myriadrf/LimeRFE/docs/reference/v1.31/gpios.rst

GPIOs
#####

10-pin GPIO interface between SDR and LimeRFE pinouti s given in table 6.

.. list-table:: Table 6. GPIO and I2C connector (J12)
   :header-rows: 1
   :stub-columns: 1

   * - Pin Numbers
     - Designation on Schematic
     - Comments
   * - 1
     - GPIO0
     - Connected to PIN 32 of MCU (INT0 pin)

       Can directly control digital TDD signal (PA/LNA – on/off)
   * - 2
     - GPIO1
     - Via J22 drives RELAY_3

       Connected to PIN 1 of MCU (INT1 pin)
   * - 3
     - GPIO2
     - Drives RELAY_0
   * - 4
     - GPIO3
     - Drives RELAY_1
   * - 5
     - GPIO4
     - Drives RELAY_2
   * - 6
     - GPIO5_CONN
     - Via J22 drives RELAY_3
   * - 7
     - SCL
     - I2C bus
   * - 8
     - SDA
     - I2C bus
   * - 9
     - GND
     - Ground
   * - 10
     - VDD_CON
     - Referent voltage for GPIOx and I2C signals

Level shifted (VDDA) GPIOs and ADC header pinout is given in table 7.

.. list-table:: Table 7. GPIO_LS and ADC connector (J13)
   :header-rows: 1
   :stub-columns: 1

   * - Pin Numbers
     - Designation on Schematic
     - Comments
   * - 1
     - GPIO2_LS
     - Connected to GPI2, level shifted to VDDA
   * - 2
     - GPIO4_LS
     - Connected to GPI4, level shifted to VDDA
   * - 3
     - ADC1
     - Via J6 connected to internal MCU ADC
   * - 4
     - GND
     - Ground
   * - 5
     - VDDA
     - Referent voltage for GPIOx_LS signals
   * - 6
     - ADC2
     - Via J7 connected to internal MCU ADC
   * - 7
     - GPIO5_LS
     - Connected to GPI5, level shifted to VDDA
   * - 8
     - GPIO3_LS
     - Connected to GPI3, level shifted to VDDA

External relays connector (J16) pinout is given in table 8.

.. list-table:: Table 8. External relays connector (J16)
   :header-rows: 1
   :stub-columns: 1

   * - Pin Numbers
     - Designation on Schematic
     - Comments
   * - 1
     - RELAY_3
     - Drives relay 3
   * - 2
     - VCOM
     - Referent voltage, from connector J15
   * - 3
     - RELAY_2
     - Drives relay 2
   * - 4
     - VCOM
     - Referent voltage, from connector J15
   * - 5
     - RELAY_1
     - Drives relay 1
   * - 6
     - VCOM
     - Referent voltage, from connector J15
   * - 7
     - RELAY_0
     - Drives relay 0
   * - 8
     - VCOM
     - Referent voltage, from connector J15
