myriadrf/LimeRFE/docs/reference/v1.31/leds.rst

LEDs
####

The LimeRFE board includes ten indicator LEDs. Their positions on the board are shown in Figures 8 and 9.

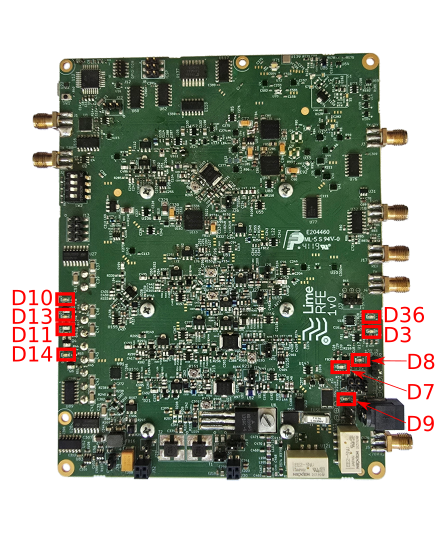
[picture p12: docs/images/LimeRFE_v1.0_components_LEDs_top.png]


  Figure 8. LimeRFE v1.0 indication top LEDs 

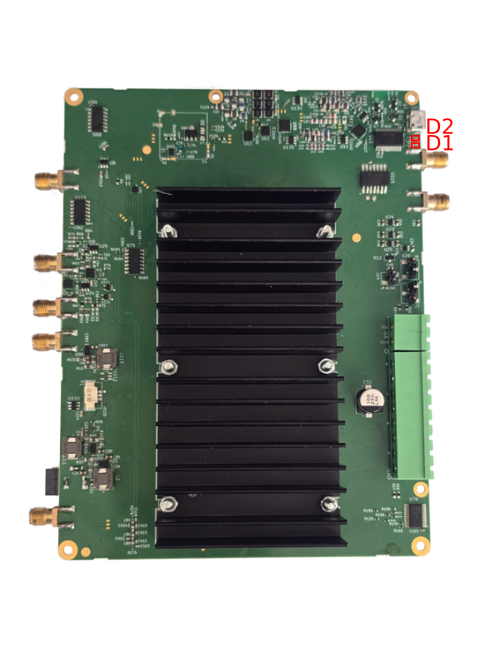
[picture p13: docs/images/LimeRFE_v1.0_components_LEDs_bot.png]


  Figure 9. LimeRFE v1.0 indication bottom LEDs 

LEDs funcions are described in table 5.

.. list-table:: Table 5. Default LEDs configuration
   :header-rows: 1
   :stub-columns: 1
   
   * - Board Reference
     - Description
   * - D1, D2
     - USB to serial communication indicator
   * - D3
     - +3V power indicator
   * - D7
     - +5V_MCU power indicator
   * - D9
     - +7.5V power indicator
   * - D10
     - GPIO2 indicator
   * - D11
     - GPIO4 indicator
   * - D13
     - GPIO3 indicator
   * - D14
     - GPIO5 indicator
   * - D36
     - +2.5V power indicator
