myriadrf/LimeRFE/docs/reference/v1.31/peripheralinterfaces.rst

ICSP Connector
##############

MCU SPI bus connectors pinout is given in table 9.

.. list-table:: Table 9. ICSP connector pinout (J8)
   :stub-columns: 1

   * - Pin Numbers
     - Designation on Schematic
     - Comments
   * - 1
     - MISO
     - ICSP bus
   * - 2
     - +5V_ICSP
     - Referent voltage for ICSP bus
   * - 3
     - SCK
     - ICSP bus
   * - 4
     - MOSI
     - ICSP bus
   * - 5
     - RESET
     - MCU reset
   * - 6
     - GND
     - Ground
