myriadrf/LimeRFE/docs/reference/v1.31/index.rst

v1.31
#####

.. toctree::
   :maxdepth: 3
   :hidden:
   
   overview
   cons
   rxblock
   txblock
   leds
   gpios
   peripheralinterfaces
   power

This is the Reference Manual for LimeRFE v1.31 hardware.



  Figure 1: LimeRFE v1.31 board top view

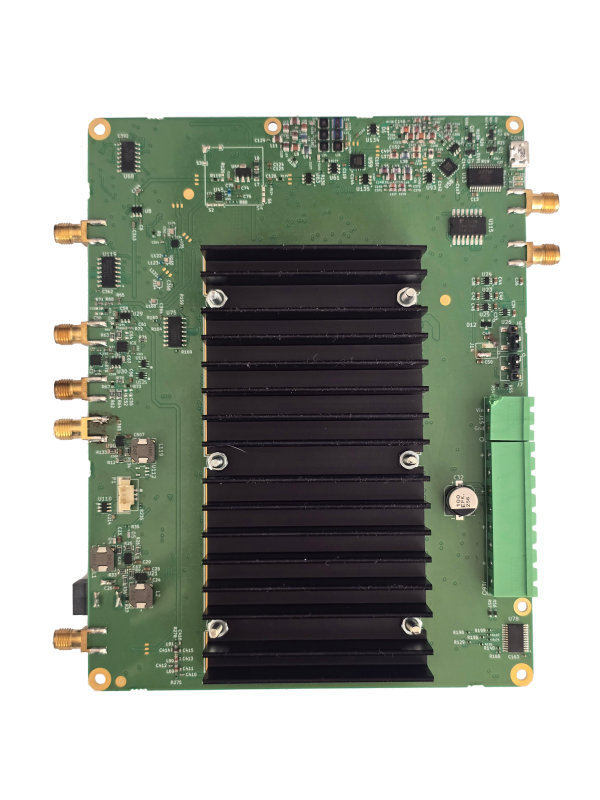
[picture p15: docs/images/LimeRFE_v1.31_3d_bot.png]


  Figure 2: LimeRFE v1.31 board bottom view
