myriadrf/LimeRFE/hardware/1v0/HeatSink_drawing/LimeRFE_1v0_HeatSink.pdf

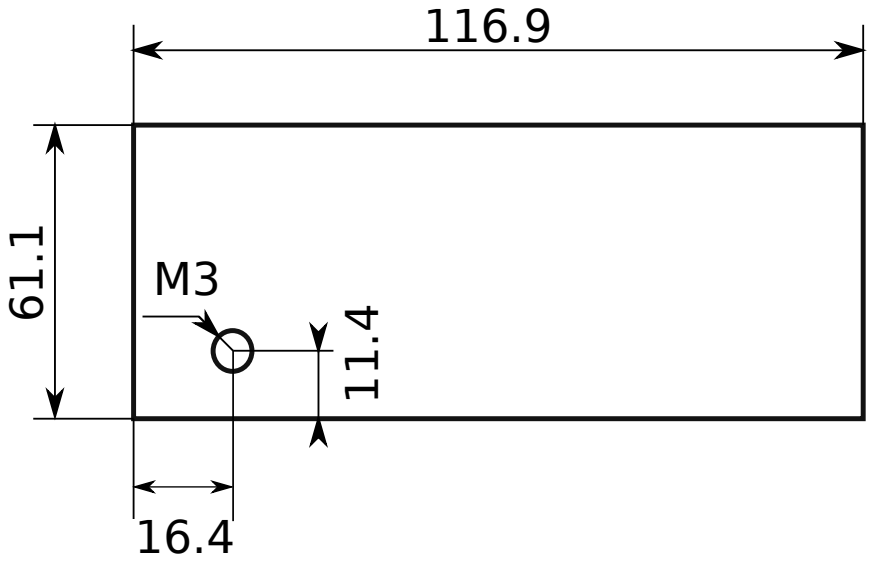
[picture p16: figure]

19.1

3.2

Heat sink
for LimeRFE 1v0
