myriadrf/LimeRFE/hardware/1v31/HeatSink_drawing/LimeRFE_1v31_HeatSink.pdf

19.1

3.2

Heat sink
for LimeRFE 1v31
