myriadrf/LimeRFE/docs/reference/v1.0/overview.rst

Overview
########

The scope of this chapter is in detailed explanation of the block diagram of the LimeRFE board. The above mentioned block diagram is shown in Figure 3. Please keep in mind that this block diagram depicts only RF part of the board. 

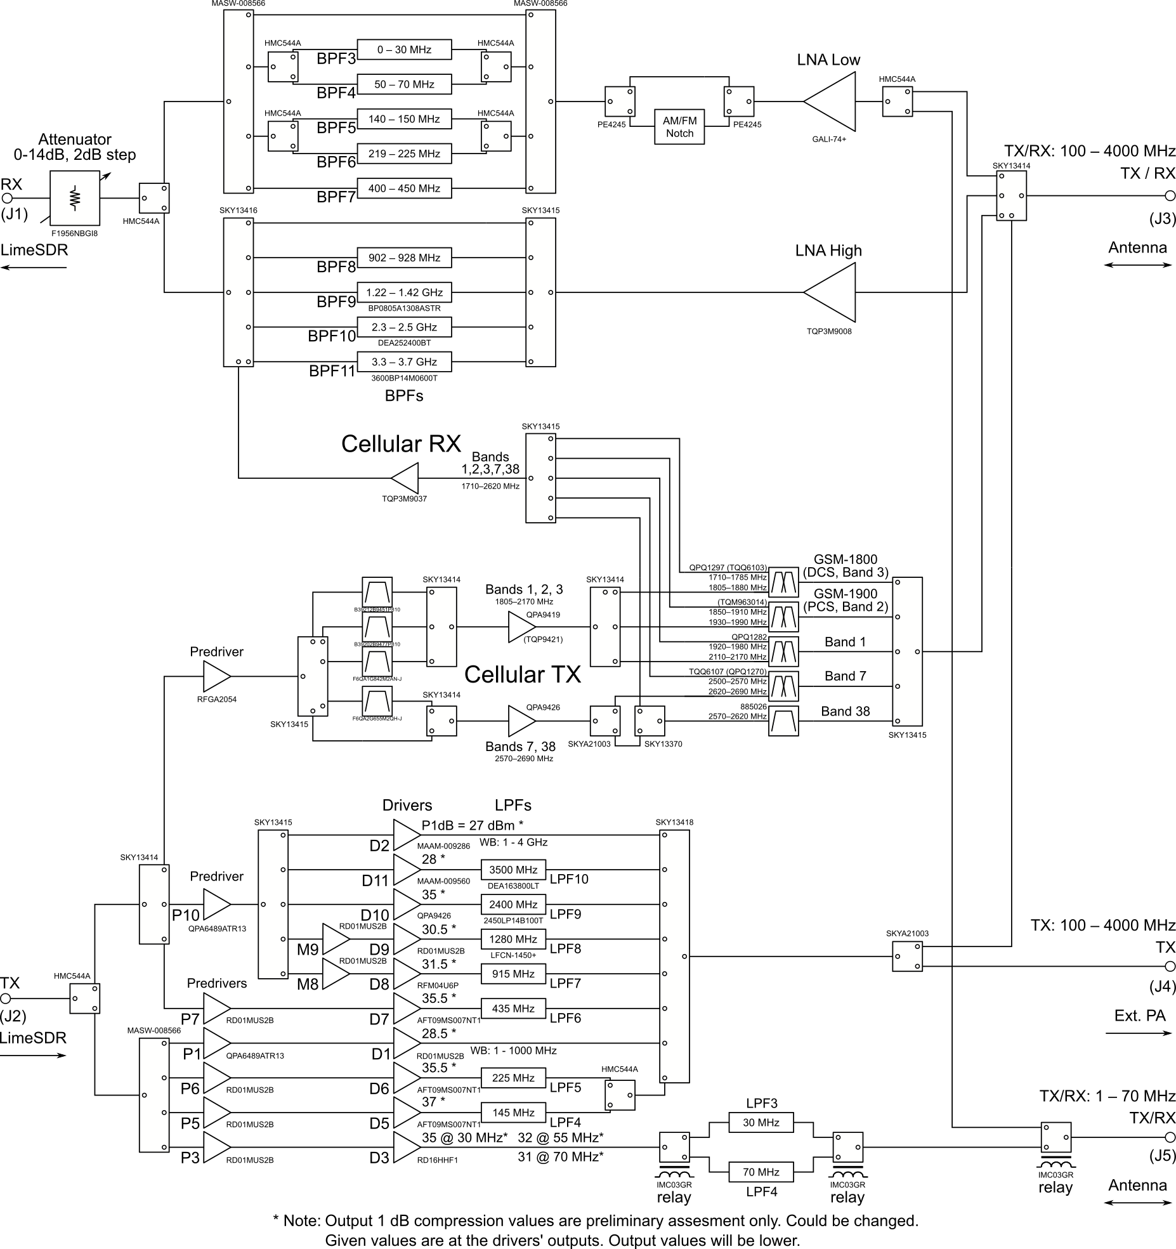
[picture p65: docs/images/LimeRFE_v1.0_diagrams_BD.png]


  Figure 3: LimeRFE v1.0 board block diagram

Basically, the board comprises receiver and transmitter blocks, where both of them have Wideband, HAM and Cellular sub-blocks. These sub-blocks are not strictly divided and separated, for example HAM and Wideband have been realised under the same hardware. Photo of the LimeRFE board, with marked most important RF blocks is shown in Figure 4 and in Figure 5. 

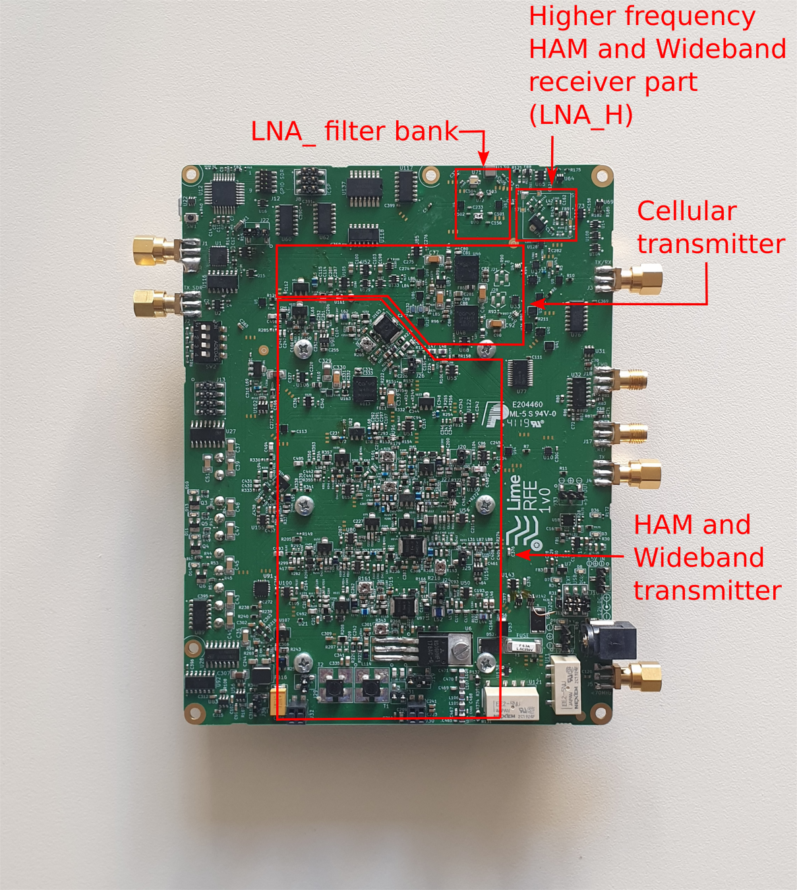
[picture p66: docs/images/LimeRFE_v1.0_Wideband_Cell_HAM_top.png]


  Figure 4: Receiver and transmitter sub-blocks – Top view

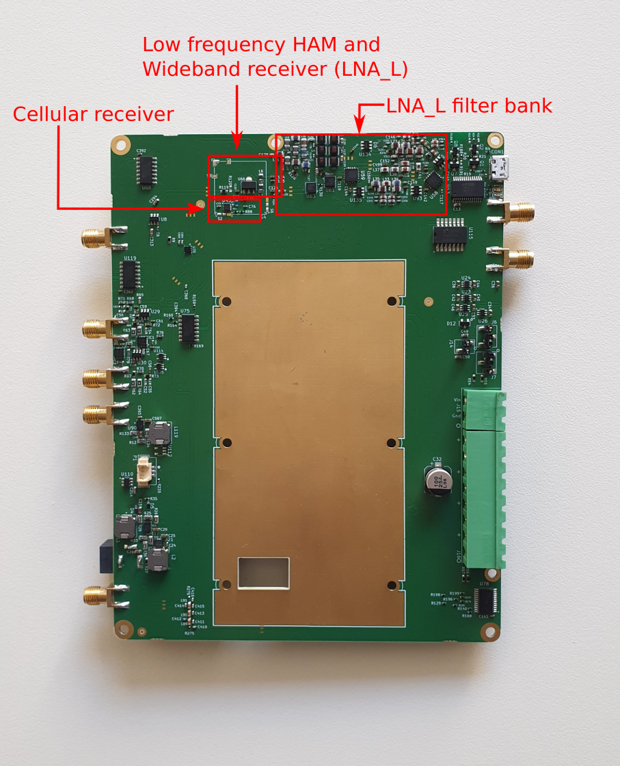
[picture p67: docs/images/LimeFRE_v1.0_Wideband_Cell_HAM_bot.png]


  Figure 5: Receiver and transmitter sub-blocks – Bottom view 
  (without Heat sink and RD16HHF1 transistor)

.. table:: Table 1. Board components

  +-----------------------+-------------------------+-------------------------------------------------------------------------------------------------------------+
  | **Board Reference**   | **Type**                | **Description**                                                                                             |
  +=======================+=========================+=============================================================================================================+
  | **DC Supply Block**                                                                                                                                           |
  +-----------------------+-------------------------+-------------------------------------------------------------------------------------------------------------+
  | J9                    | 3 pin header            | 12V DC input                                                                                                |
  +-----------------------+-------------------------+-------------------------------------------------------------------------------------------------------------+
  | J23                   | Power Barrel            | 12V DC input                                                                                                |
  |                       |                         |                                                                                                             |
  |                       | Connector Jack          |                                                                                                             |
  +-----------------------+-------------------------+-------------------------------------------------------------------------------------------------------------+
  | J10                   | 3 pin header            | 5V DC input                                                                                                 |
  +-----------------------+-------------------------+-------------------------------------------------------------------------------------------------------------+
  | J11                   | 3x2 pin header          | 5V input selector                                                                                           |
  +-----------------------+-------------------------+-------------------------------------------------------------------------------------------------------------+
  | J33                   | 3 pin header            | 5V DC output                                                                                                |
  +-----------------------+-------------------------+-------------------------------------------------------------------------------------------------------------+
  | U17                   | LDO 3V                  | Provides a stable 3V DC                                                                                     |
  +-----------------------+-------------------------+-------------------------------------------------------------------------------------------------------------+
  | U18                   | LDO 2.5V                | Provides a stable 2.5V DC                                                                                   |
  +-----------------------+-------------------------+-------------------------------------------------------------------------------------------------------------+
  | U19                   | DC-DC converter         | Converts 12V to internal 5V                                                                                 |
  +-----------------------+-------------------------+-------------------------------------------------------------------------------------------------------------+
  | U20                   | 5V input protection     | Monitors and protects 5V input                                                                              |
  +-----------------------+-------------------------+-------------------------------------------------------------------------------------------------------------+
  | U21                   | DC-DC converter         | Converts 12V to internal 7.5V                                                                               |
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
  +-----------------------+-------------------------+-------------------------------------------------------------------------------------------------------------+
  | U12                   | MCU                     | ATMEGA 328P microcontroller                                                                                 |
  +-----------------------+-------------------------+-------------------------------------------------------------------------------------------------------------+
  | U13                   | USB-to-serial chip      | Converts USB to MCU serial communication and vice versa                                                     |
  +-----------------------+-------------------------+-------------------------------------------------------------------------------------------------------------+
  | J8                    | ICSP connector          | SPI bus to MCU                                                                                              |
  +-----------------------+-------------------------+-------------------------------------------------------------------------------------------------------------+
  | D1, D2                | LED                     | USB to Serial communication indicator                                                                       |
  +-----------------------+-------------------------+-------------------------------------------------------------------------------------------------------------+
  | CON1                  | USB mini-B connector    | USB connector for the LimeRFE board                                                                         |
  +-----------------------+-------------------------+-------------------------------------------------------------------------------------------------------------+
  | U22                   | USB protection          | Protects USB lines from over-voltages                                                                       |
  +-----------------------+-------------------------+-------------------------------------------------------------------------------------------------------------+
  | U60, U62, U68, U75,   | Shift registers         | Saves the current state of the LimeRFE                                                                      |
  |                       |                         |                                                                                                             |
  | U76, U89, U92, U116,  |                         |                                                                                                             |
  |                       |                         |                                                                                                             |
  | U117, U118, U119      |                         |                                                                                                             |
  +-----------------------+-------------------------+-------------------------------------------------------------------------------------------------------------+
  | J12                   | GPIO and I2C connector  | PINS:                                                                                                       |
  |                       |                         |                                                                                                             |
  |                       |                         | GPIO0, GPIO1, GPIO2, GPIO3_CONN, GPIO4,                                                                     |
  |                       |                         |                                                                                                             |
  |                       |                         | GPIO5, SCL, SDA, GND, VDD_CON                                                                               |
  +-----------------------+-------------------------+-------------------------------------------------------------------------------------------------------------+
  | D12                   | TVS diode               | Protects the board from the DC voltage connected to J12                                                     |
  +-----------------------+-------------------------+-------------------------------------------------------------------------------------------------------------+
  | J13                   | Level Shifted GPIO      | PINS:                                                                                                       |
  |                       |                         |                                                                                                             |
  |                       | and ADC connector       | GPIO0_LS, GPIO2_LS, ADC1, GND,                                                                              |
  |                       |                         |                                                                                                             |
  |                       |                         | VDDA, ADC2, GPIO3_LS, GPIO1_LS                                                                              |
  +-----------------------+-------------------------+-------------------------------------------------------------------------------------------------------------+
  | U23, U24, U25, U26    | Level Shifters          | Converts voltage levels of GPIO signals;                                                                    |
  |                       |                         |                                                                                                             |
  |                       |                         | between VDD_CON (GPIO) and VDDA (GPIO_LS)                                                                   |
  +-----------------------+-------------------------+-------------------------------------------------------------------------------------------------------------+
  | SW2                   | Switch                  | Sets directions of U23-26, for GPIO signals (between GPIO and GPIO_LS)                                      |
  +-----------------------+-------------------------+-------------------------------------------------------------------------------------------------------------+
  | J14                   | 2 pin header            | In a case VDD_CON = VDDA connects these two voltages                                                        |
  +-----------------------+-------------------------+-------------------------------------------------------------------------------------------------------------+
  | J22                   | 3 pin header            | Selects GPIO3 source, either GPIO3_CONN or GPIO5                                                            |
  +-----------------------+-------------------------+-------------------------------------------------------------------------------------------------------------+
  | D10, D11, D13 D14     | LED                     | Indicators for GPIO0, GPIO2, GPIO1, GPIO3 respectively                                                      |
  +-----------------------+-------------------------+-------------------------------------------------------------------------------------------------------------+
  | Q3, Q4, Q5, Q6        | BJT NPN                 | Drivers for D10-13, for GPIO0, GPIO2, GPIO1, GPIO3 respectively                                             |
  +-----------------------+-------------------------+-------------------------------------------------------------------------------------------------------------+
  | U27, U28              | Relay drivers           | Drivers for RELAY_0, RELAY_1, RELAY_2, RELAY_3 signals                                                      |
  +-----------------------+-------------------------+-------------------------------------------------------------------------------------------------------------+
  | J16                   | 8 position header       | Connects LimeRFE to the external relays                                                                     |
  +-----------------------+-------------------------+-------------------------------------------------------------------------------------------------------------+
  | J15                   | 2 position header       | DC voltage for drivers for relays                                                                           |
  +-----------------------+-------------------------+-------------------------------------------------------------------------------------------------------------+
  | U115                  | Inverter                | It is used as 2.5V – 3.0V level shifter for digital signals obtained from U116 and U117,                    |
  |                       |                         |                                                                                                             |
  |                       |                         | from the LimeRFE shift register                                                                             |
  +-----------------------+-------------------------+-------------------------------------------------------------------------------------------------------------+
  | U77, U78              | Level shifter           | Level shifter for digital signals which control TX HAM and WB sub-blocks                                    |
  +-----------------------+-------------------------+-------------------------------------------------------------------------------------------------------------+
  | U127, U129            | Inverter                | Controls digital signals for TDD TX/RX RF switch (U128 )                                                    |
  +-----------------------+-------------------------+-------------------------------------------------------------------------------------------------------------+
  | U141, U142            | Inverter                | Controls digital signals for RF switch for TX HAM145 and HAM220 (U143)                                      |
  +-----------------------+-------------------------+-------------------------------------------------------------------------------------------------------------+
  | U69                   | Logical AND             | Generates control signals for LNA_EN for LNA in higher frequency bands                                      |
  |                       |                         |                                                                                                             |
  |                       |                         | (HAM1280, HAM3500, HAM2400, HAM920 and WB4000)                                                              |
  +-----------------------+-------------------------+-------------------------------------------------------------------------------------------------------------+
  | U137                  | Inverter                | Generates control signals for RF switches in RX lower frequency section. (U38, U134, U93 and U135)          |
  +-----------------------+-------------------------+-------------------------------------------------------------------------------------------------------------+
  | U64                   | Logical AND             | Generates control signals for LNA_EN for LNA for lower frequency bands                                      |
  |                       |                         |                                                                                                             |
  |                       |                         | (HAM30, HAM70, HAM435, HAM220, HAM145, WB1000)                                                              |
  +-----------------------+-------------------------+-------------------------------------------------------------------------------------------------------------+
  | U7                    | Relay driver            | Generates control signal for RF switch U11                                                                  |
  +-----------------------+-------------------------+-------------------------------------------------------------------------------------------------------------+
  | U114, U125            | Inverter                | Generates control signal for RF switches U29 and U30 in SWR section.                                        |
  +-----------------------+-------------------------+-------------------------------------------------------------------------------------------------------------+
  | U32                   | OP amp                  | Operational amplifier in SWR section                                                                        |
  +-----------------------+-------------------------+-------------------------------------------------------------------------------------------------------------+
  | **RF Block**                                                                                                                                                  |
  +-----------------------+-------------------------+-------------------------------------------------------------------------------------------------------------+
  | J1                    | SMA                     | RX connector                                                                                                |
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
  +-----------------------+-------------------------+-------------------------------------------------------------------------------------------------------------+
  | H1                    | Heat sink               | Aluminum black anodized heat sink                                                                           |
  +-----------------------+-------------------------+-------------------------------------------------------------------------------------------------------------+
  | P1                    | 3 pin FAN connector     | Connects an external fan                                                                                    |
  +-----------------------+-------------------------+-------------------------------------------------------------------------------------------------------------+

A more detailed description is provided in the following sections.
