myriadrf/LimeRFE/docs/reference/v1.0/index.rst

v1.0
####

.. toctree::
   :maxdepth: 3
   :hidden:
   
   overview
   cons
   rxblock
   txblock
   leds
   gpios
   peripheralinterfaces
   power

This is the Reference Manual for LimeRFE v1.0 hardware.



  Figure 1: LimeRFE v1.0 board top view

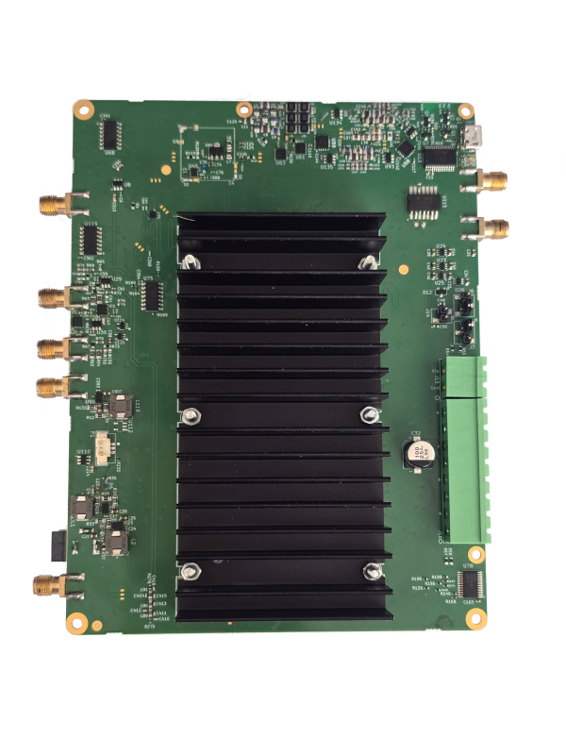
[picture p71: docs/images/LimeRFE_v1.0_3d_bot.png]


  Figure 2: LimeRFE v1.0 board bottom view
