myriadrf/LimeRFE/archived/0v3/hardware/PDF/LimeRFE_v03_Block_Diagram.pdf

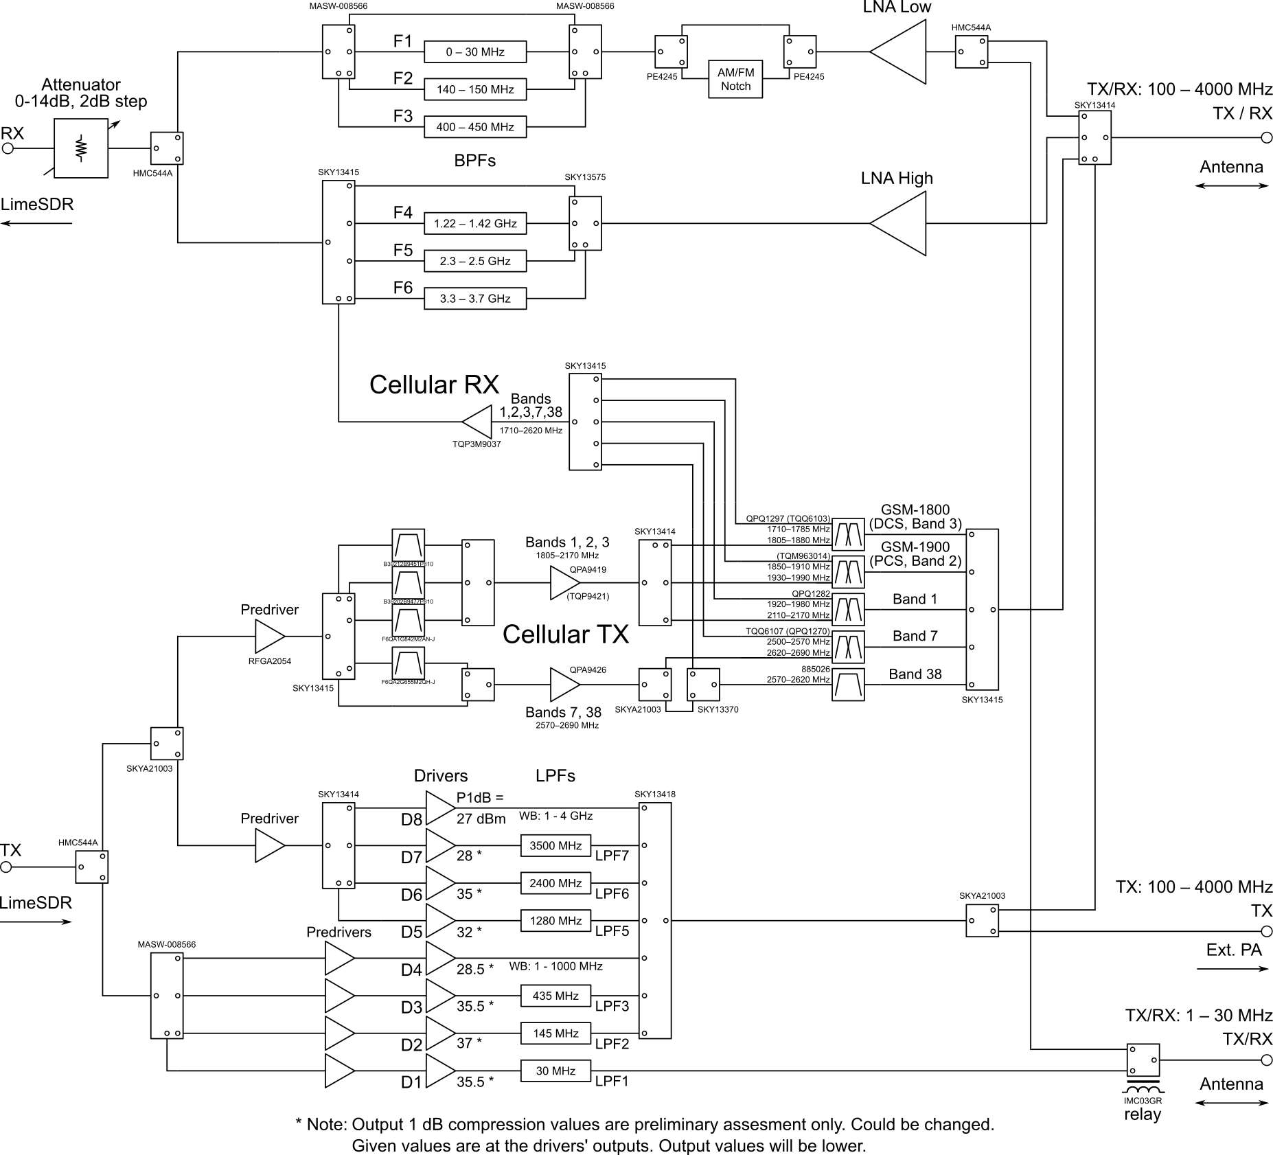
[picture p72: page 1]
