myriadrf/LimeRFE/archived/1v0/hardware/PDF/LimeRFE_1v0_Block_Diagram.pdf

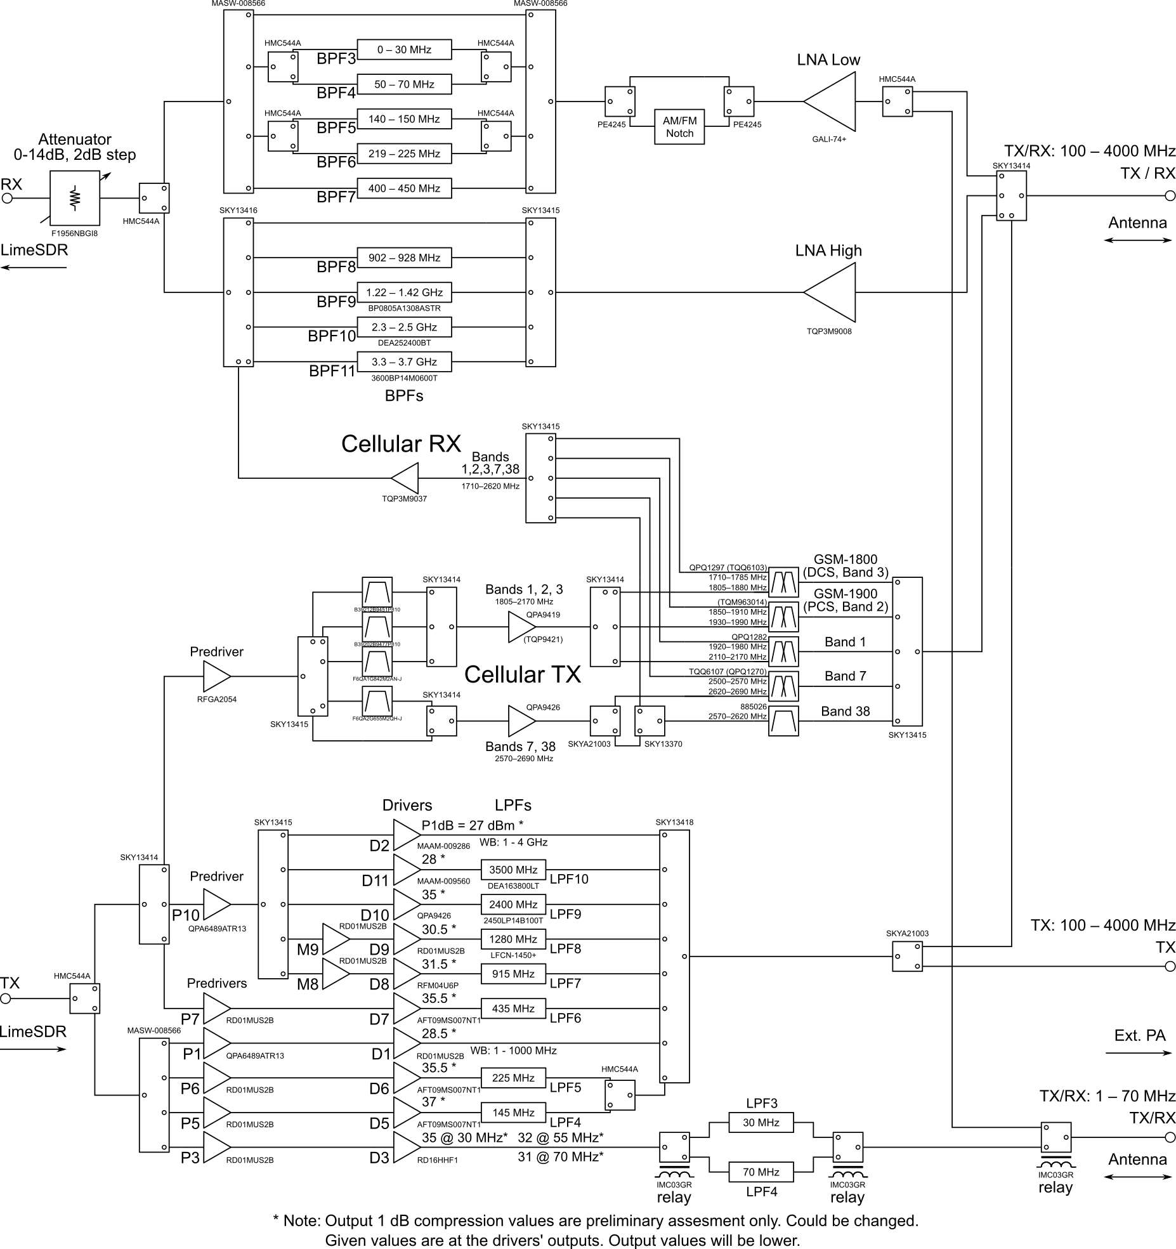
[picture p73: page 1]
