myriadrf/LimeRFE/docs/images/LimeRFE_v1.0_3D.jpg

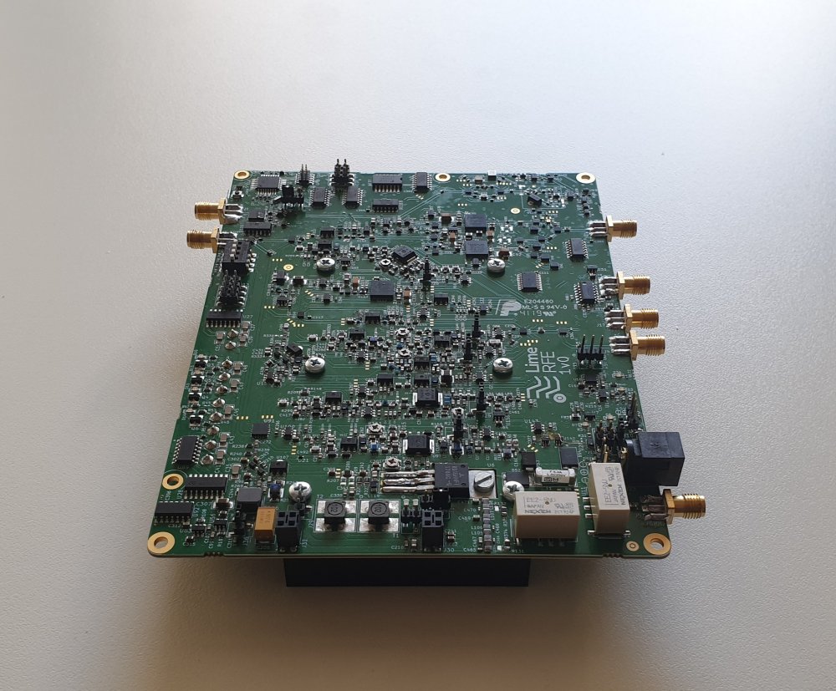
docs/images/LimeRFE_v1.0_3D.jpg
