myriadrf/LimeRFE/hardware/1v0/PDF/Layout/Lime_RFE-B.Mask.pdf

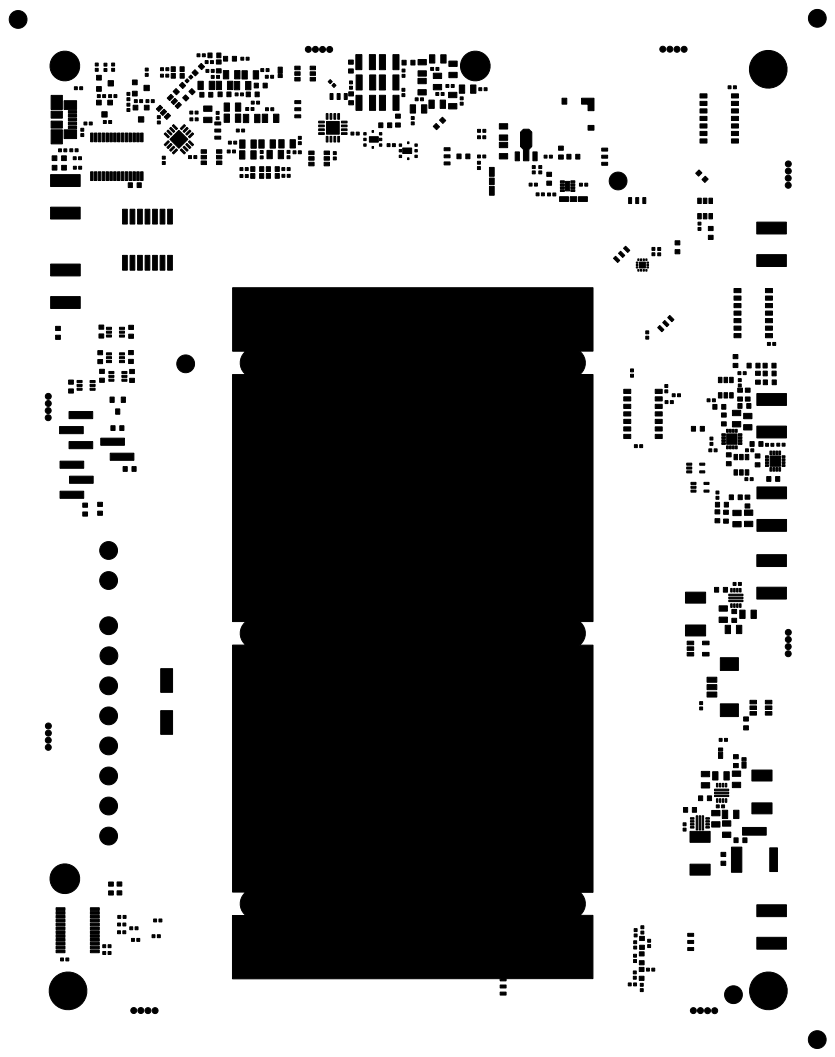
[picture p354: page 1]
