myriadrf/LimeRFE/hardware/1v0/PDF/Layout/Lime_RFE-B.Paste.pdf

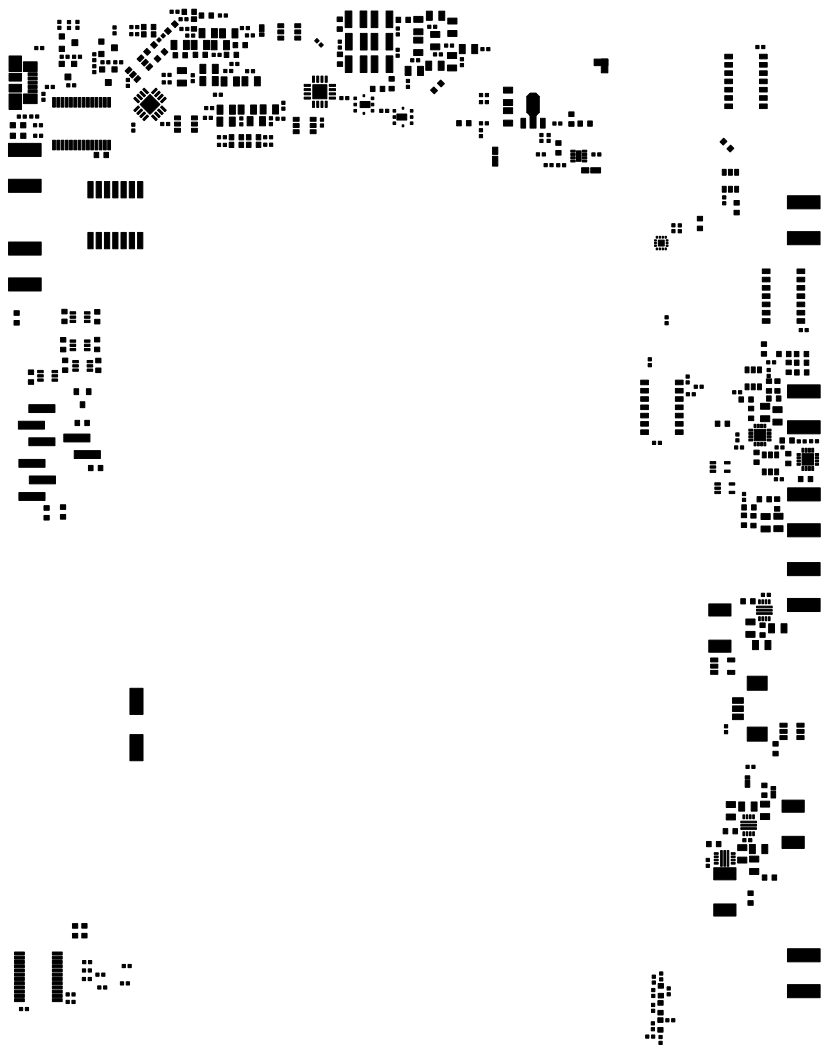
[picture p355: page 1]
