myriadrf/LimeRFE/hardware/1v0/PDF/Layout/Lime_RFE-B.pdf

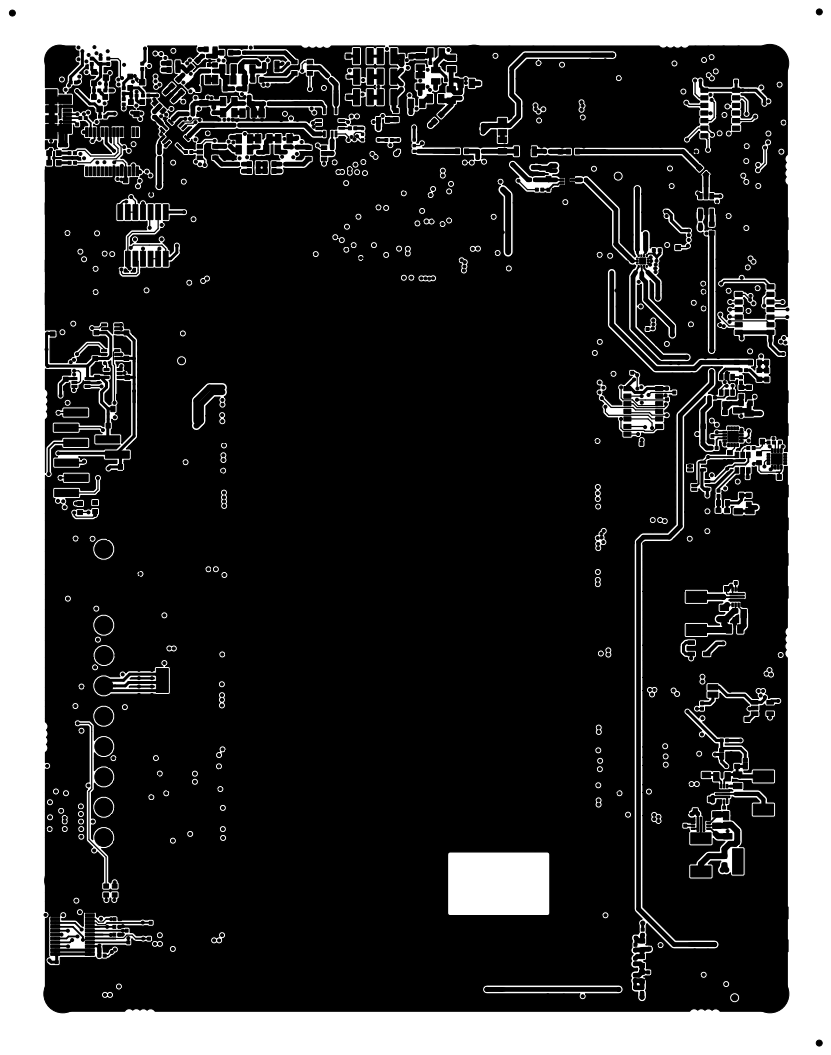
[picture p356: page 1]
