myriadrf/LimeRFE/hardware/1v0/PDF/Layout/Lime_RFE-B.SilkS.pdf

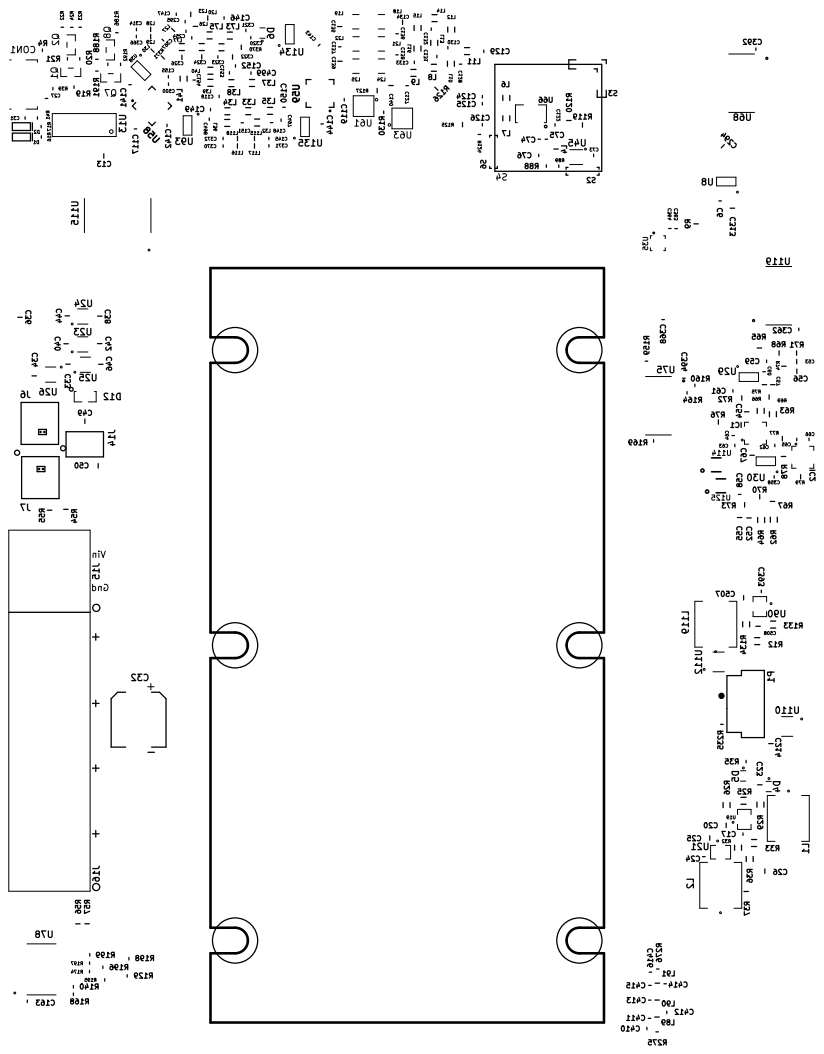
[picture p357: page 1]
