myriadrf/LimeRFE/hardware/1v0/PDF/Layout/Lime_RFE-Edge.Cuts.pdf

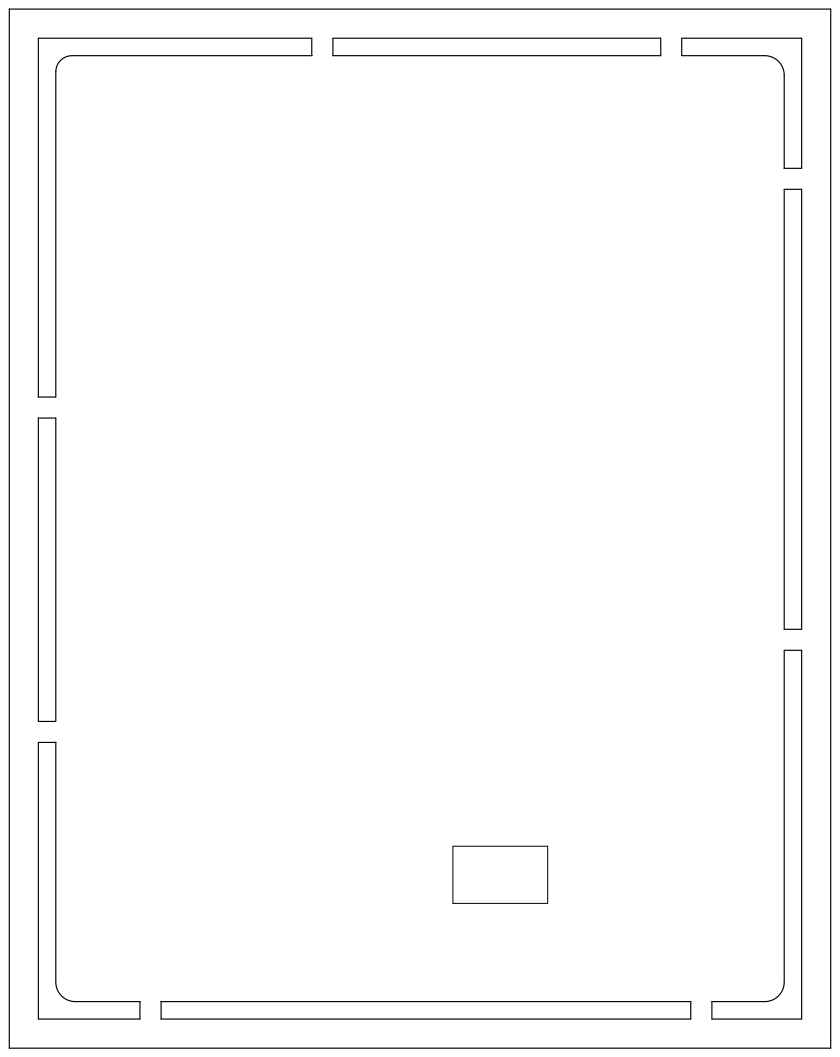
[picture p358: page 1]
