myriadrf/LimeRFE/hardware/1v0/PDF/Layout/Lime_RFE-F.Fab.pdf

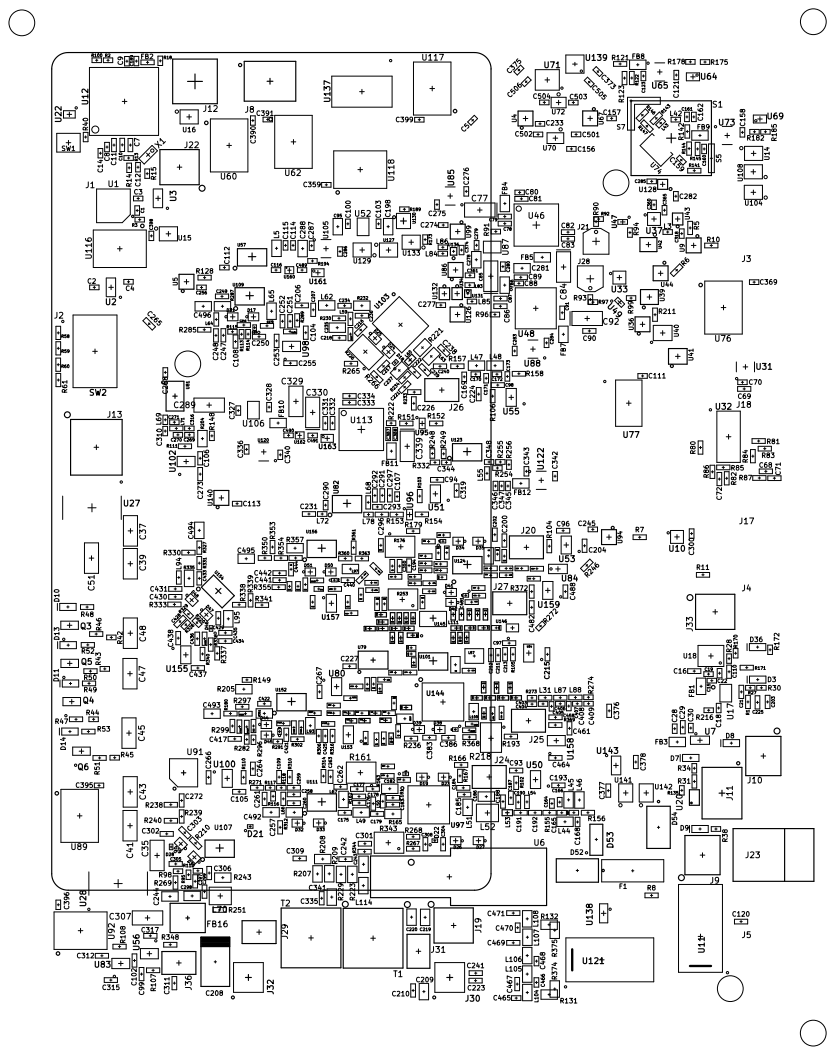
[picture p359: page 1]
