myriadrf/LimeRFE/hardware/1v0/PDF/Layout/Lime_RFE-F.Mask.pdf

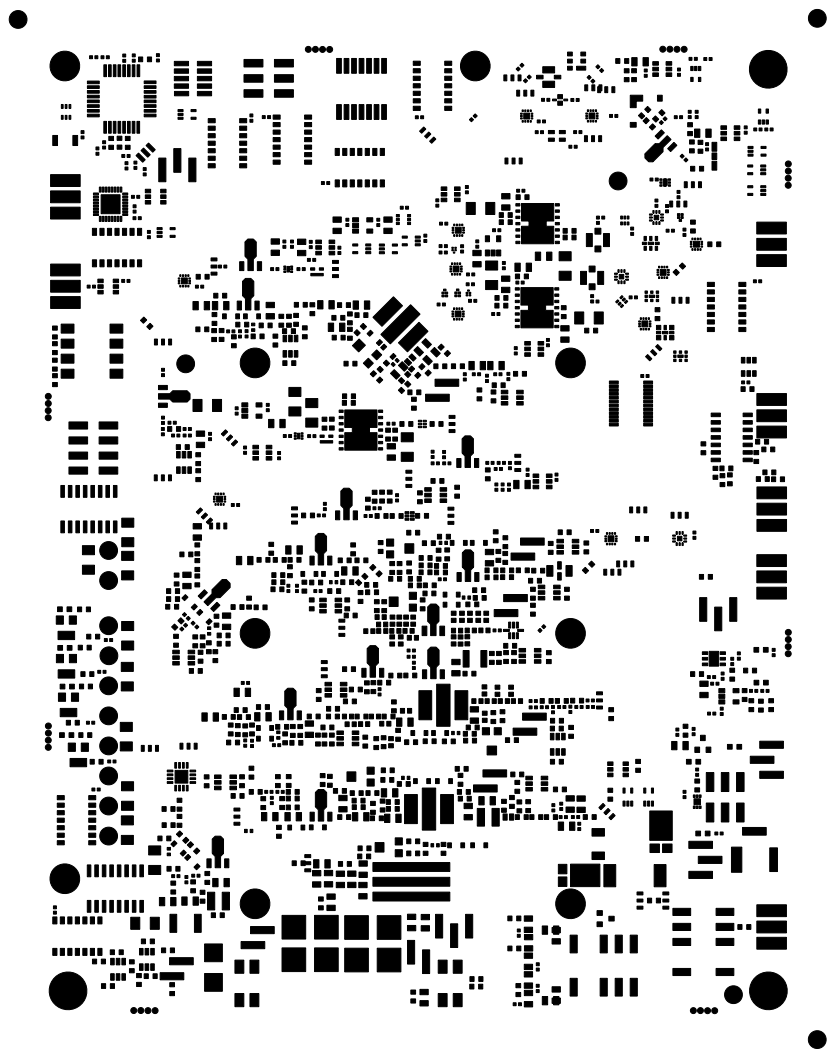
[picture p360: page 1]
