myriadrf/LimeRFE/hardware/1v0/PDF/Layout/Lime_RFE-F.Paste.pdf

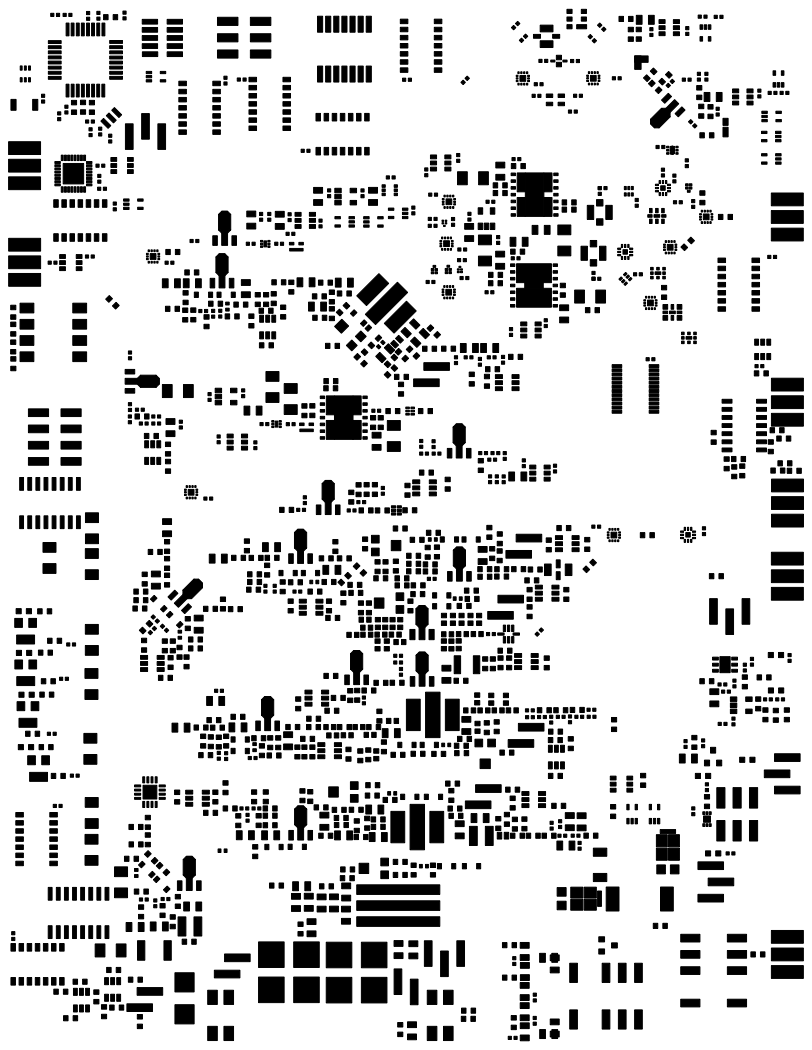
[picture p361: page 1]
