myriadrf/LimeRFE/hardware/1v0/PDF/Layout/Lime_RFE-F.SilkS.pdf

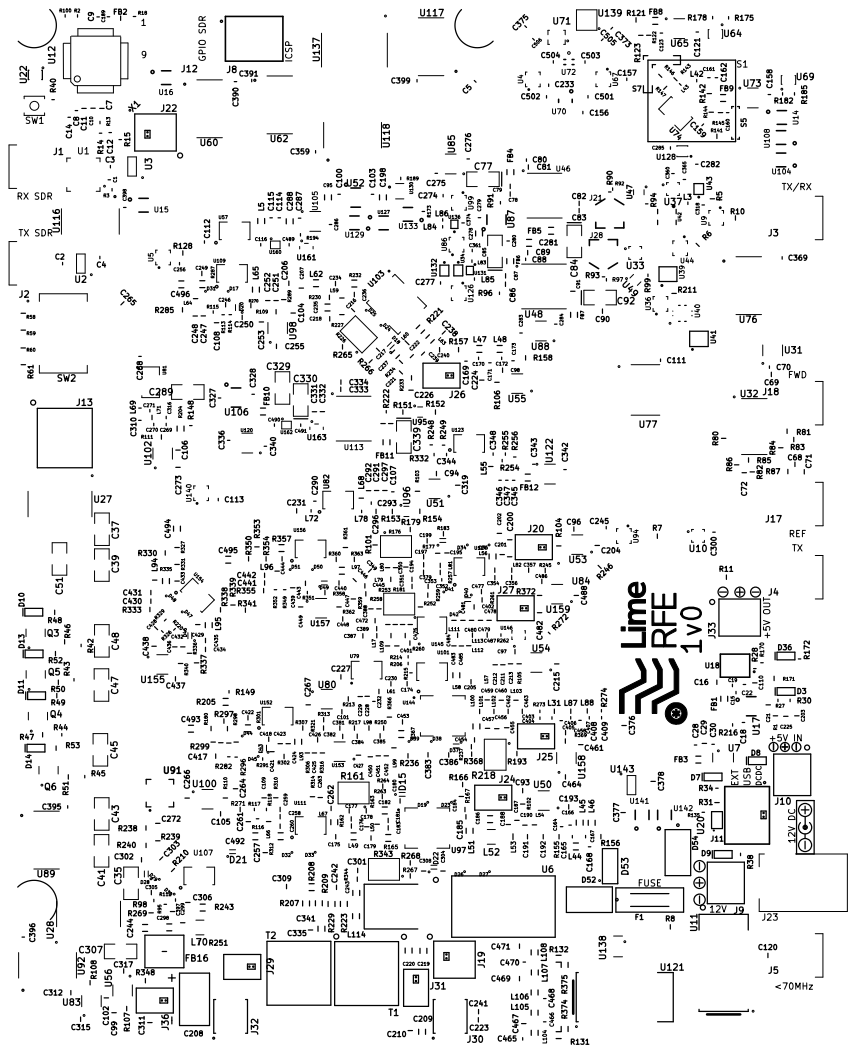
[picture p362: page 1]
