myriadrf/LimeRFE/hardware/1v0/PDF/Layout/Lime_RFE-GND.pdf

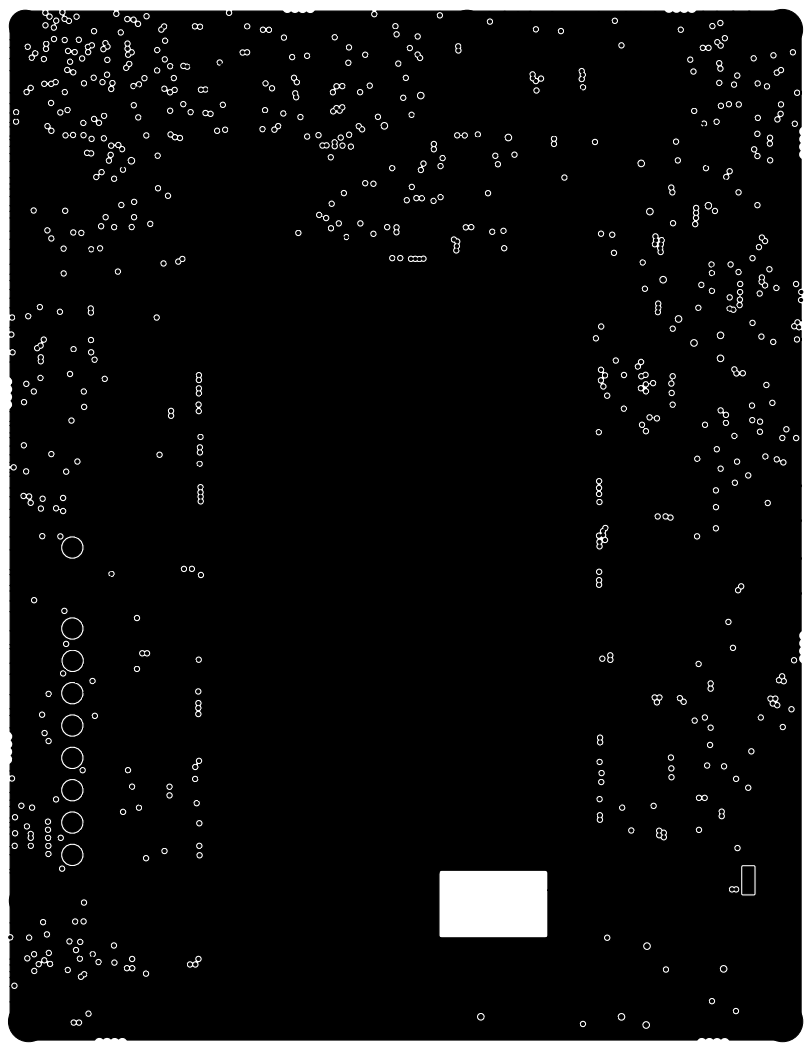
[picture p363: page 1]
