myriadrf/LimeRFE/hardware/1v0/PDF/Layout/Lime_RFE-PWR.pdf

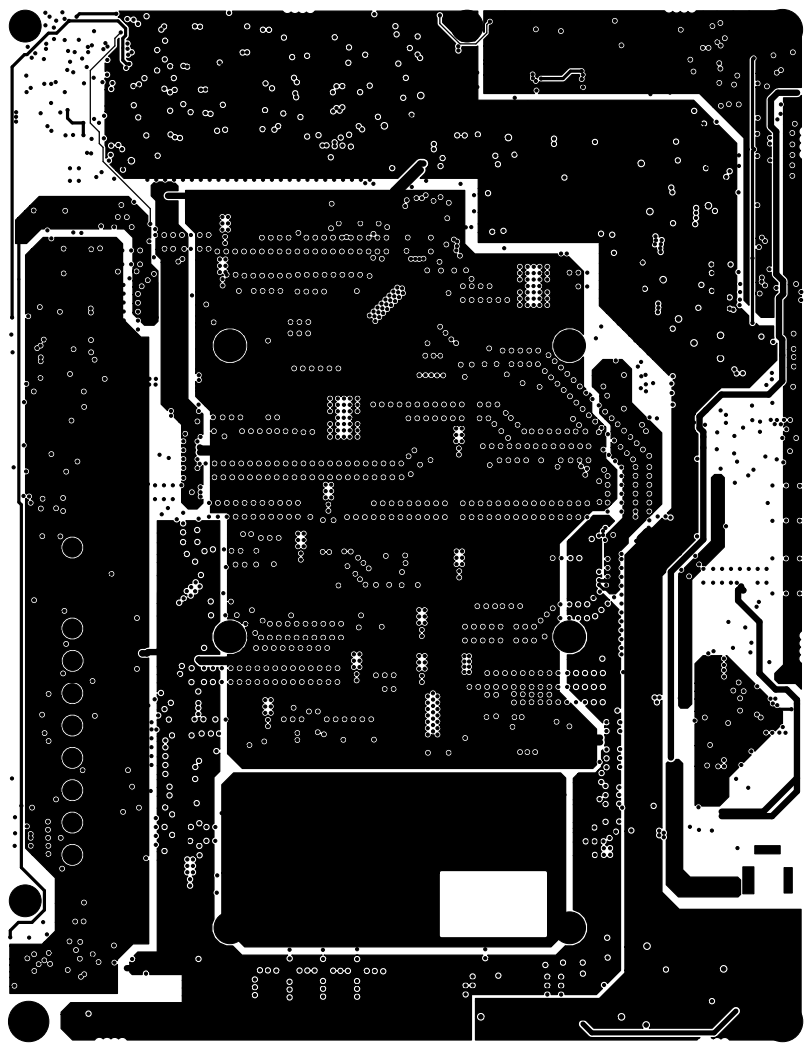
[picture p364: page 1]
