myriadrf/LimeRFE/hardware/1v0/PDF/Layout/Lime_RFE-SIG1.pdf

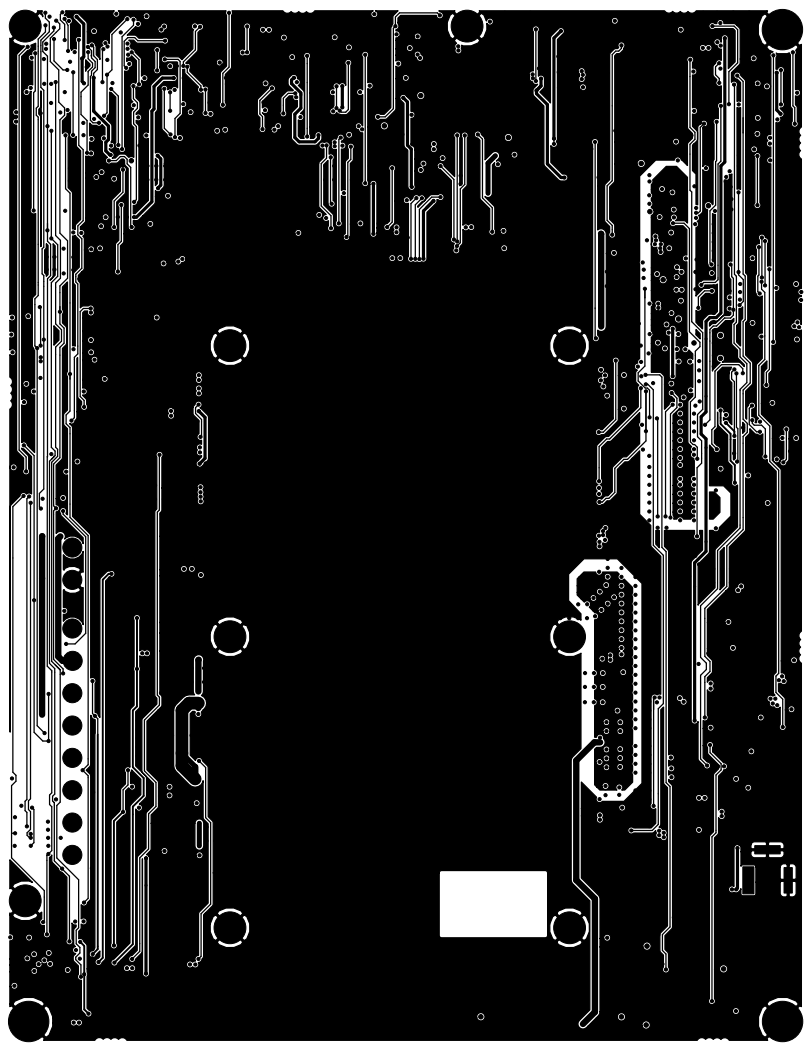
[picture p365: page 1]
