myriadrf/LimeRFE/hardware/1v0/PDF/Layout/Lime_RFE-SIG2.pdf

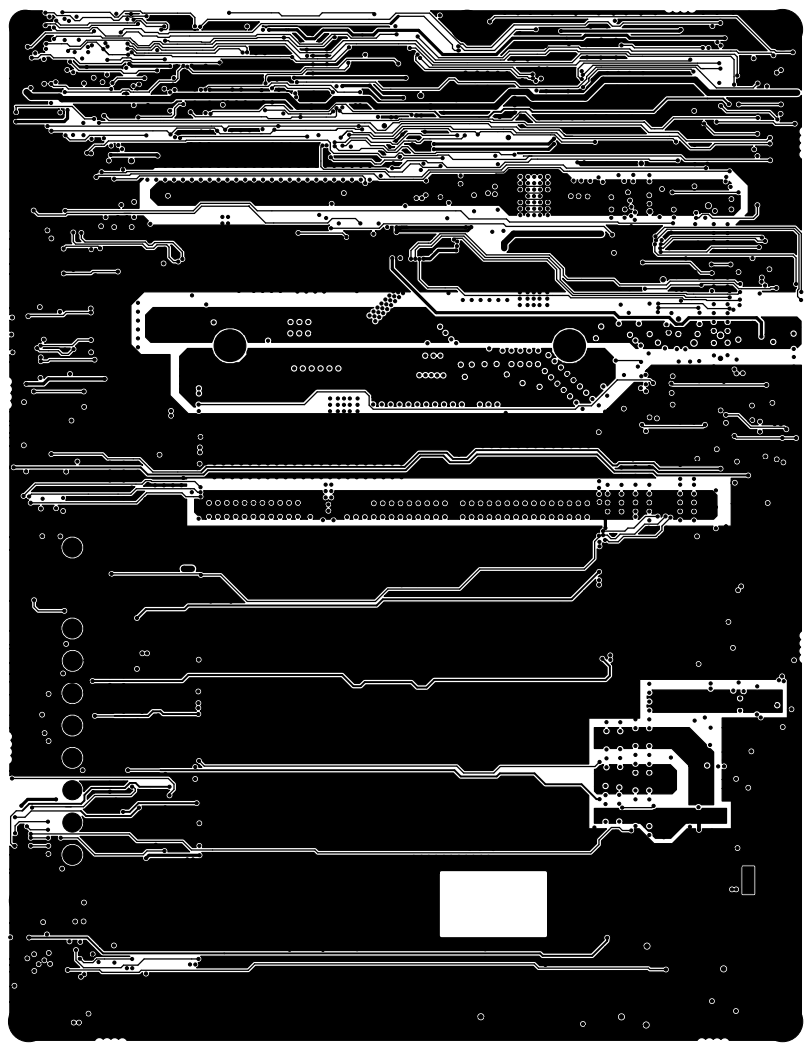
[picture p366: page 1]
