myriadrf/LimeRFE/hardware/1v0/PDF/Layout/Lime_RFE-T.pdf

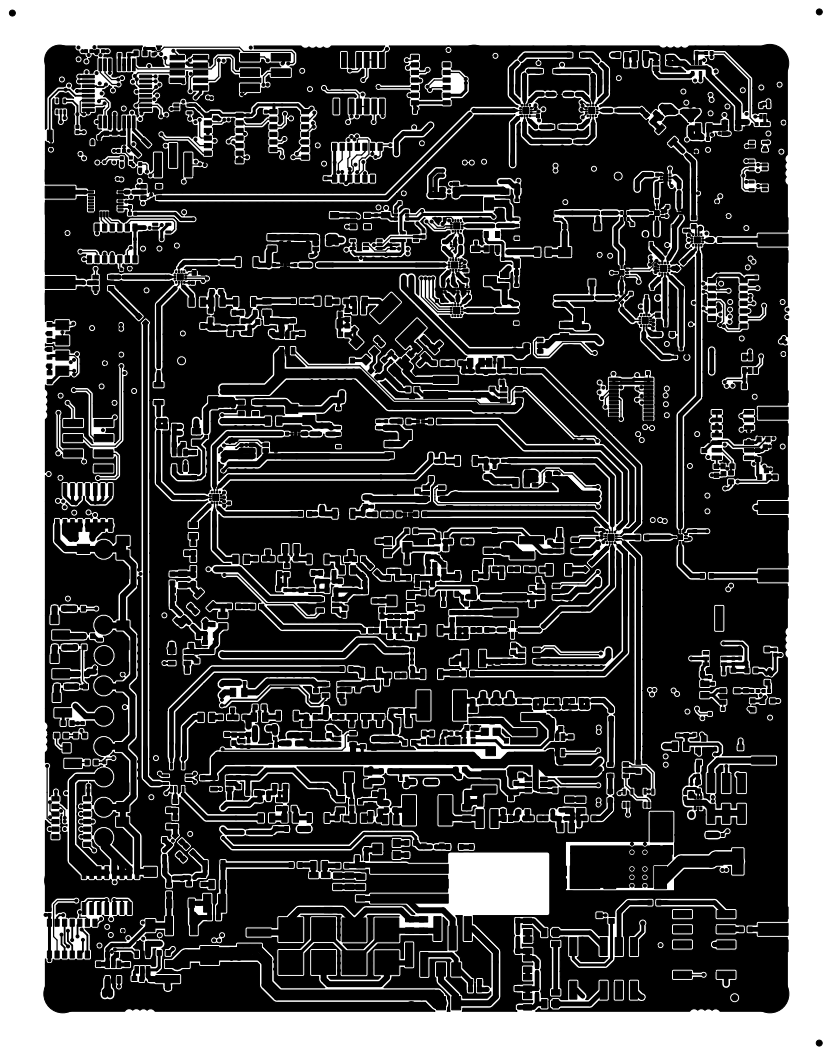
[picture p367: page 1]
