myriadrf/LimeRFE/archived/0v3/docs/LimeRFE_0v3_Schematic.pdf

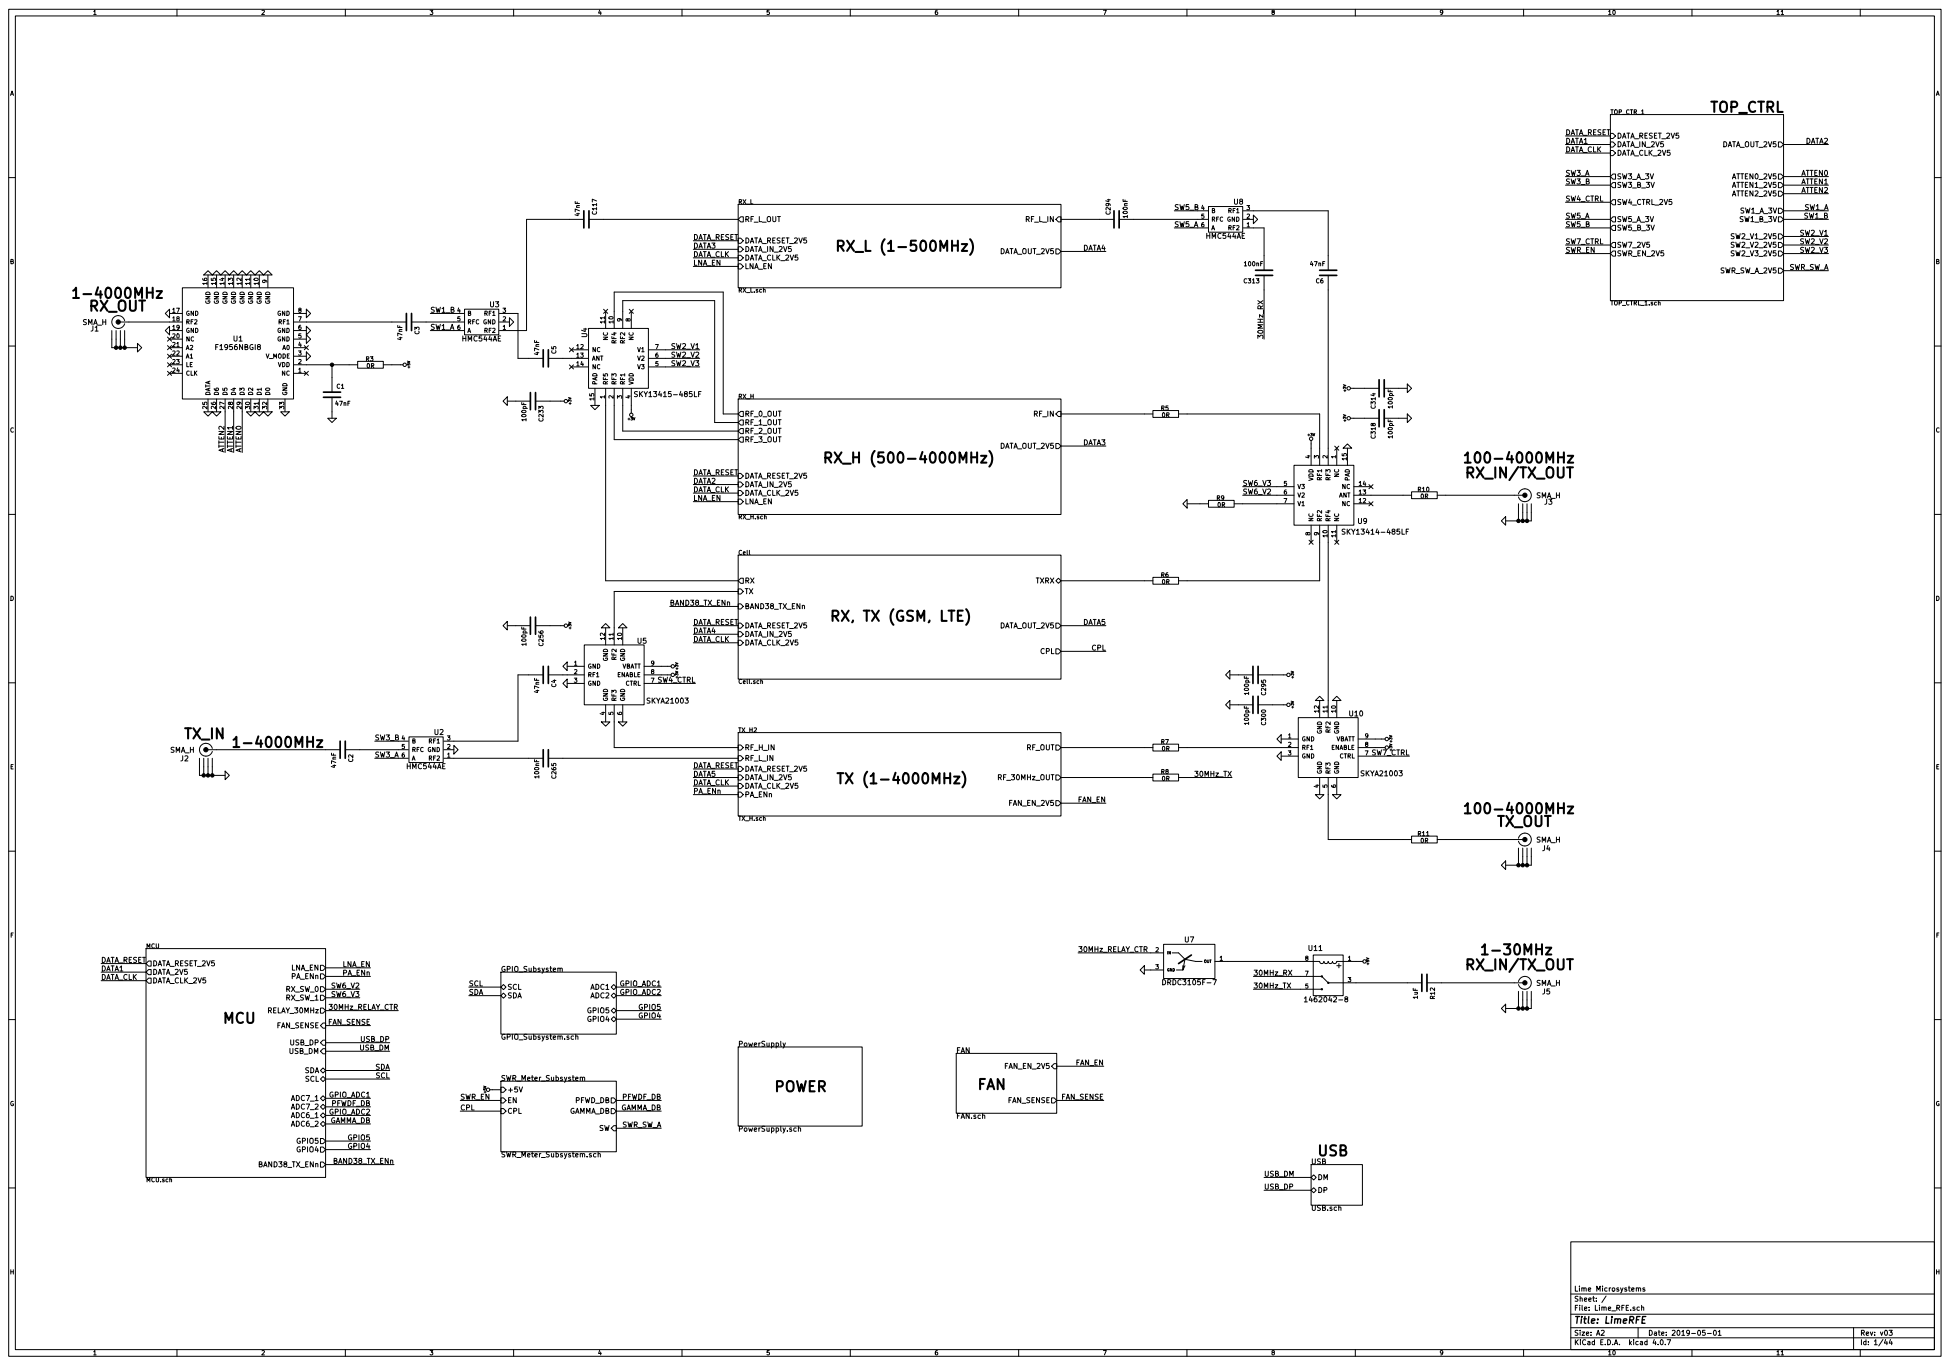
[picture p368: page 1]

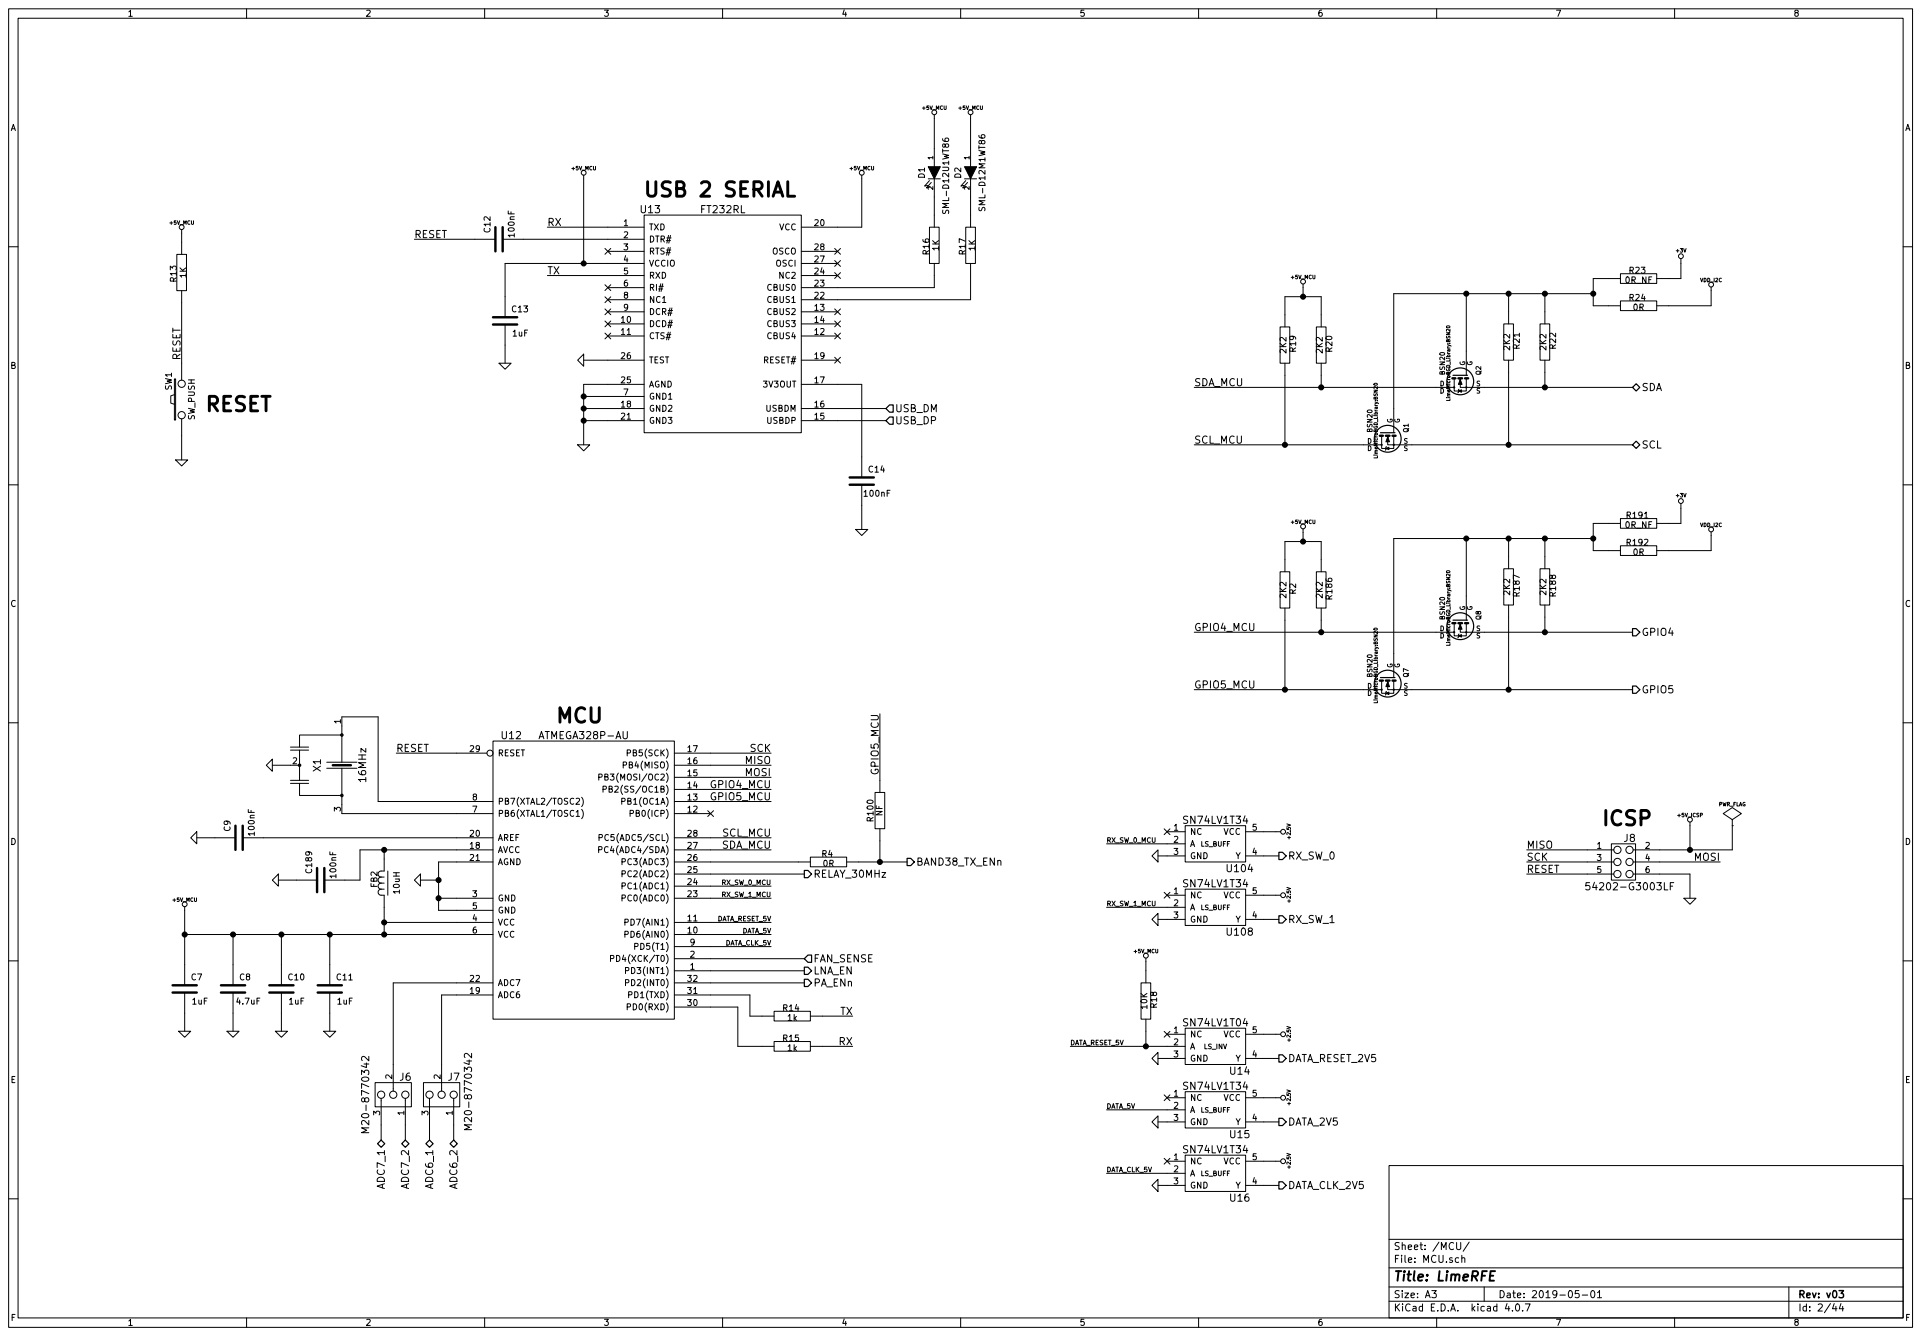
[picture p369: page 2]

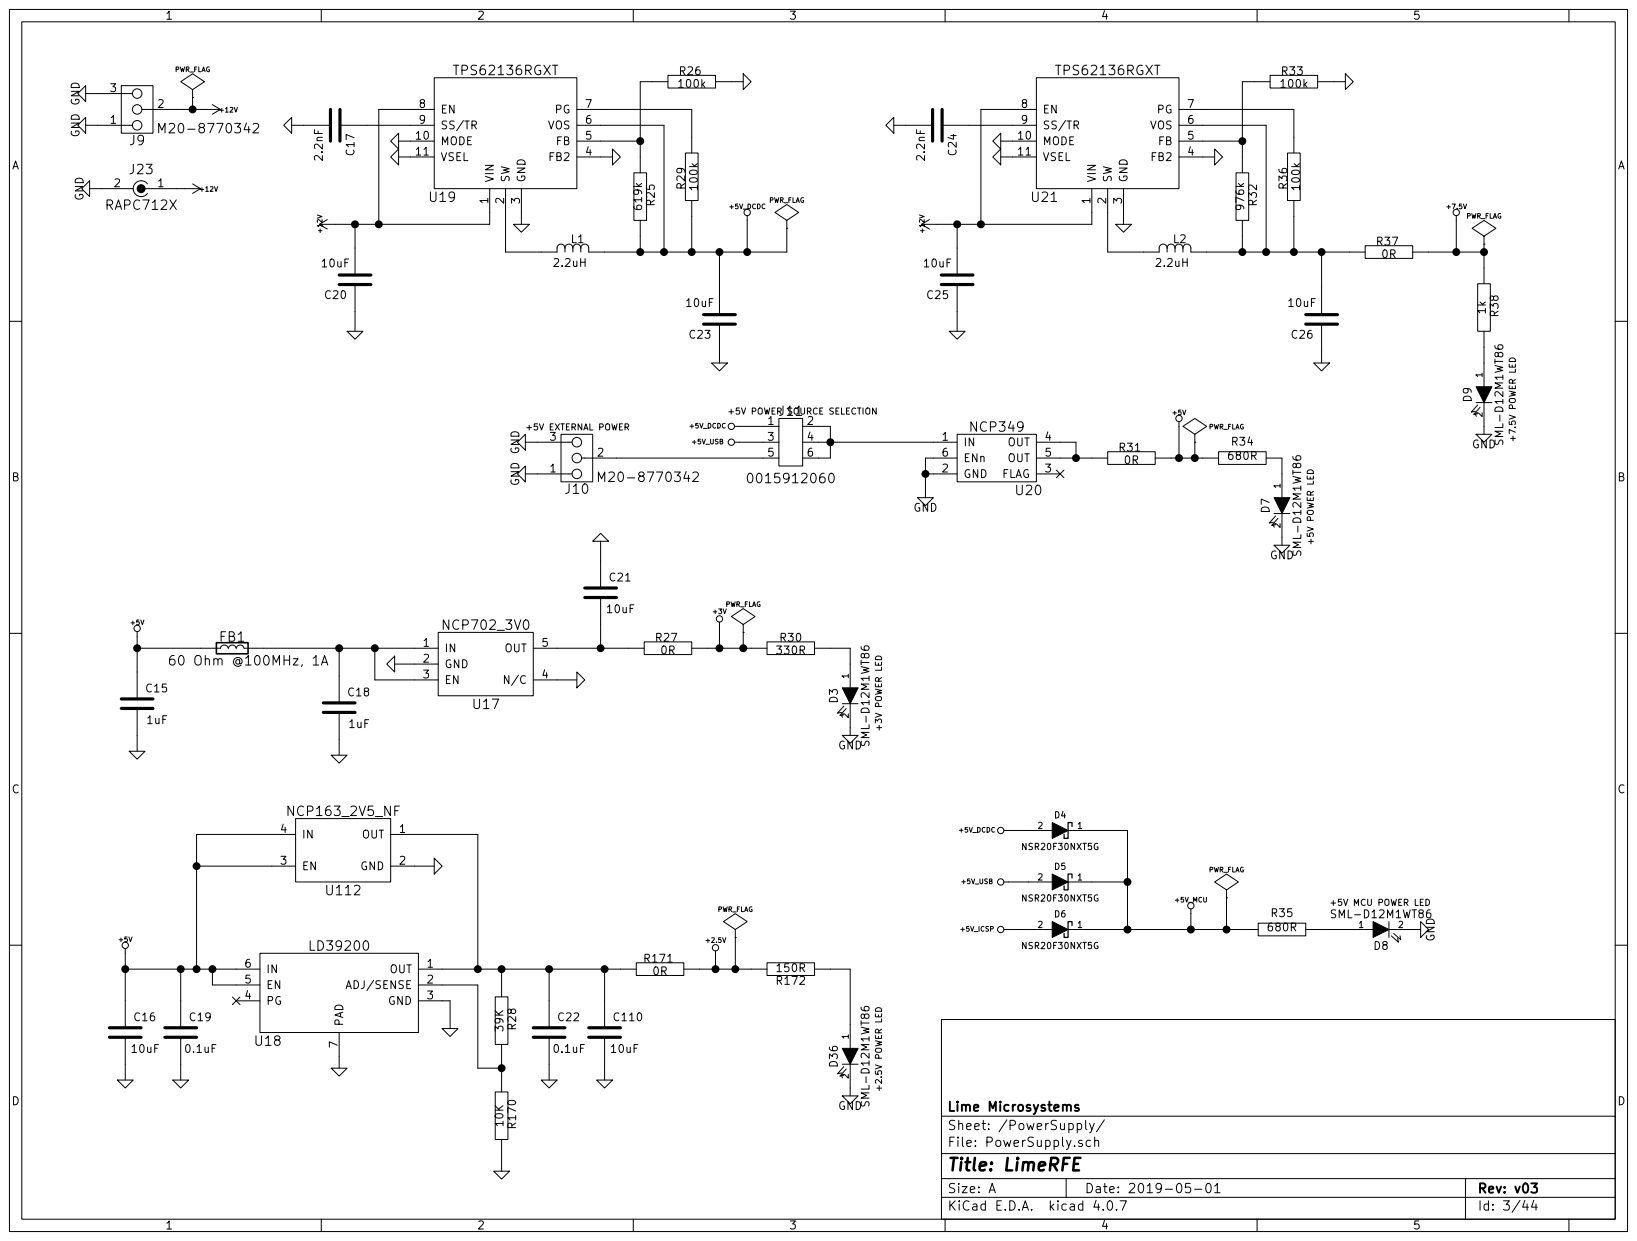
[picture p370: page 3]

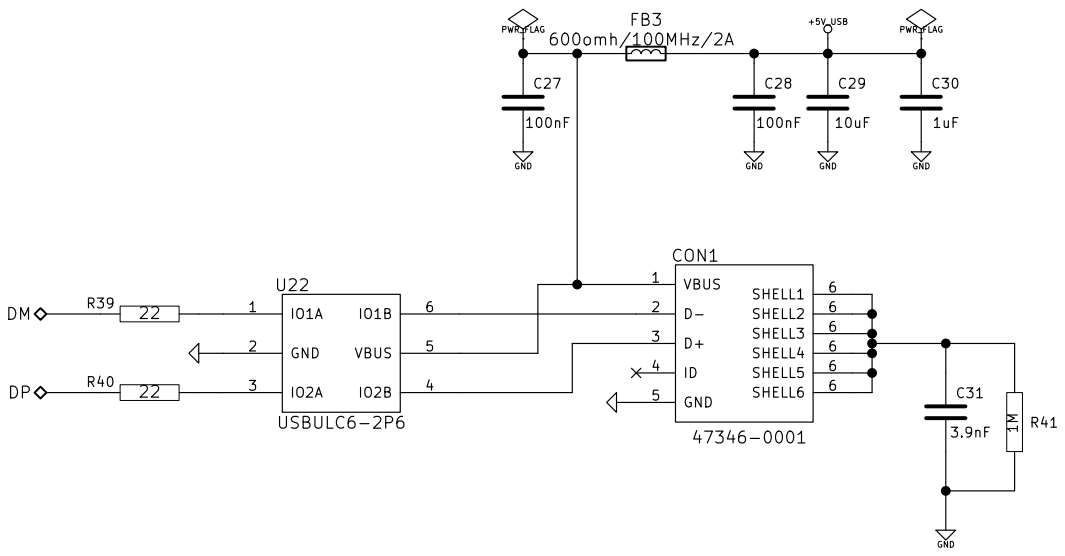
[picture p371: page 4]

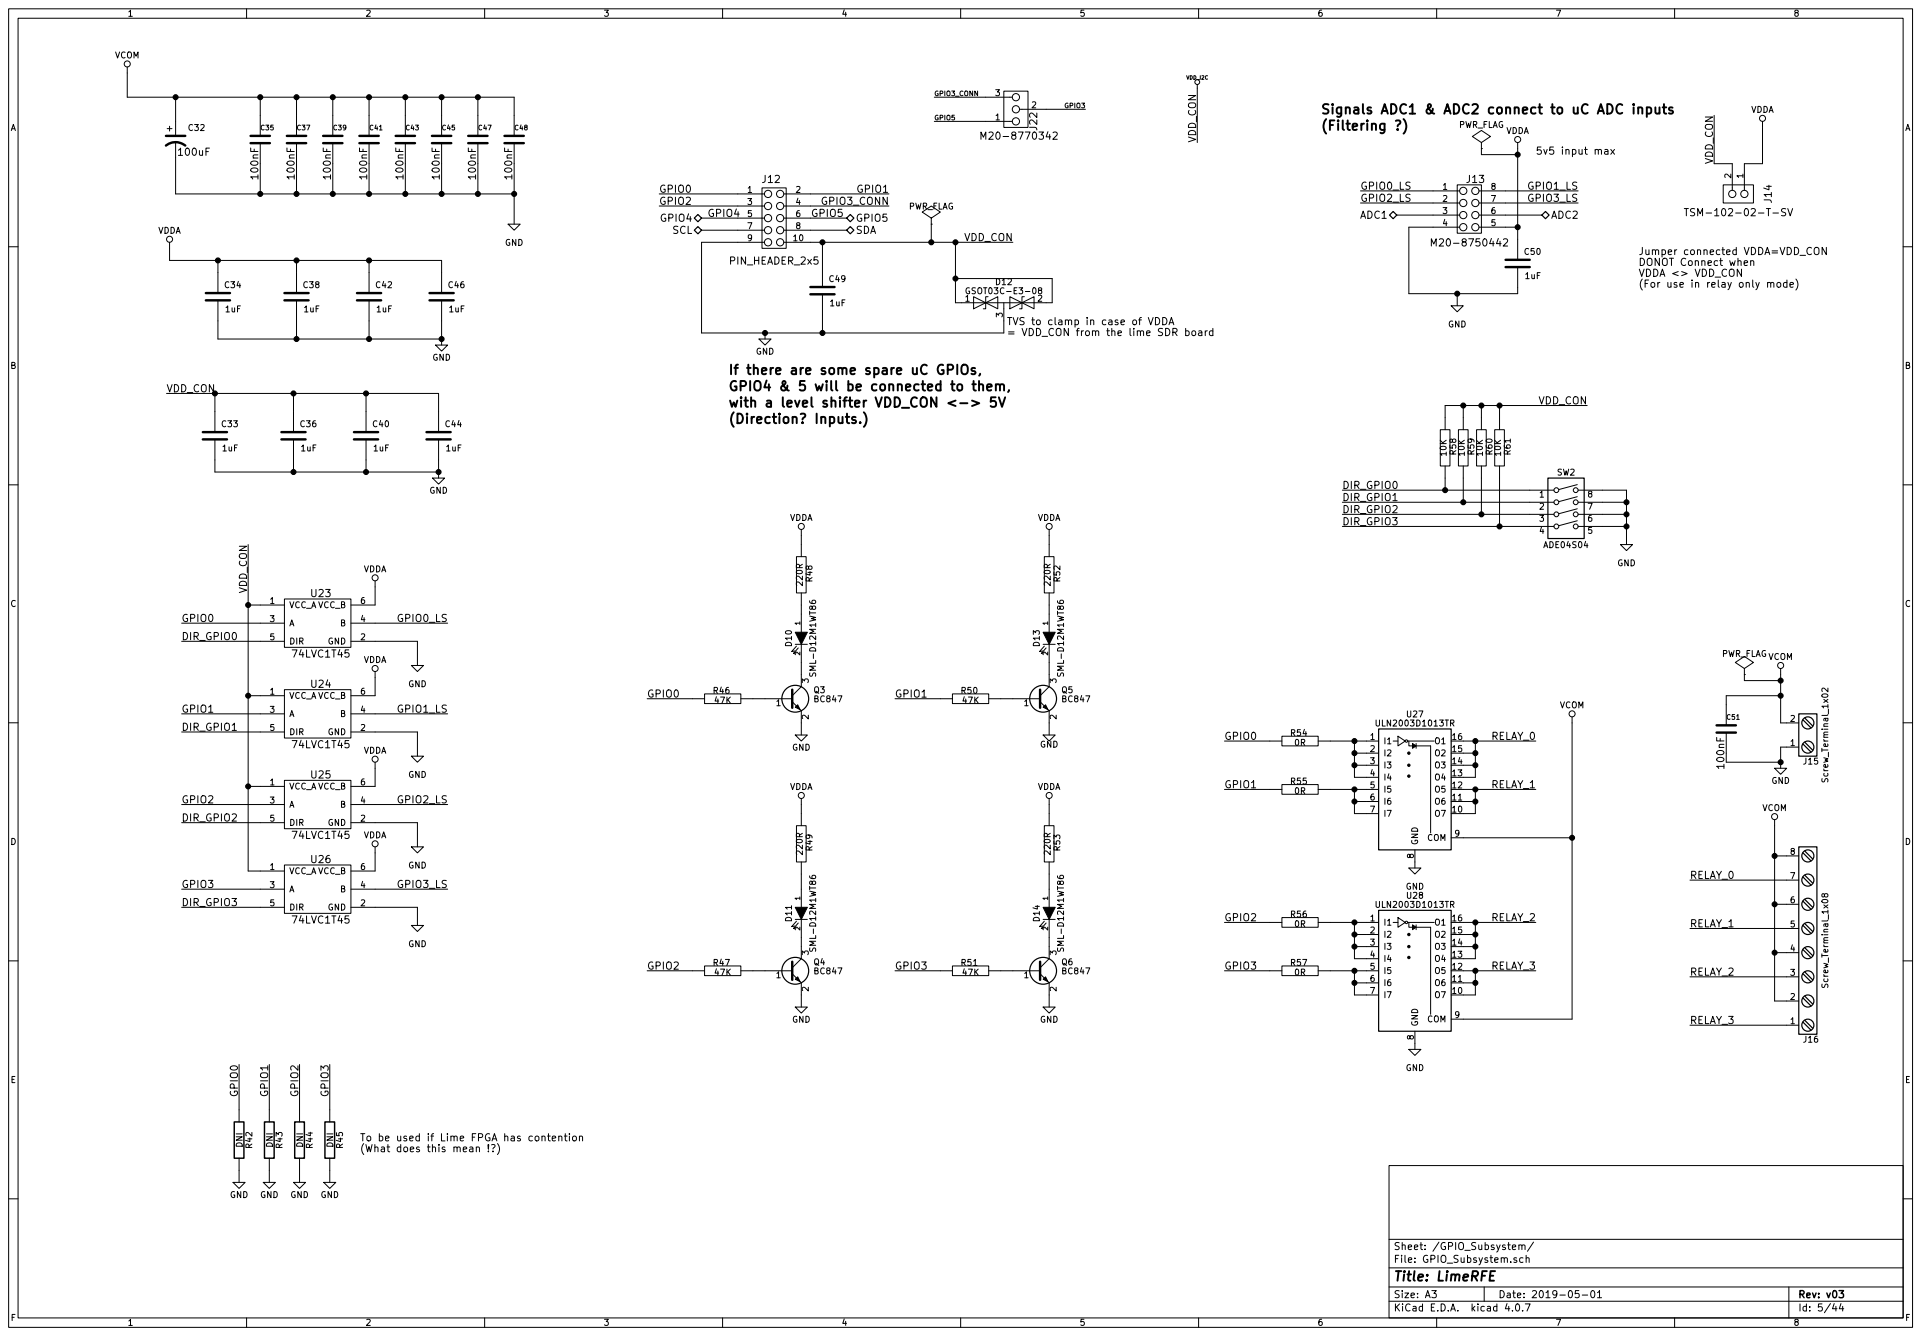
[picture p372: page 5]

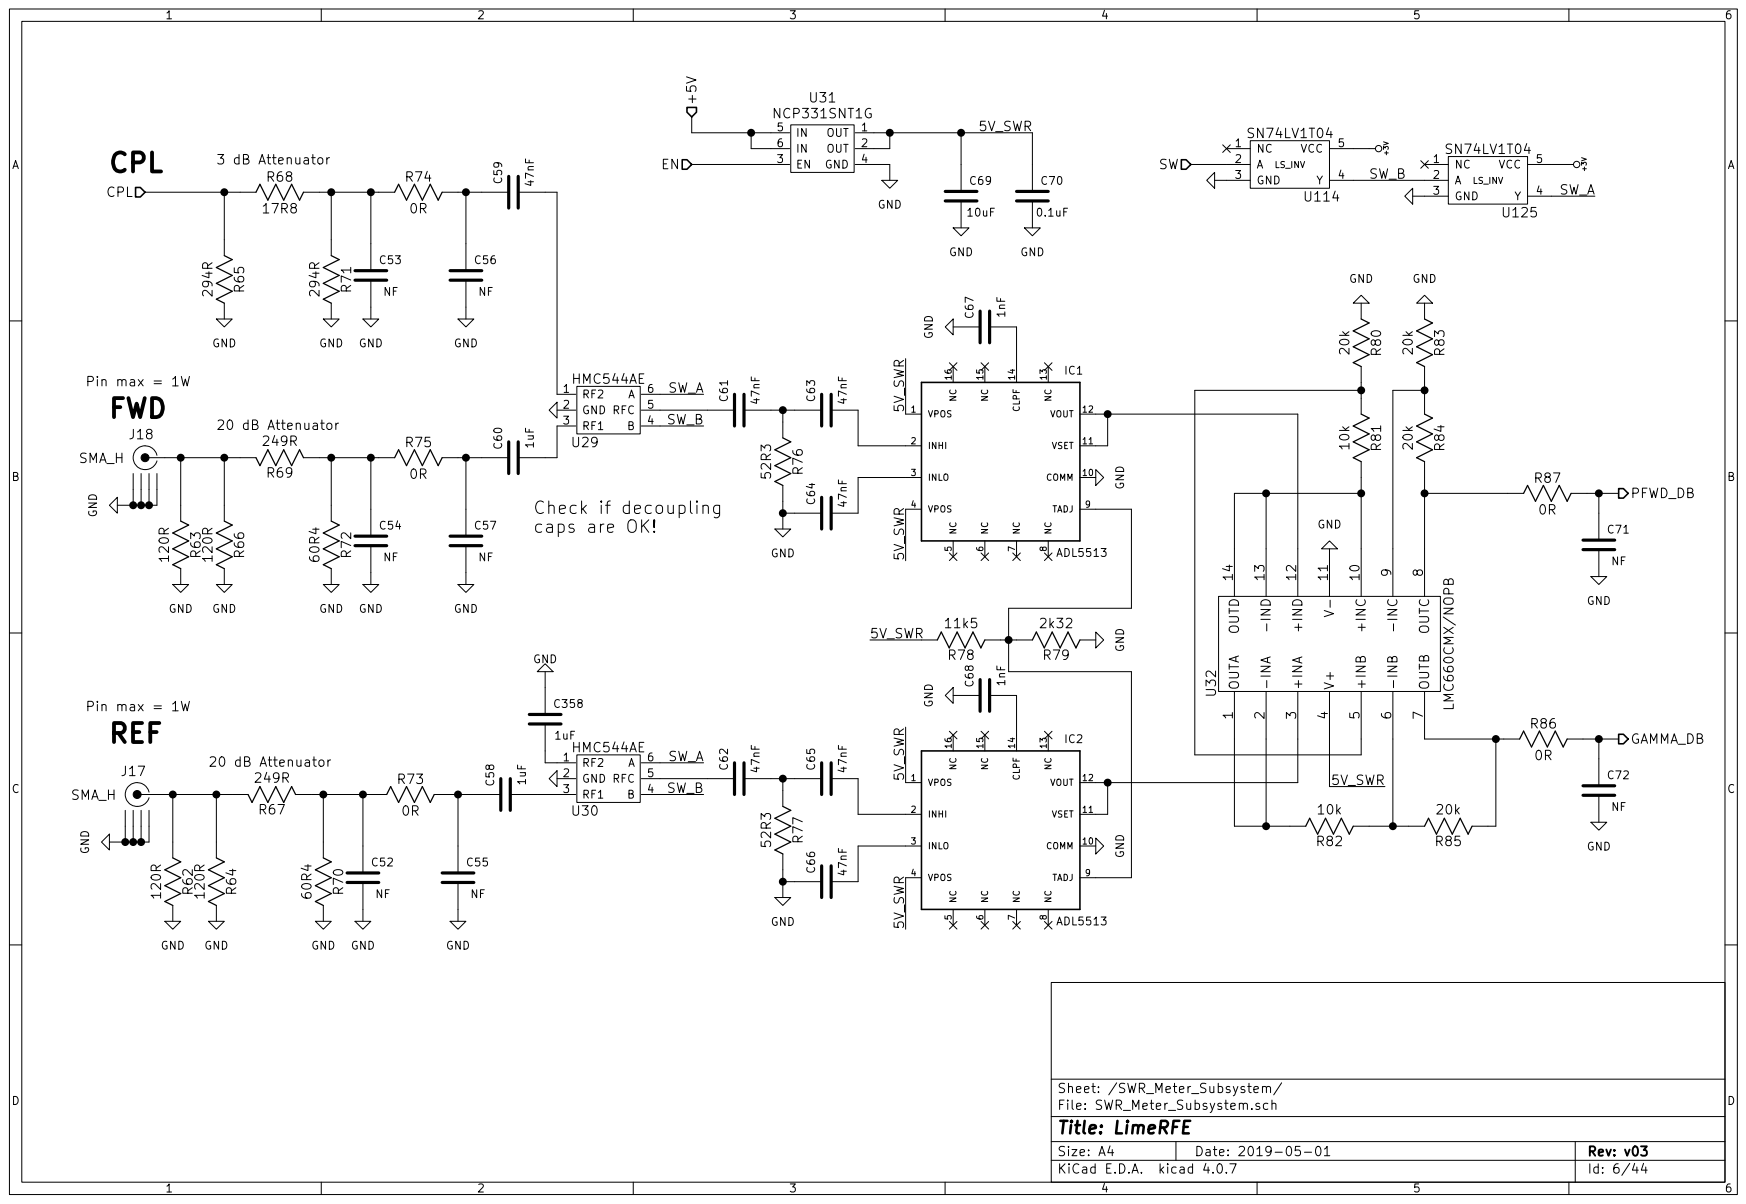
[picture p373: page 6]

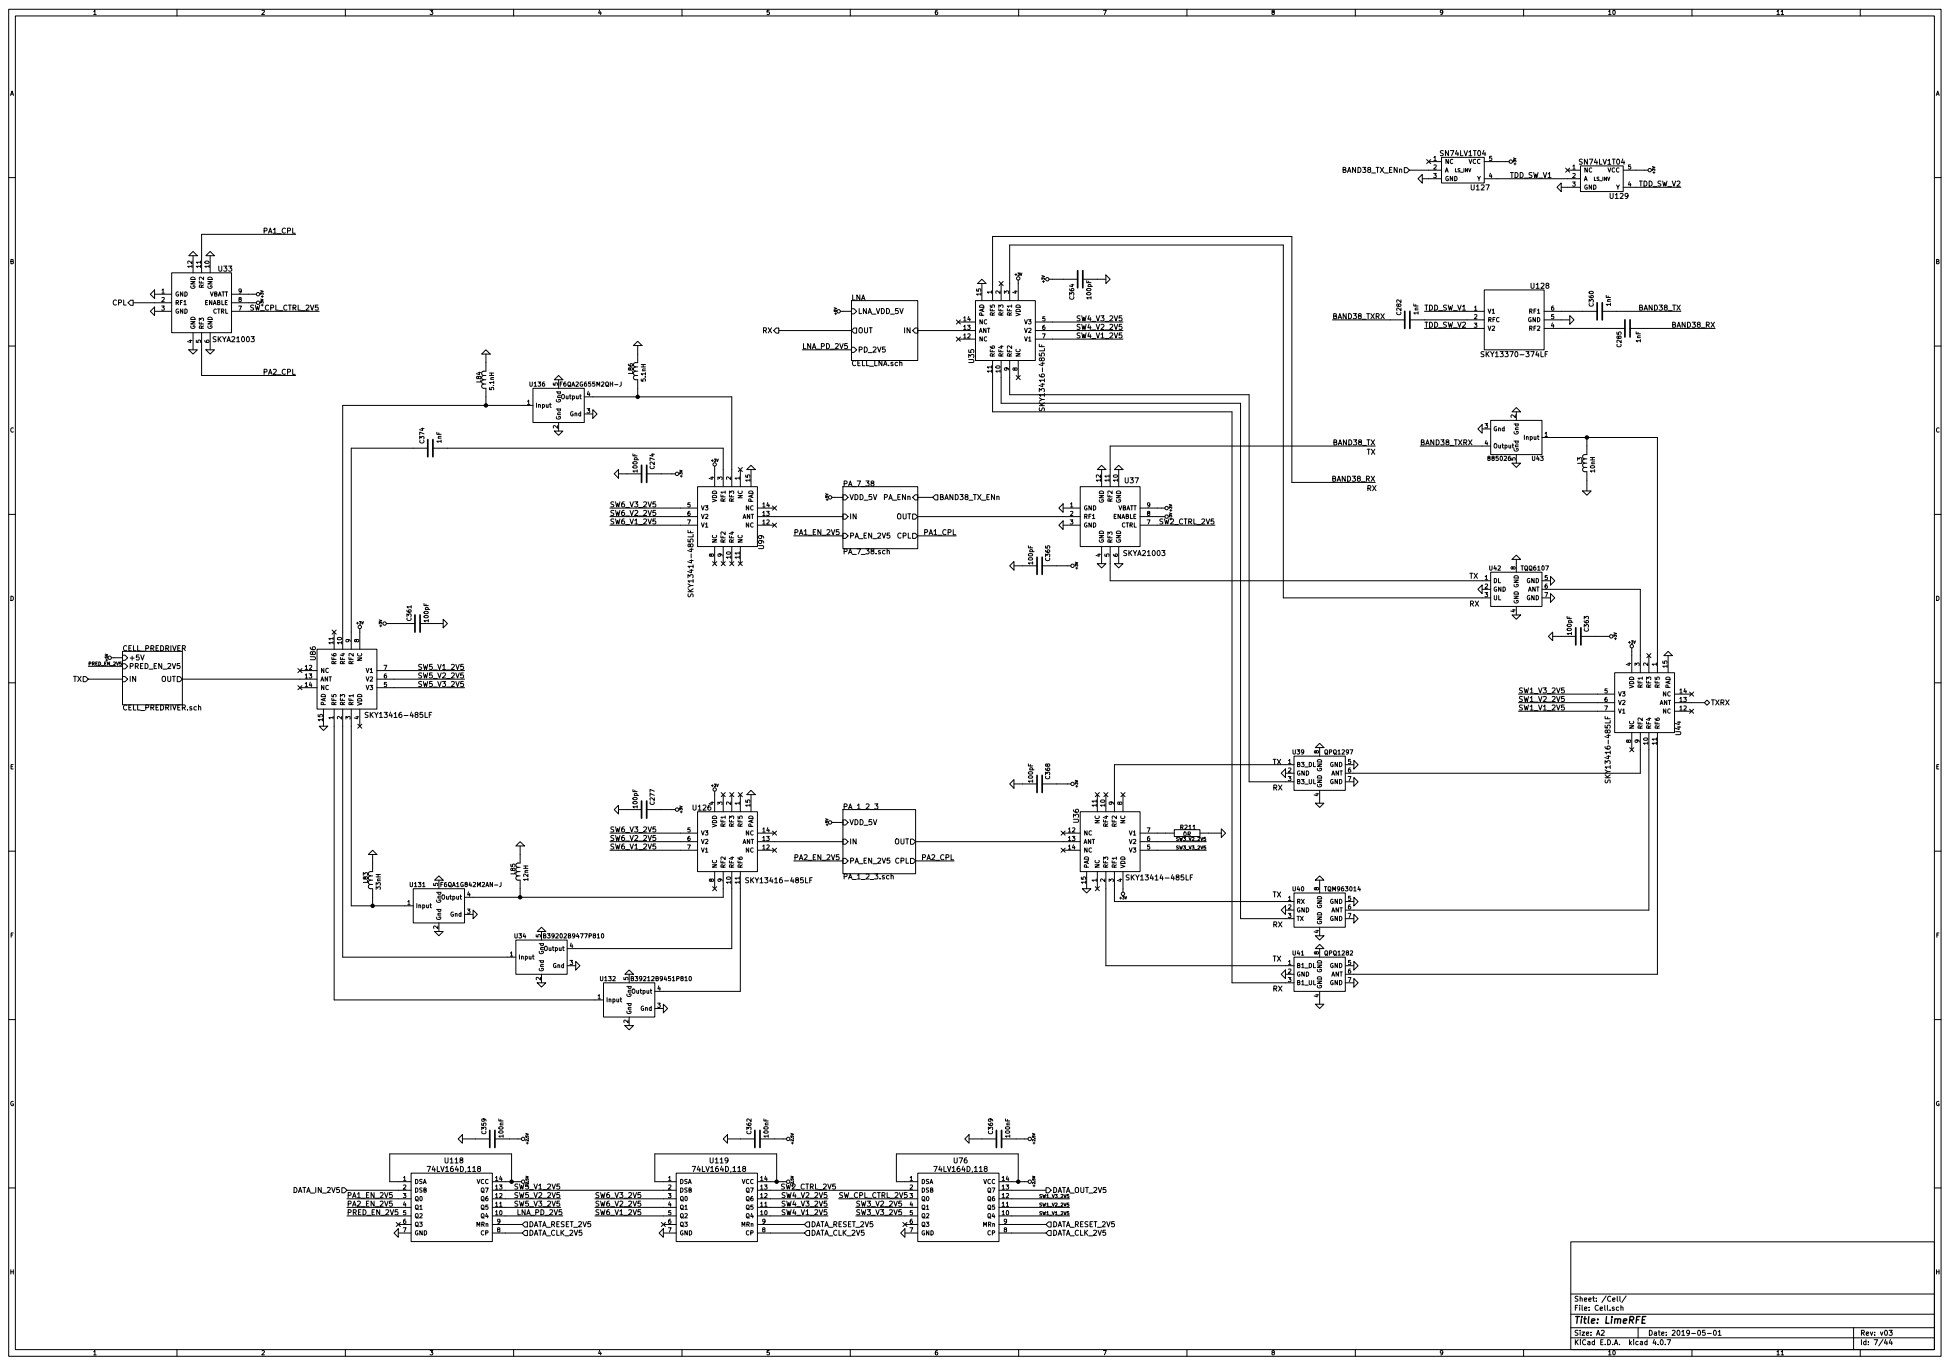
[picture p374: page 7]

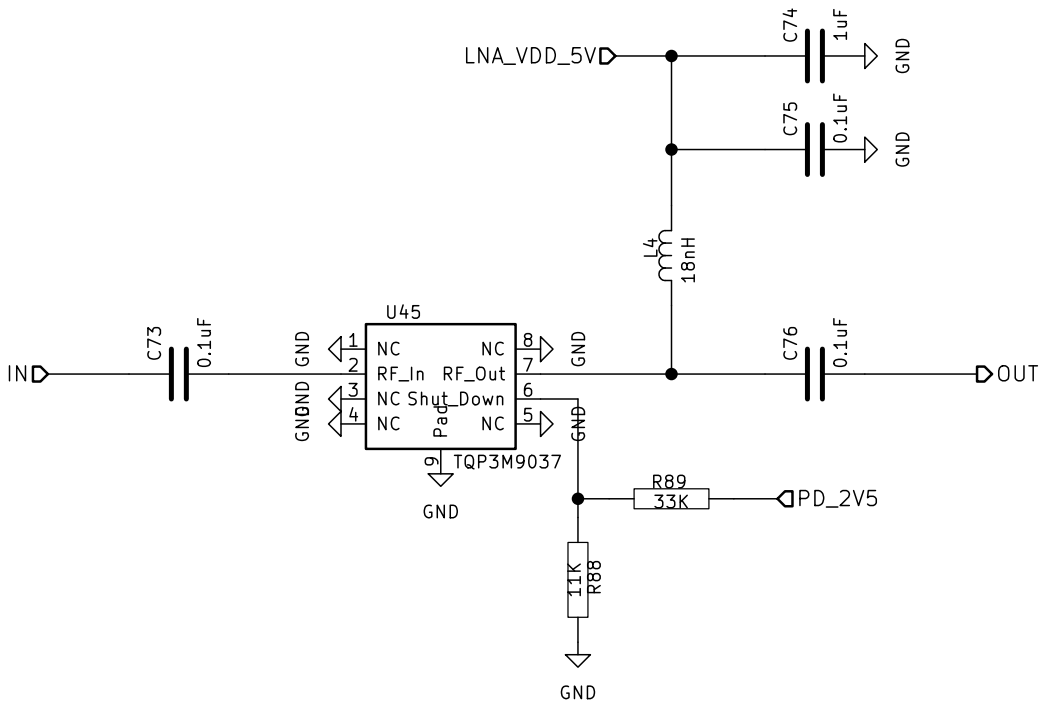
[picture p375: page 8]

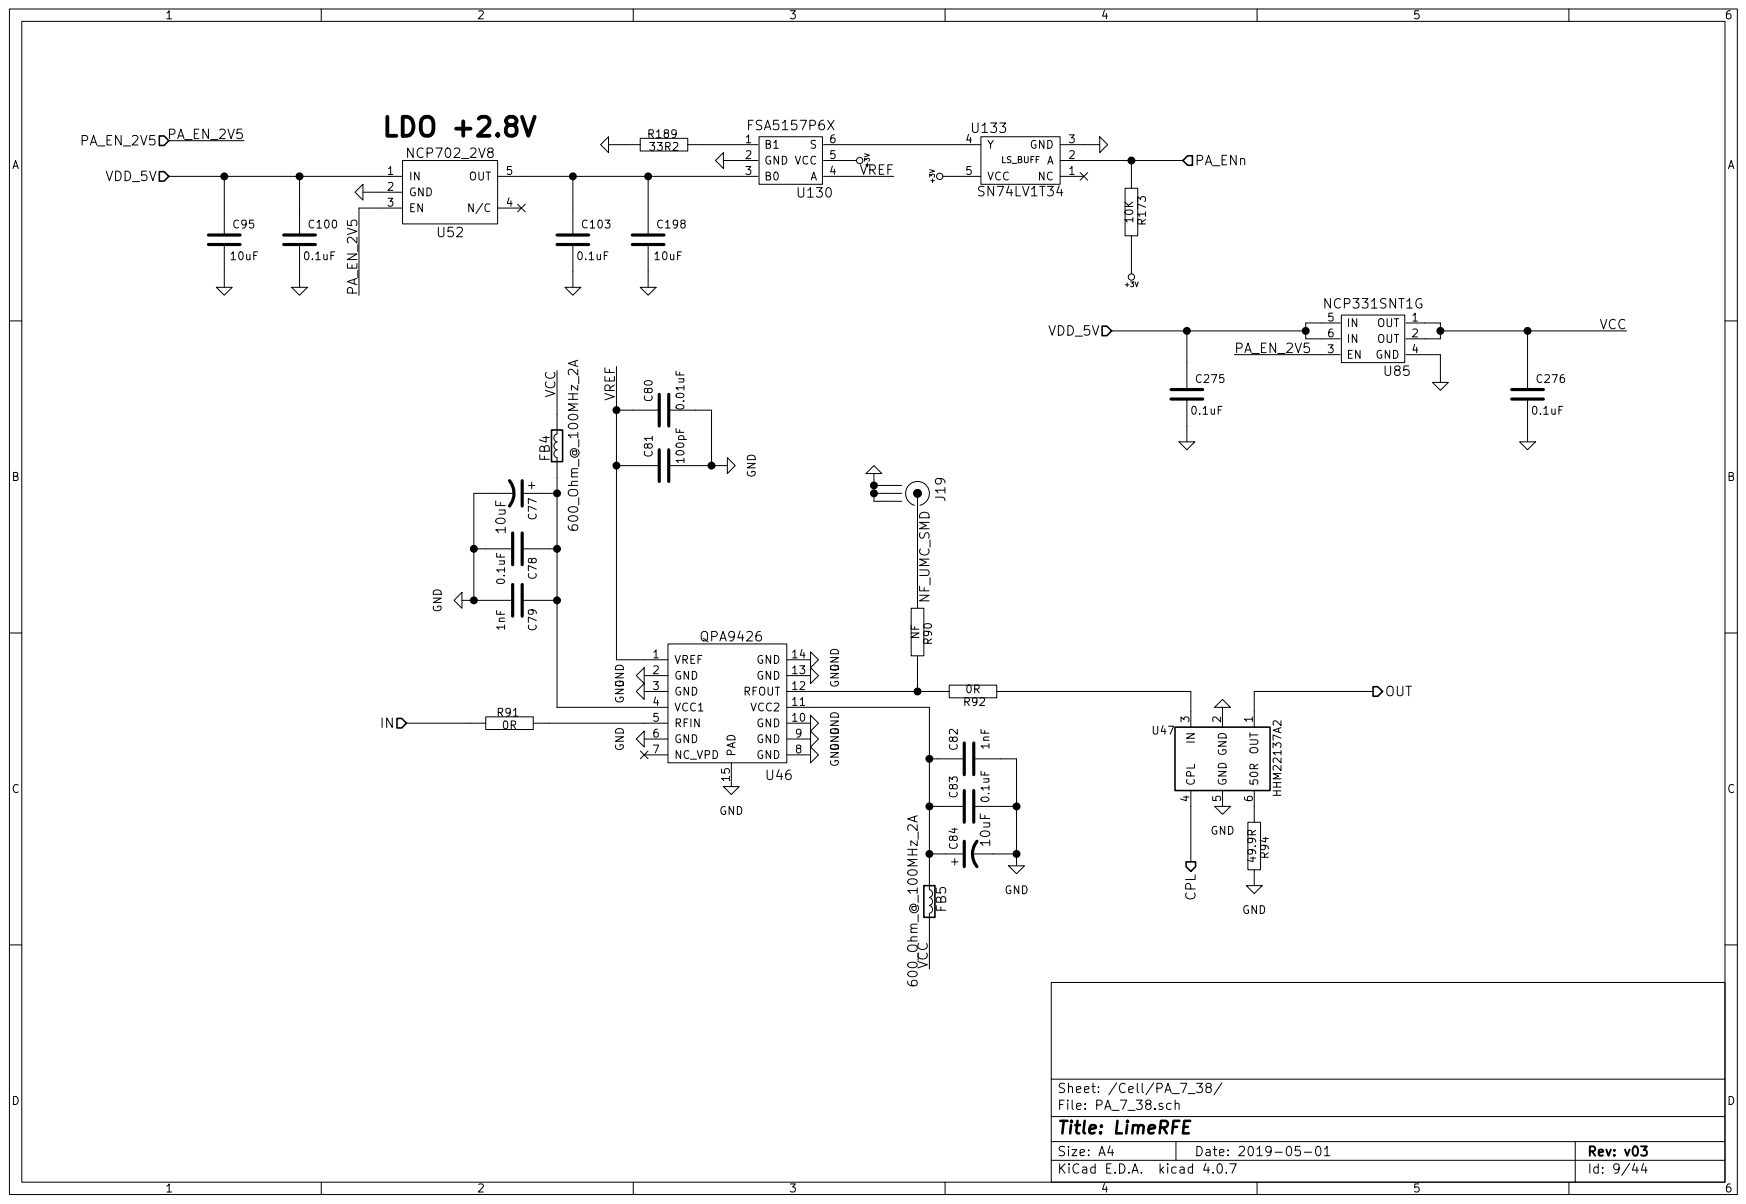
[picture p376: page 9]

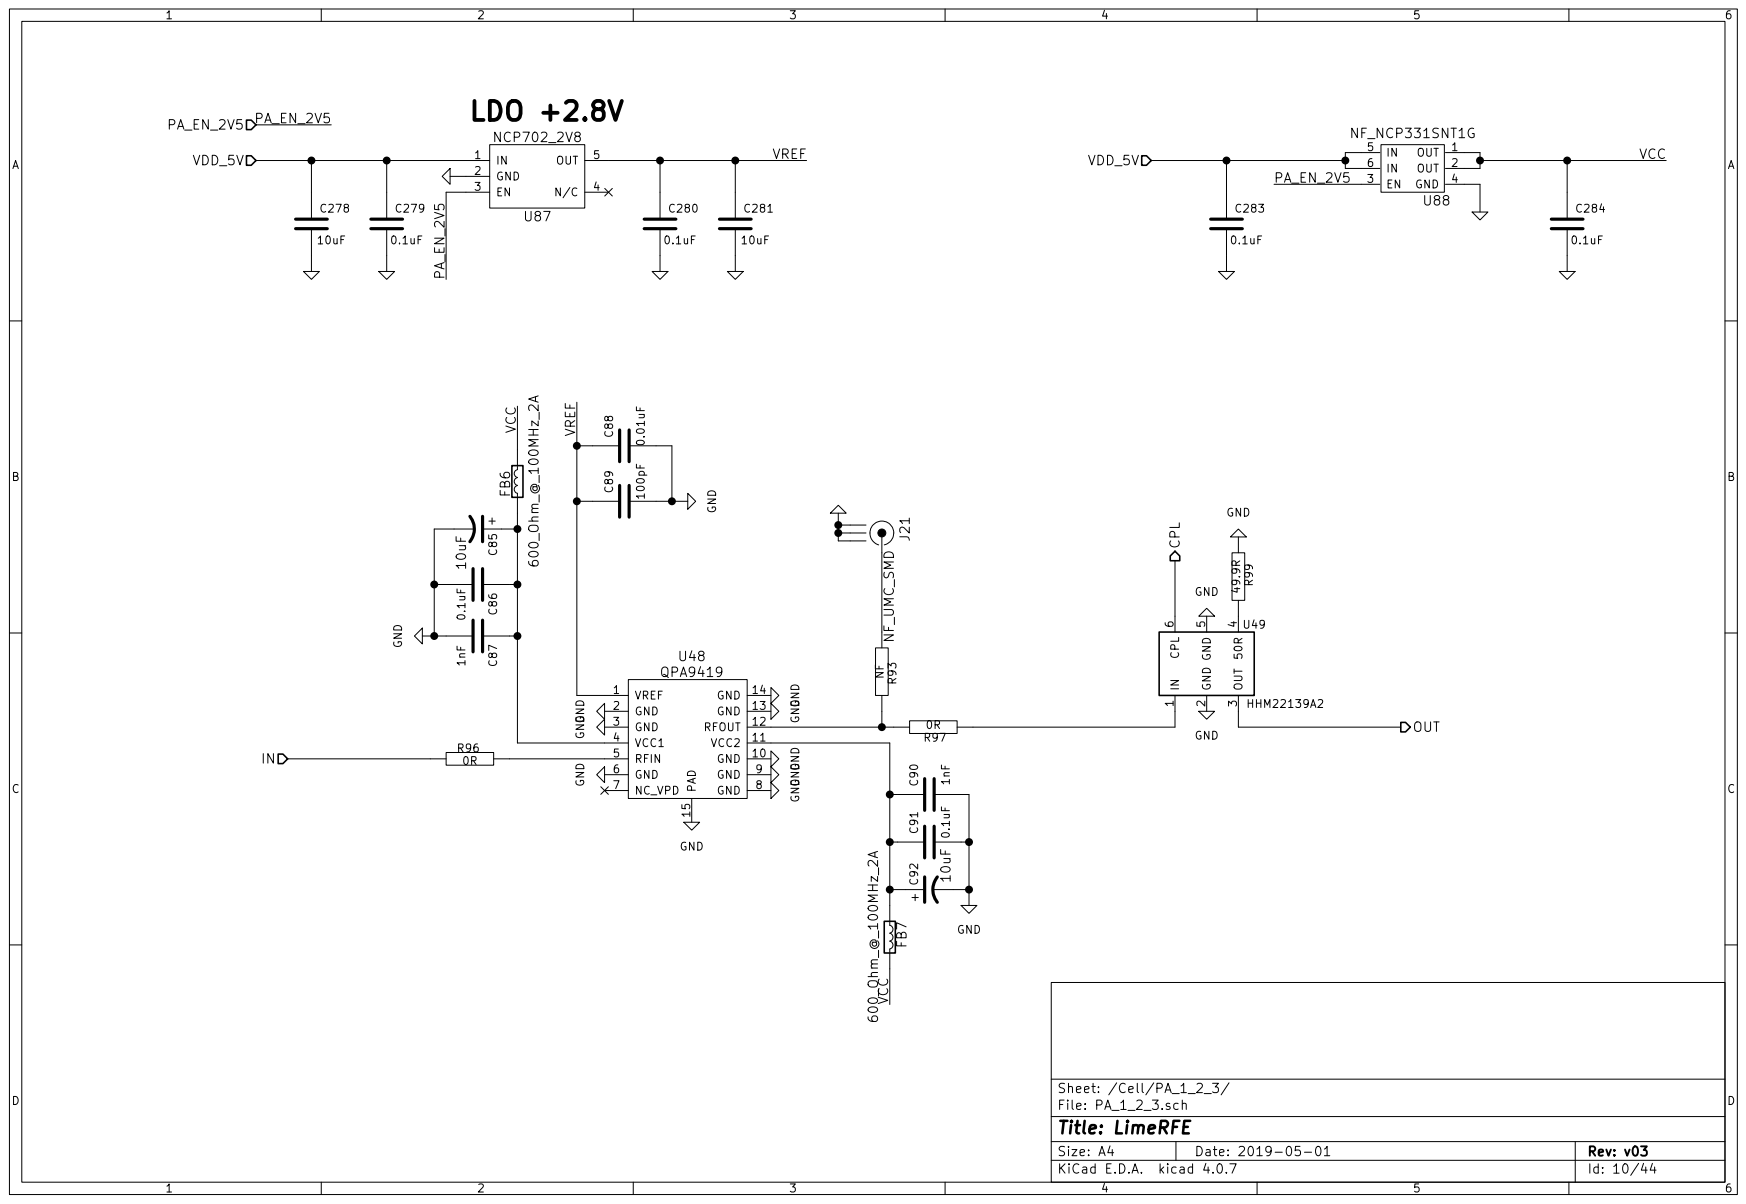
[picture p377: page 10]

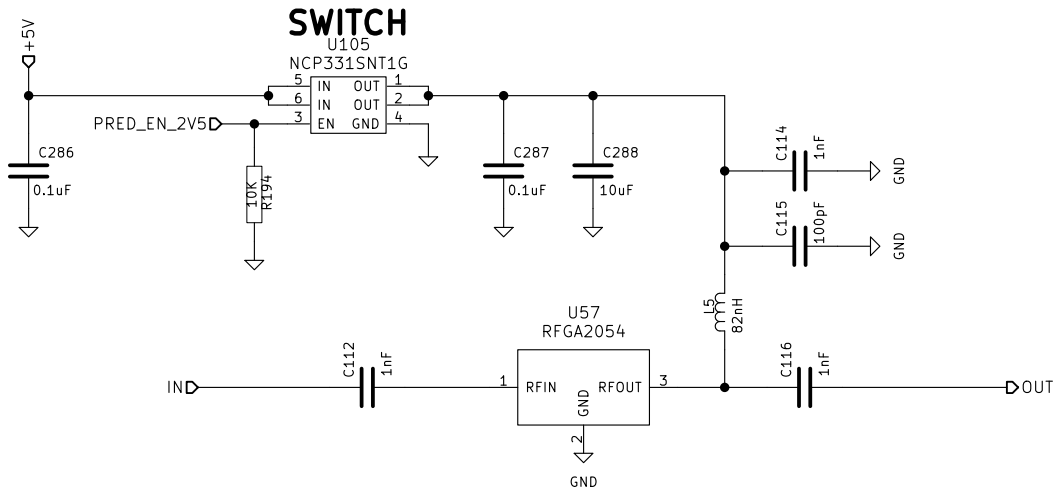
[picture p378: page 11]

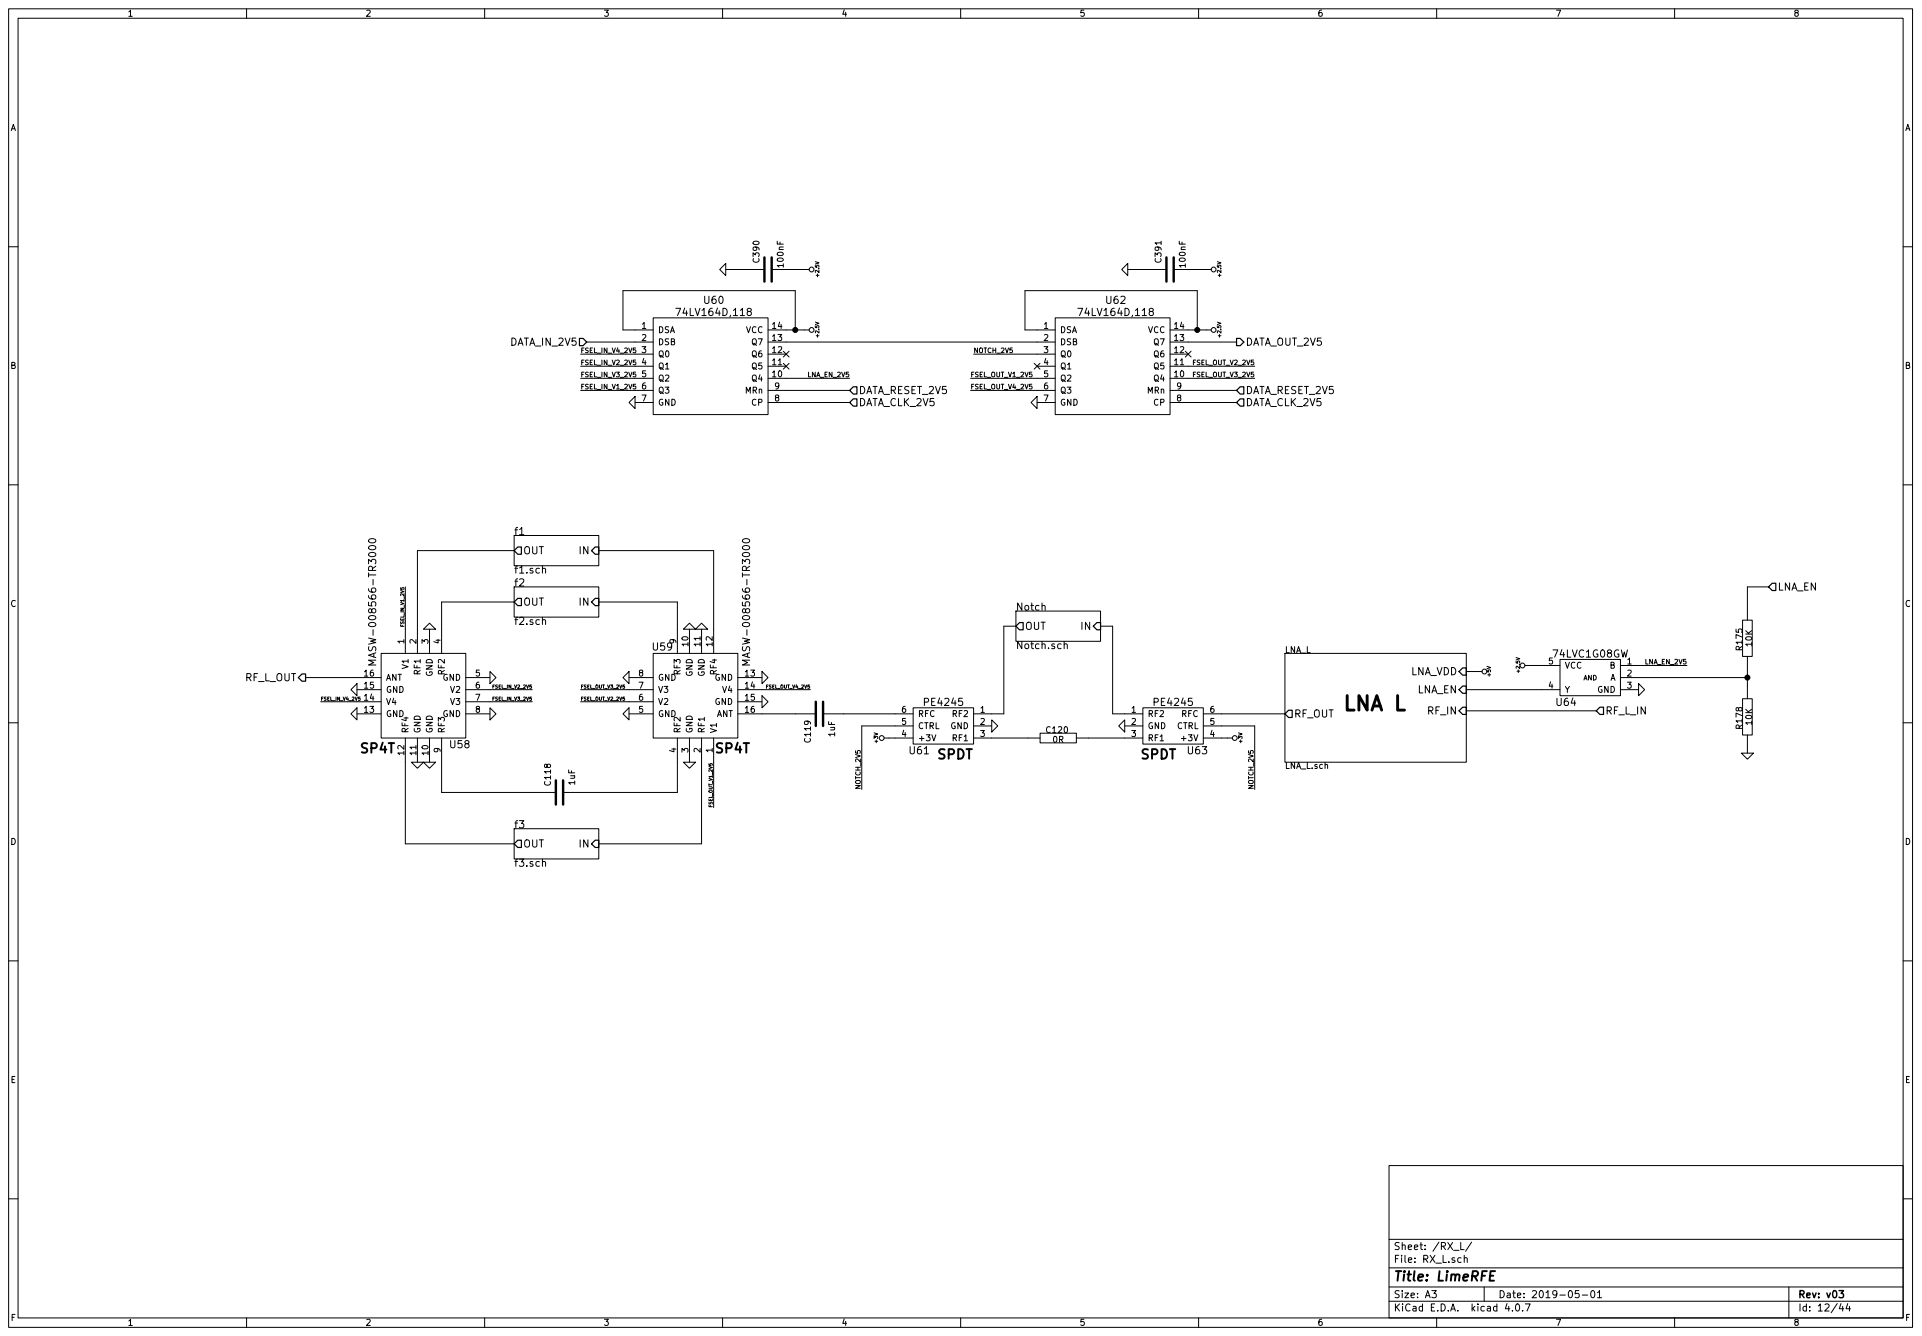
[picture p379: page 12]

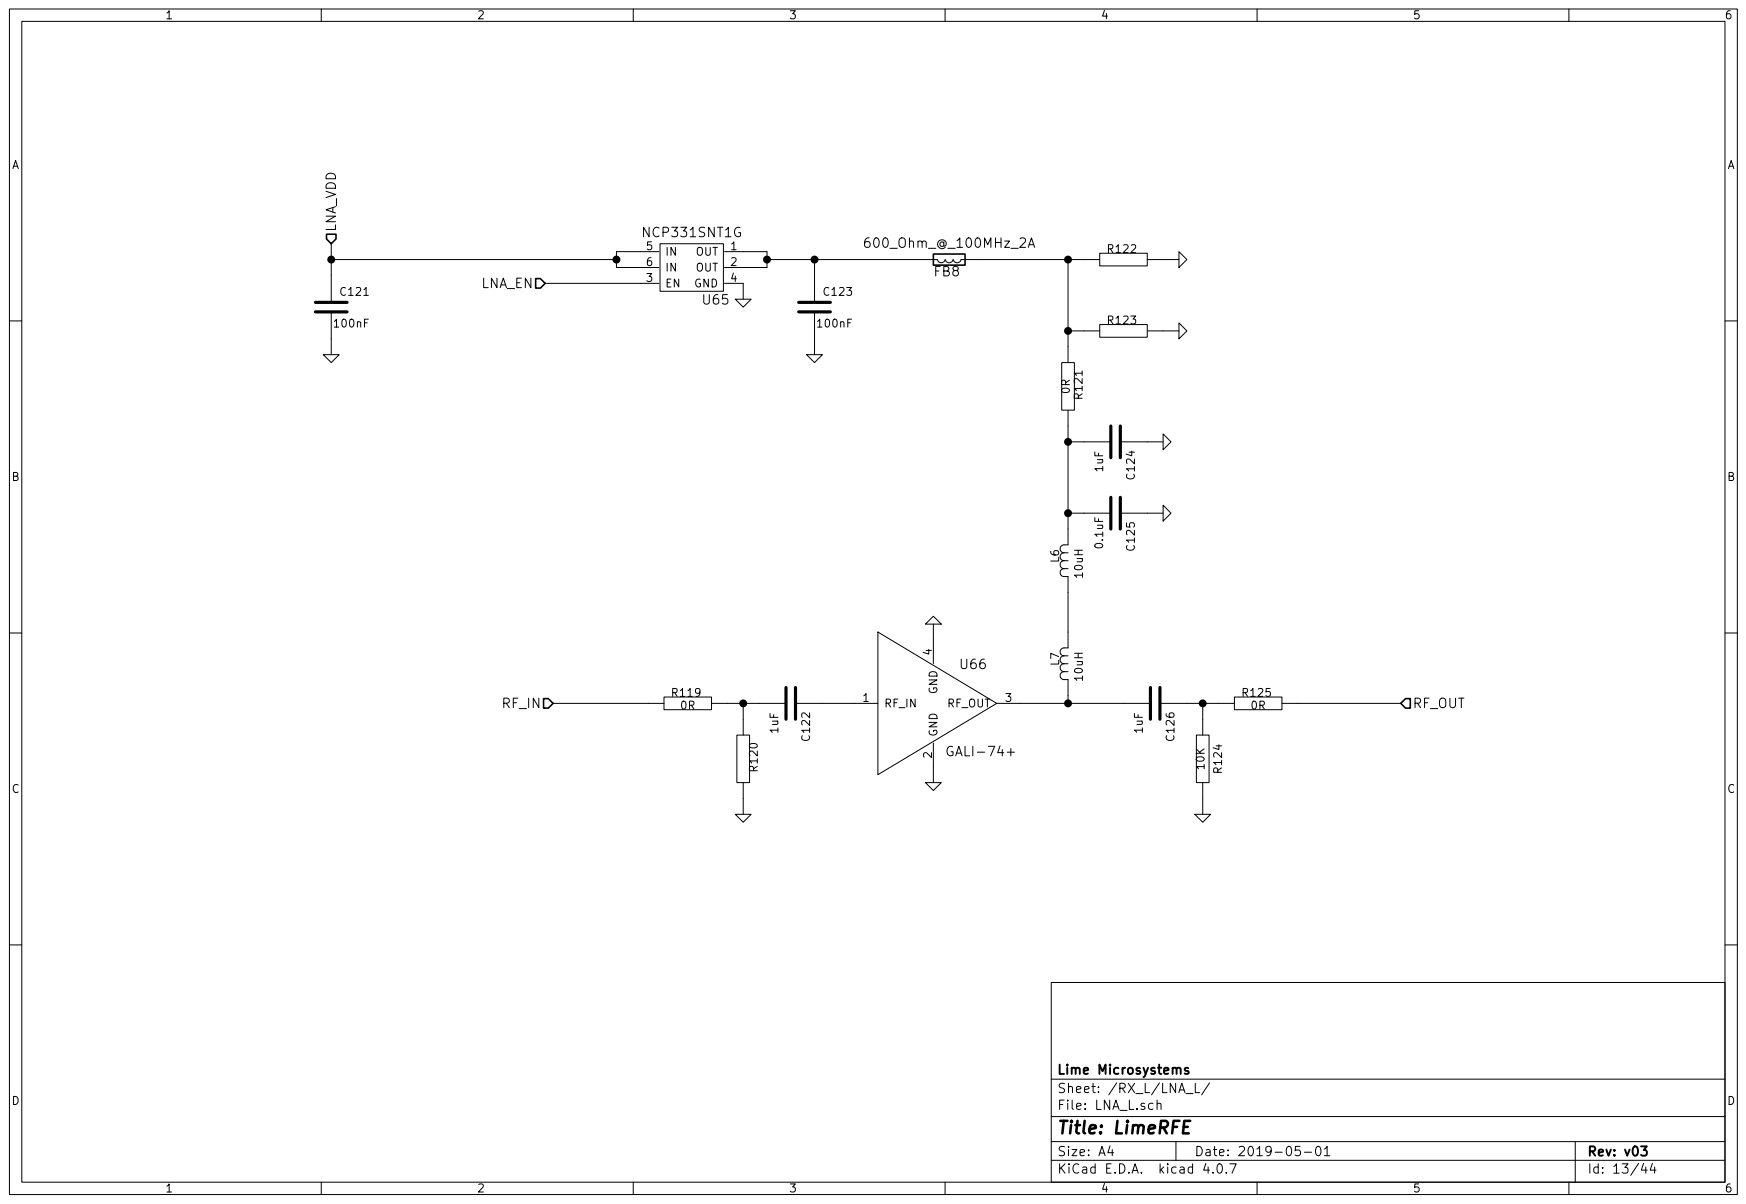
[picture p380: page 13]


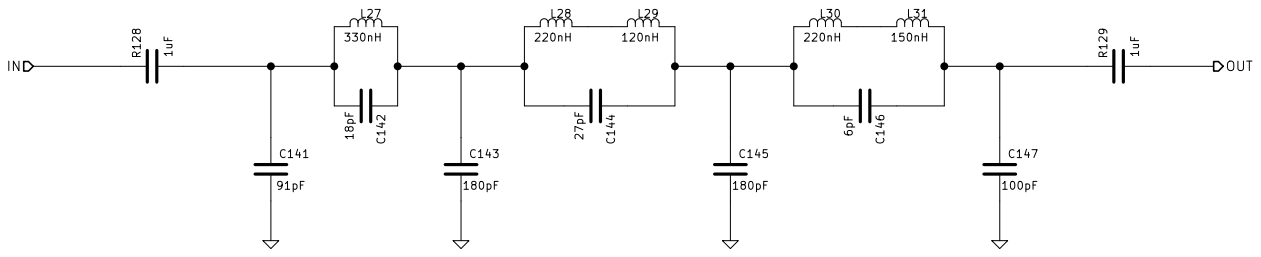
[picture p381: page 15]

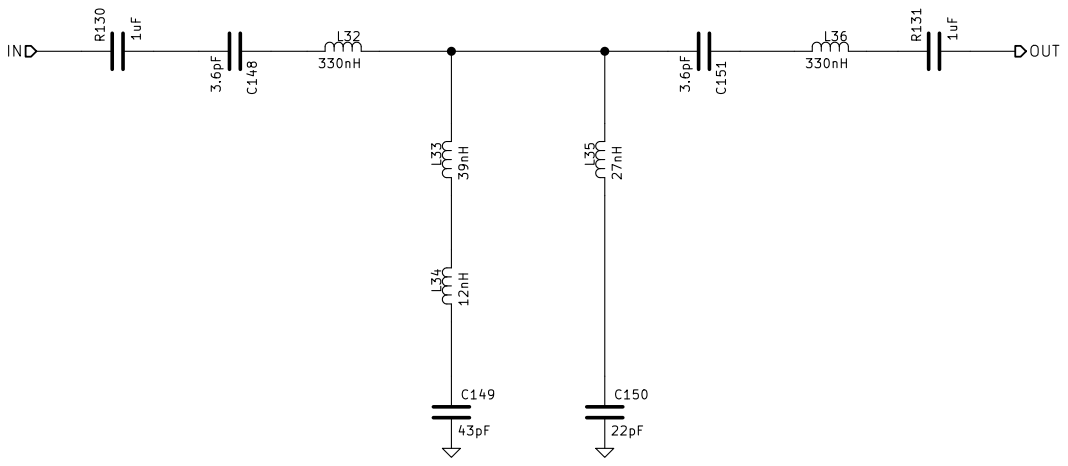
[picture p382: page 16]

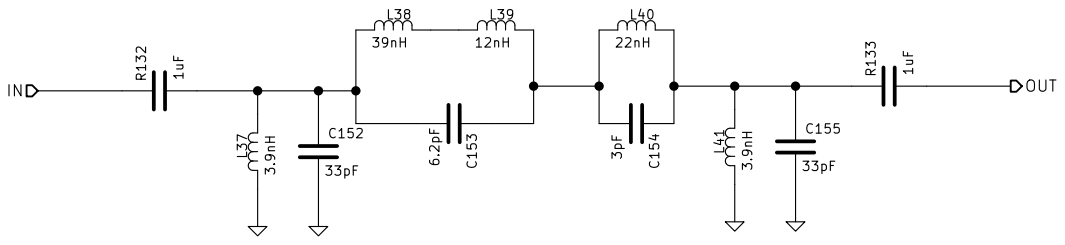
[picture p383: page 17]

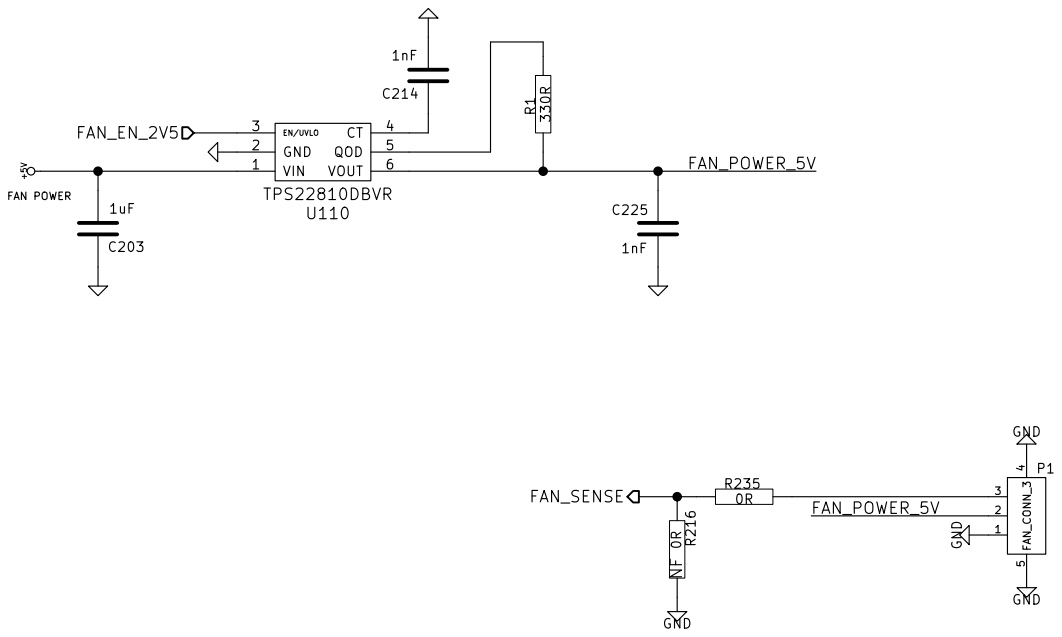
[picture p384: page 18]

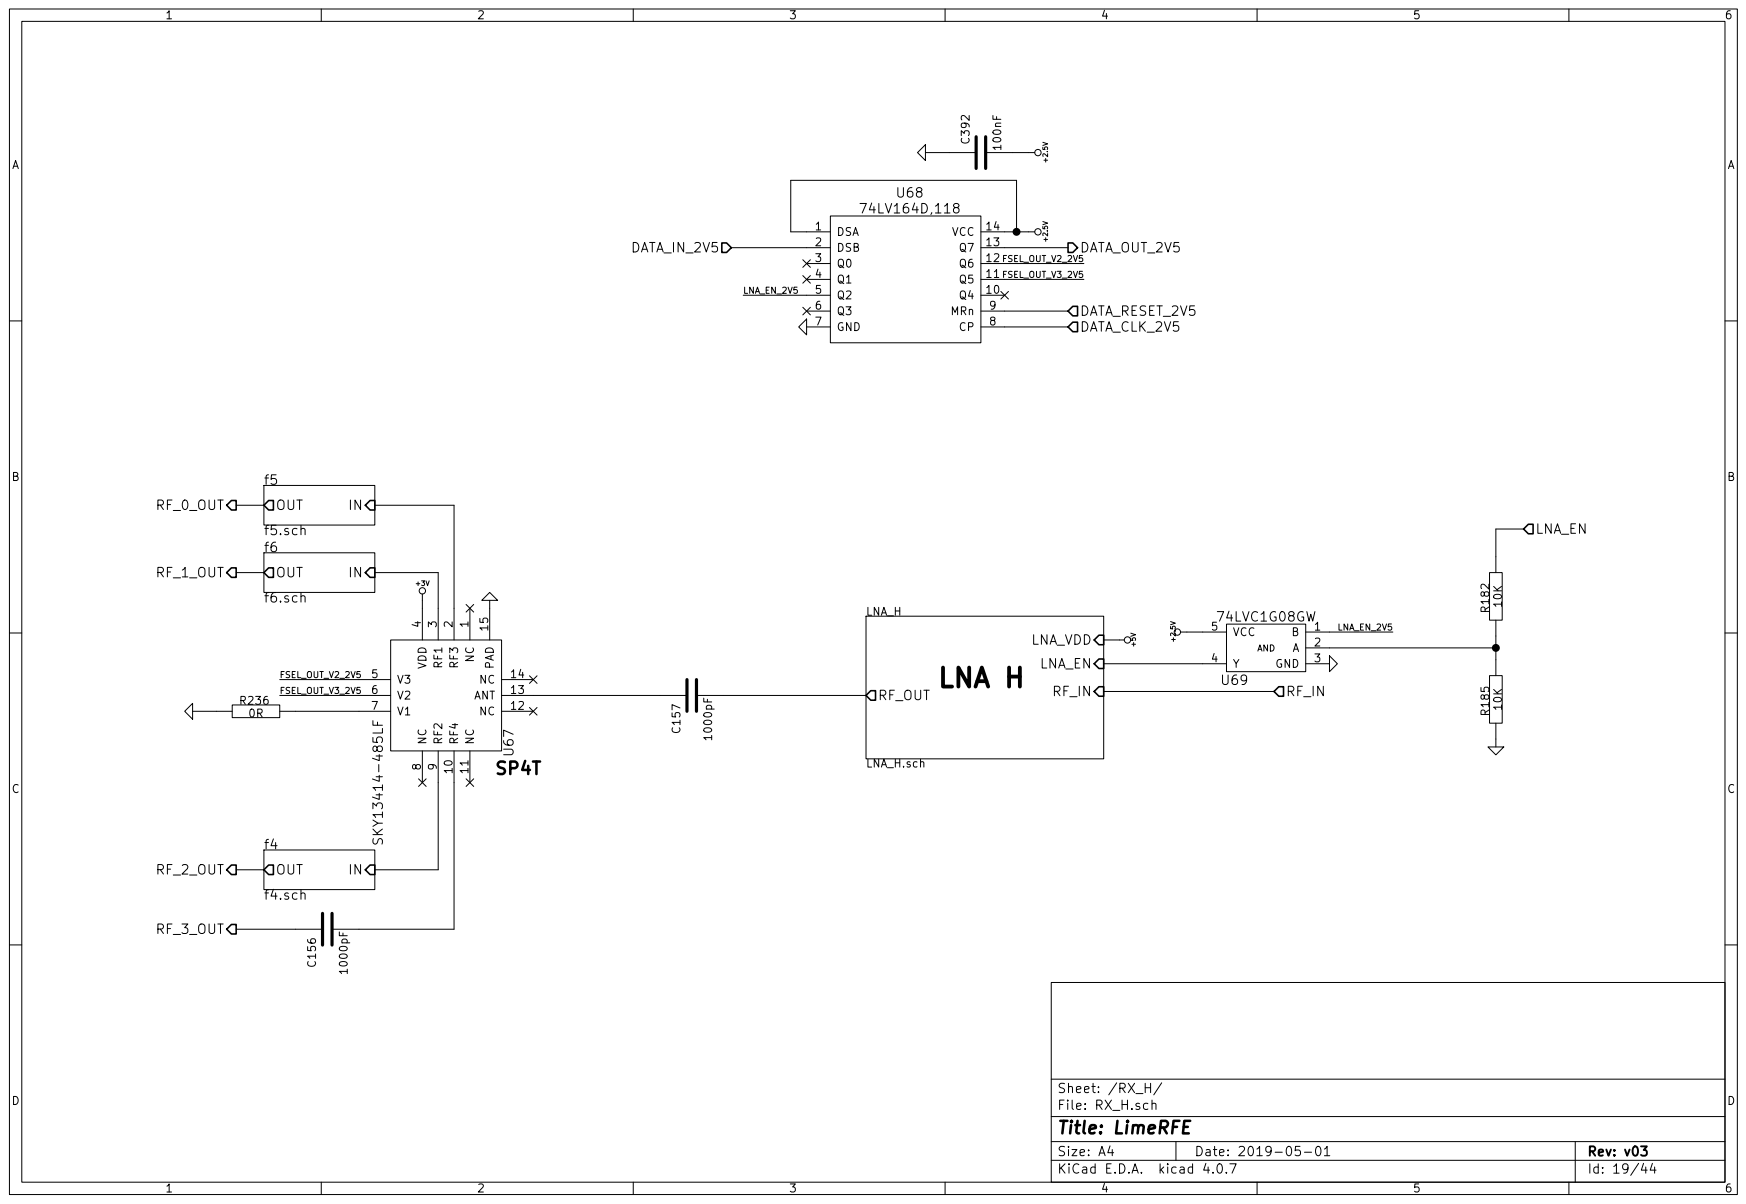
[picture p385: page 19]

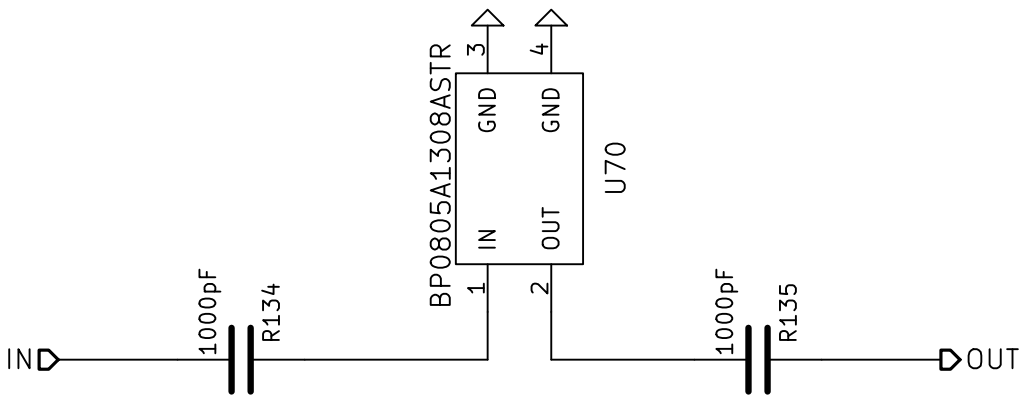
[picture p386: page 20]

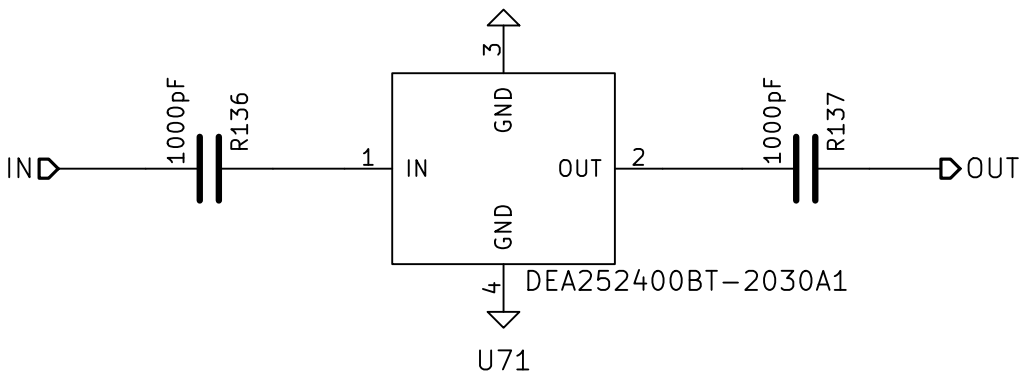
[picture p387: page 21]

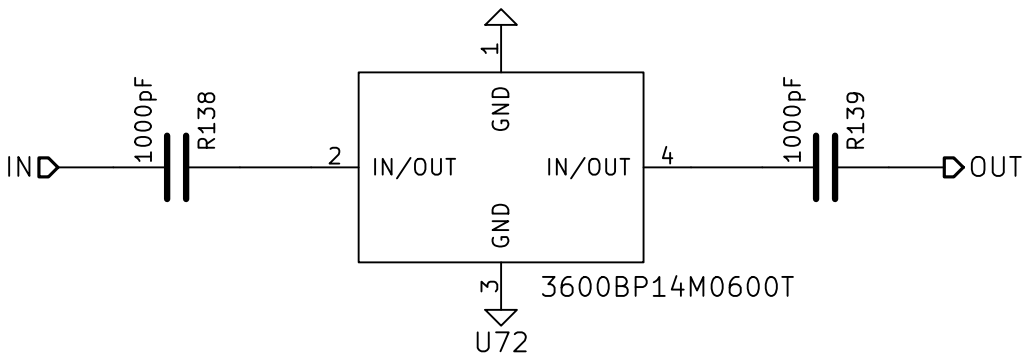
[picture p388: page 22]

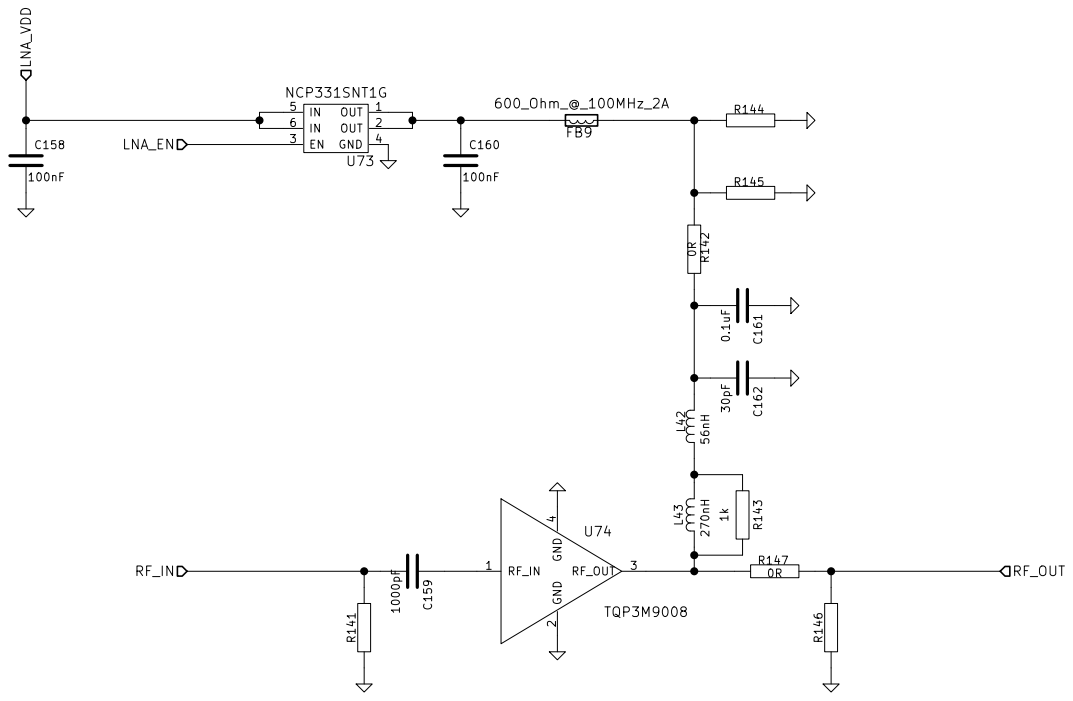
[picture p389: page 23]

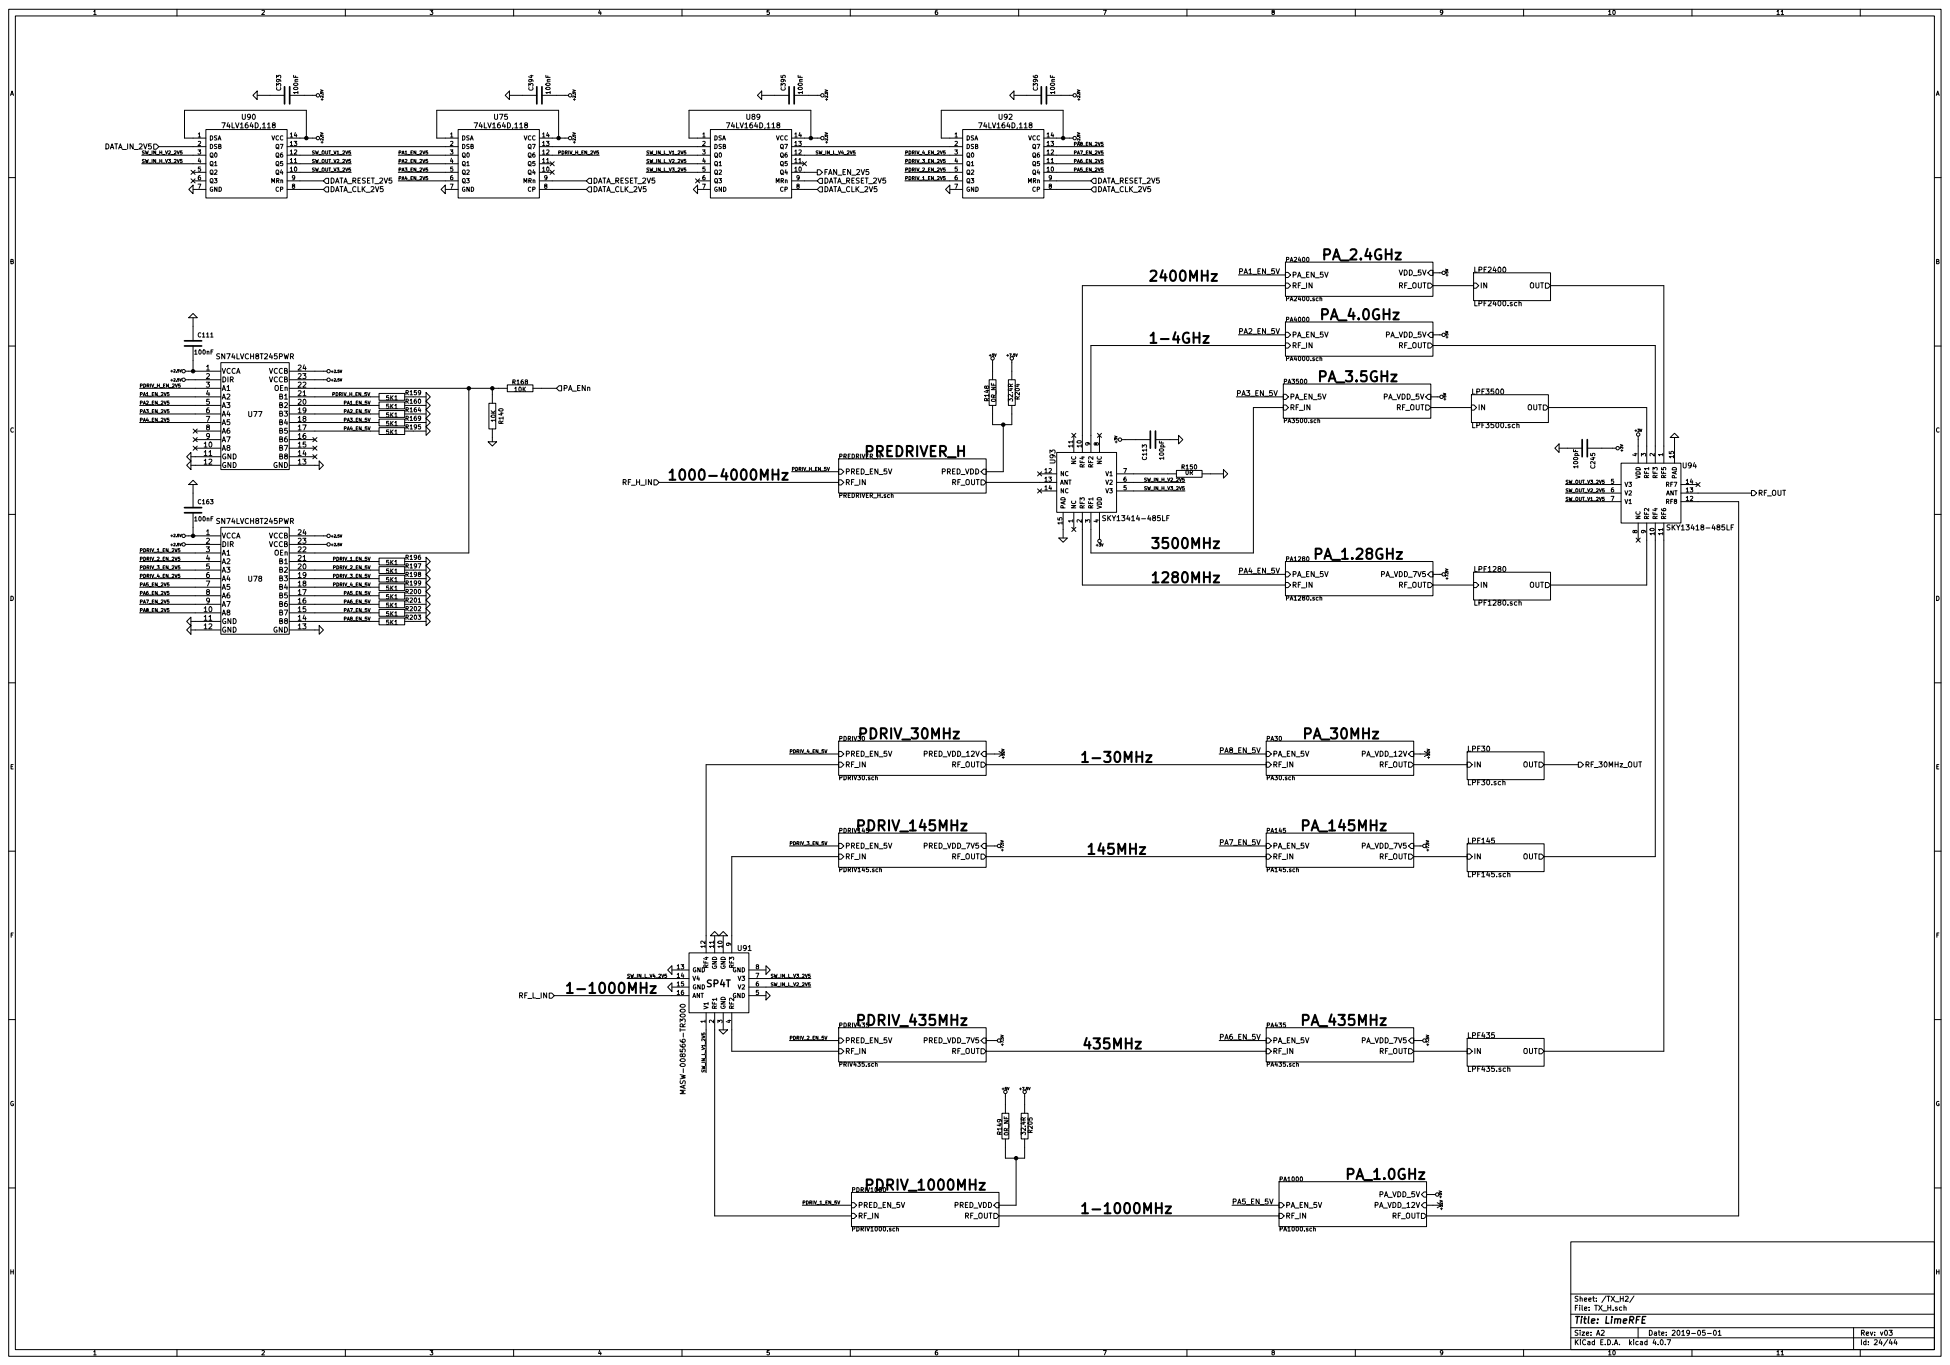
[picture p390: page 24]


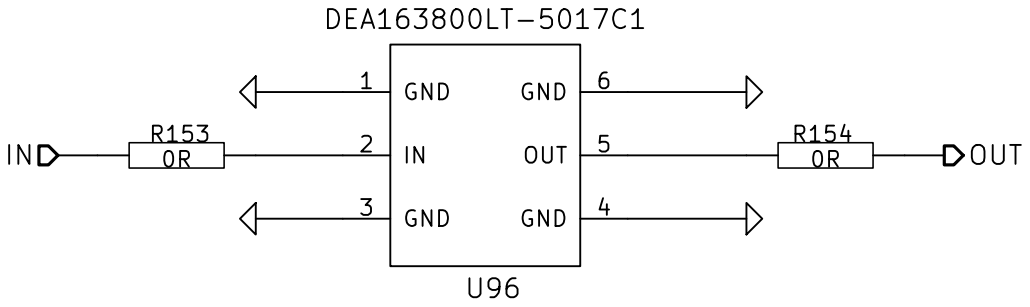
[picture p391: page 26]


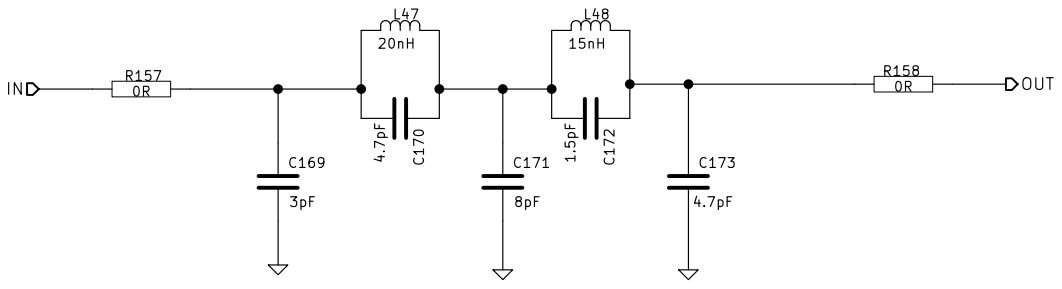
[picture p392: page 28]

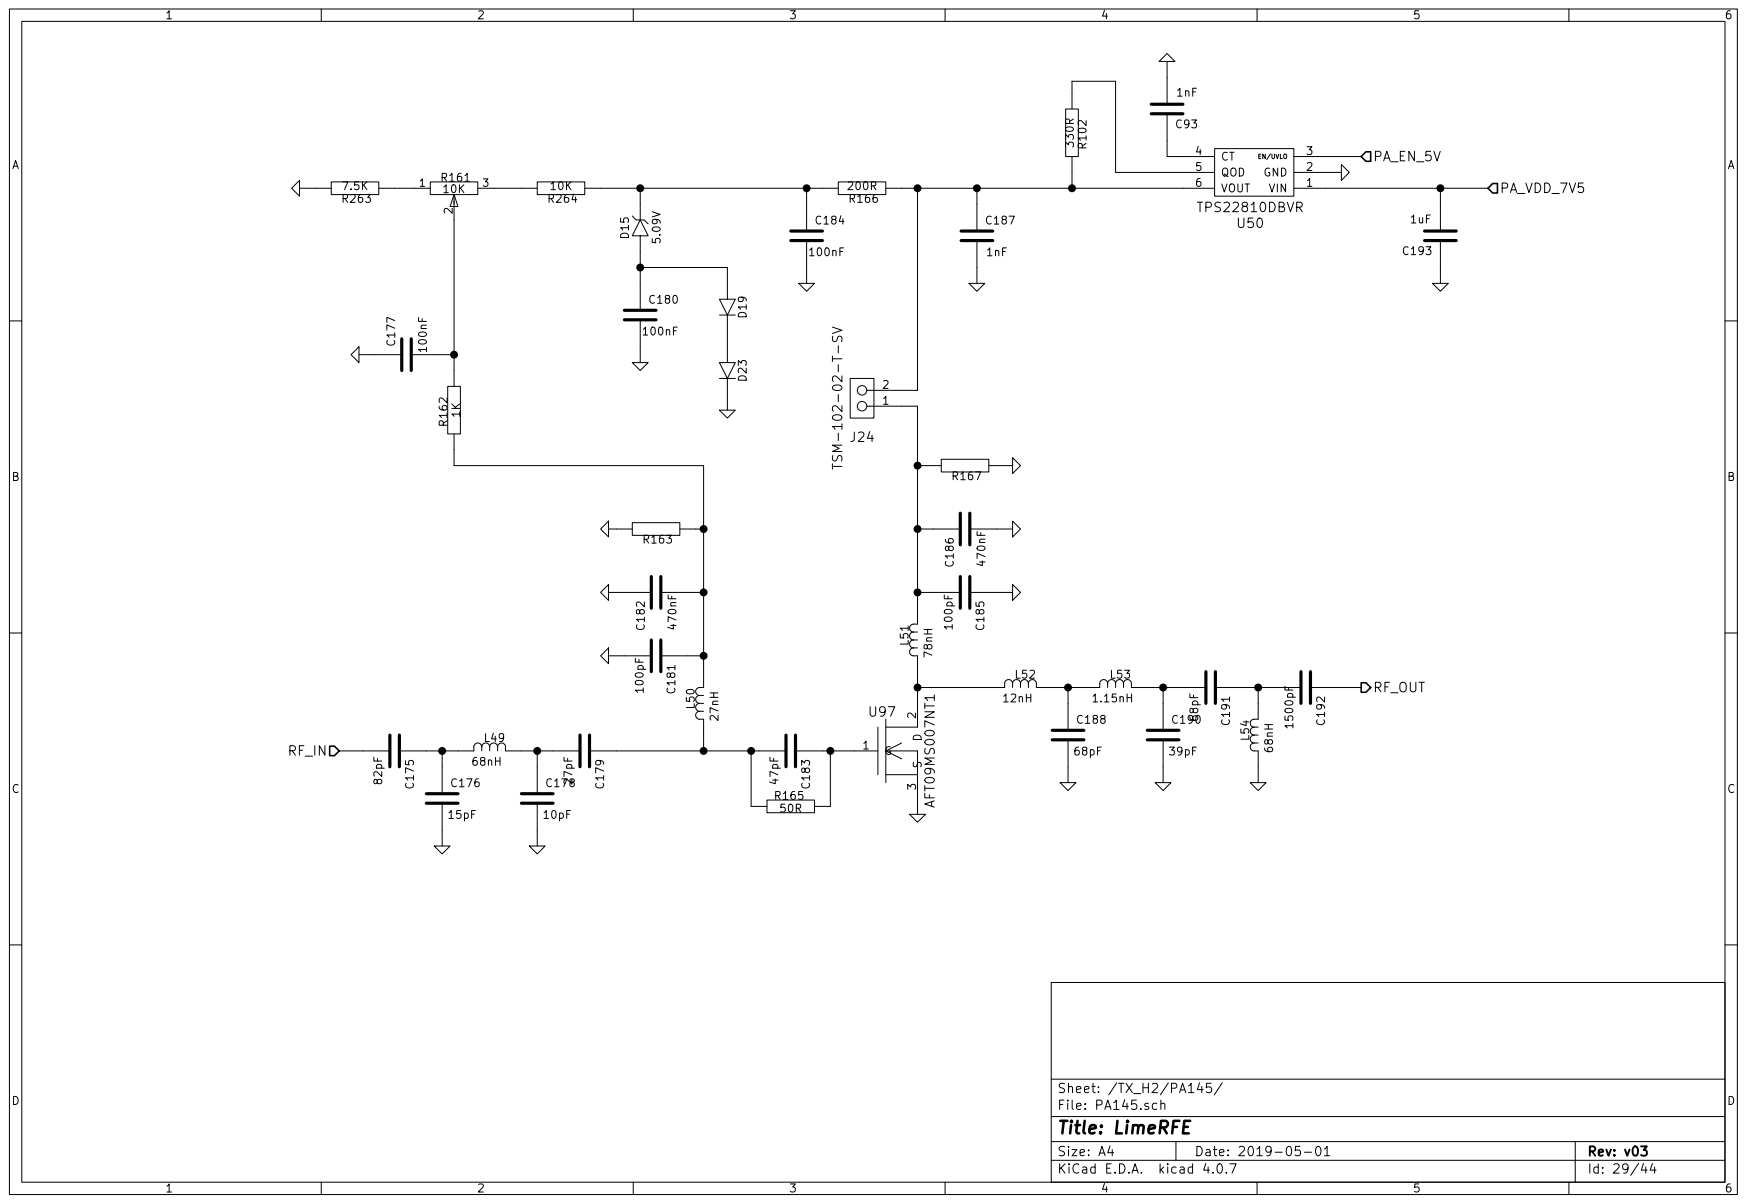
[picture p393: page 29]

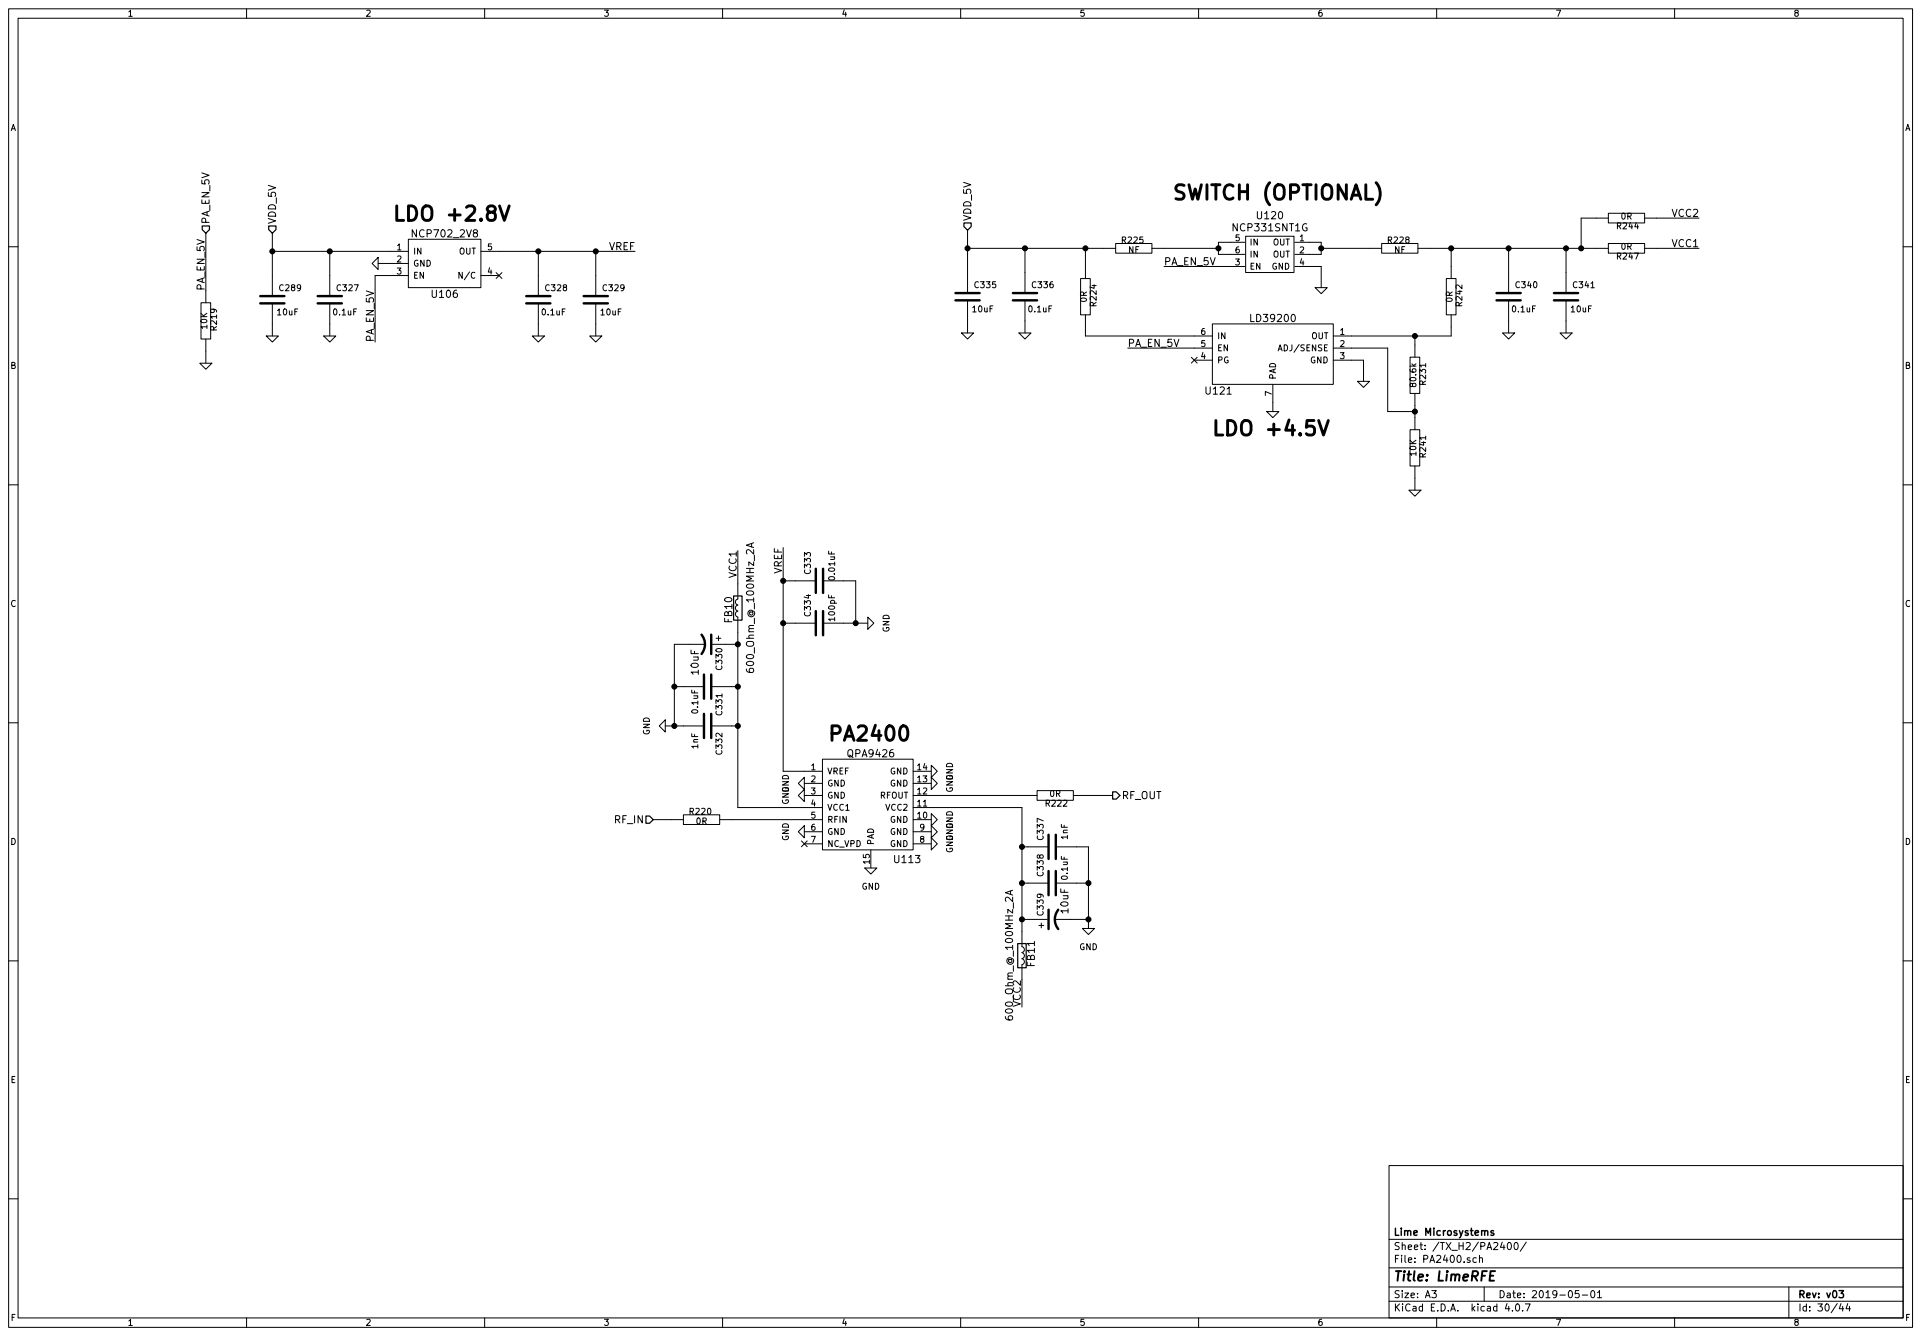
[picture p394: page 30]

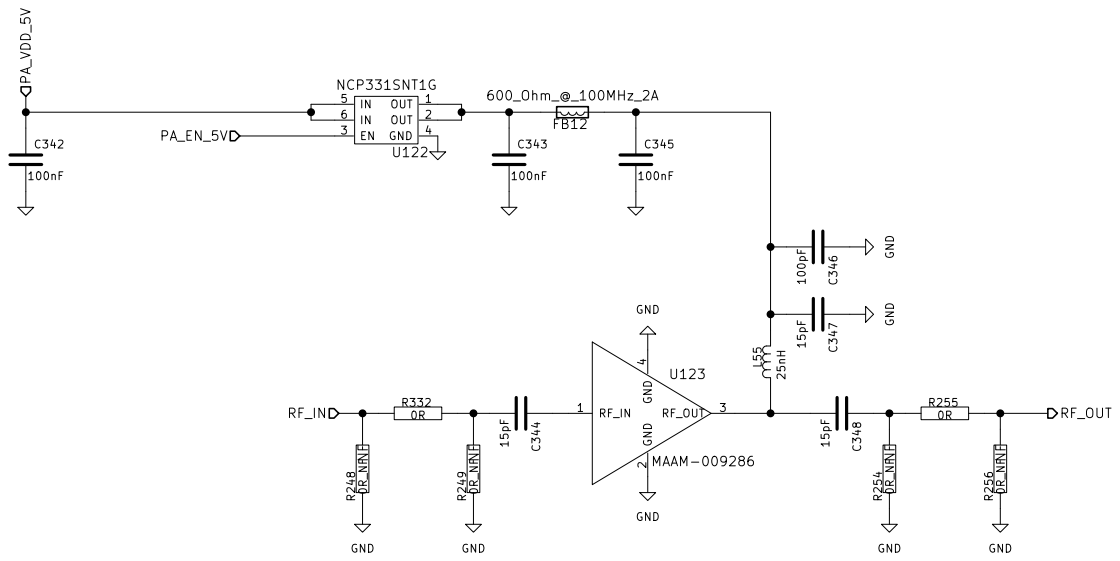
[picture p395: page 31]

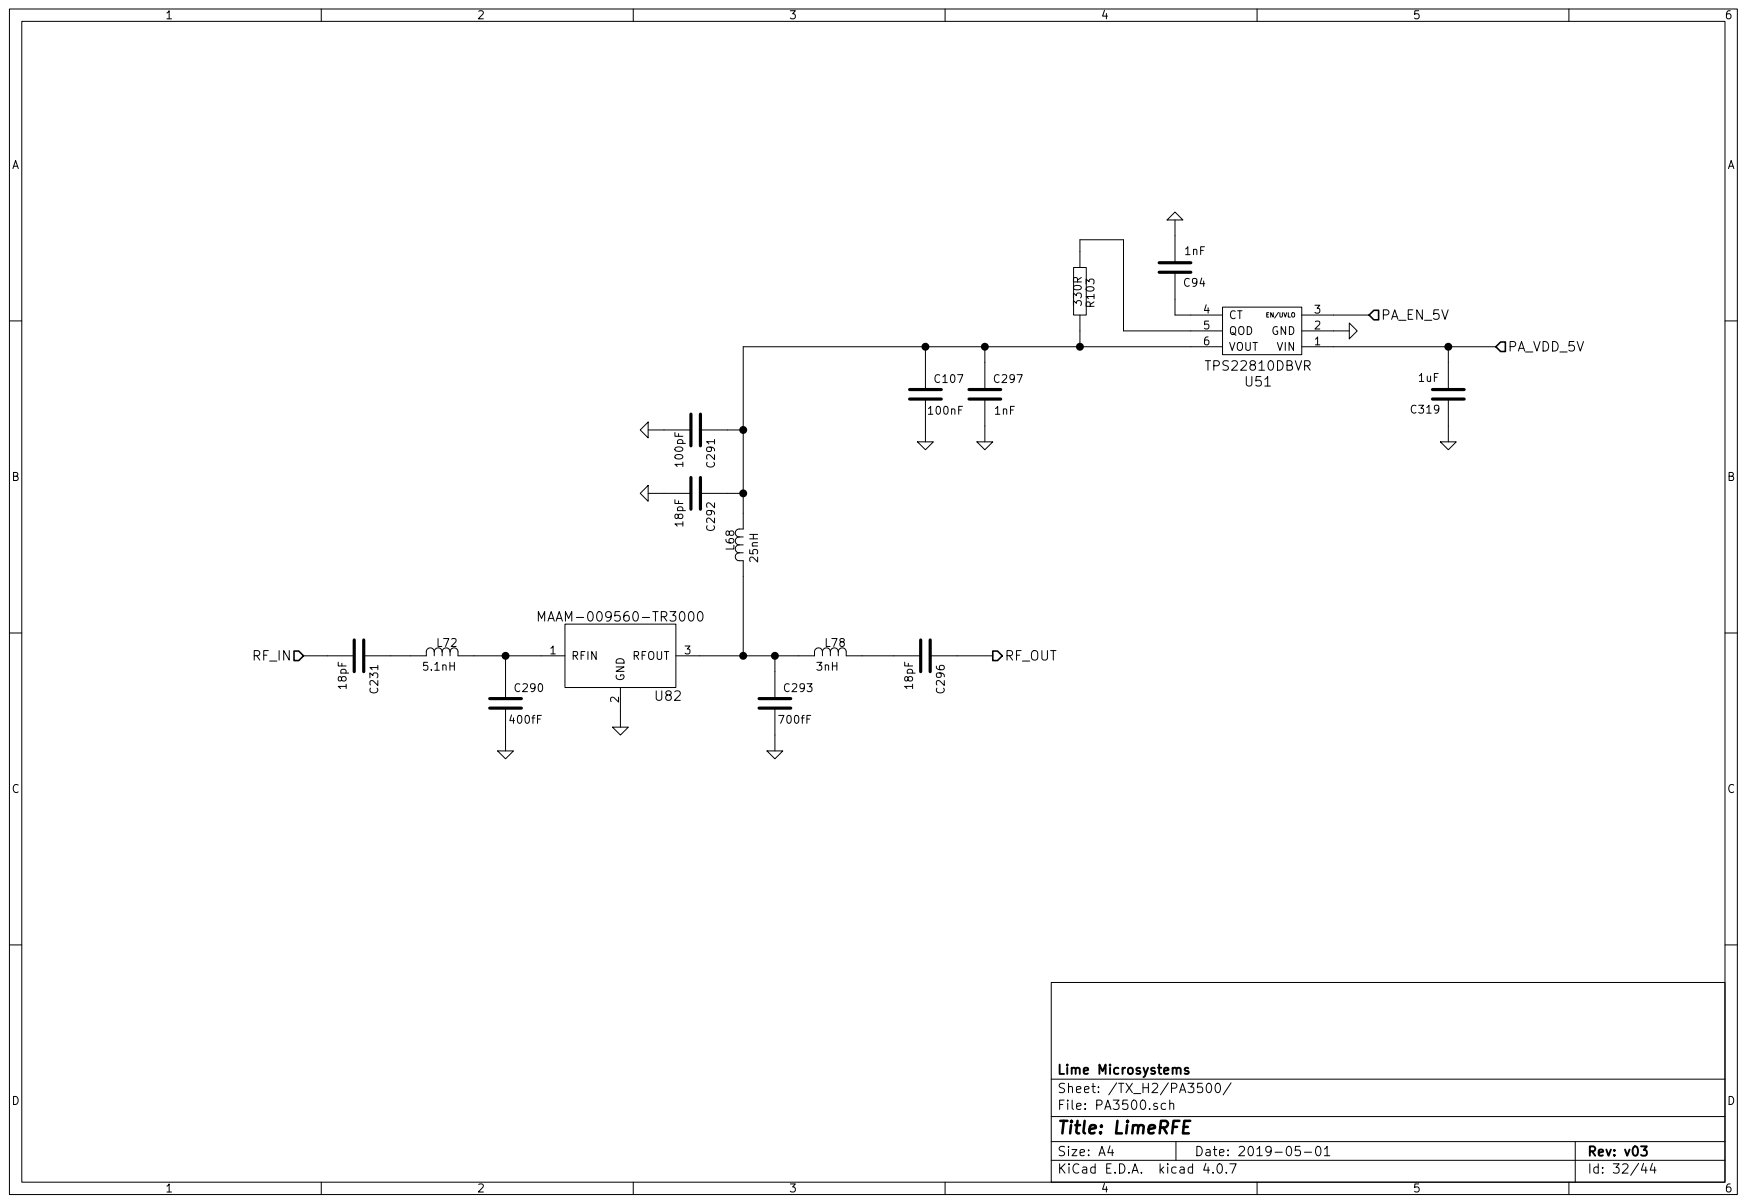
[picture p396: page 32]

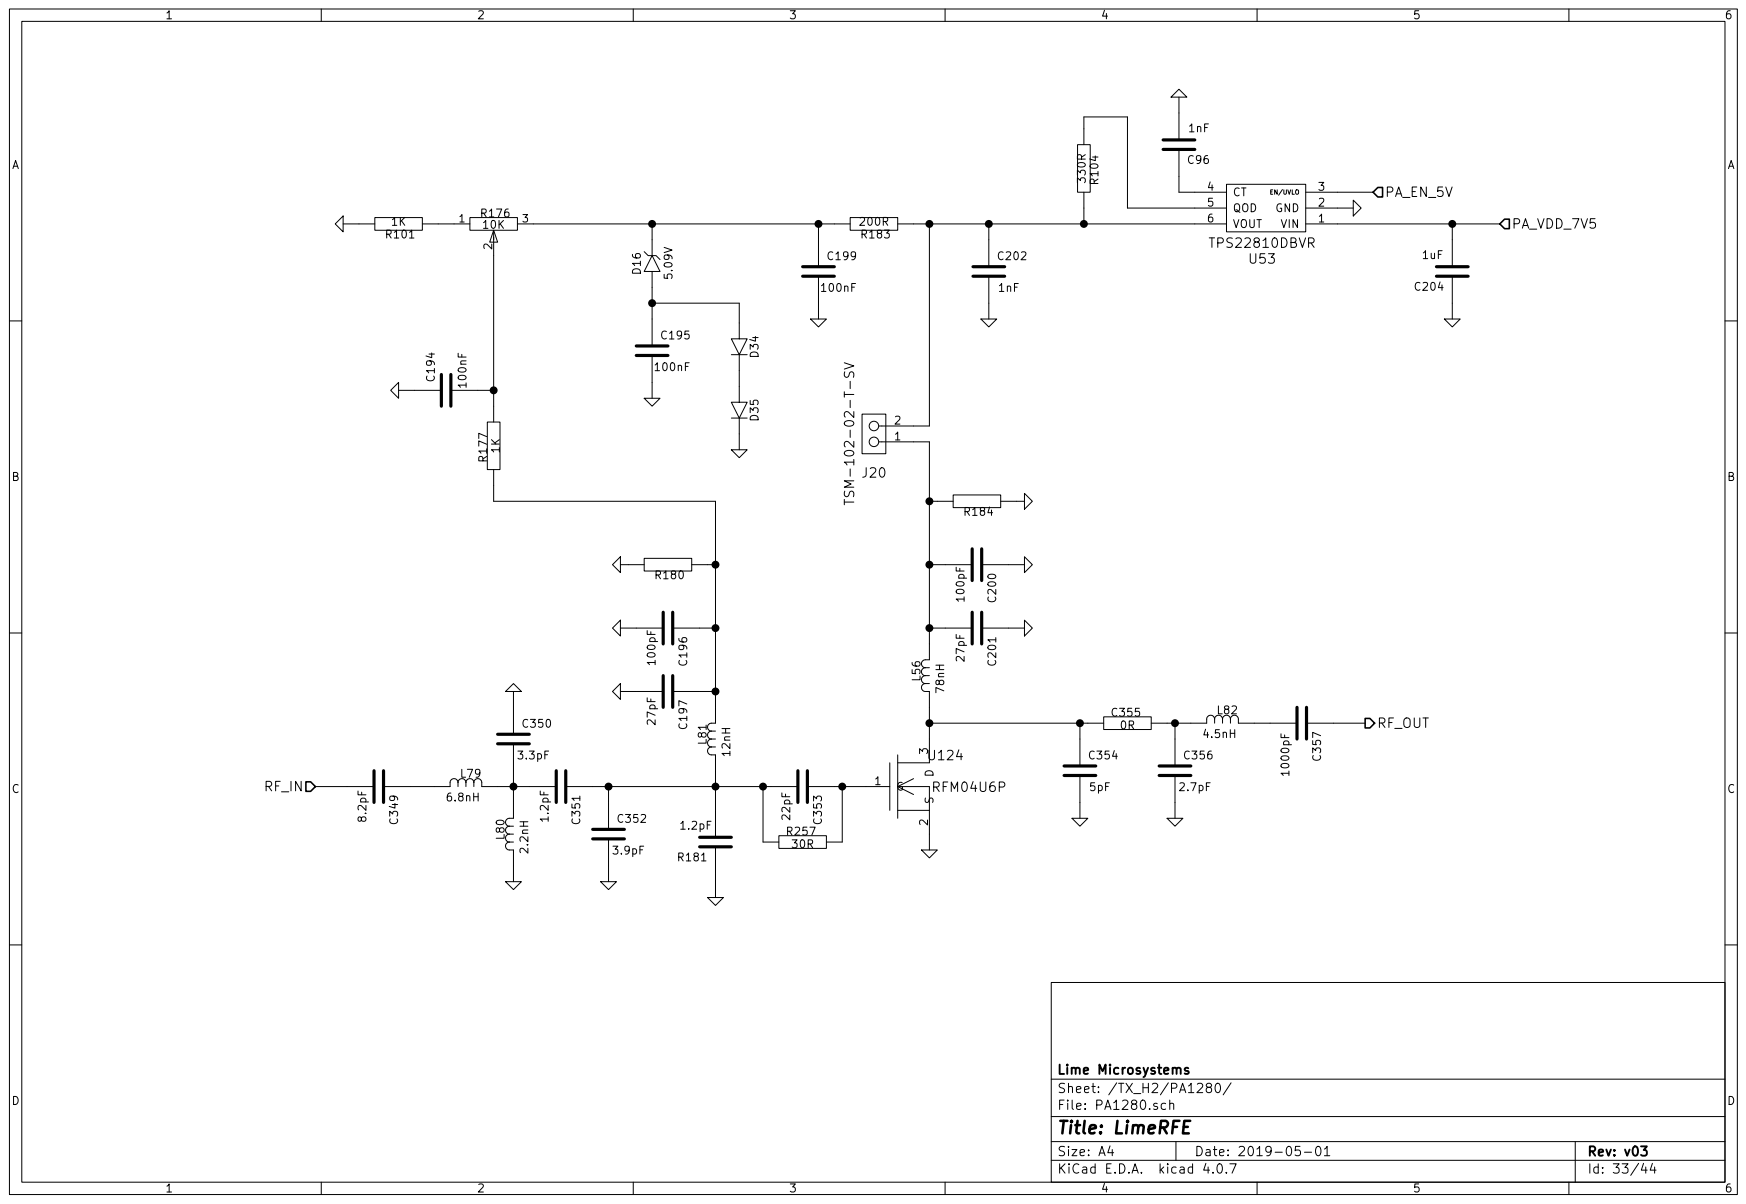
[picture p397: page 33]

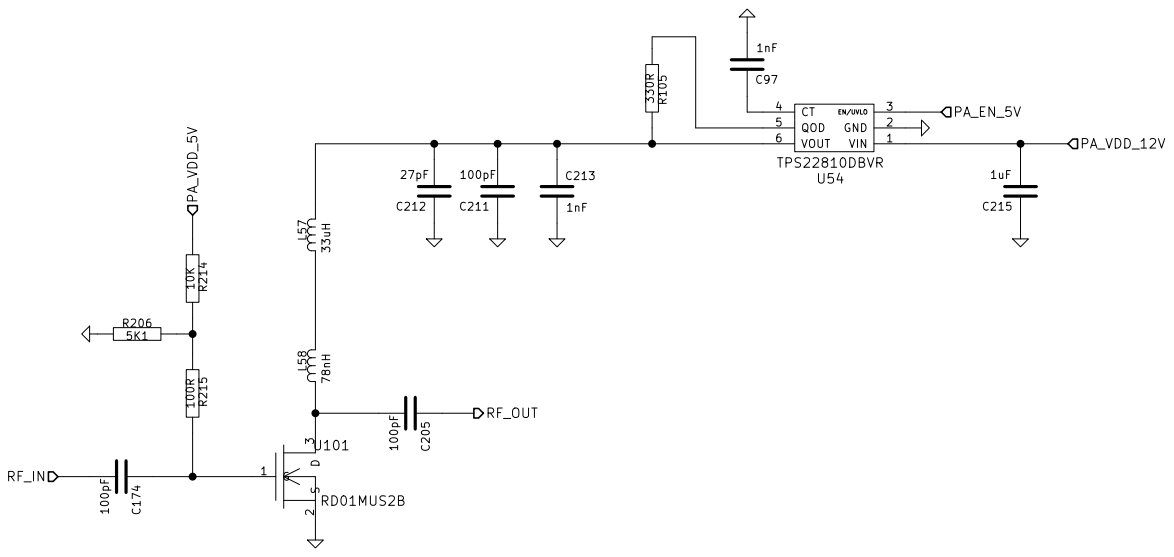
[picture p398: page 34]

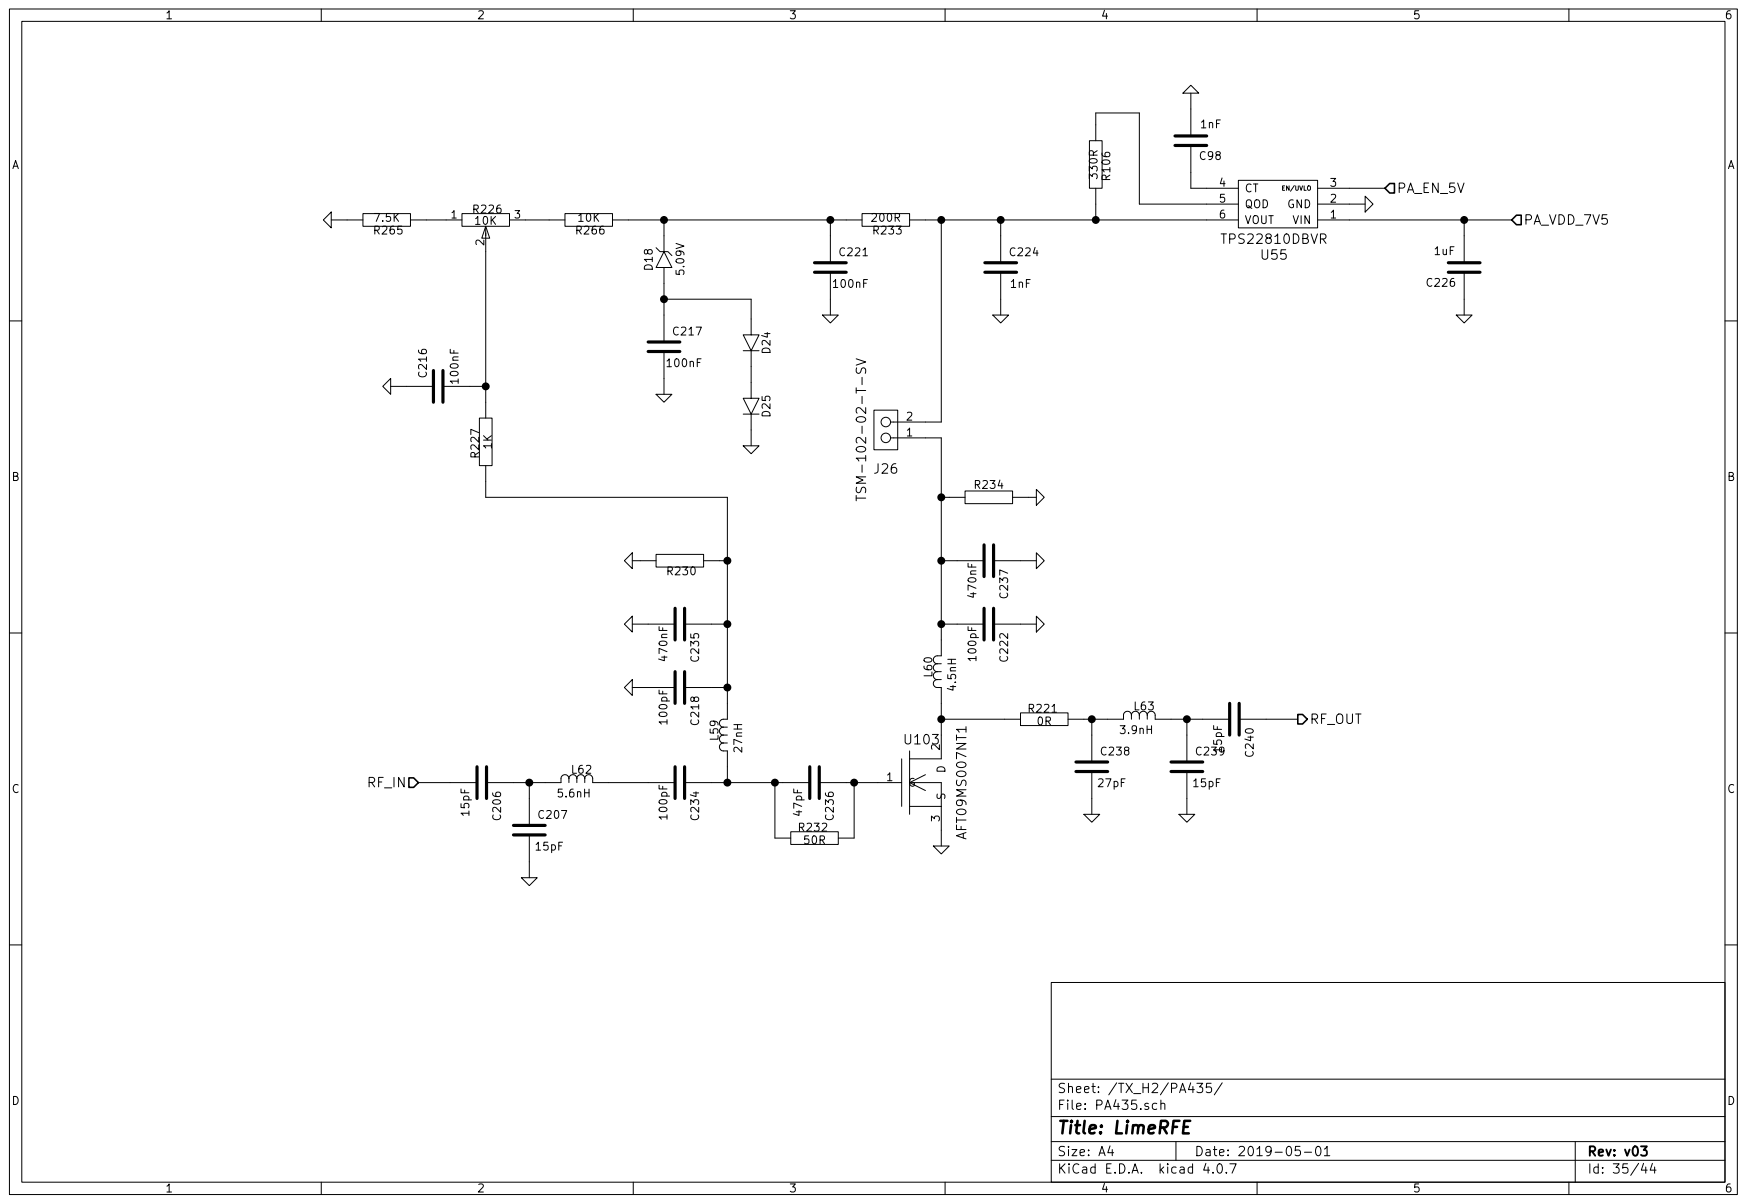
[picture p399: page 35]


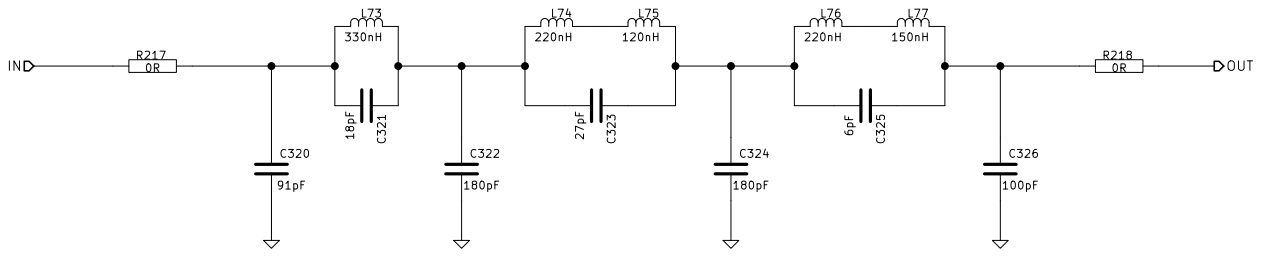
[picture p400: page 37]

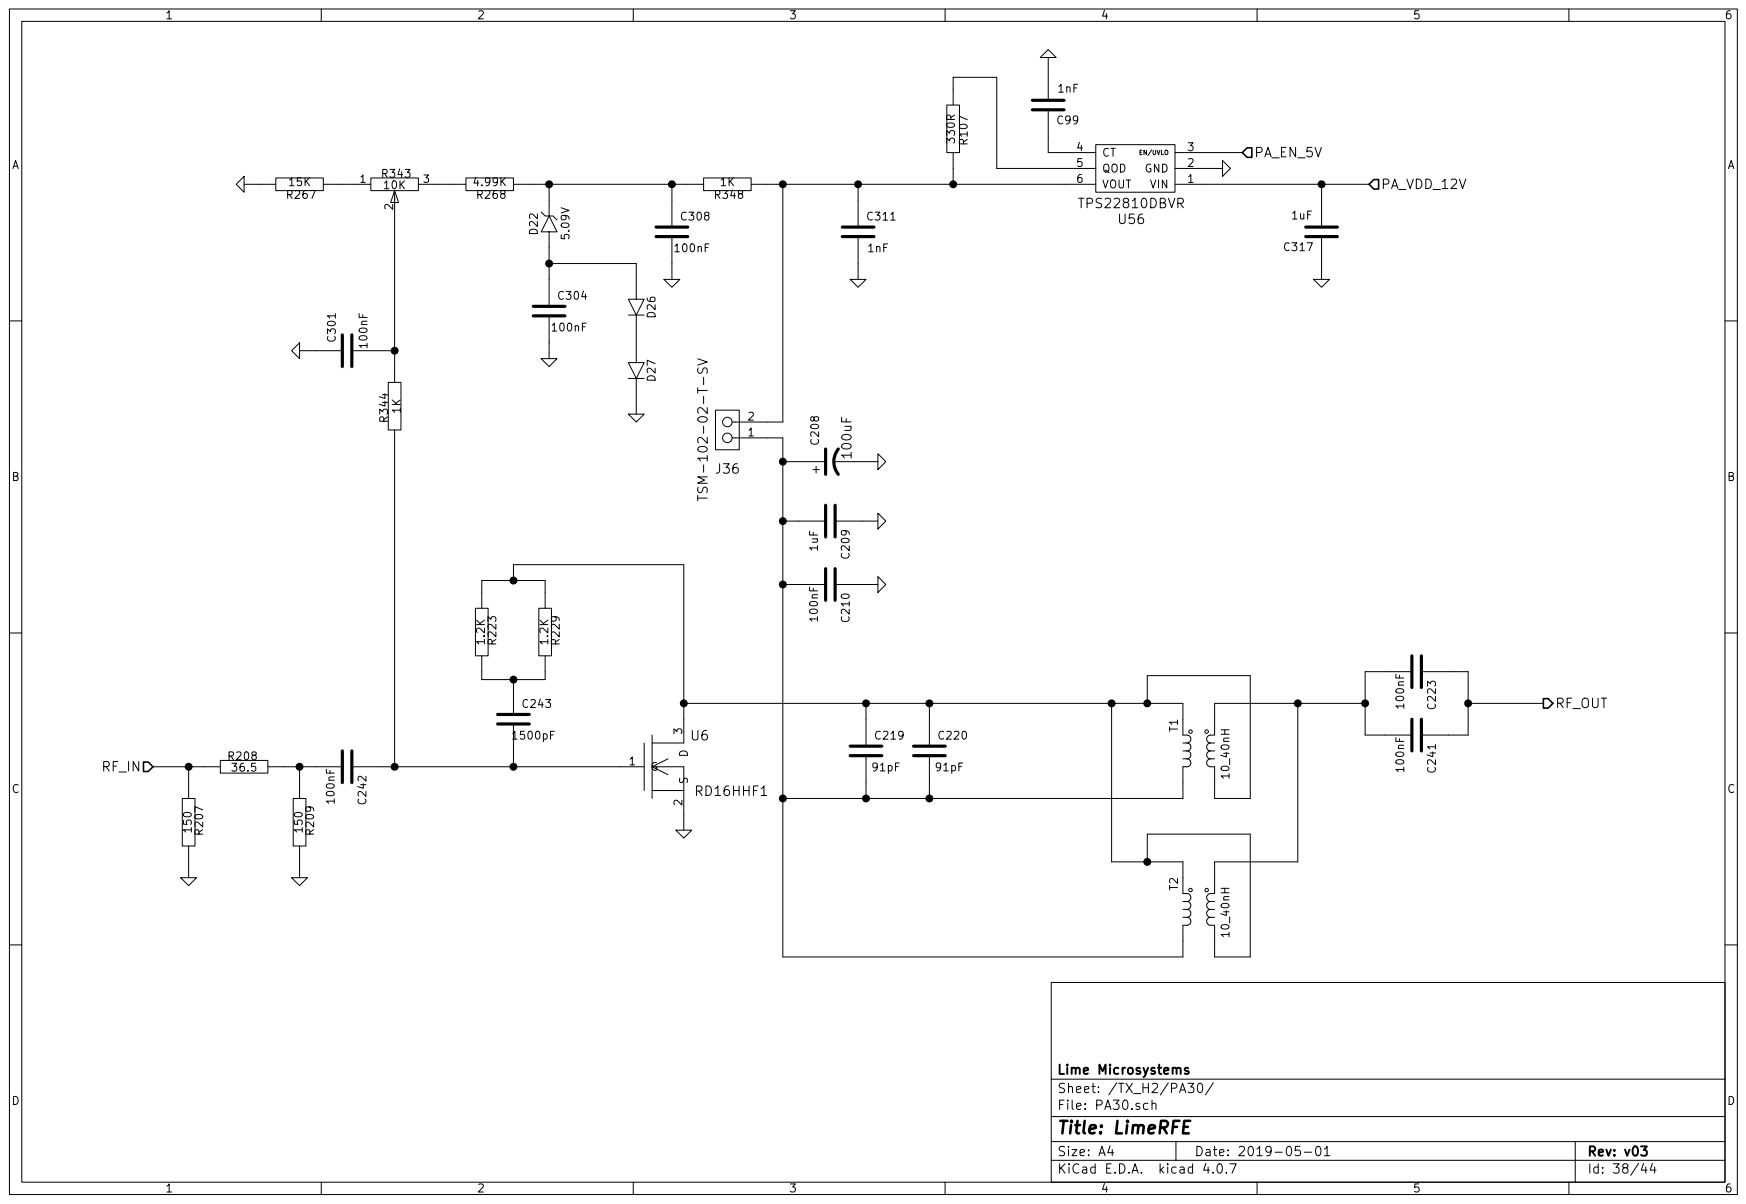
[picture p401: page 38]

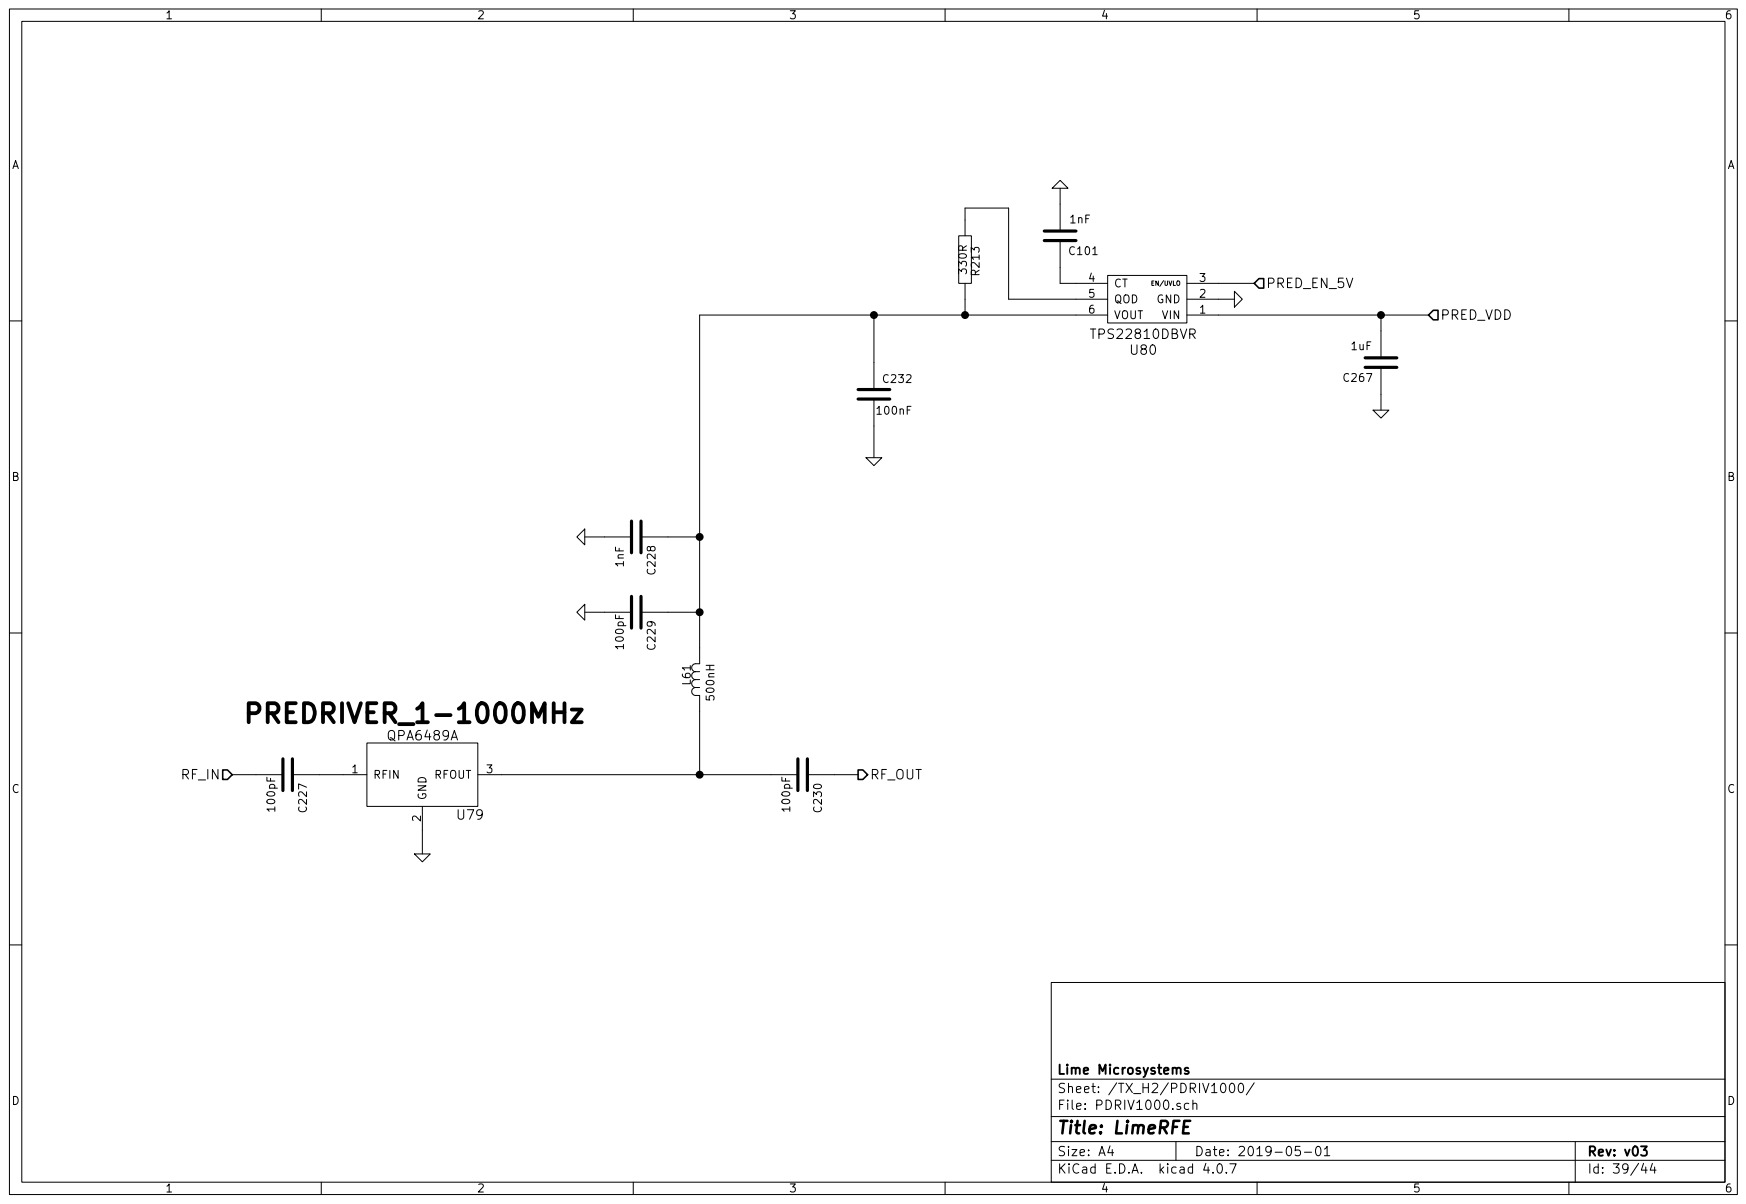
[picture p402: page 39]

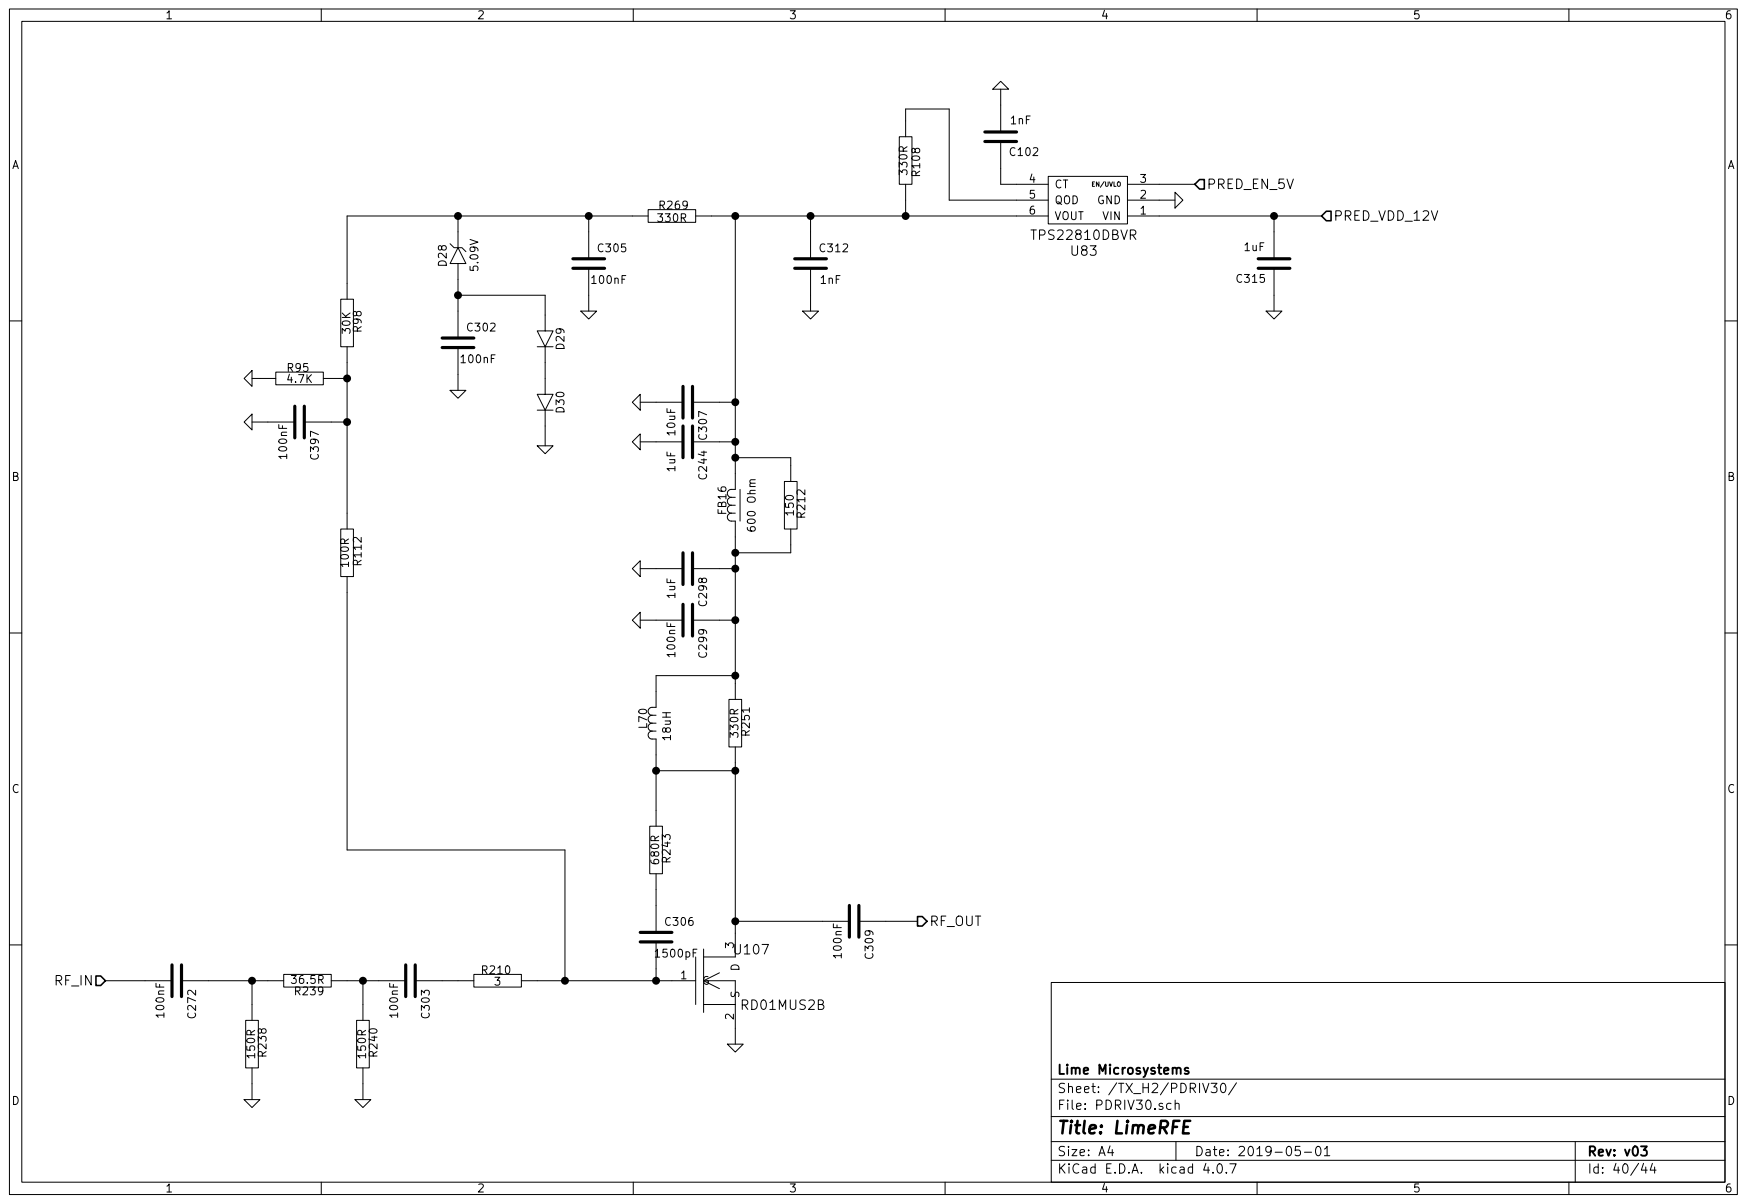
[picture p403: page 40]

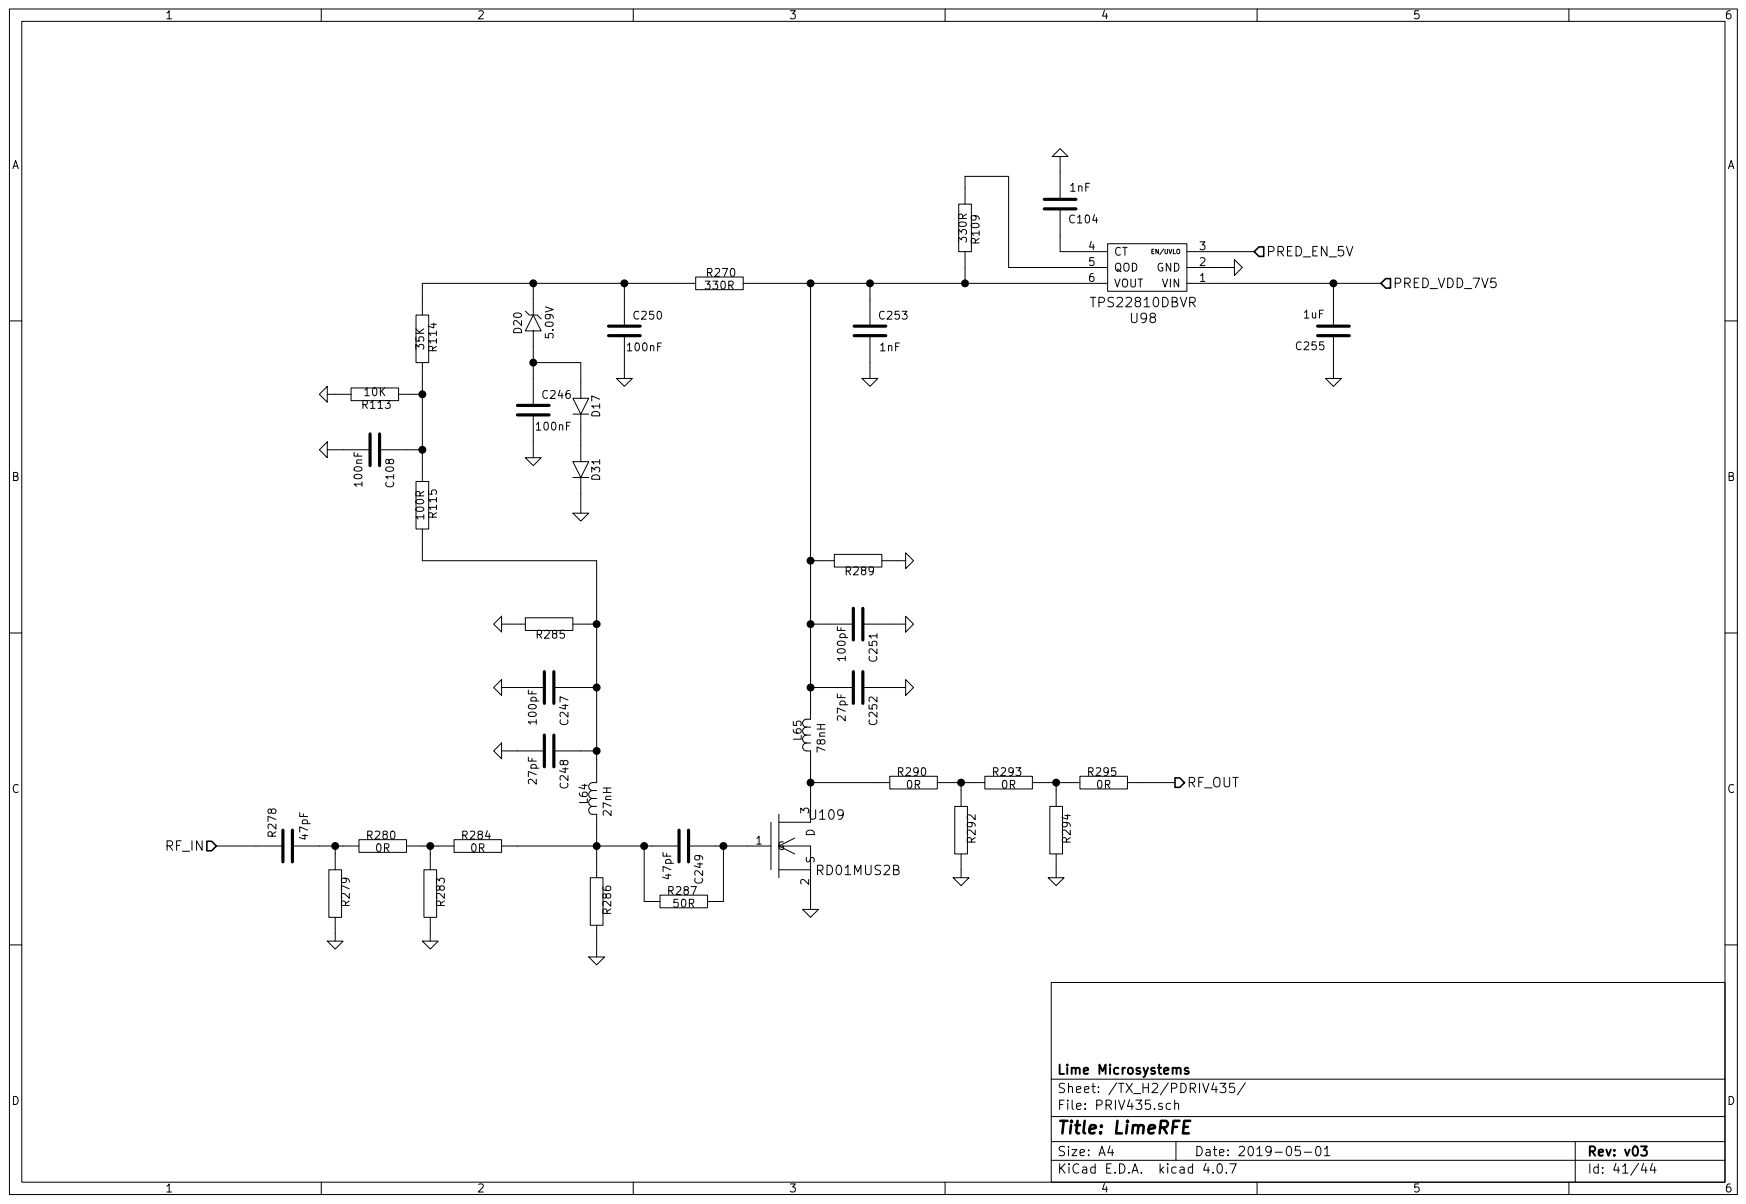
[picture p404: page 41]

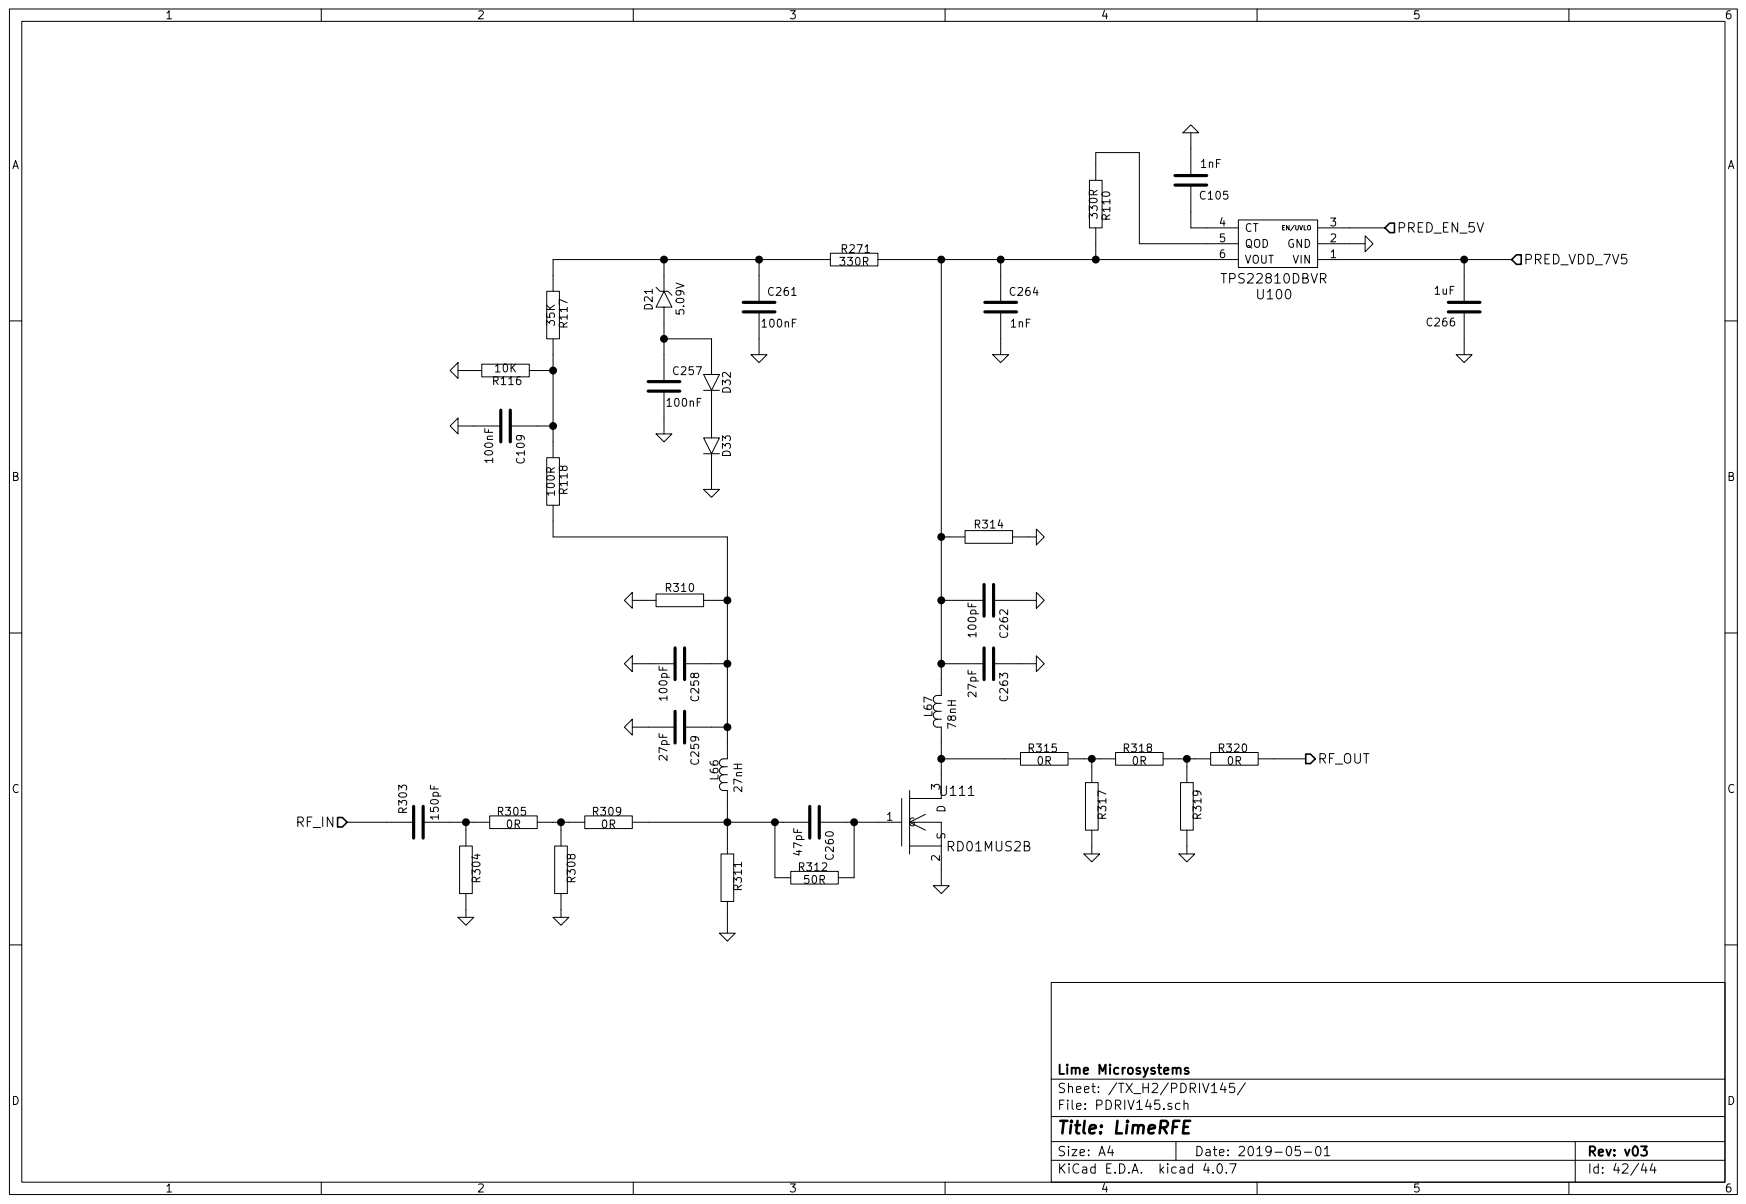
[picture p405: page 42]

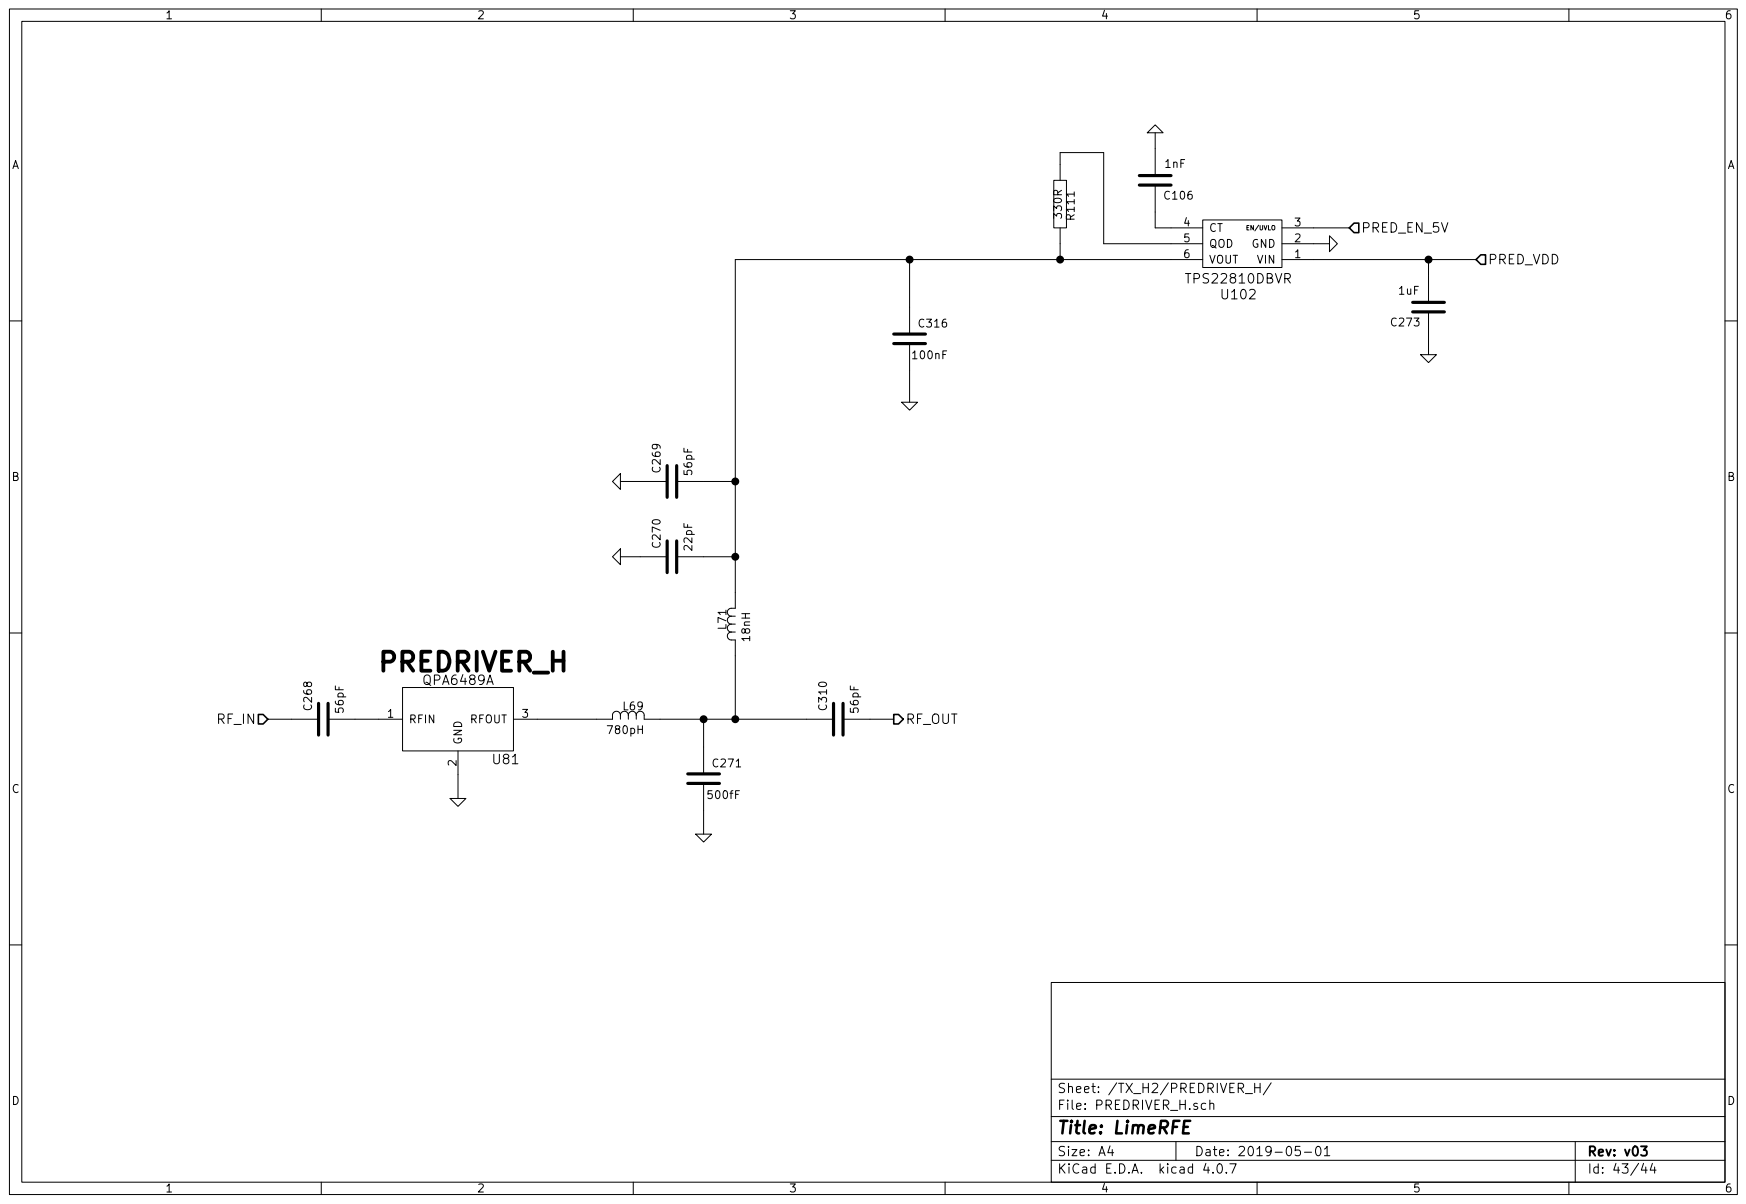
[picture p406: page 43]

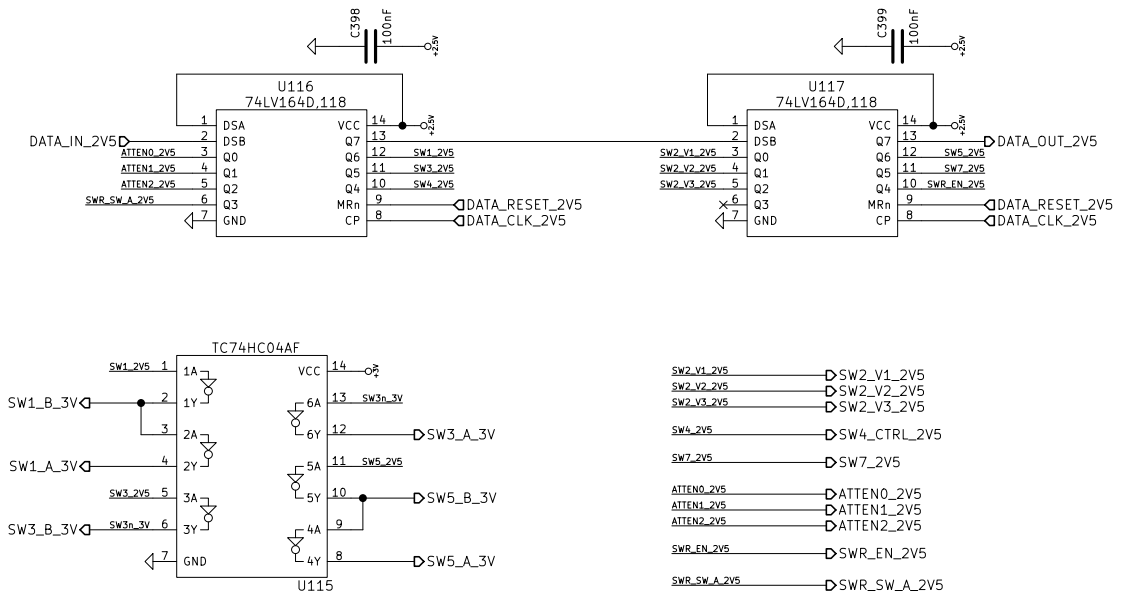
[picture p407: page 44]
