myriadrf/LimeRFE/archived/1v2/docs/LimeRFE_1v2_Schematic.pdf

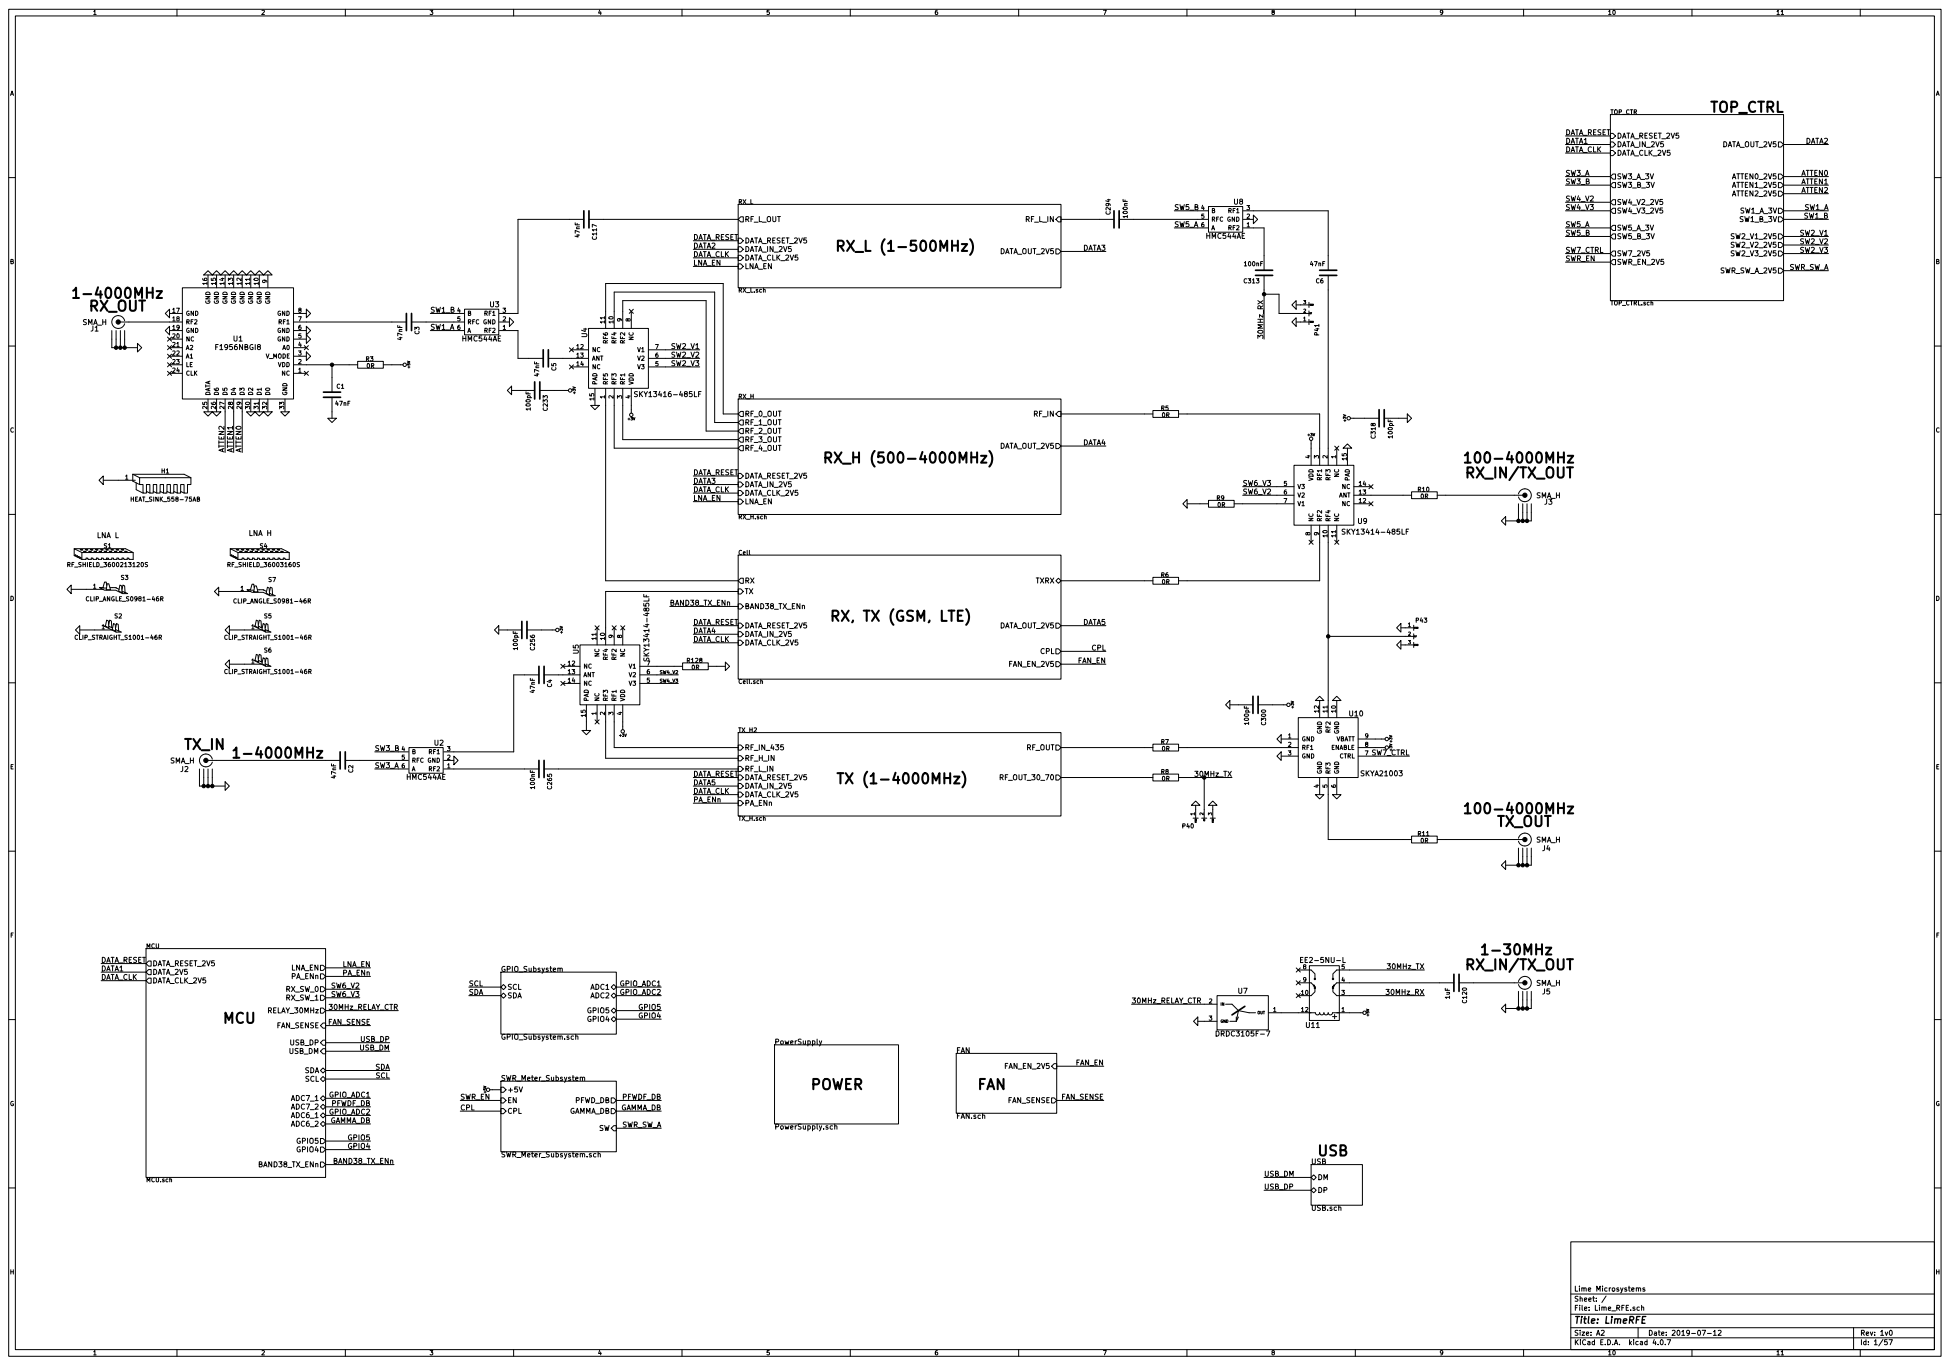
[picture p408: page 1]

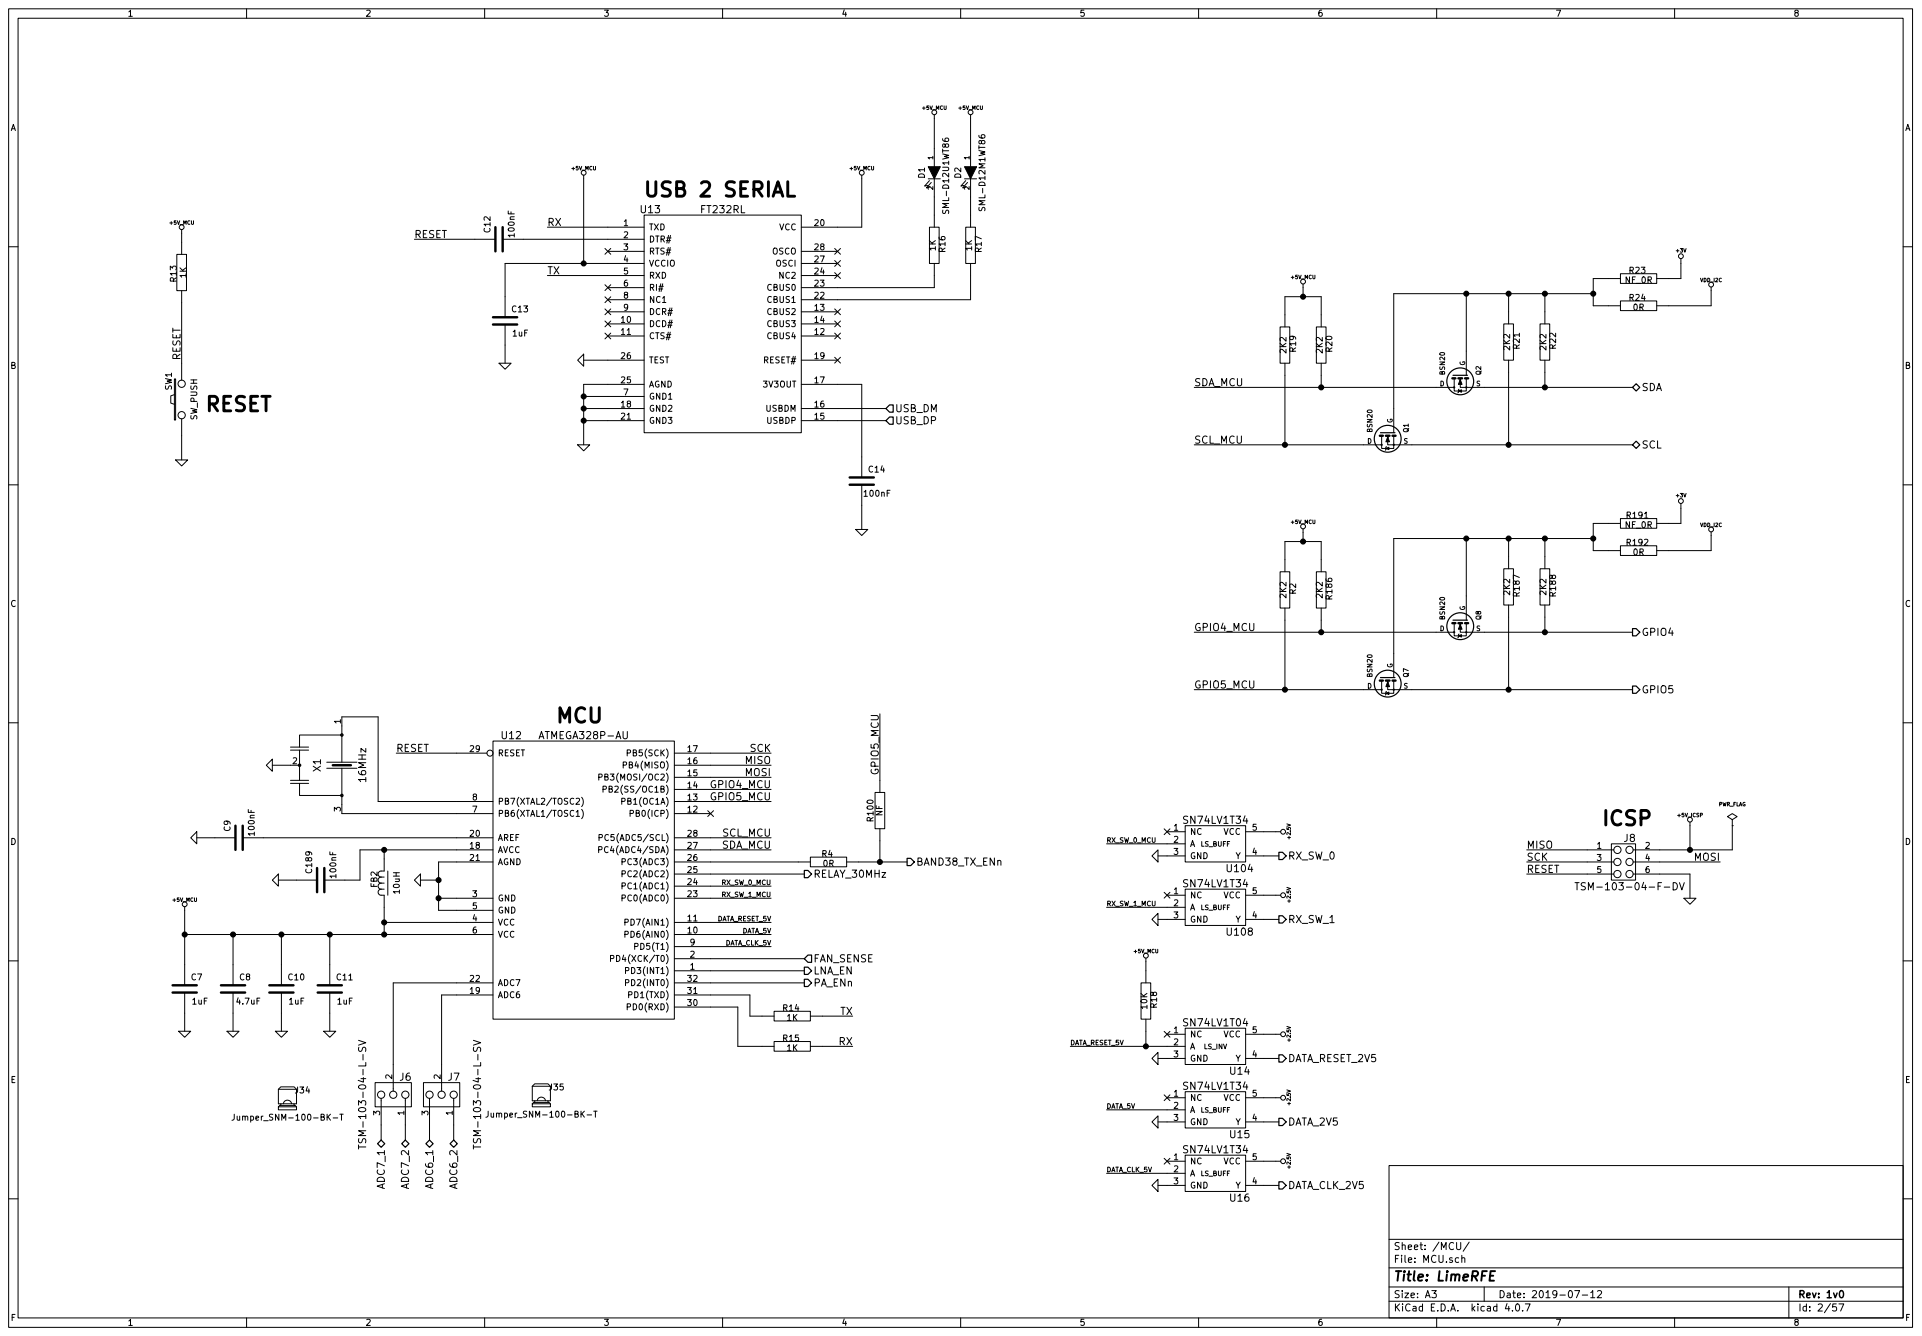
[picture p409: page 2]

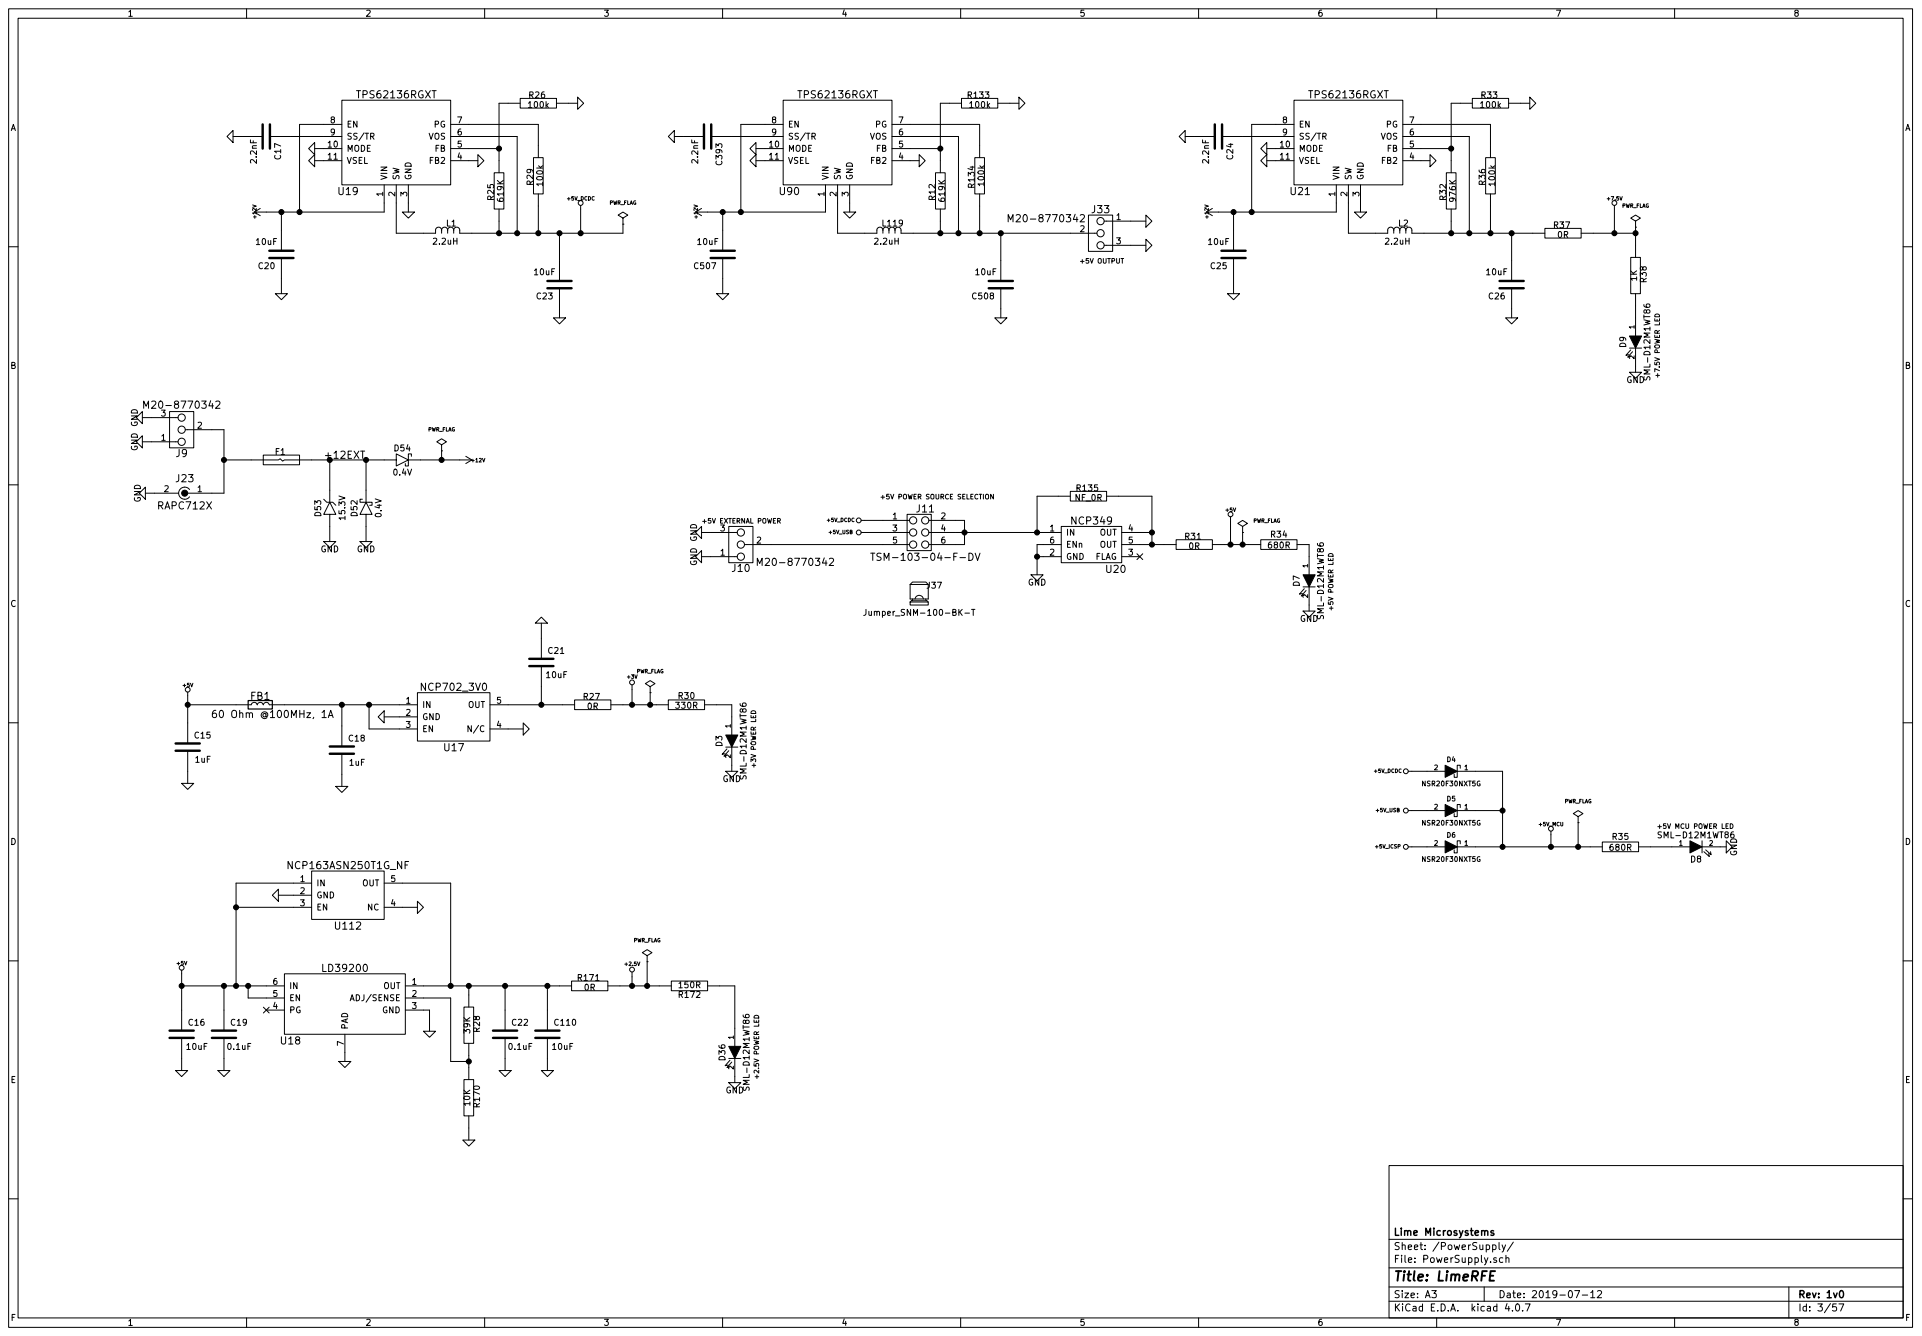
[picture p410: page 3]

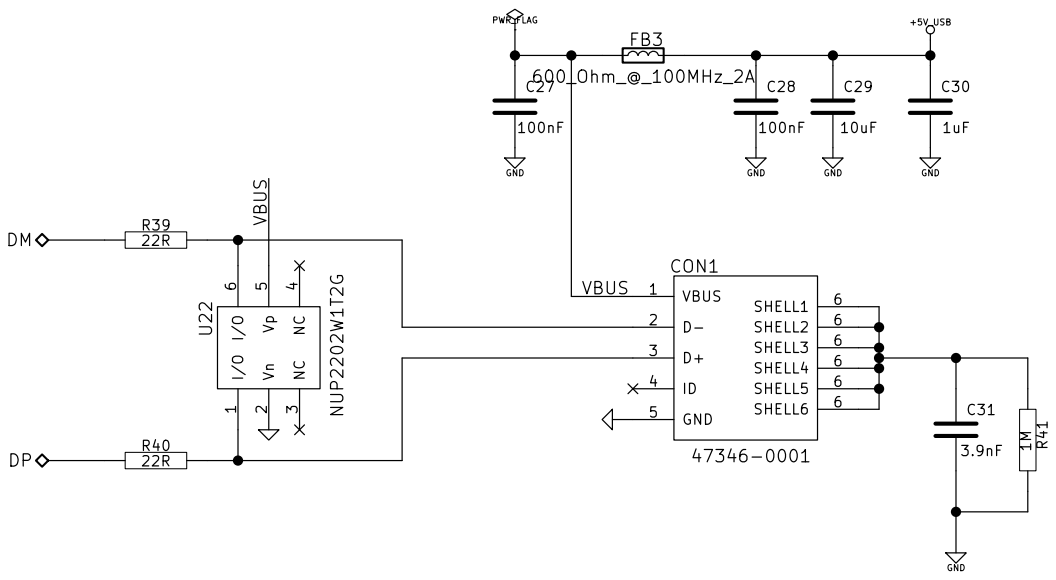
[picture p411: page 4]

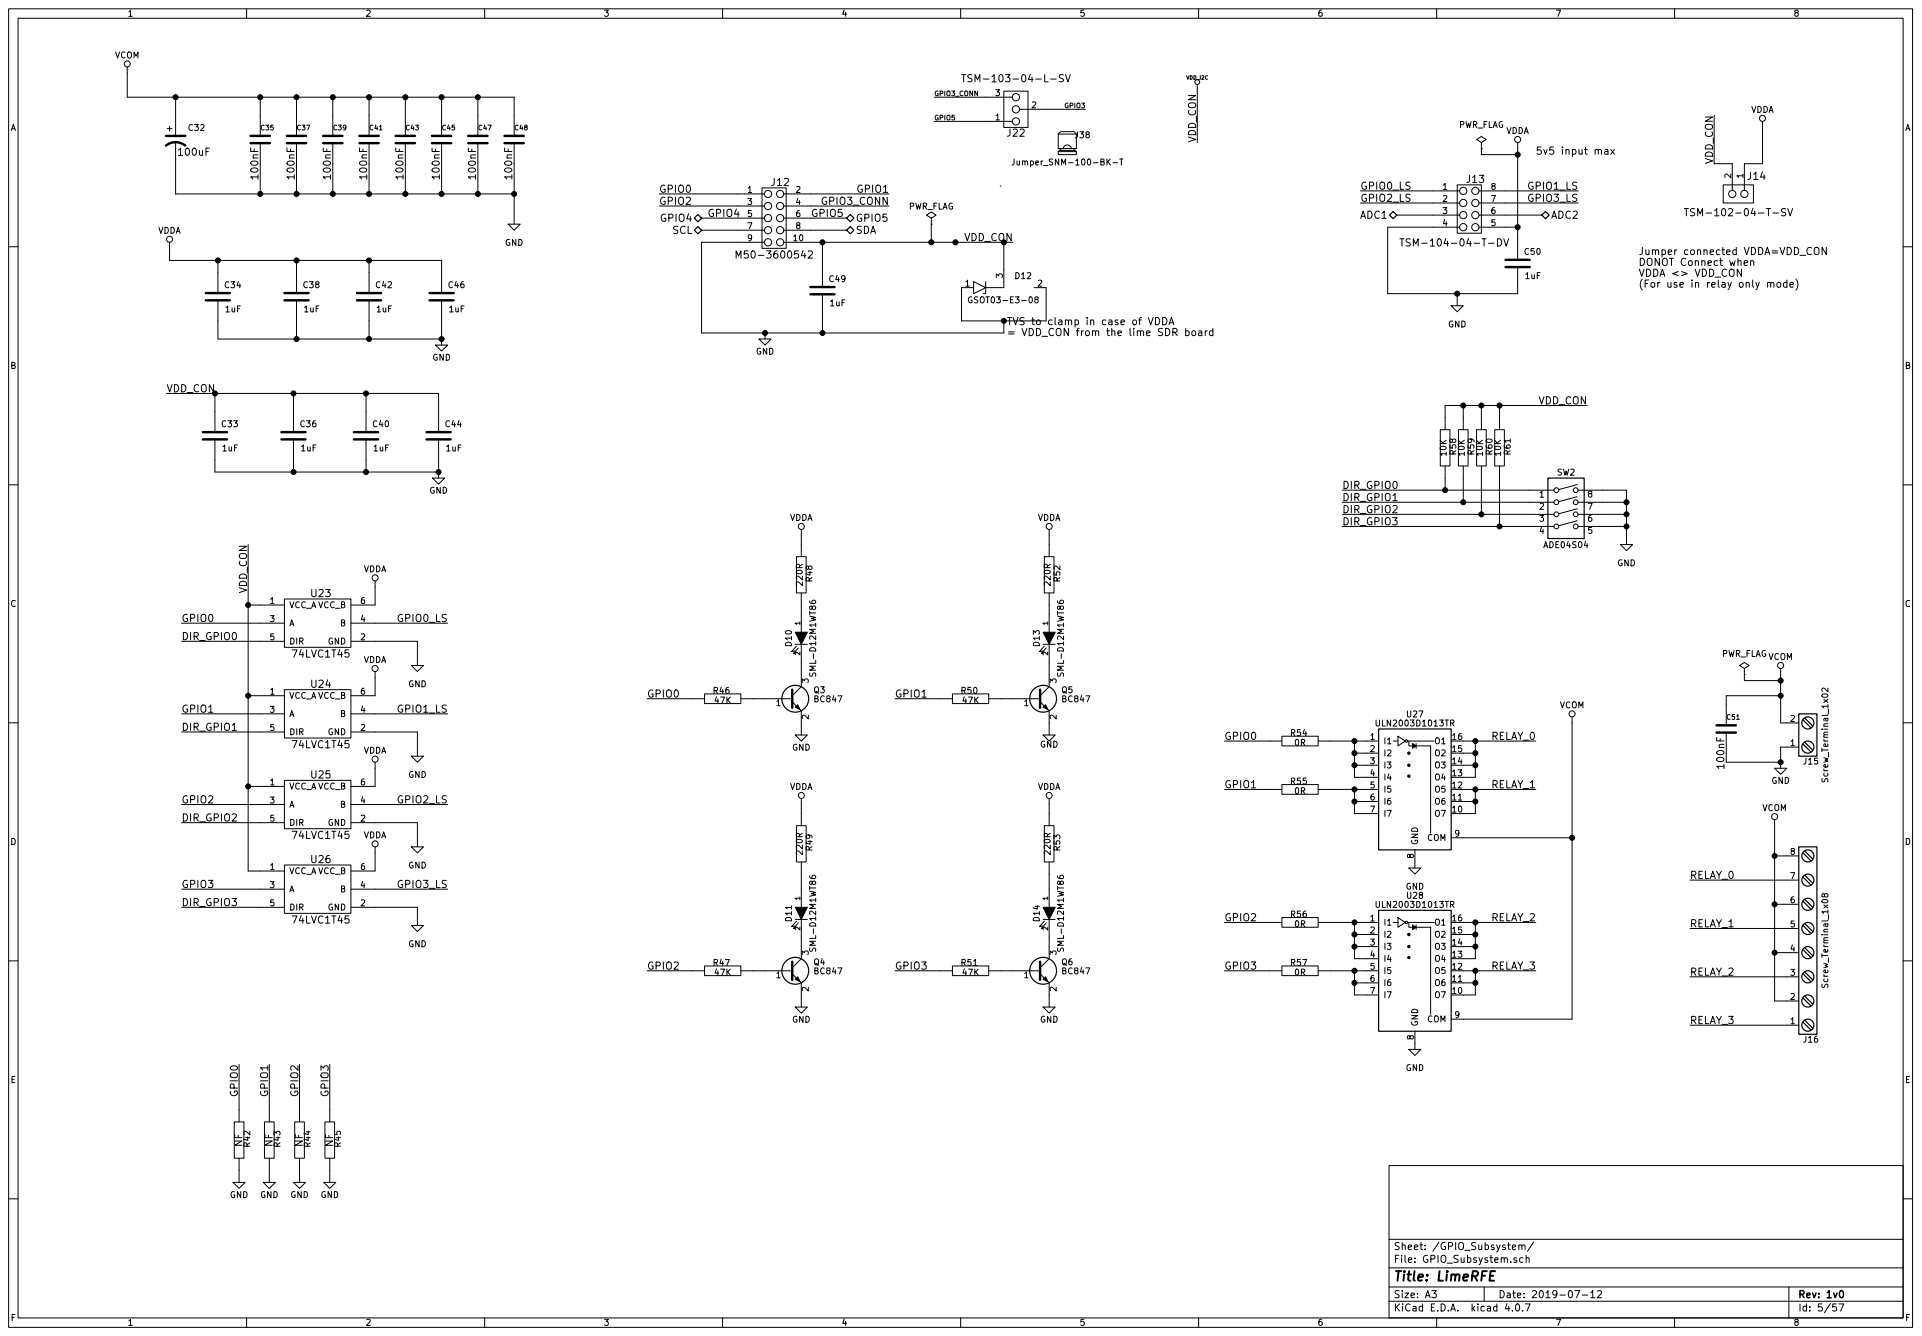
[picture p412: page 5]

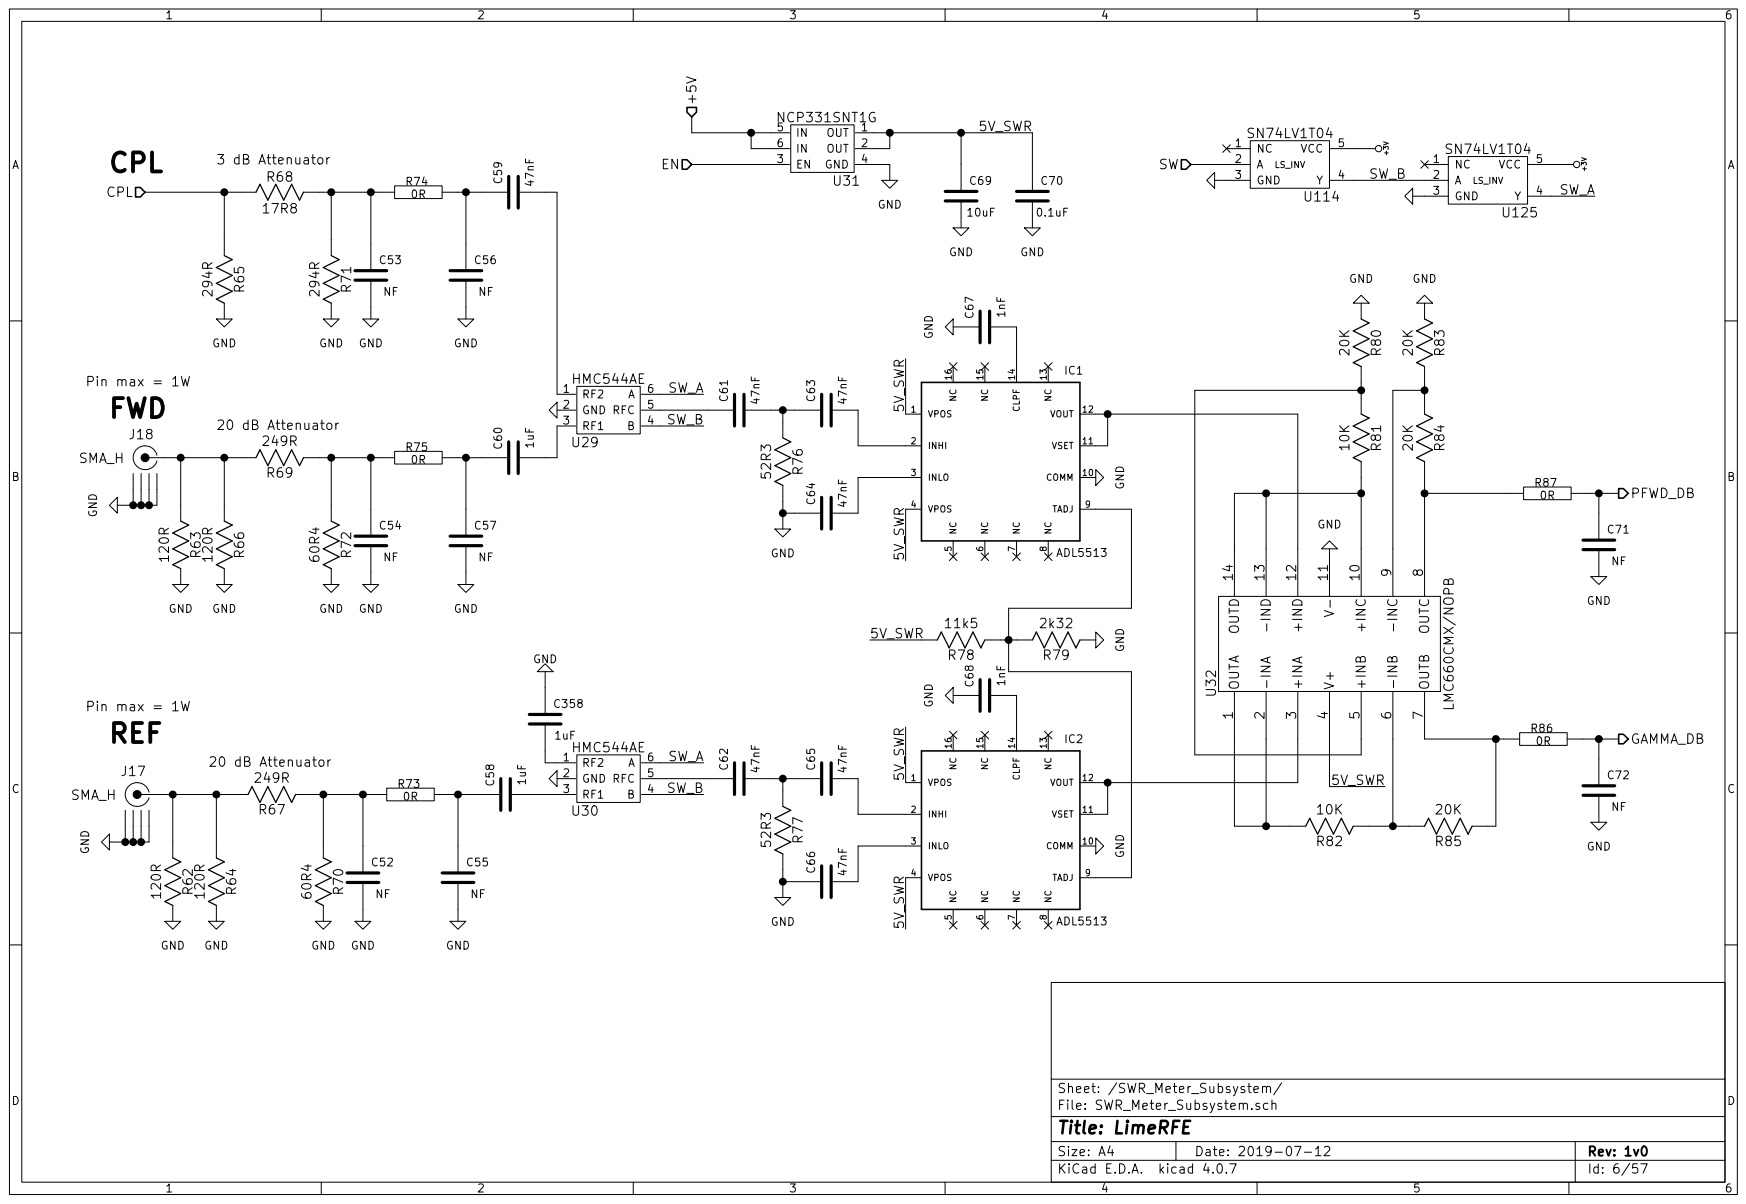
[picture p413: page 6]

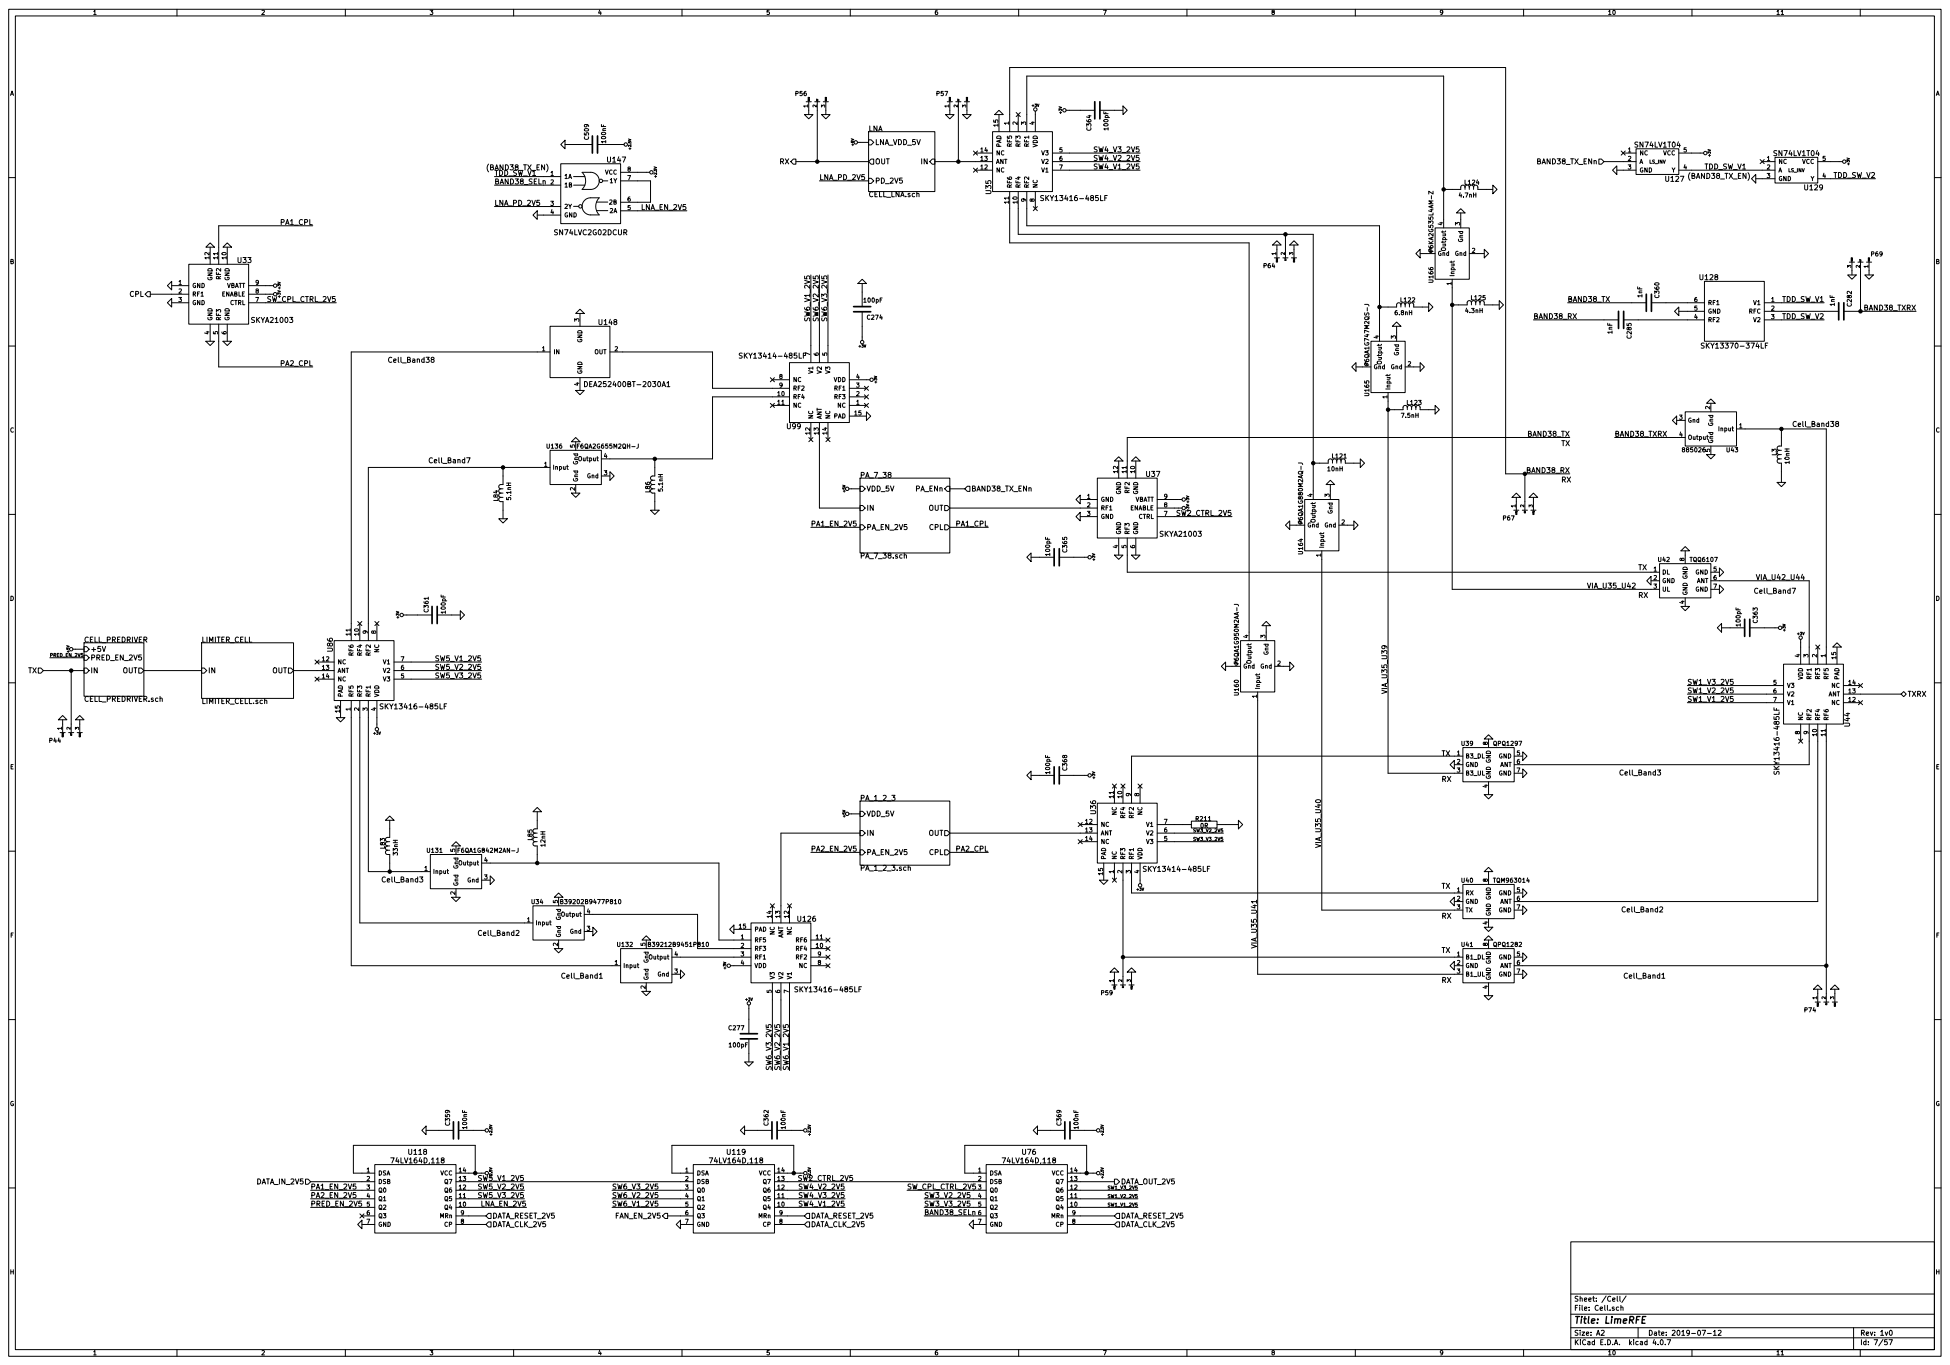
[picture p414: page 7]


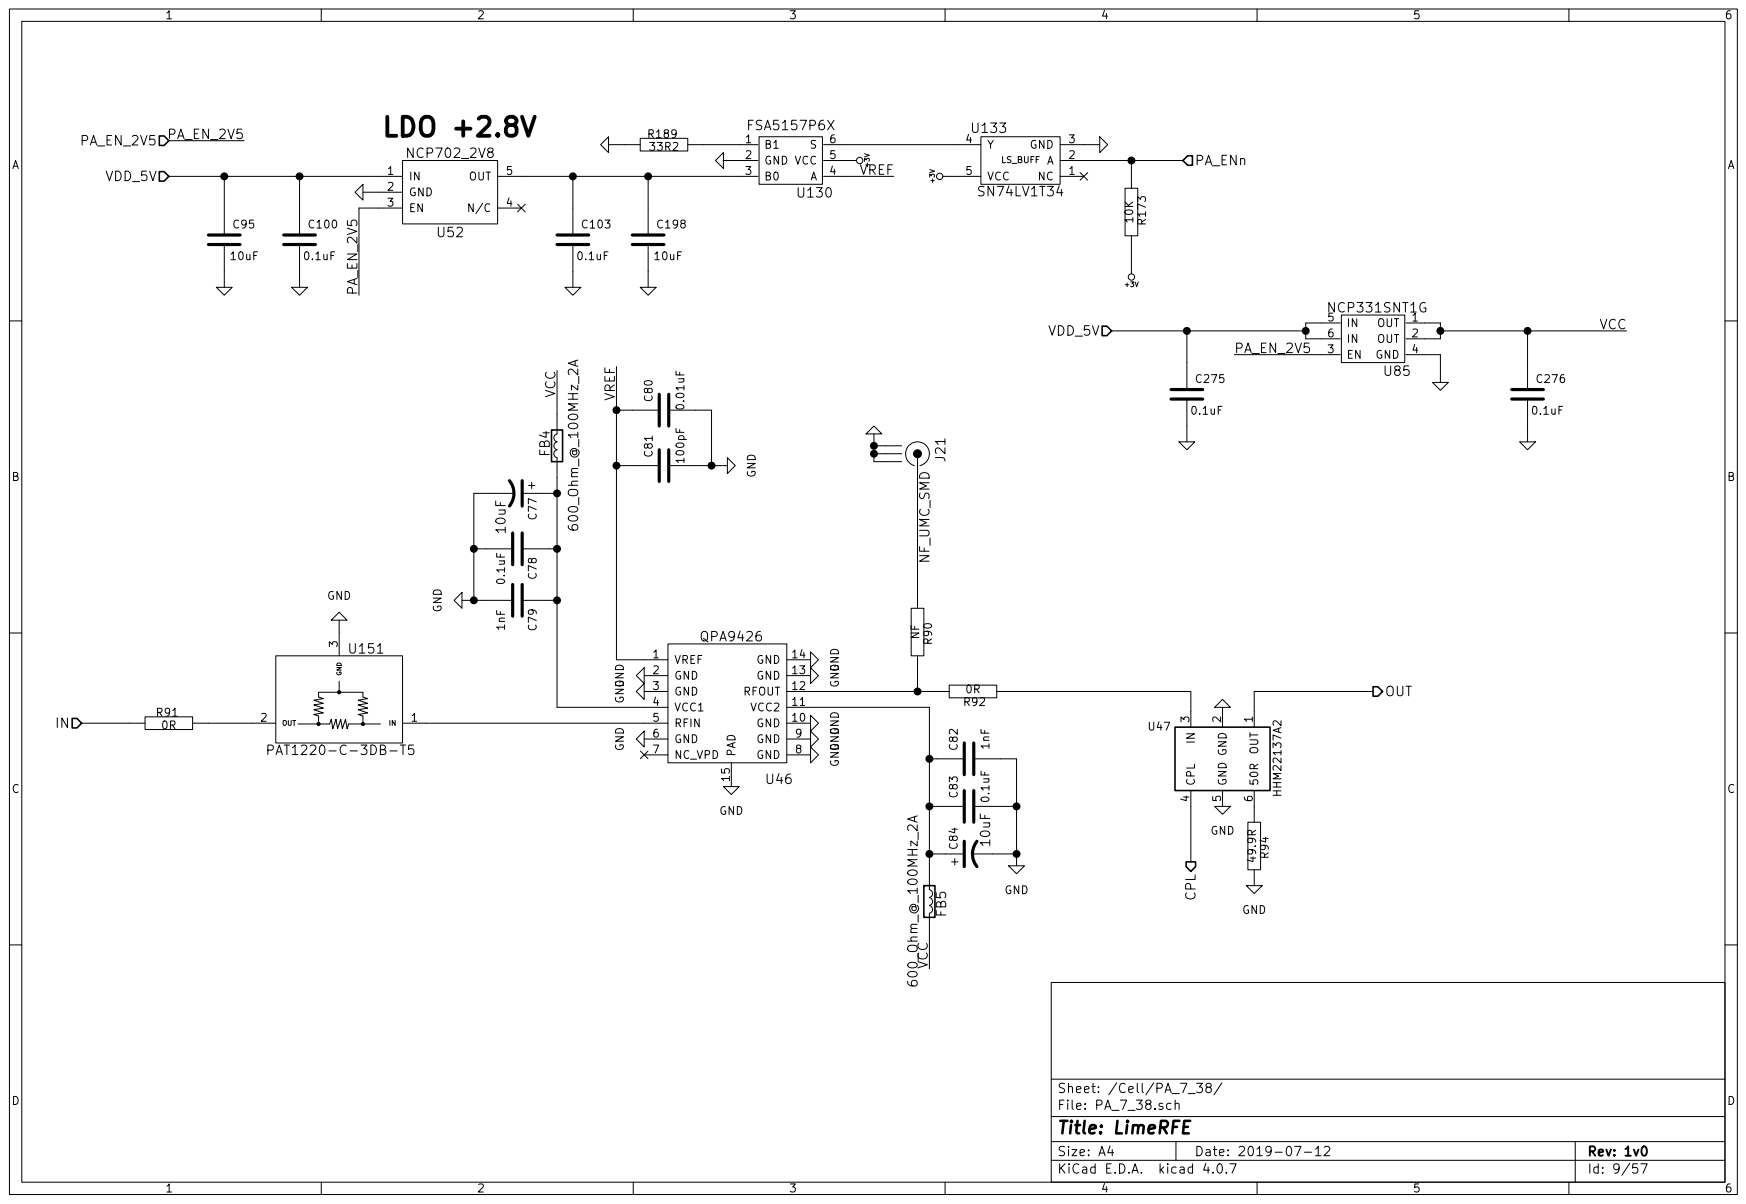
[picture p415: page 9]

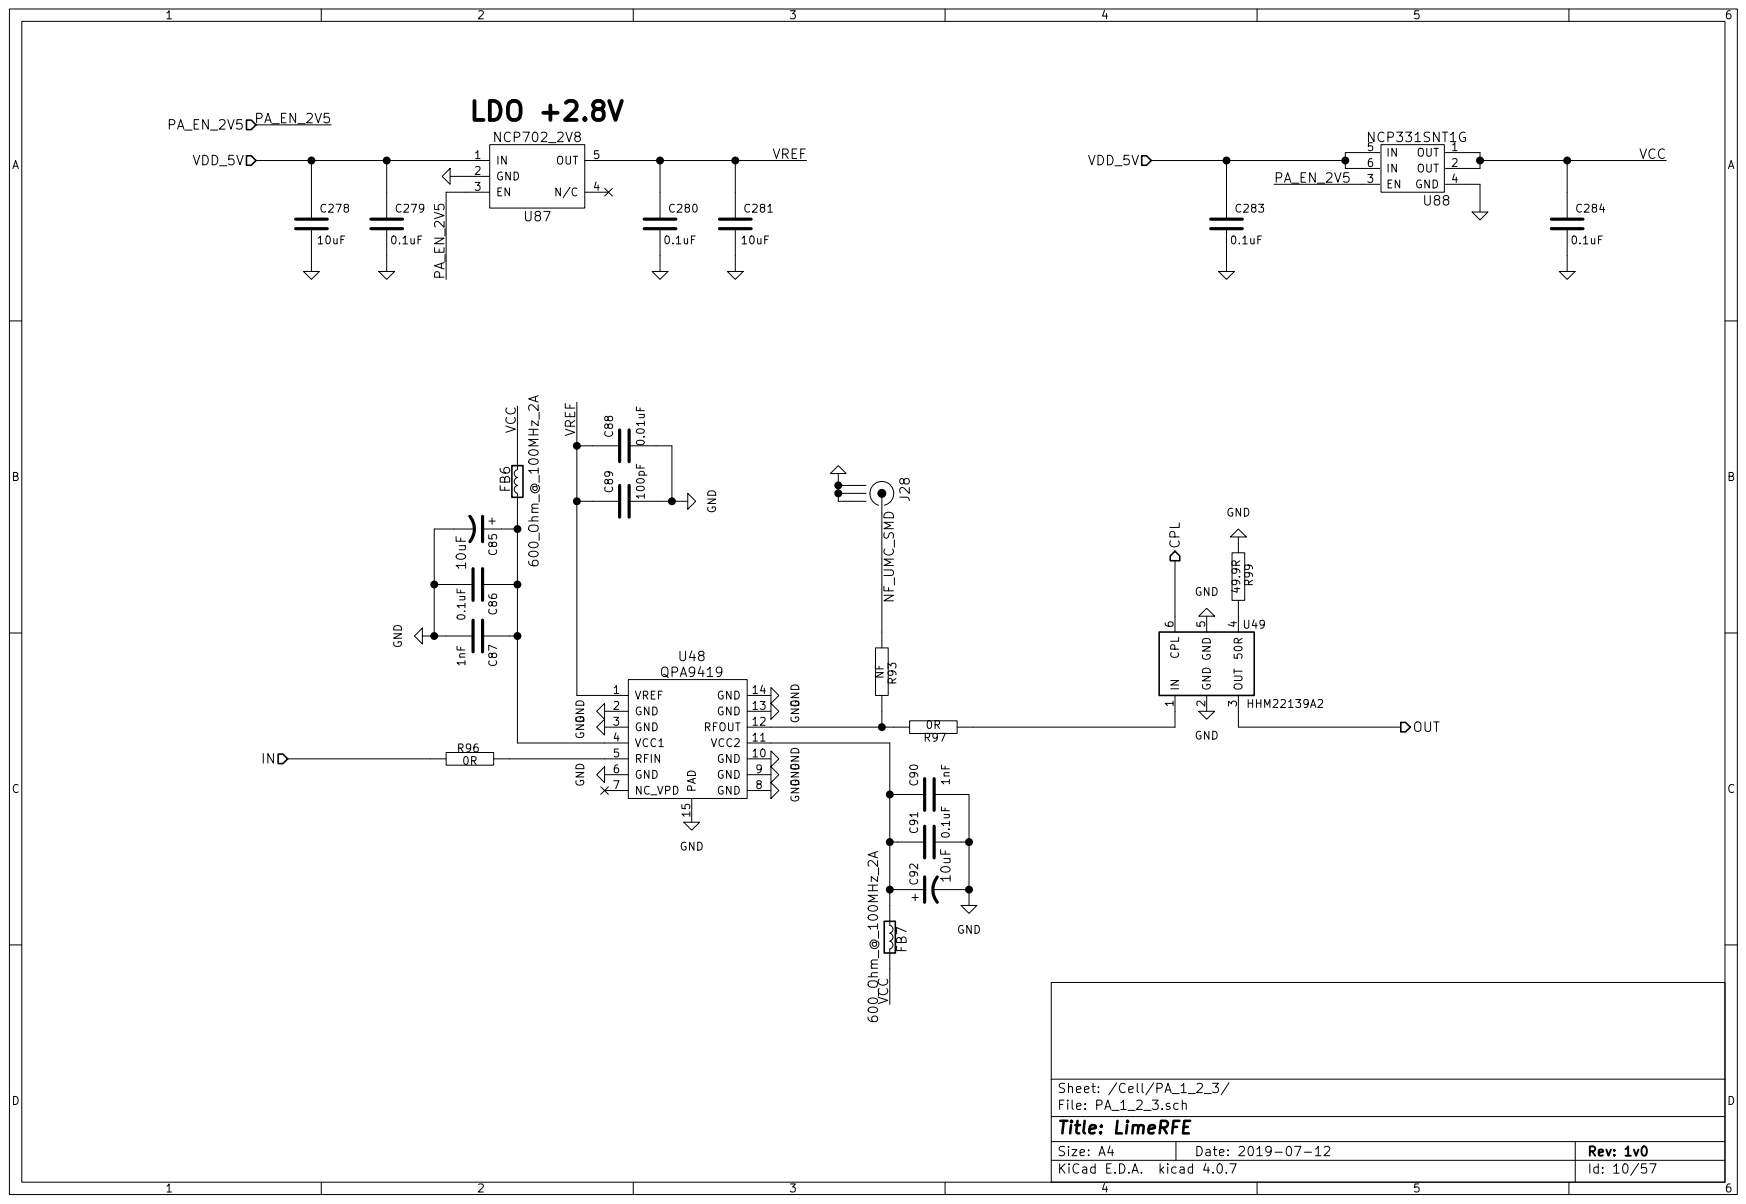
[picture p416: page 10]


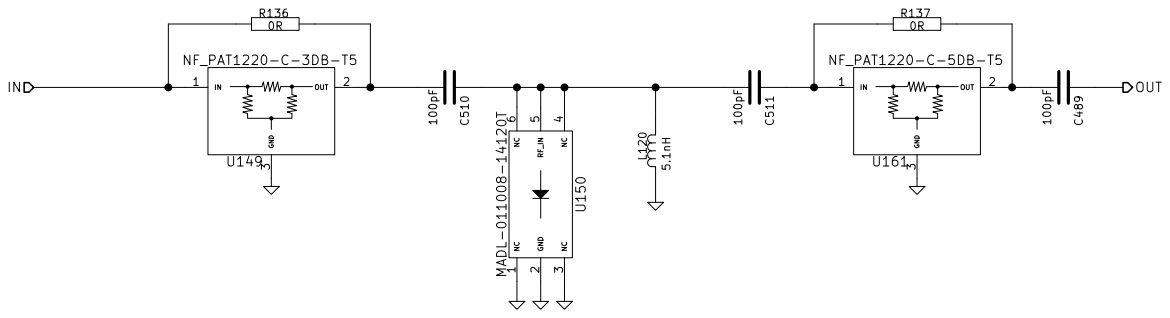
[picture p417: page 12]

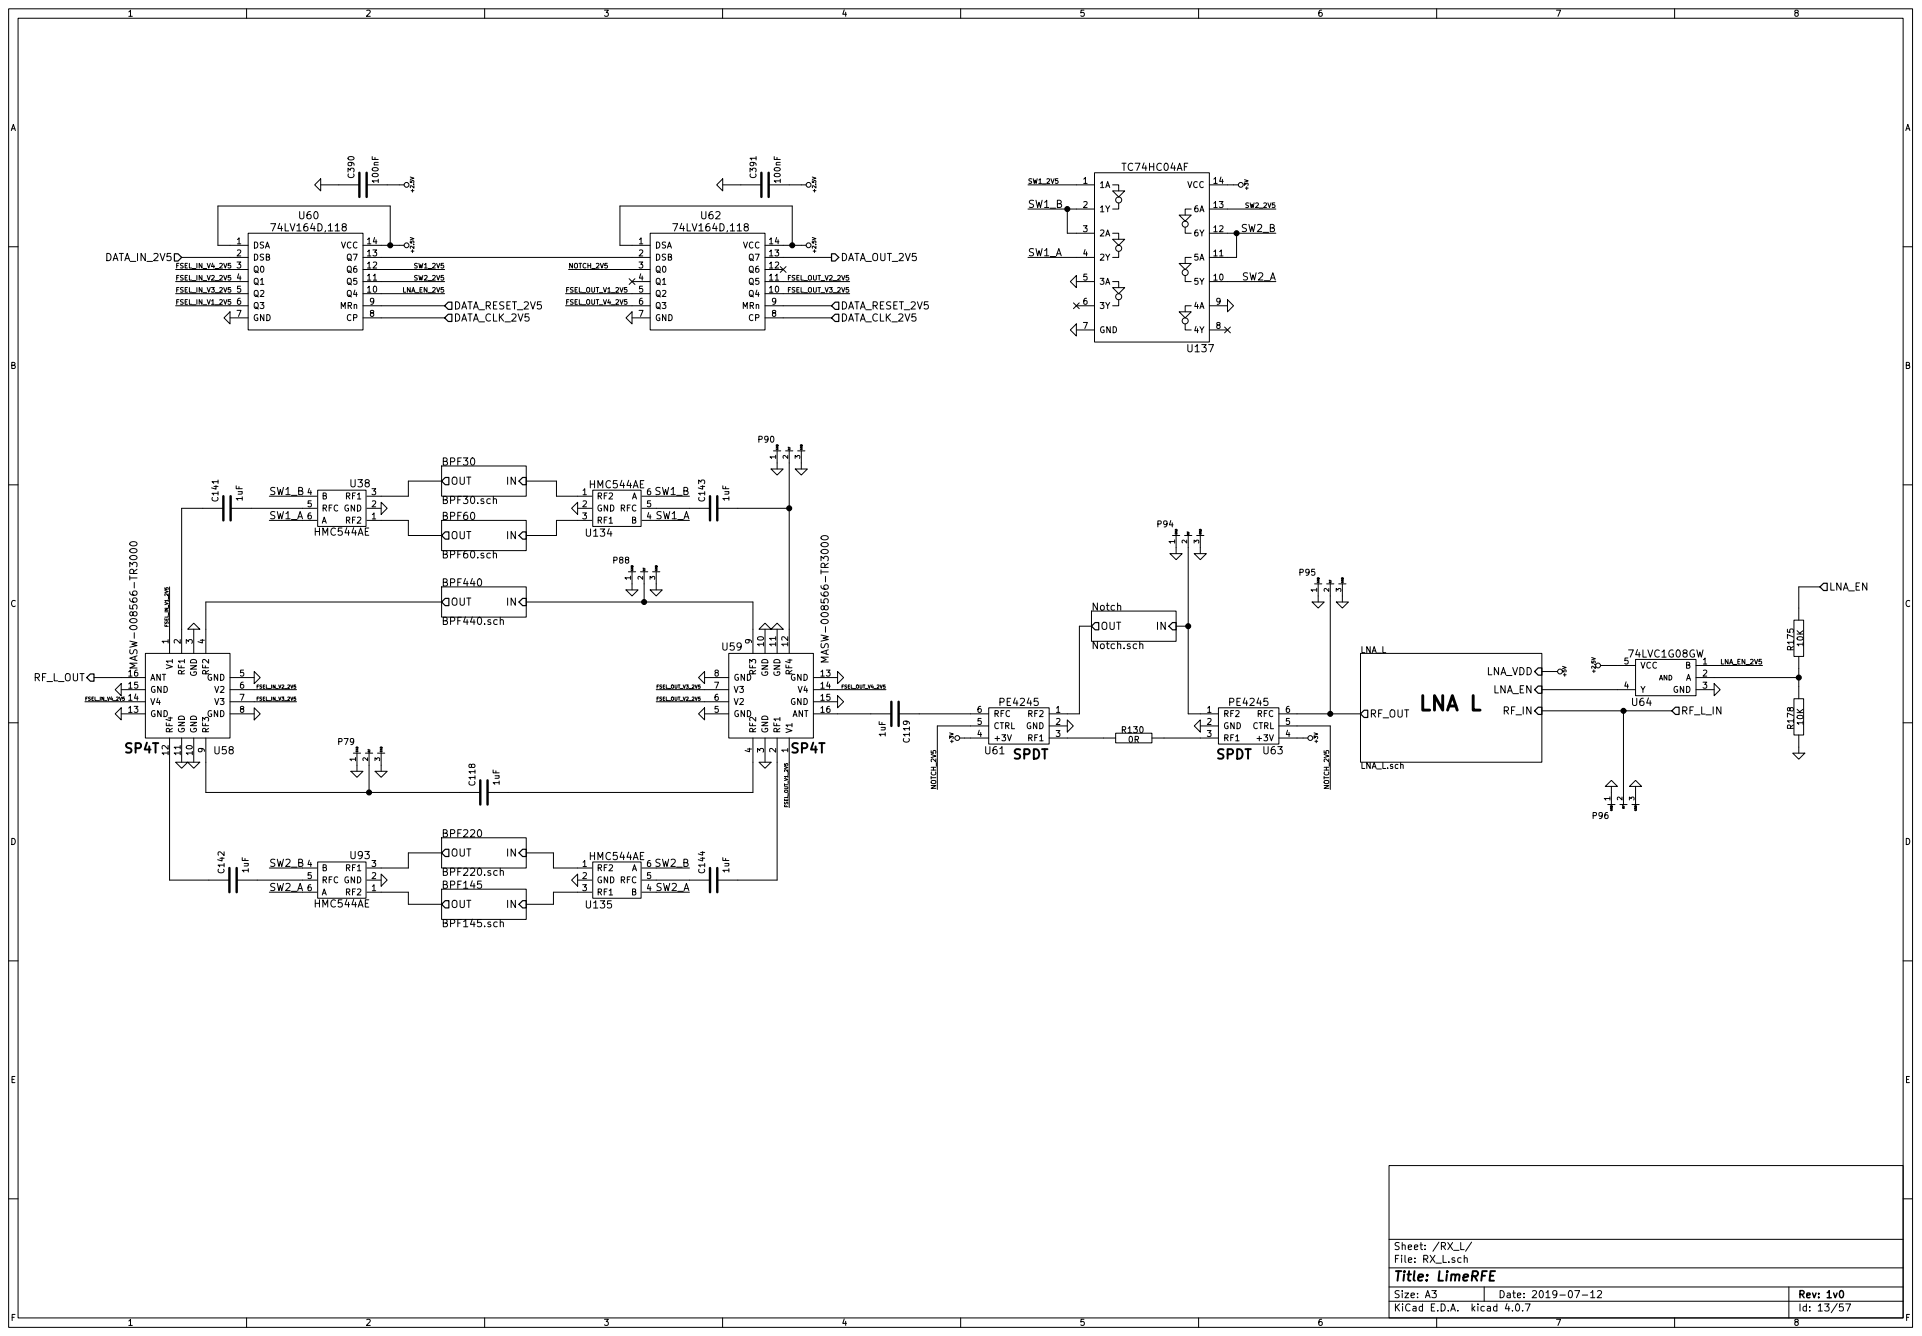
[picture p418: page 13]

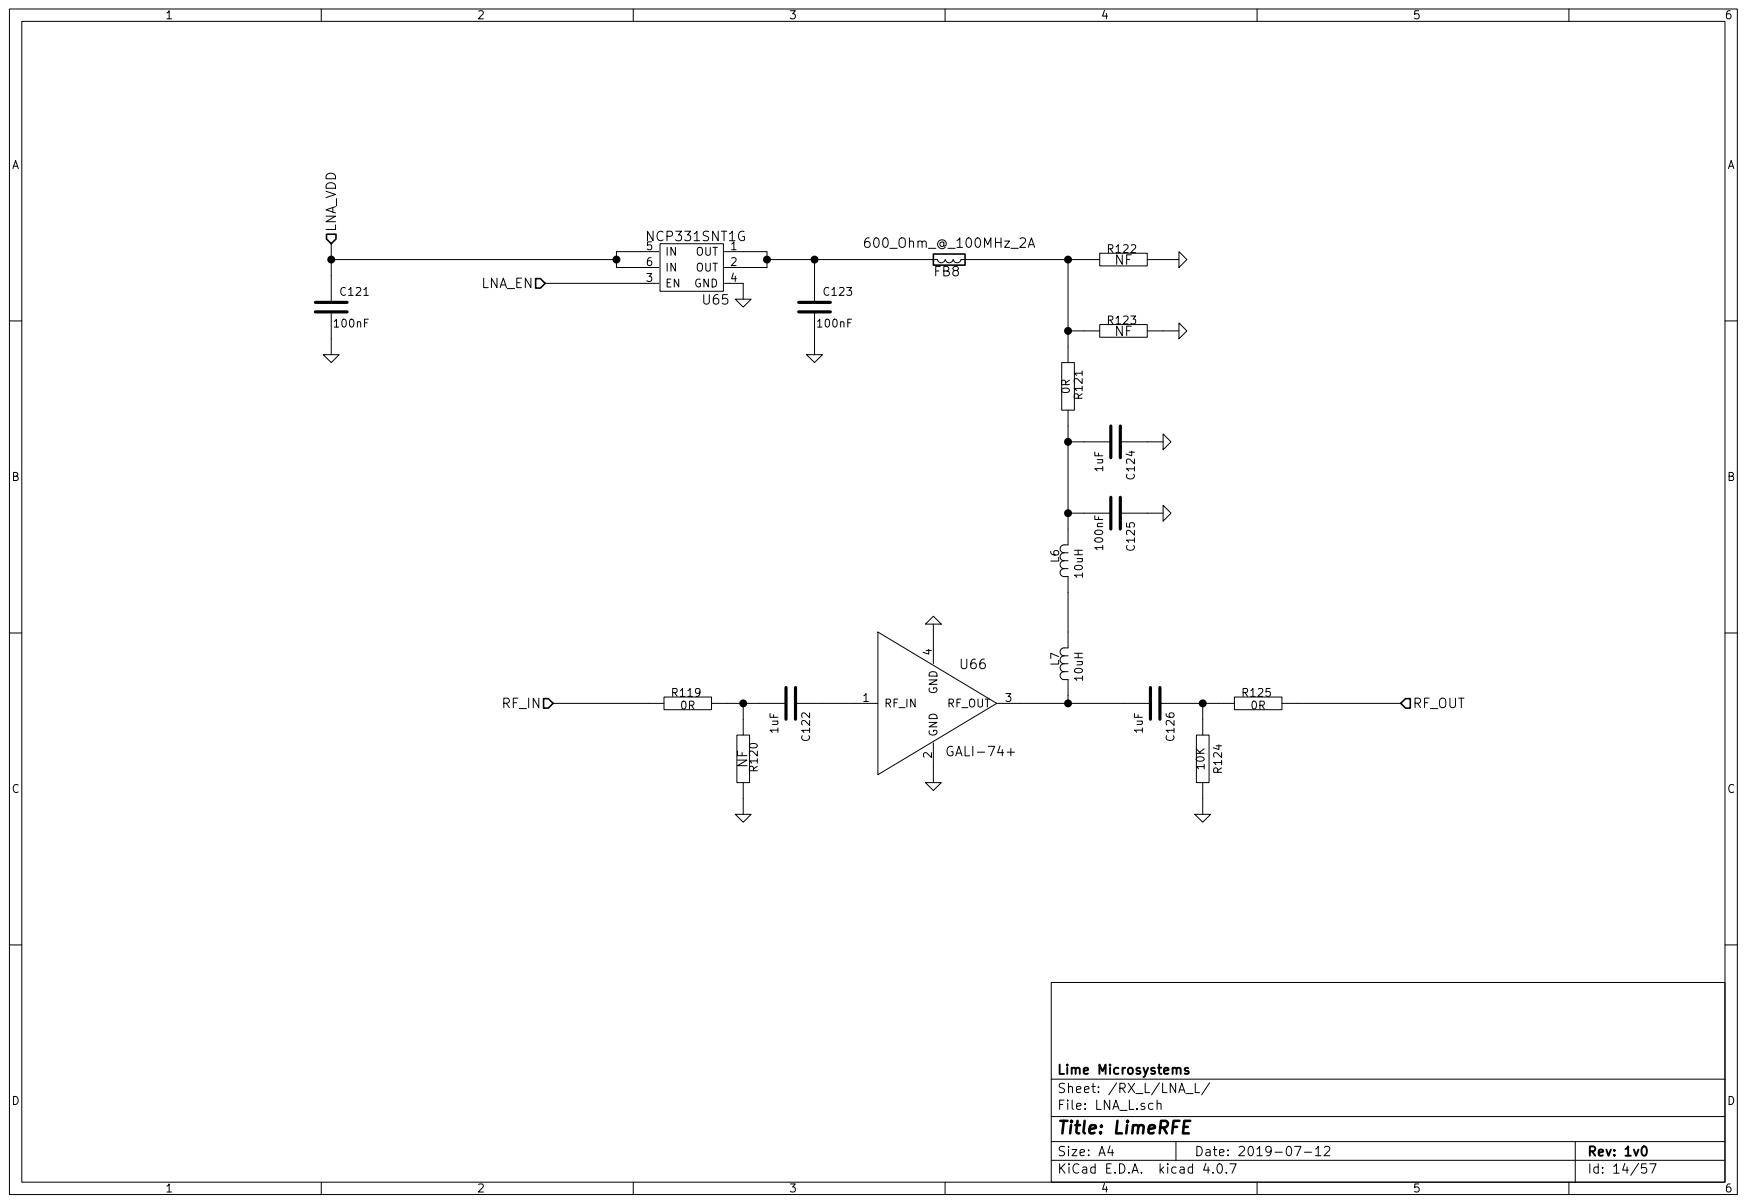
[picture p419: page 14]


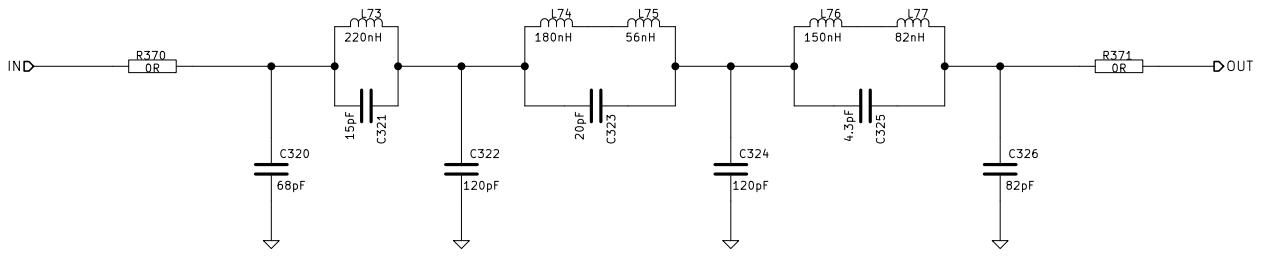
[picture p420: page 16]


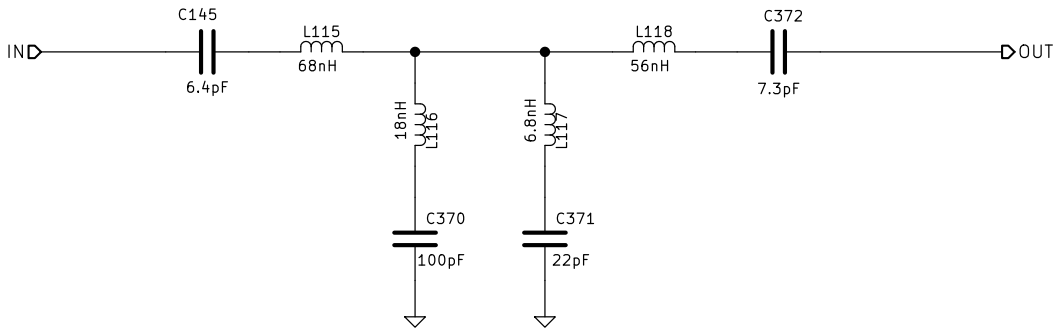
[picture p421: page 18]




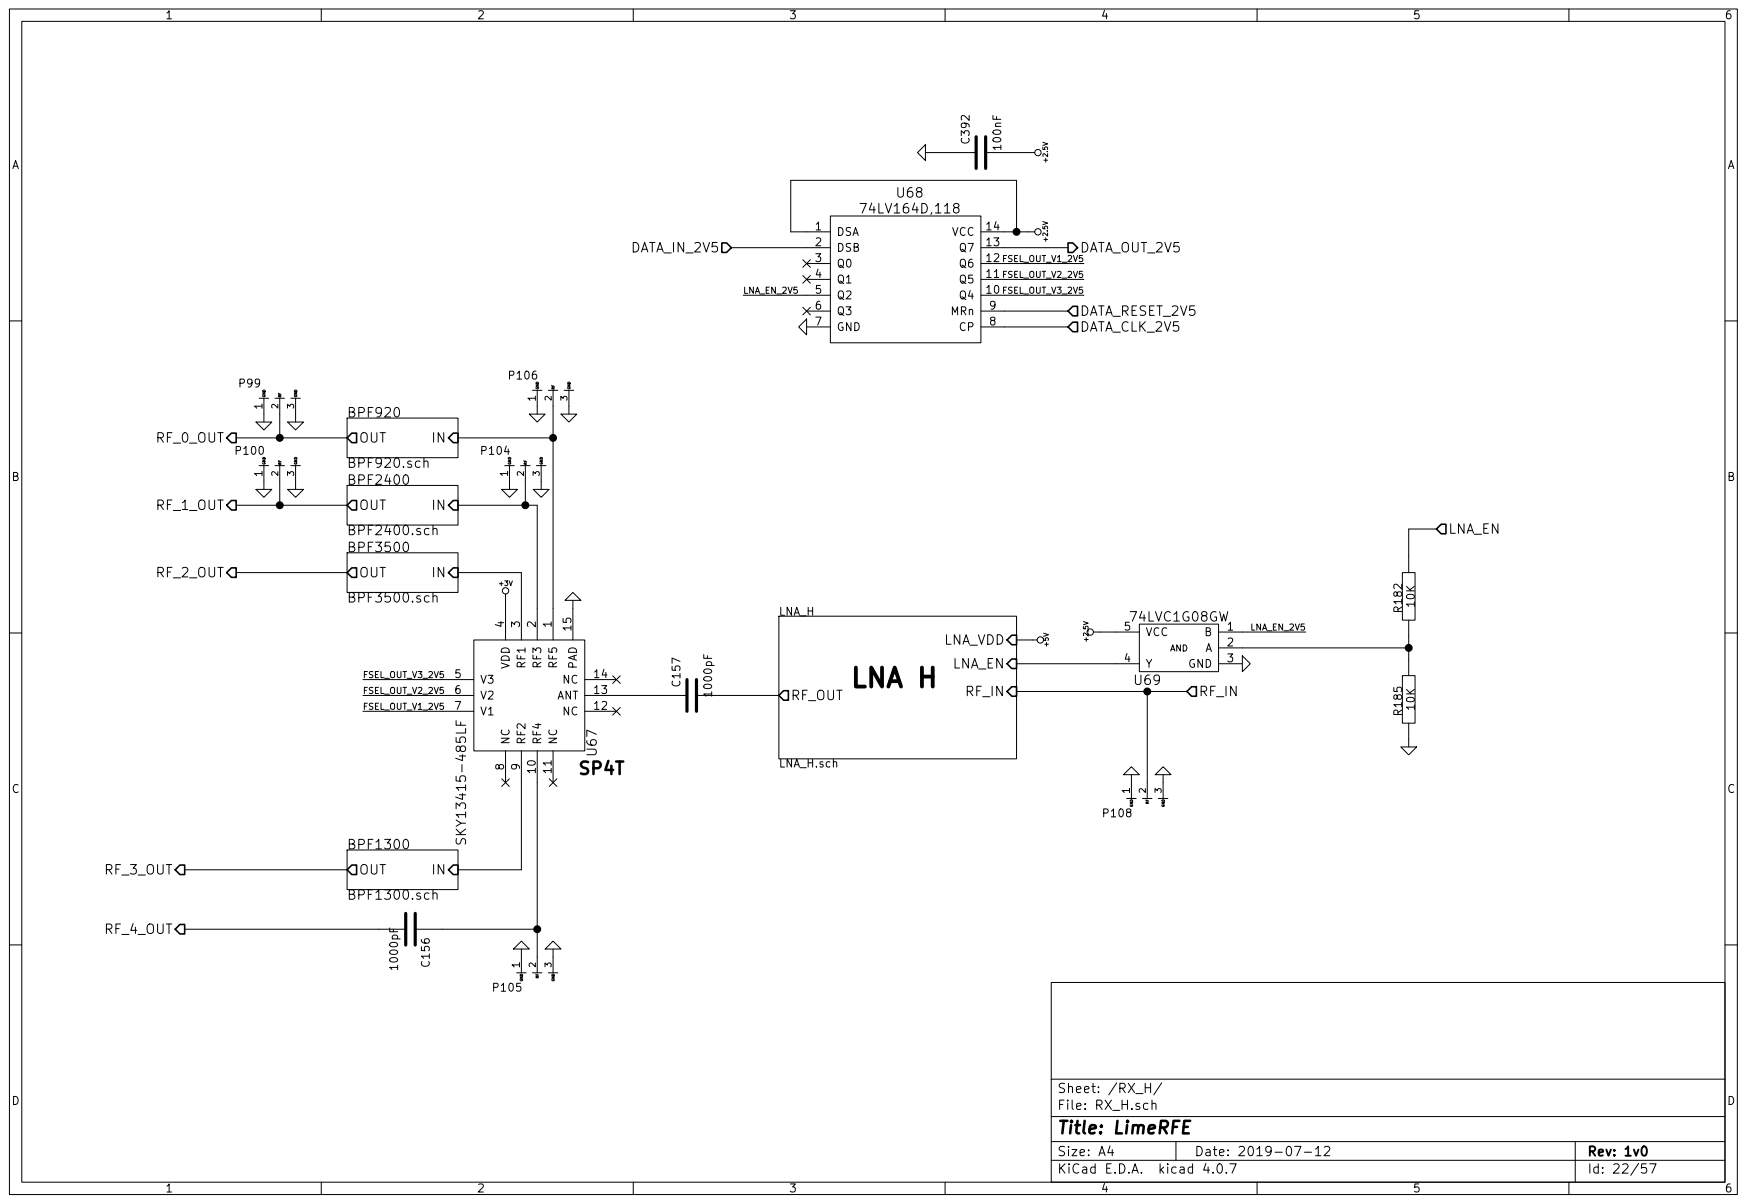
[picture p422: page 22]






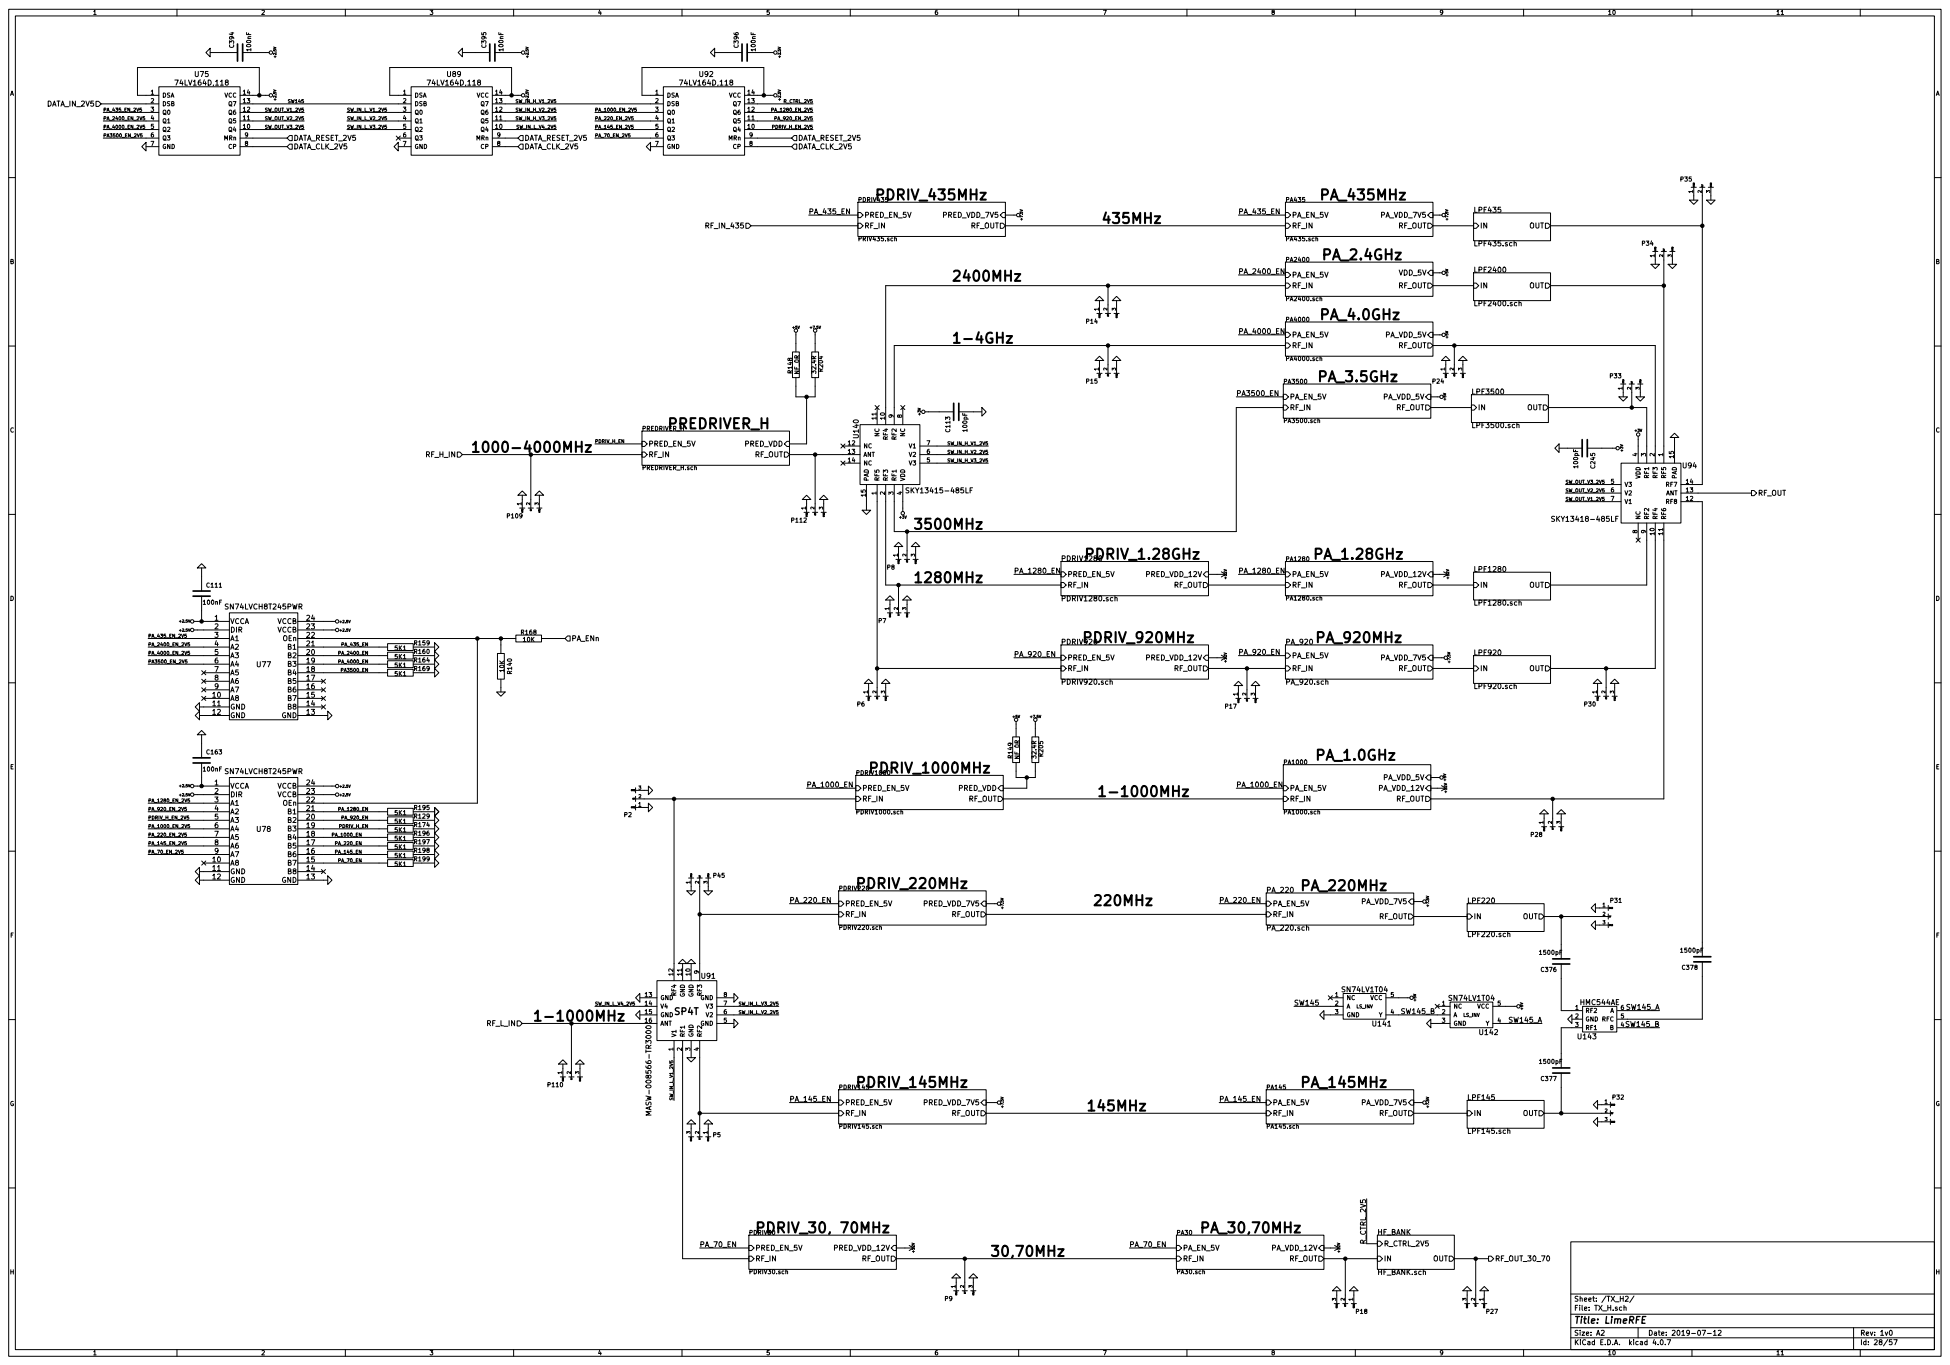
[picture p423: page 28]





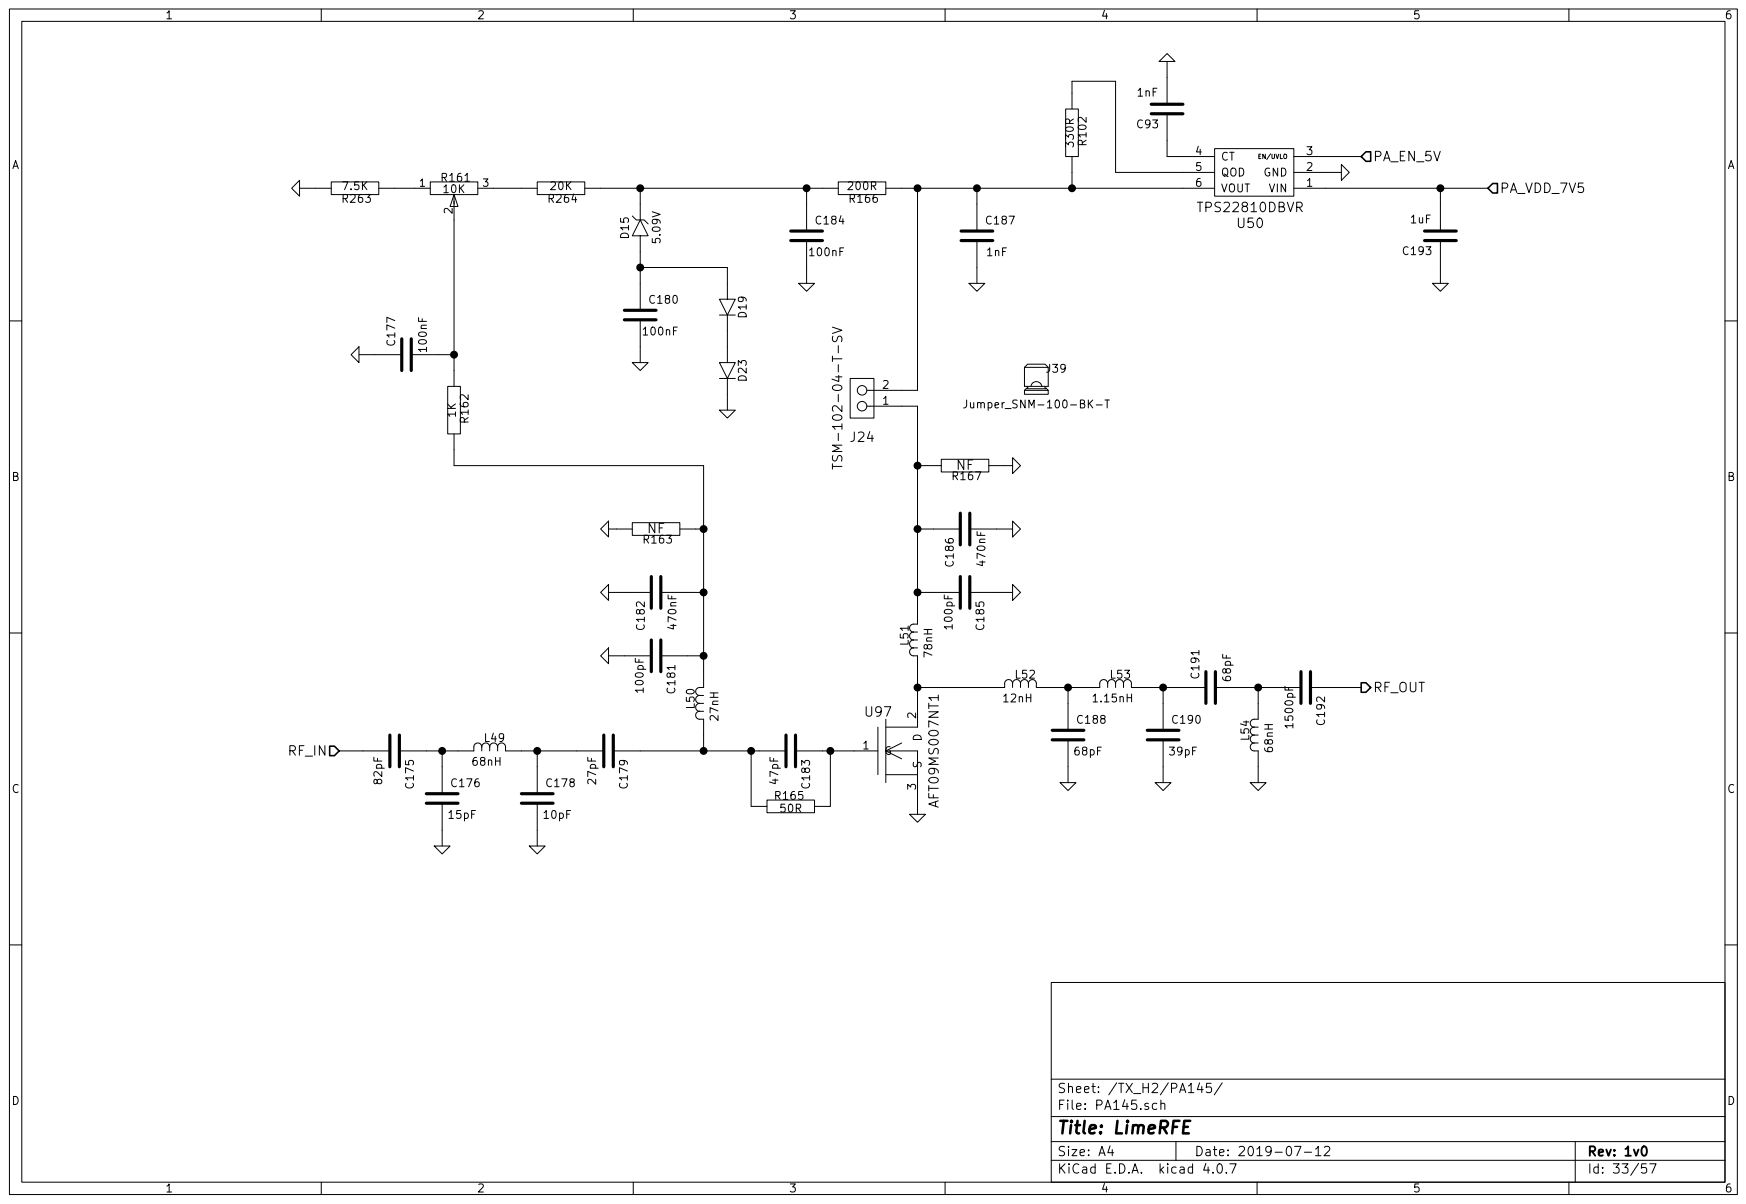
[picture p424: page 33]

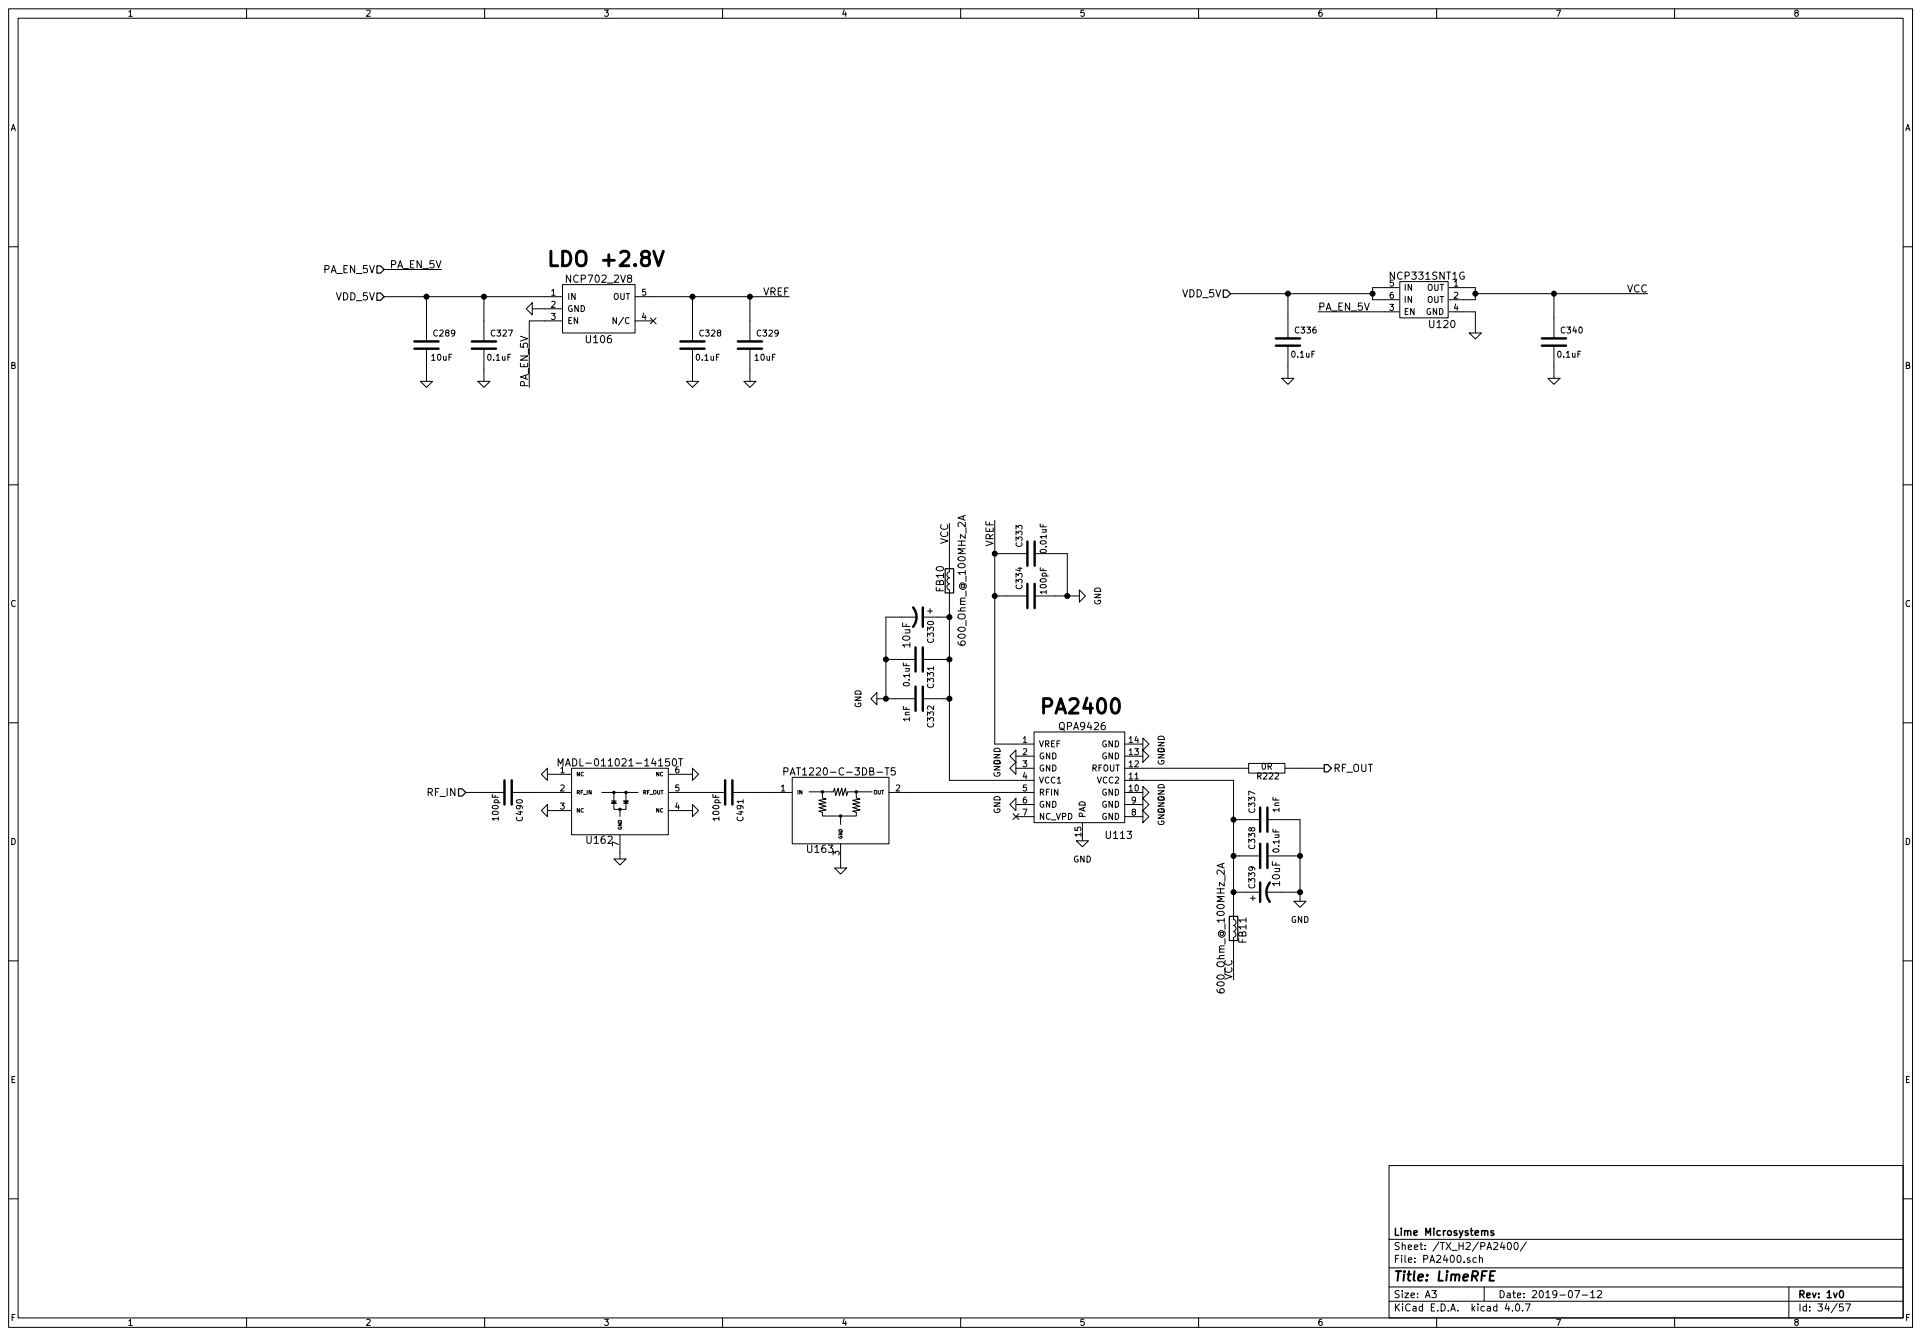
[picture p425: page 34]


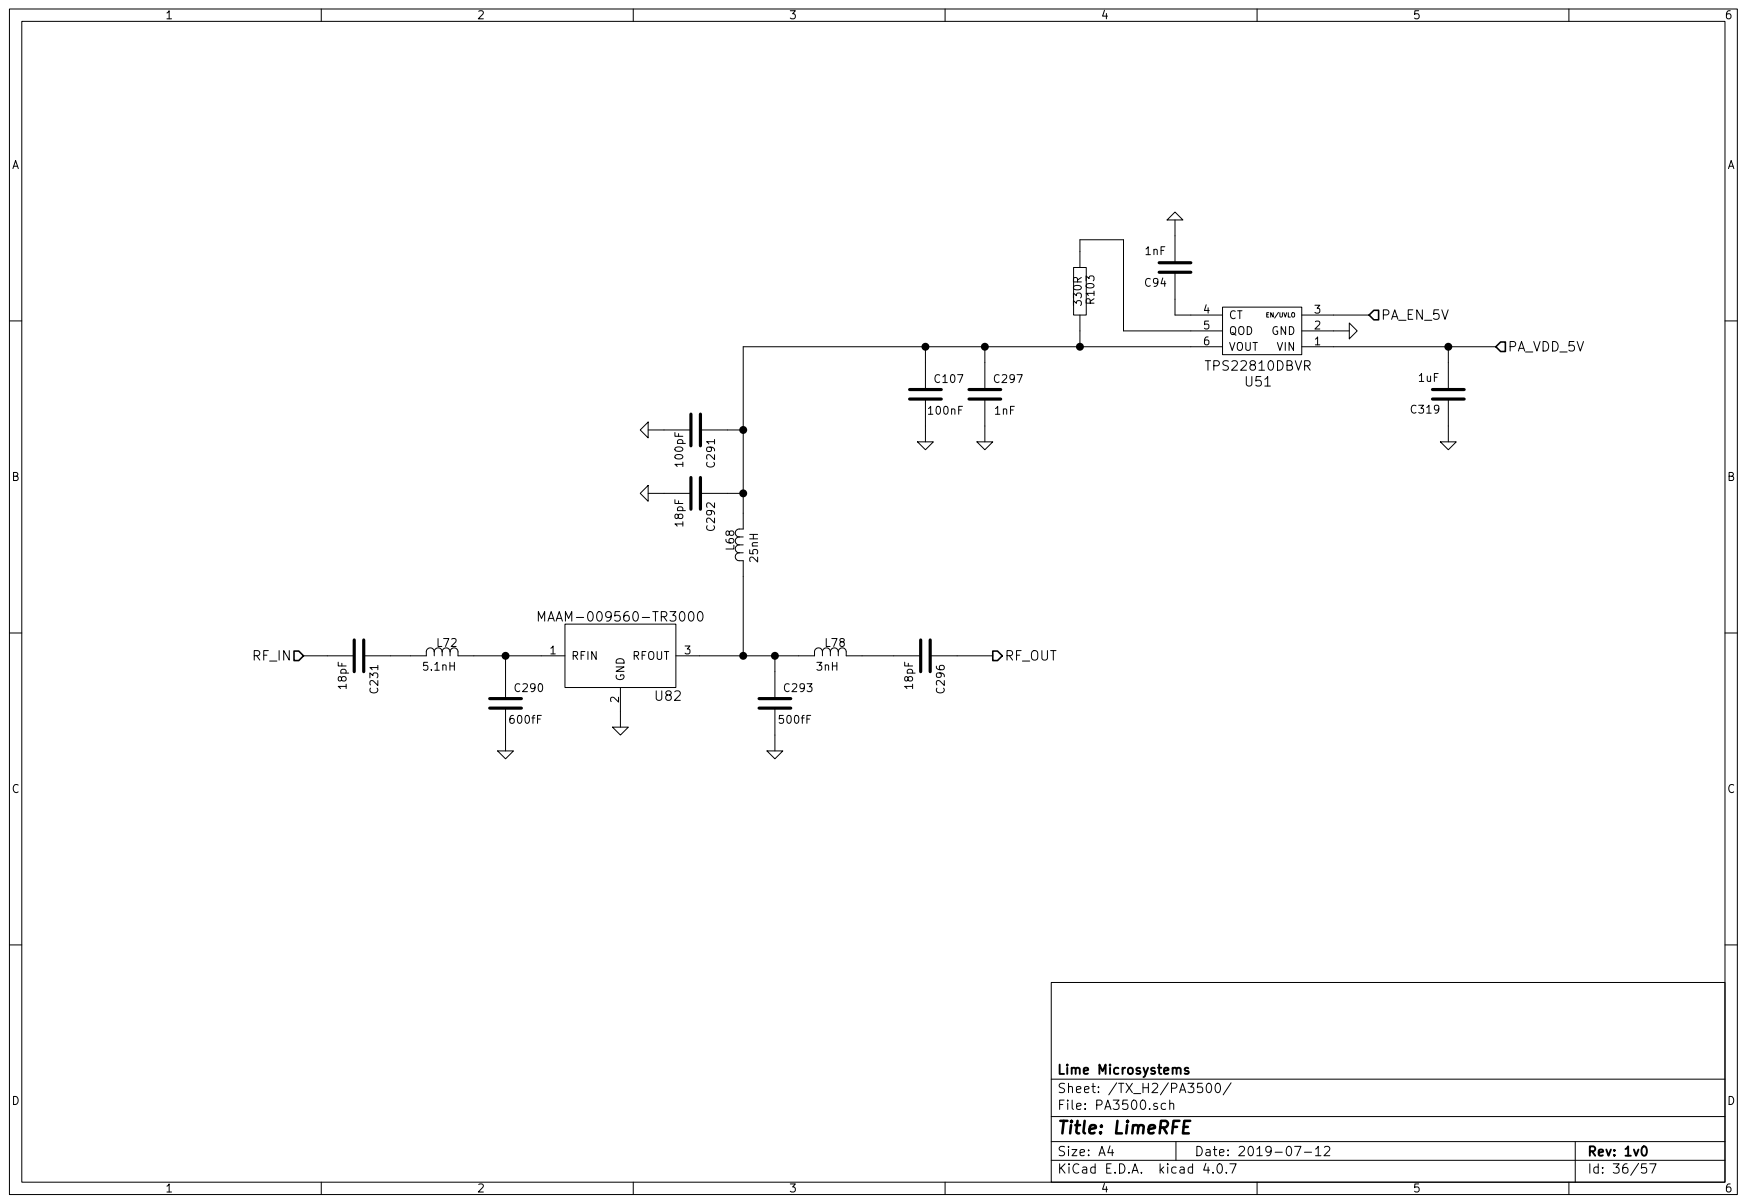
[picture p426: page 36]

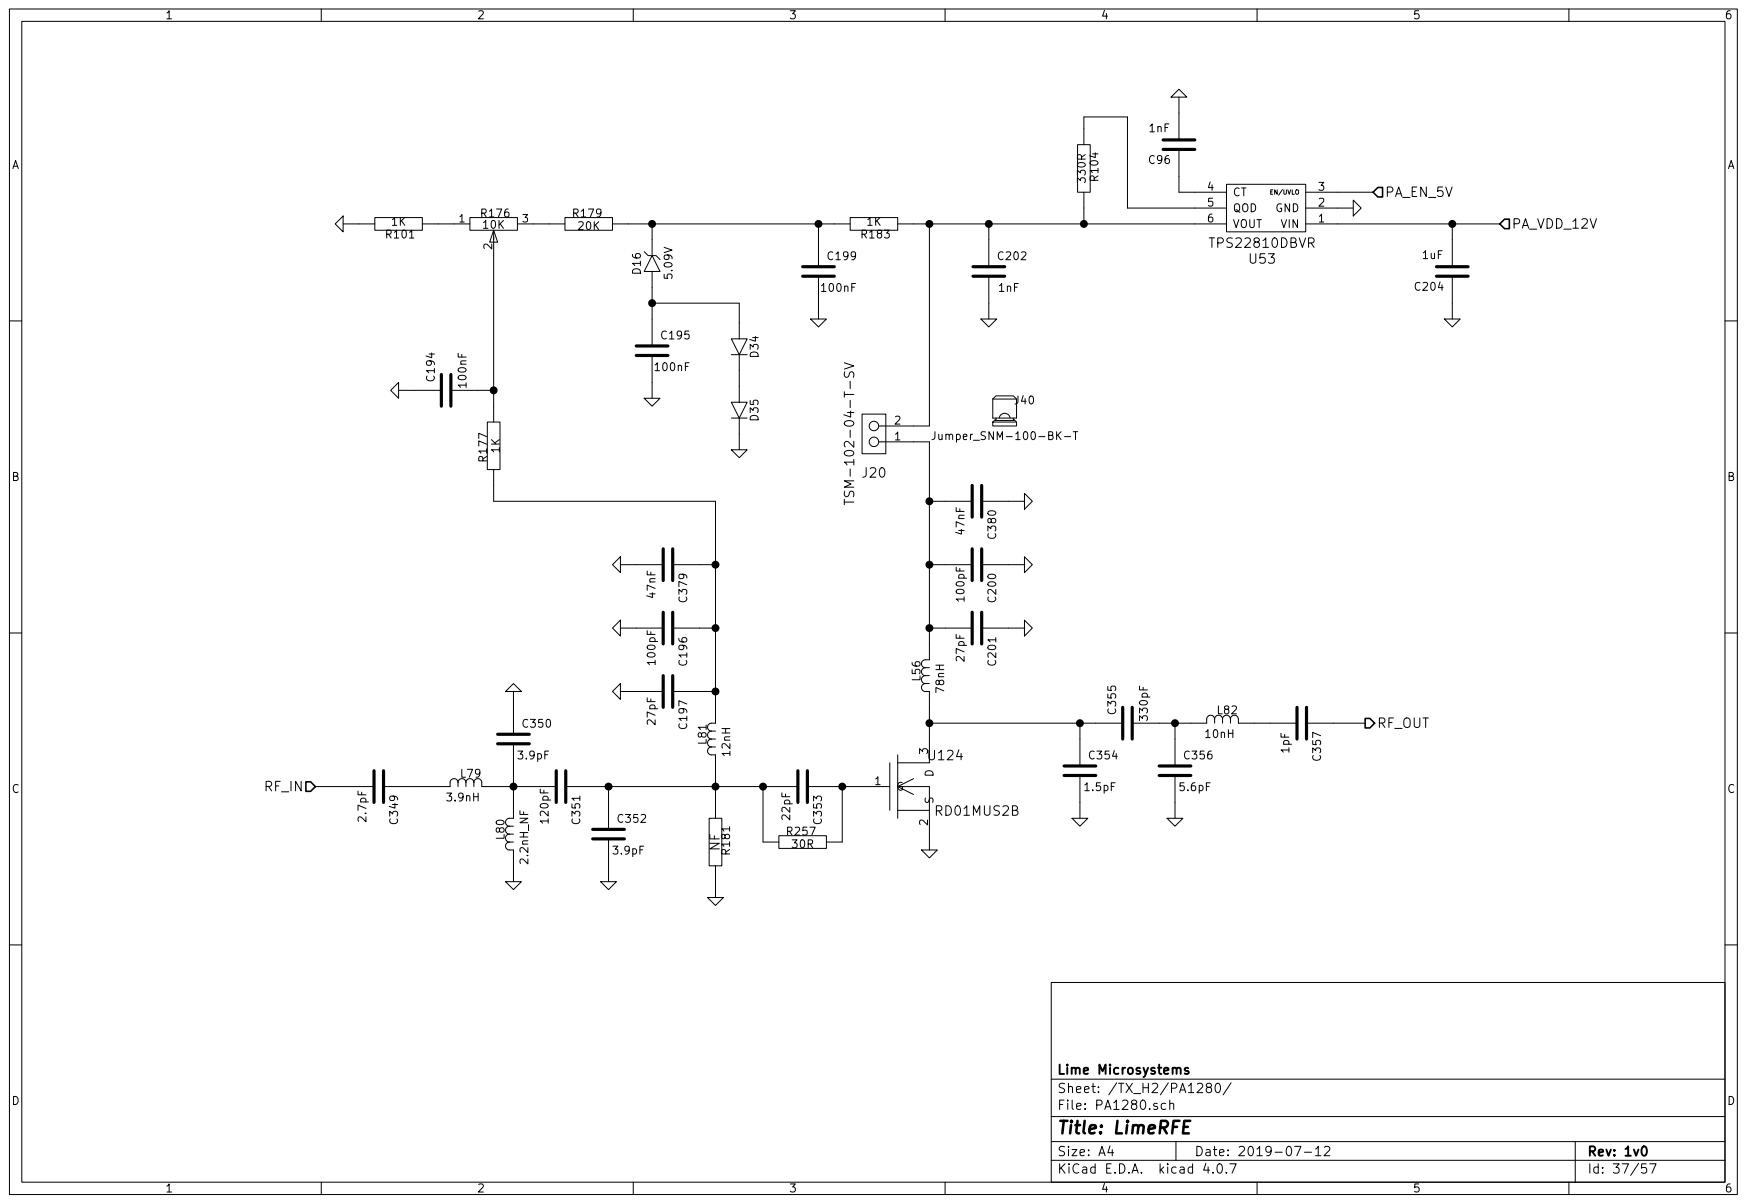
[picture p427: page 37]


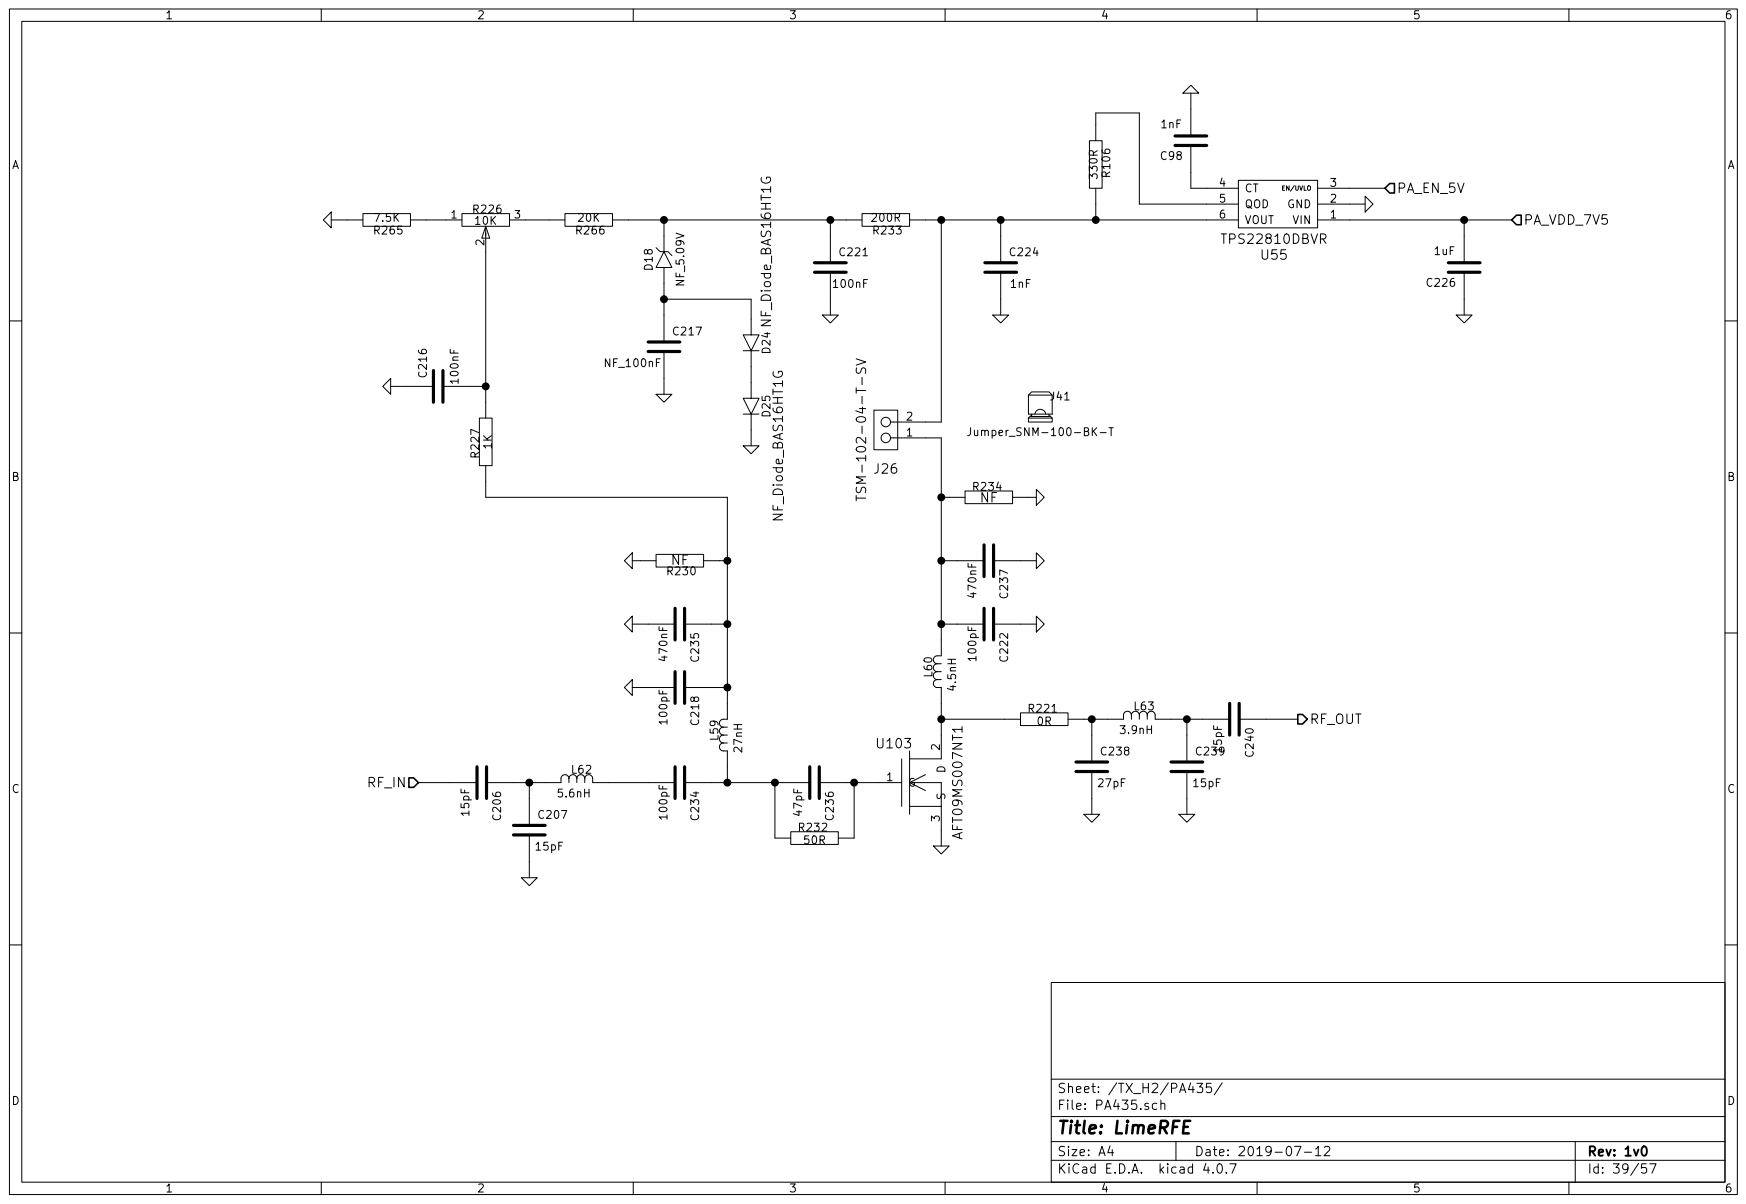
[picture p428: page 39]


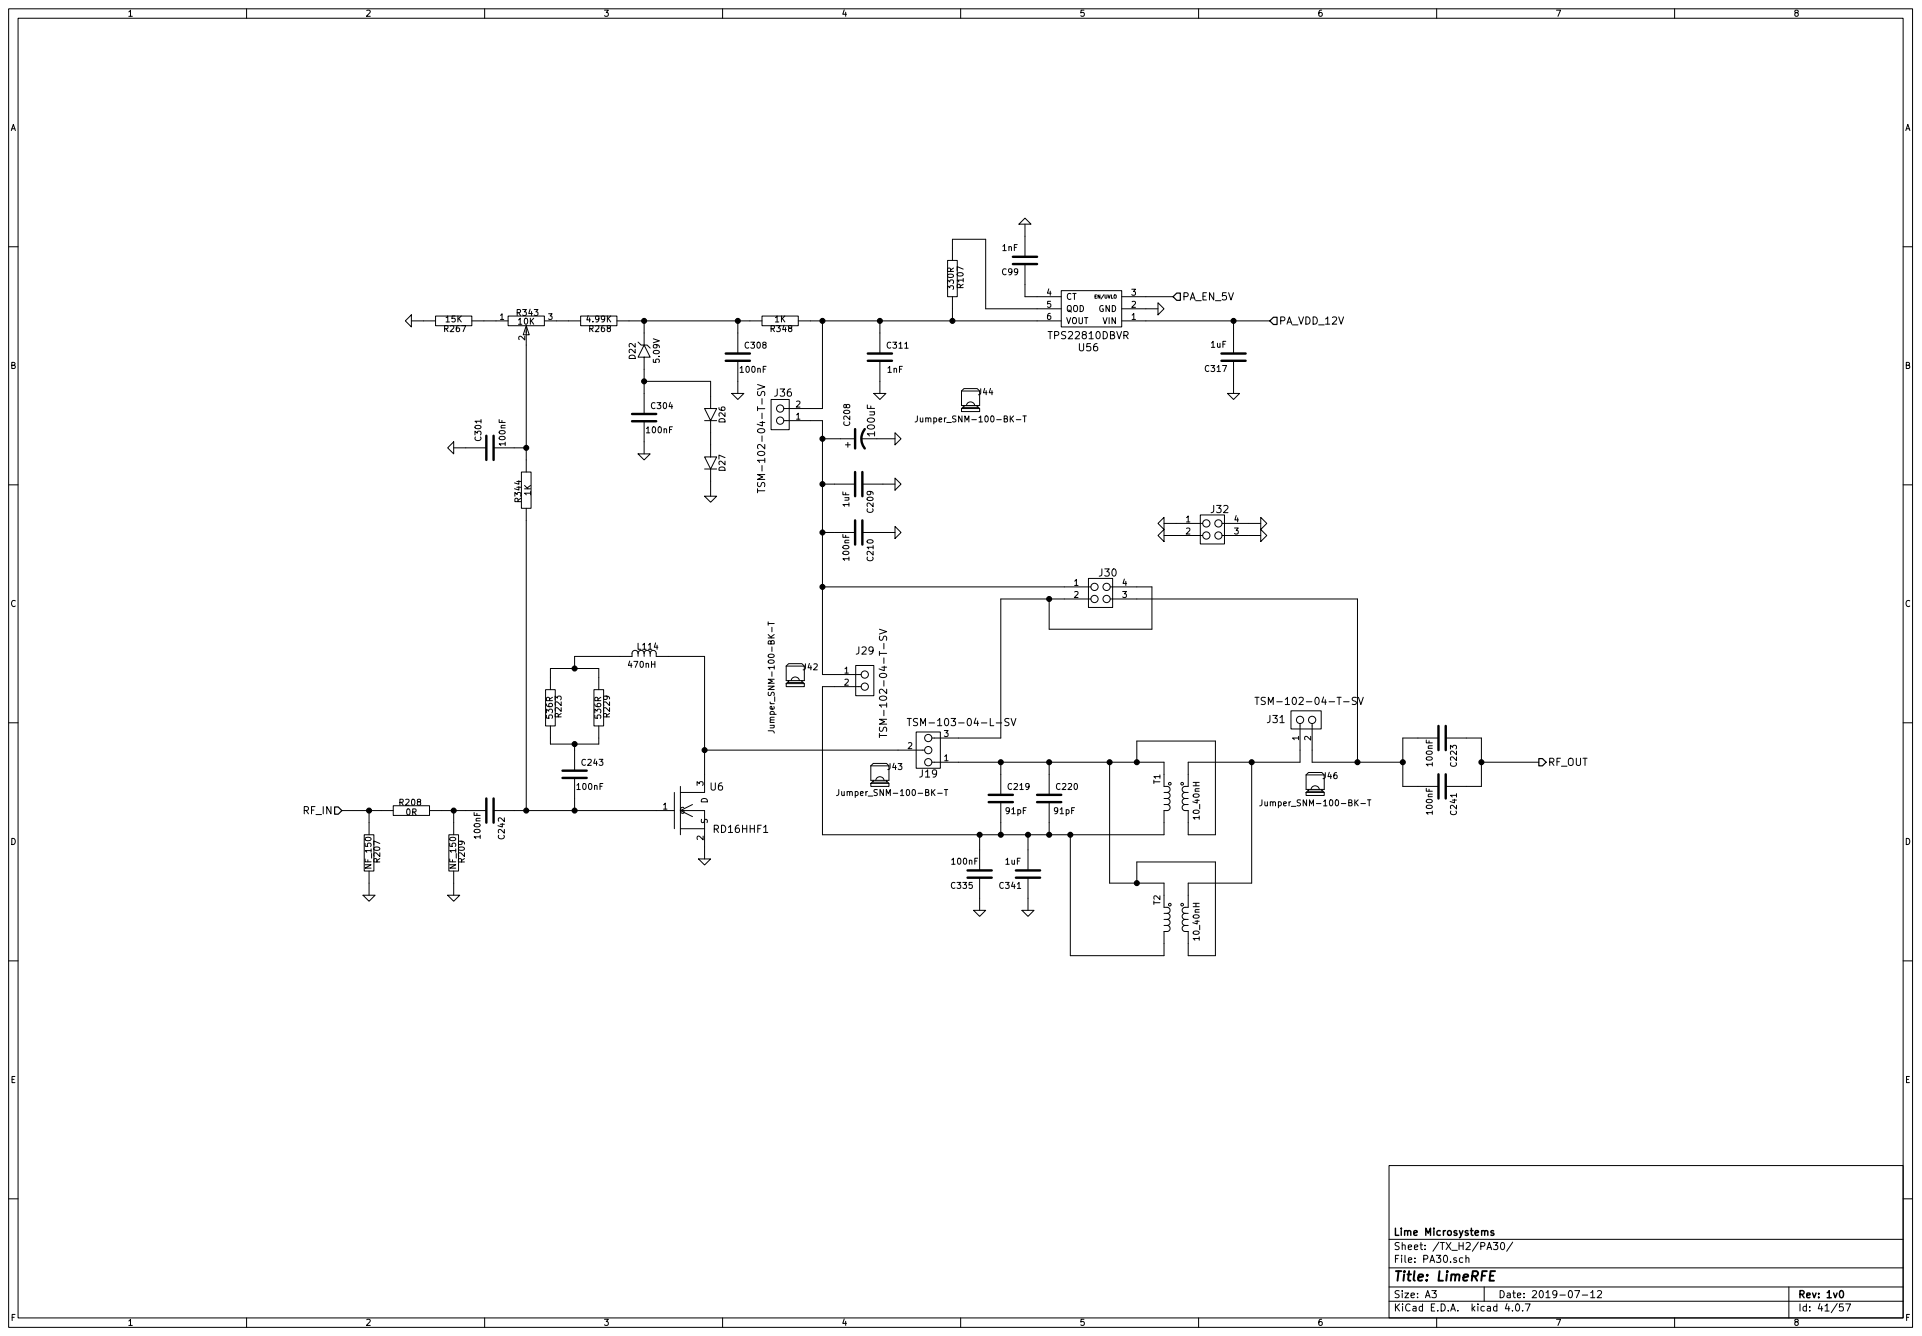
[picture p429: page 41]

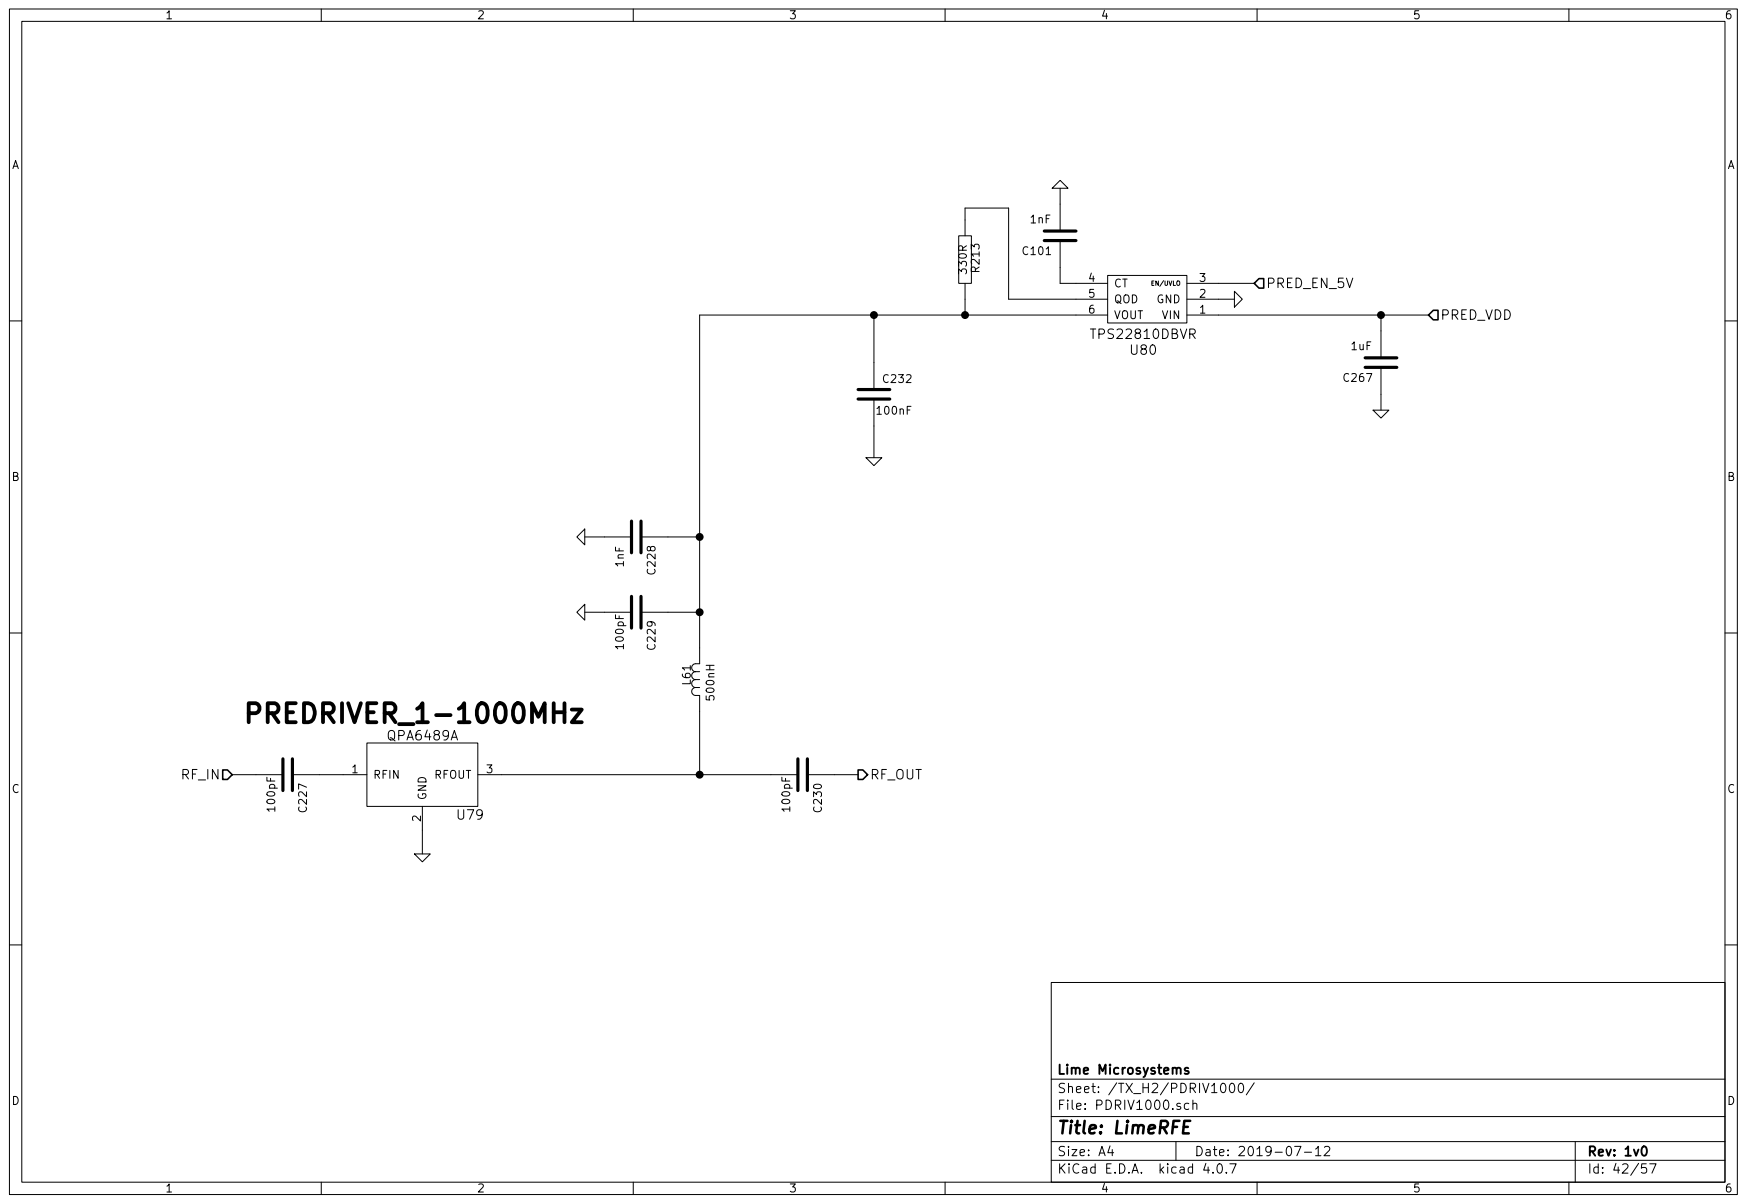
[picture p430: page 42]

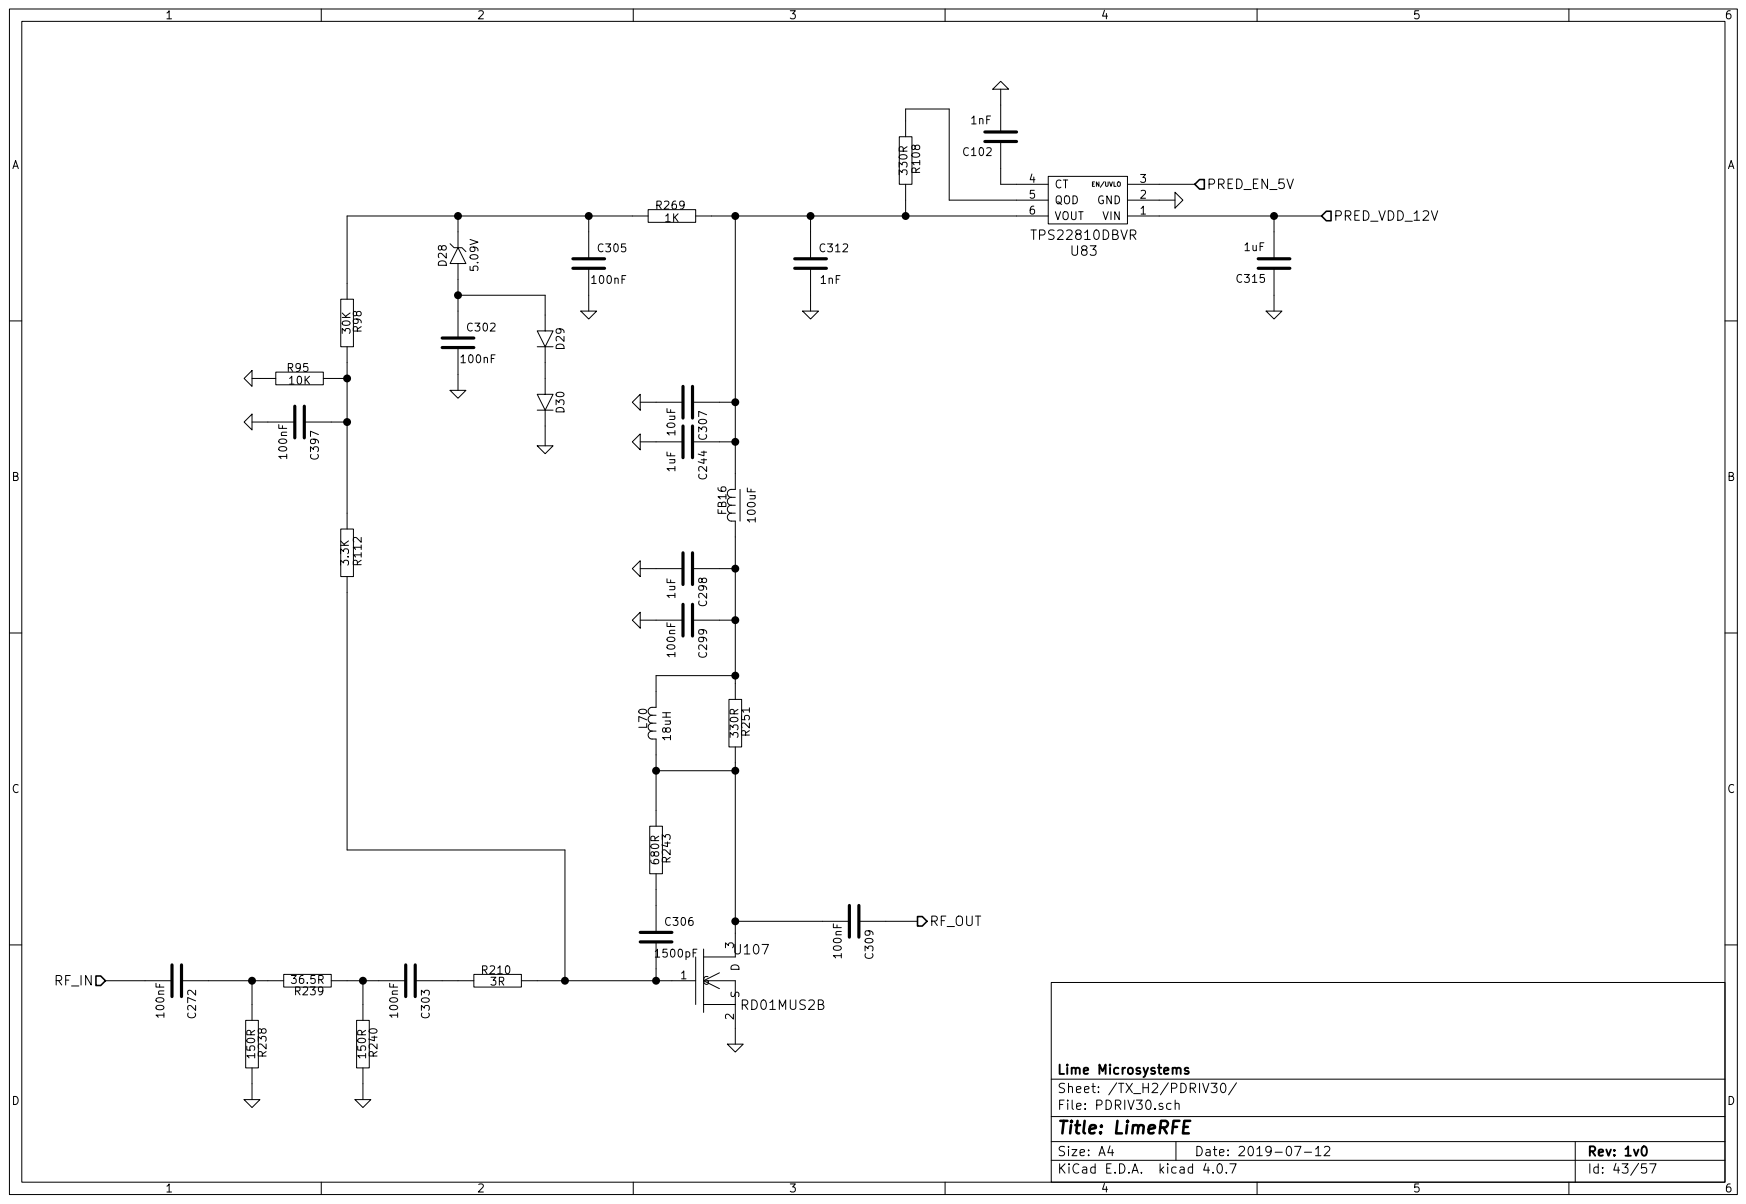
[picture p431: page 43]

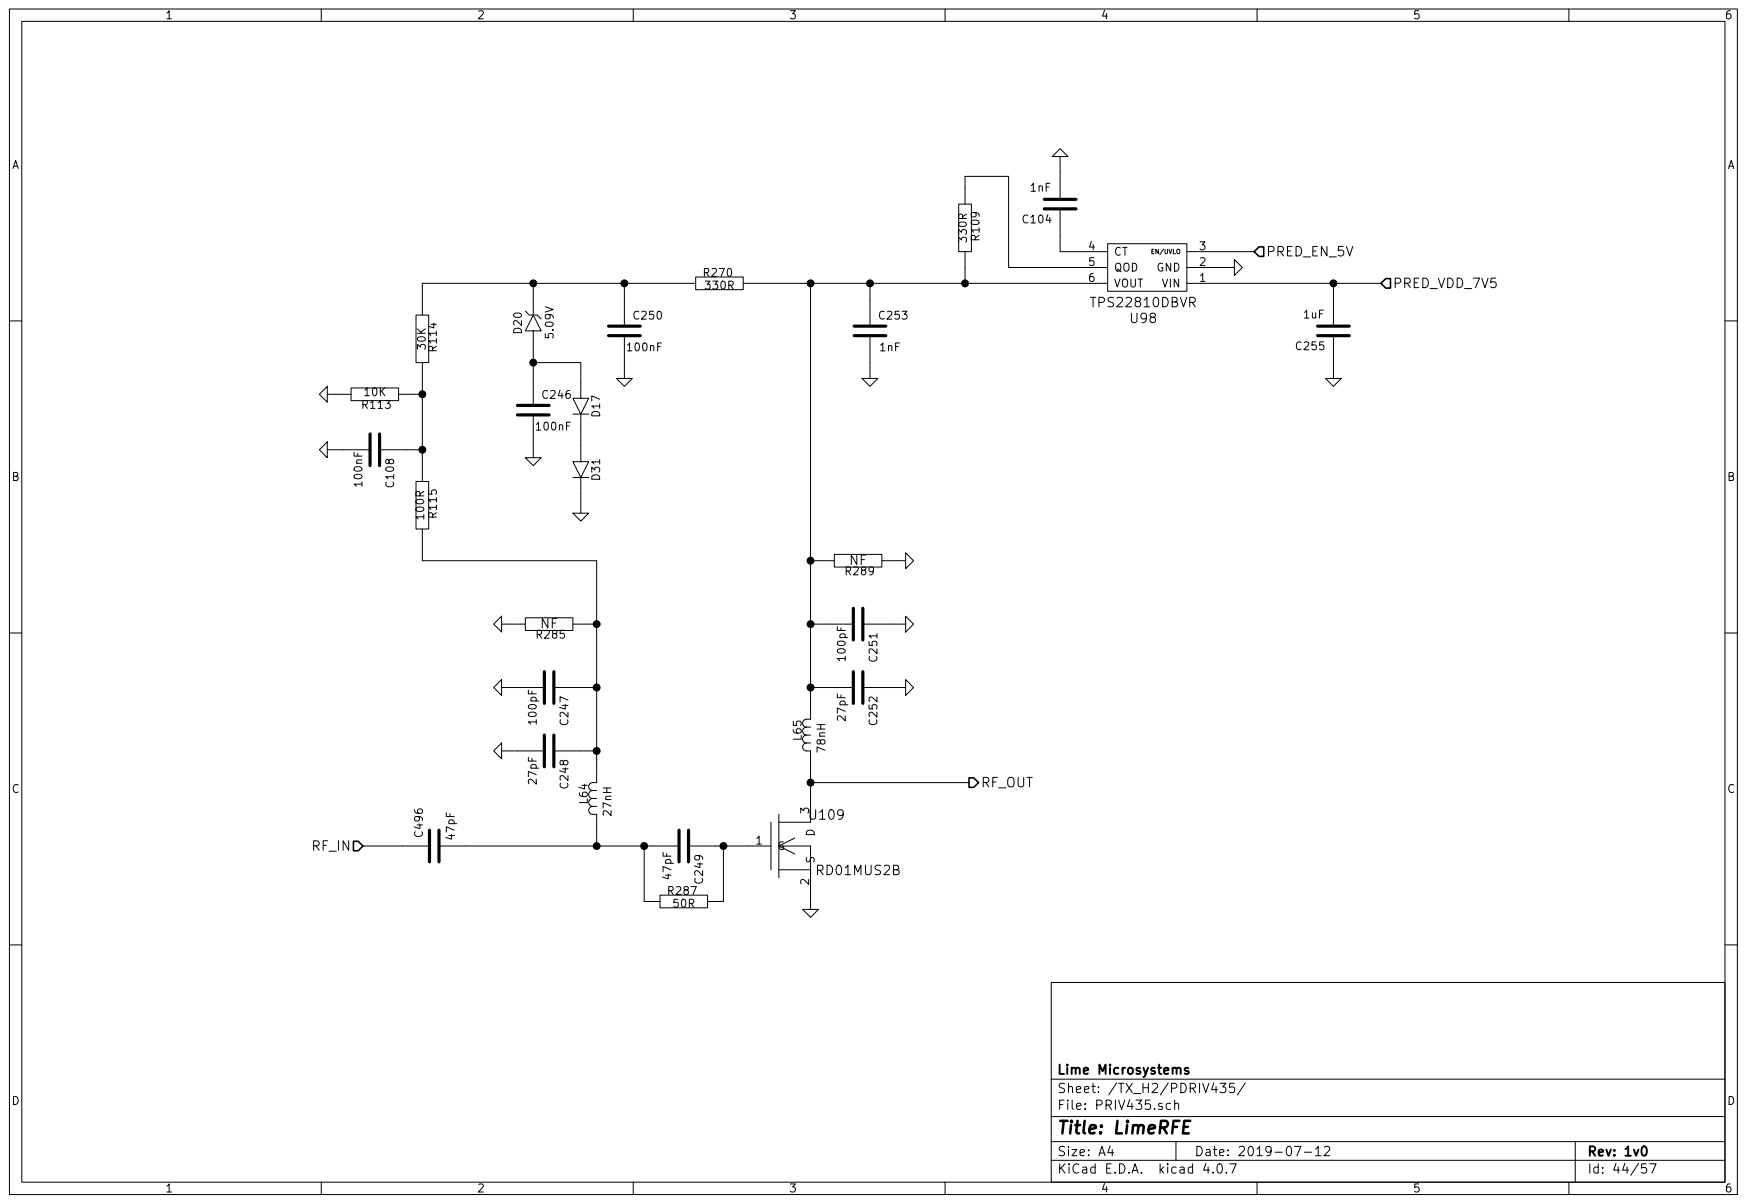
[picture p432: page 44]

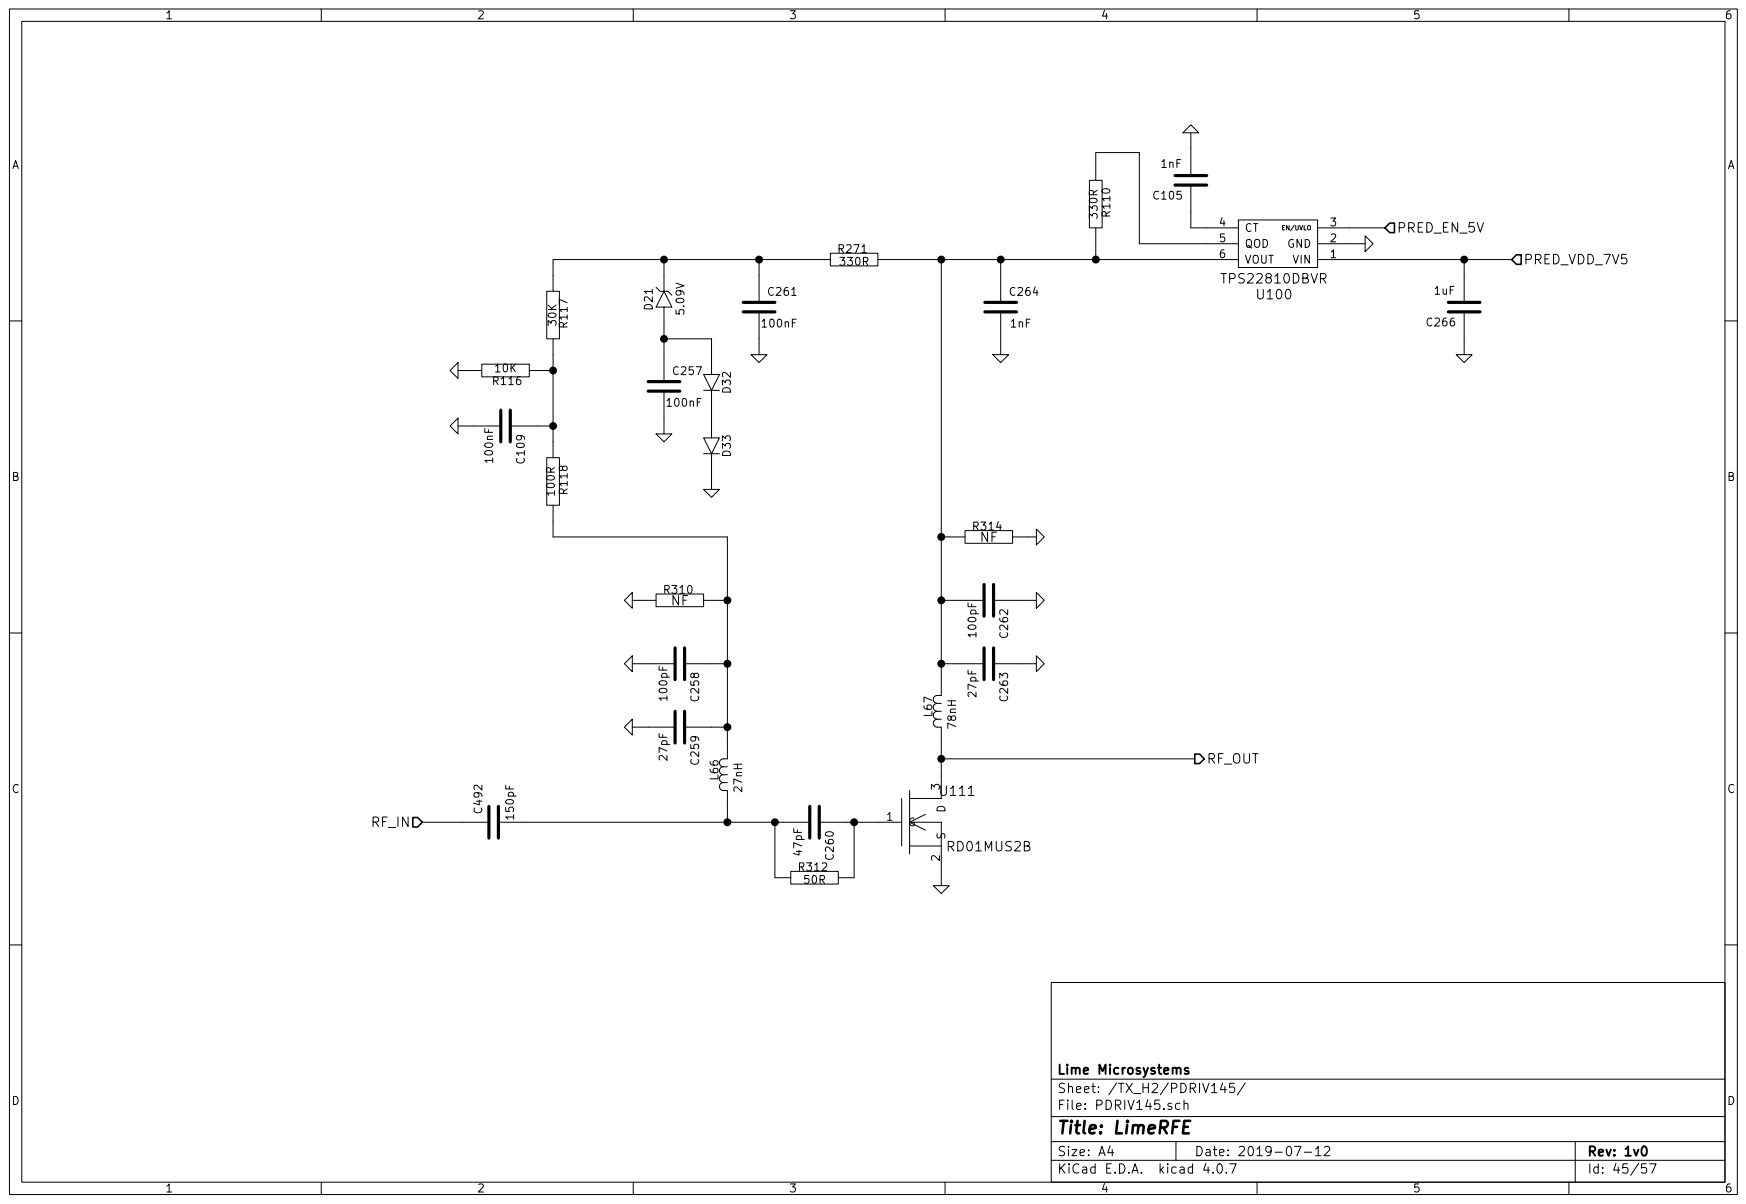
[picture p433: page 45]

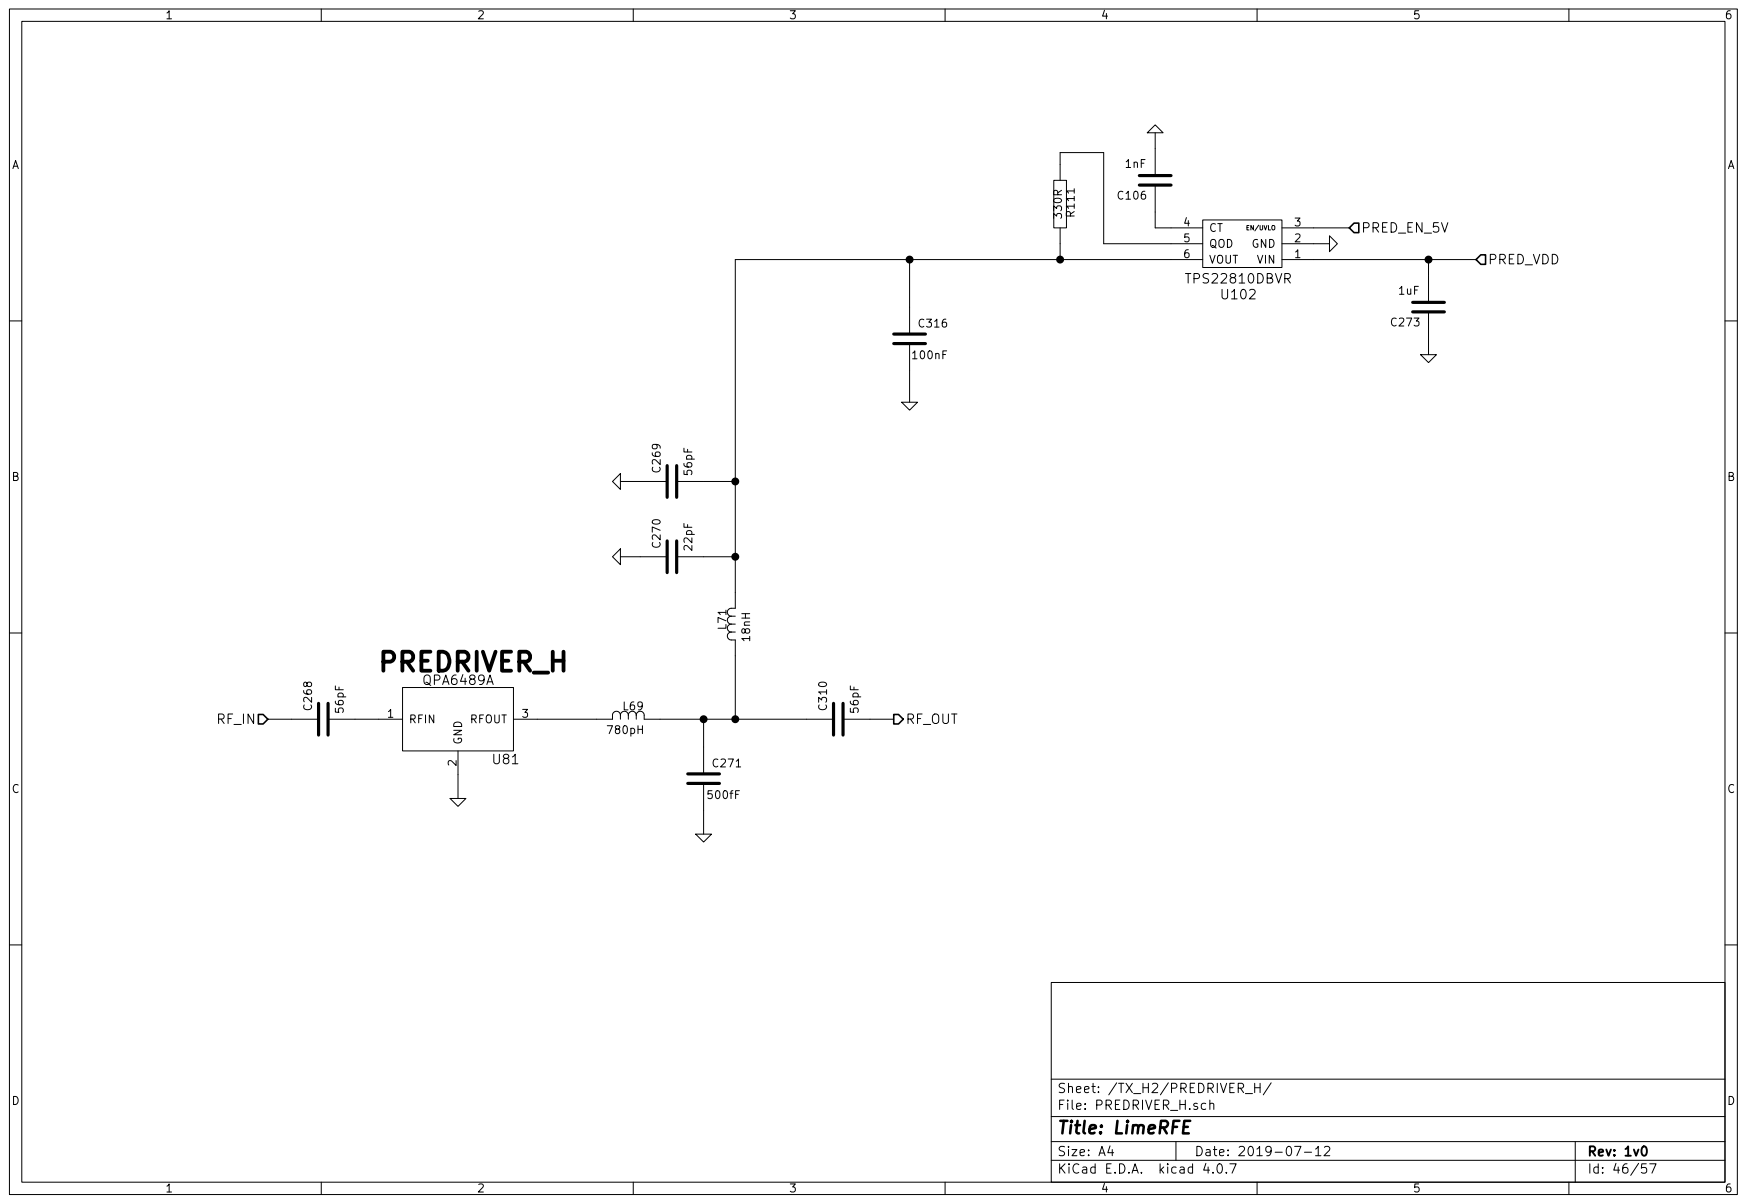
[picture p434: page 46]

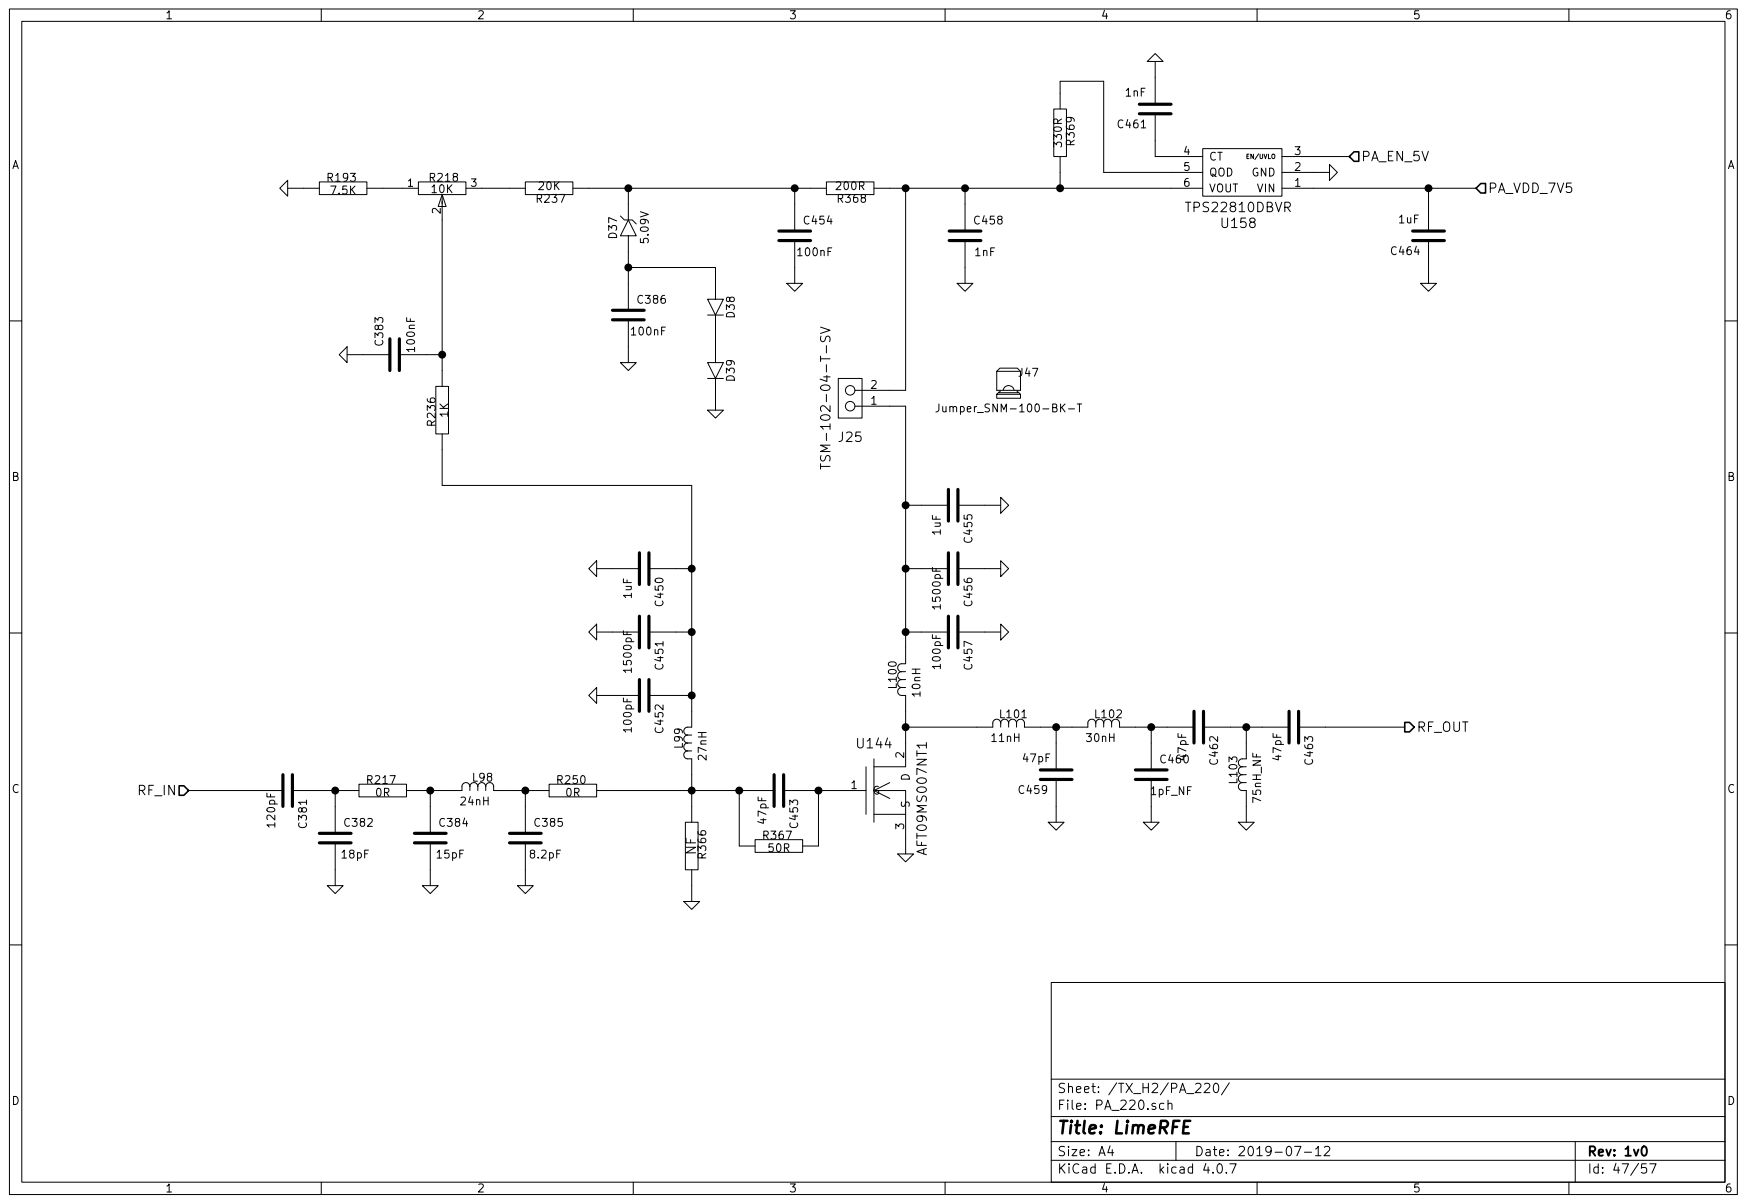
[picture p435: page 47]

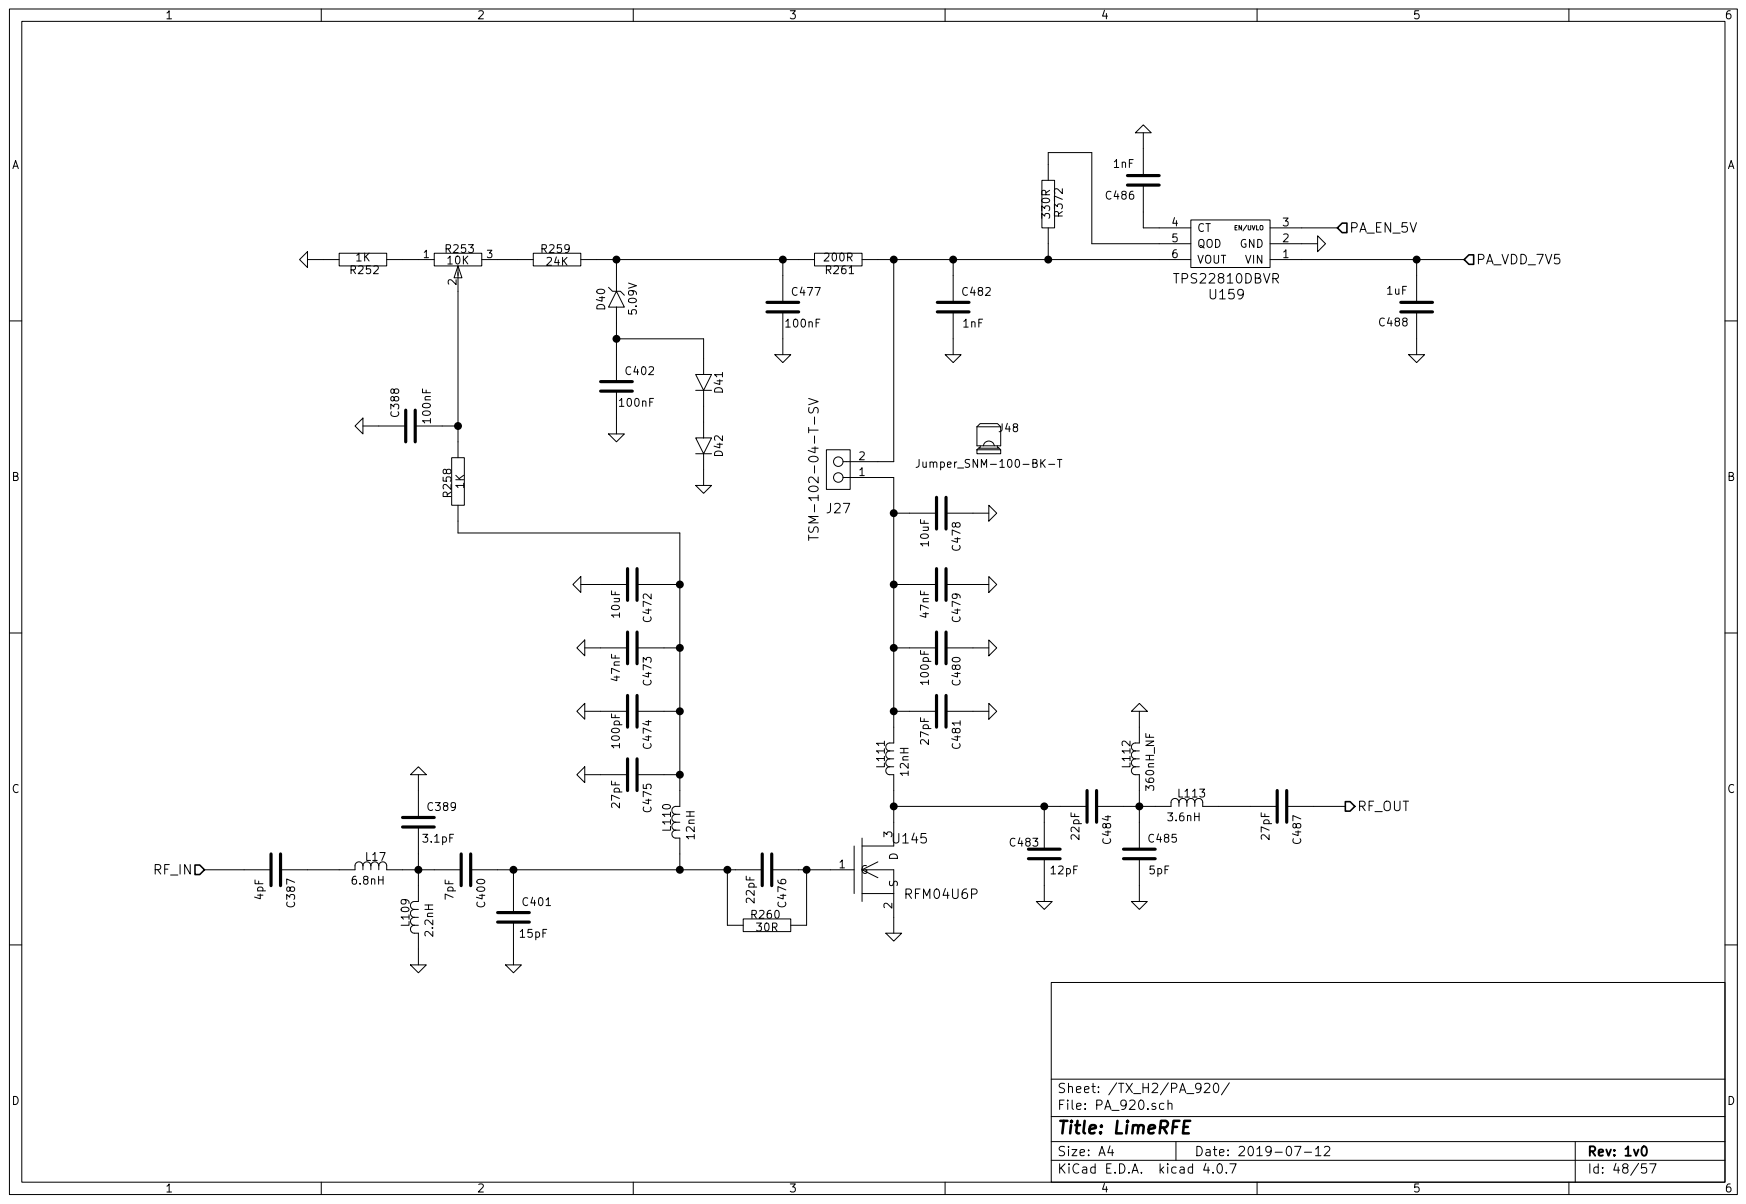
[picture p436: page 48]



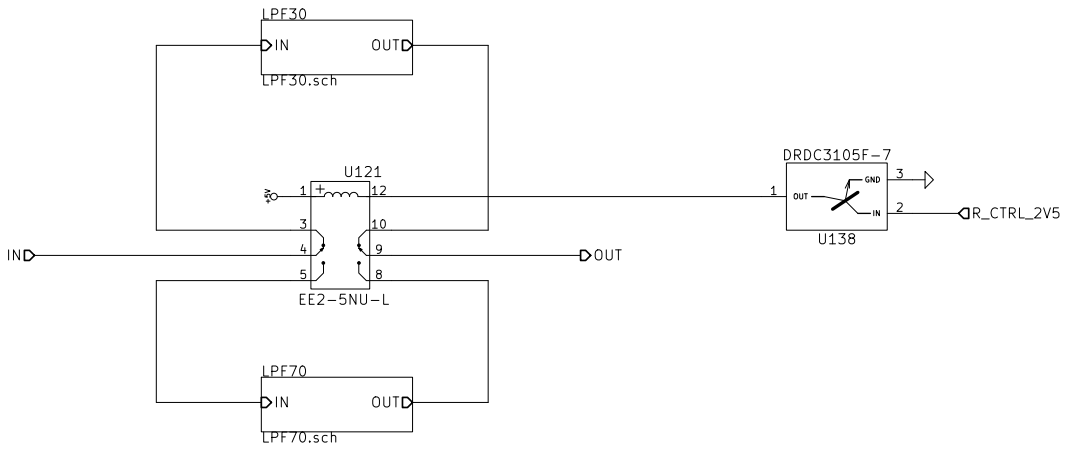
[picture p437: page 51]

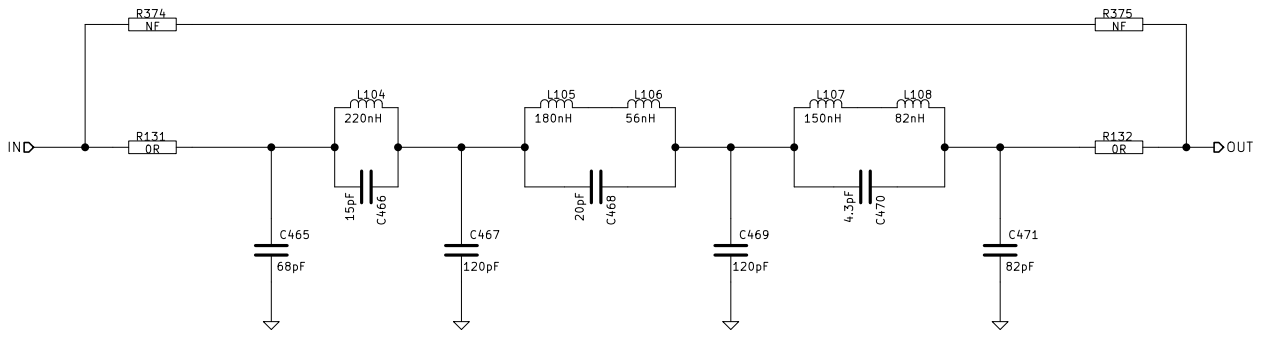
[picture p438: page 52]
