myriadrf/LimeRFE/archived/1v2/docs/LimeRFE_1v2_Block_Diagram.pdf

## 219 – 225 MHz

## 400 – 450 MHz
