myriadrf/LimeRFE/archived/0v3/docs/LimeRFE_0v3_Block_Diagram.pdf

## 0 – 30 MHz

## 140 – 150 MHz
