myriadrf/LimeRFE/archived/1v0/docs/LimeRFE_1v0_Block_Diagram.pdf

## 219 – 225 MHz

## 400 – 450 MHz
