myriadrf/LimeRFE/hardware/1v0/KiCAD/BPF30.sch

## KiCad design hardware/1v0/KiCAD/BPF30.sch (2020-02-29)

Schematic: BPF30.sch

Parts:
C320: 68pF_0402_GCM1555C1H680JA16J; SMD0402; Manufacturer Part Number GCM1555C1H680JA16J
C321: 15pF_0402_GJM1555C1H150JB01D; SMD0402; Manufacturer Part Number GJM1555C1H150JB01D
C322, C324: 120pF_0603_GRM1885C2A121JA01D; SMD0603; Manufacturer Part Number GRM1885C2A121JA01D
C323: 20pF_0402_GJM1555C1H200GB01D; SMD0402; Manufacturer Part Number GJM1555C1H200GB01D
C325: 4.3pF_0402_GCM1555C1H4R3CA16D; SMD0402; Manufacturer Part Number GCM1555C1H4R3CA16D
C326: 82pF_0603_GCM1555C1H820JA16D; SMD0603; Manufacturer Part Number GCM1555C1H820JA16D
L73: 220nH_0805_0805HP-221XGRB; SMD0805; Manufacturer Part Number 0805HP-221XGRB
L74: 180nH_0805_0805HP-181XGRB; SMD0805; Manufacturer Part Number 0805HP-181XGRB
L75: 56nH_0805_0805HP-56NXGRB; SMD0805; Manufacturer Part Number 0805HP-56NXGRB
L76: 150nH_0805_0805HP-151XGRB; SMD0805; Manufacturer Part Number 0805HP-151XGRB
L77: 82nH_0805_0805HP-82NXJRB; SMD0805; Manufacturer Part Number 0805HP-82NXJRB
R370, R371: 0R_0603_RCS06030000Z0EA; SMD0603; Manufacturer Part Number RCS06030000Z0EA
