myriadrf/LimeRFE/hardware/1v0/KiCAD/BPF60.sch

## KiCad design hardware/1v0/KiCAD/BPF60.sch (2020-02-29)

Schematic: BPF60.sch

Parts:
C146, C254: 33pF_0402_GCM1555C1H330FA16J; SMD0402; Manufacturer Part Number GCM1555C1H330FA16J
C147: 120pF_0402_GCM1555C1H121FA16D; SMD0402; Manufacturer Part Number GCM1555C1H121FA16D
C295: 18pF_0402_GCQ1555C1H180FB01D; SMD0402; Manufacturer Part Number GCQ1555C1H180FB01D
C314: 330pF_0402_GCM1555C1H331FA16D; SMD0402; Manufacturer Part Number GCM1555C1H331FA16D
C366: 56pF_0402_GCM1555C1H560FA16D; SMD0402; Manufacturer Part Number GCM1555C1H560FA16D
C367: 27pF_0402_GCM1555C1H270FA16D; SMD0402; Manufacturer Part Number GCM1555C1H270FA16D
L20: 210nH_0603_0603CS-R21XGLU; SMD0603; Manufacturer Part Number 0603CS-R21XGLU
L23: 200nH_0603_0603HP-R20XGLU; SMD0603; Manufacturer Part Number 0603HP-R20XGLU
L26: 51nH_0603_0603HP-51NXJLU; SMD0603; Manufacturer Part Number 0603HP-51NXJLU
L27: 390nH_0603_0603HP-R39XGLU; SMD0603; Manufacturer Part Number 0603HP-R39XGLU
L28: 120nH_0603_0603HP-R12XJLW; SMD0603; Manufacturer Part Number 0603HP-R12XJLW
L29: 18nH_0603_0603HP-18NXGLU; SMD0603; Manufacturer Part Number 0603HP-18NXGLU
L30: 250nH_0603_0603HP-R25XGLU; SMD0603; Manufacturer Part Number 0603HP-R25XGLU
