myriadrf/LimeRFE/hardware/1v0/KiCAD/BPF145.sch

## KiCad design hardware/1v0/KiCAD/BPF145.sch (2020-02-29)

Schematic: BPF145.sch

Parts:
C148, C151: 3.6pF_0402_GJM1555C1H3R6WB01D; SMD0402; Manufacturer Part Number GJM1555C1H3R6WB01D
C149: 43pF_0402_GRM1555C1H430GA01D; SMD0402; Manufacturer Part Number GRM1555C1H430GA01D
C150: 22pF_0402_GCM1555C1H220GA16D; SMD0402; Manufacturer Part Number GCM1555C1H220GA16D
C497, C498: 1uF_0402_GCM155C71A105KE38D; SMD0402; Manufacturer Part Number GCM155C71A105KE38D
L32, L36: 330nH_0805; SMD0805; Manufacturer Part Number 0805HP-331XGRB
L33: 39nH_0805; SMD0805; Manufacturer Part Number 0805HT-39NTJLB
L34: 12nH_0805; SMD0805; Manufacturer Part Number 0805HP-12NXGRB
L35: 27nH_0805; SMD0805; Manufacturer Part Number 0805HQ-27NXGLB
