myriadrf/LimeRFE/hardware/1v0/KiCAD/BPF220.sch

## KiCad design hardware/1v0/KiCAD/BPF220.sch (2020-02-29)

Schematic: BPF220.sch

Parts:
C145: 6.4pF_0402_GRM1555C1H6R4BA01D; SMD0402; Manufacturer Part Number GRM1555C1H6R4BA01D
C370: 100pF_0402_GCM1555C1H101JA16D; SMD0402; Manufacturer Part Number GCM1555C1H101JA16D
C371: 22pF_0402_CC0402JRNPO9BN220; SMD0402; Manufacturer Part Number CC0402JRNPO9BN220
C372: 7.3pF_0402_GJM1555C1H7R3BB01D; SMD0402; Manufacturer Part Number GJM1555C1H7R3BB01D
L115: 68nH_0603_0603CS-68NXJLW; SMD0603; Manufacturer Part Number 0603CS-68NXJLW
L116: 18nH_0603_0603CS-18NXJLW; SMD0603; Manufacturer Part Number 0603CS-18NXJLW
L117: 6.8nH_0603_0603CS-6N8XJLW; SMD0603; Manufacturer Part Number 0603CS-6N8XJLW
L118: 56nH_0603_0603CS-56NXJLW; SMD0603; Manufacturer Part Number 0603CS-56NXJLW
