myriadrf/LimeRFE/hardware/1v0/KiCAD/BPF440.sch

## KiCad design hardware/1v0/KiCAD/BPF440.sch (2020-02-29)

Schematic: BPF440.sch

Parts:
C152: 18pF_0402_GRM1555C1H180JA01D; SMD0402; Manufacturer Part Number GRM1555C1H180JA01D
C153: 6.7pF_0402_GRM1555C1H6R7DA01D; SMD0402; Manufacturer Part Number GRM1555C1H6R7DA01D
C154: 6.6pF_0402_GRM1555C1H6R6BA01D; SMD0402; Manufacturer Part Number GRM1555C1H6R6BA01D
C155: 33pF_0402_GRM1555C1H330GA01J; SMD0402; Manufacturer Part Number GRM1555C1H330GA01J
C499, C500: 1uF_0402_GCM155C71A105KE38D; SMD0402; Manufacturer Part Number GCM155C71A105KE38D
L37: 4.7nH_0805_0805HT-4N7TJLC; SMD0805; Manufacturer Part Number 0805HT-4N7TJLC
L38: 15nH_0805_0805HT-15NTJLB; SMD0805; Manufacturer Part Number 0805HT-15NTJLB
L39: 47nH_0805_0805HT-47NTJLB; SMD0805; Manufacturer Part Number 0805HT-47NTJLB
L40: 9.1nH_0805_0805HT-9N1TJLB; SMD0805; Manufacturer Part Number 0805HT-9N1TJLB
L41: 1.8nH_0805_0805HT-1N8TJLC; SMD0805; Manufacturer Part Number 0805HT-1N8TJLC
