myriadrf/LimeRFE/hardware/1v0/KiCAD/BPF920.sch

## KiCad design hardware/1v0/KiCAD/BPF920.sch (2020-02-29)

Schematic: BPF920.sch

Parts:
C373, C375: 1000pF_0402_GRM1555C1H102FA01D; SMD0402; Manufacturer Part Number GRM1555C1H102FA01D
U139: B39921B3728U410; Manufacturer Part Number B39921B3728U410
