myriadrf/LimeRFE/hardware/1v0/KiCAD/BPF1300.sch

## KiCad design hardware/1v0/KiCAD/BPF1300.sch (2020-02-29)

Schematic: BPF1300.sch

Parts:
C501, C502: 1000pF_0402_GRM1555C1H102GA01D; SMD0402; Manufacturer Part Number GRM1555C1H102GA01D
U70: BP0805A1308ASTR; Manufacturer Part Number BP0805A1308ASTR
