myriadrf/LimeRFE/hardware/1v0/KiCAD/BPF2400.sch

## KiCad design hardware/1v0/KiCAD/BPF2400.sch (2020-02-29)

Schematic: BPF2400.sch

Parts:
C505, C506: 1000pF_0402_GRM1555C1H102GA01D; SMD0402; Manufacturer Part Number GRM1555C1H102GA01D
U71: DEA252400BT-2030A1; Manufacturer Part Number DEA252400BT-2030A1
