myriadrf/LimeRFE/hardware/1v0/KiCAD/BPF3500.sch

## KiCad design hardware/1v0/KiCAD/BPF3500.sch (2020-02-29)

Schematic: BPF3500.sch

Parts:
C503, C504: 1000pF_0402_GRM1555C1H102GA01D; SMD0402; Manufacturer Part Number GRM1555C1H102GA01D
U72: 3600BP14M0600T; Manufacturer Part Number 3600BP14M0600T
