myriadrf/LimeRFE/hardware/1v0/KiCAD/CELL_LNA.sch

## KiCad design hardware/1v0/KiCAD/CELL_LNA.sch (2020-02-29)

Schematic: CELL_LNA.sch

Parts:
C73, C75, C76: 0.1uF_0402_Murata; SMD0402; Manufacturer Part Number GRM155R71C104JA88J
C74: 1uF_0402_GCM155C71A105KE38D; SMD0402; Manufacturer Part Number GCM155C71A105KE38D
L4: 18nH_0603_LQW18AN18NG00D; SMD0603; Manufacturer Part Number LQW18AN18NG00D
R88: 11K_0402_Panasonic; SMD0402; Manufacturer Part Number ERJ-2RKF1102X
R89: 33K_0402_Yageo; SMD0402; Manufacturer Part Number CR0402-JW-333GLF
U45: TQP3M9037; Manufacturer Part Number TQP3M9037
