myriadrf/LimeRFE/hardware/1v0/KiCAD/CELL_PREDRIVER.sch

## KiCad design hardware/1v0/KiCAD/CELL_PREDRIVER.sch (2020-02-29)

Schematic: CELL_PREDRIVER.sch

Parts:
C112, C114, C116: 1000pF_0402_Murata; SMD0402; Manufacturer Part Number GCM1555C1H102JA16J
C115: 100pF_0402_Murata; SMD0402; Manufacturer Part Number GCM1555C1H101JA16D
C286, C287: 0.1uF_0402_Murata; SMD0402; Manufacturer Part Number GRM155R71C104JA88J
C288: 10uF_0805_TMK212BBJ106MG-T; SMD0805; Manufacturer Part Number TMK212BBJ106MG-T
L5: 82nH_0805_LQW2BAS82NJ00L; SMD0805; Manufacturer Part Number LQW2BAS82NJ00L
R194: 10K_0402_Yageo; SMD0402; Manufacturer Part Number RC0402JR-7D10KL
U57: RFGA2054; SOT89_RFGA2054; Manufacturer Part Number RFGA2054TR13
U105: NCP331SNT1G; TSOP-6; Manufacturer Part Number NCP331SNT1G

Notes on the sheet:
SWITCH
