myriadrf/LimeRFE/hardware/1v0/KiCAD/Cell.sch

## KiCad design hardware/1v0/KiCAD/Cell.sch (2020-02-29)

Schematic: Cell.sch

Parts:
C274, C277, C361, C363, C364, C365, C368, C489: 100pF_0402_GCM1555C1H101JA16D; SMD0402; Manufacturer Part Number GCM1555C1H101JA16D
C282, C285, C360, C374: 1000pF_0402_Murata; SMD0402; Manufacturer Part Number GCM1555C1H102JA16J
C359, C362, C369: 100nF_0402_GRM155R71C104KA88J; SMD0402; Manufacturer Part Number GRM155R71C104KA88J
L3: 10nH_0402_LQW15AN10NG0ZD; SMD0402; Manufacturer Part Number LQW15AN10NG0ZD
L83: 33nH_0402_LQG15HS33NJ02D; SMD0402; Manufacturer Part Number LQG15HS33NJ02D
L84, L86: 5.1nH_0402_LQG15HS5N1S02D; SMD0402; Manufacturer Part Number LQG15HS5N1S02D
L85: 12nH_0402_LQG15HS12NH02D; SMD0402; Manufacturer Part Number LQG15HS12NH02D
P44, P50, P56, P57, P59, P64, P67, P69, P74: probe_v1
R211: 0R_0603_RCS06030000Z0EA; SMD0603; Manufacturer Part Number RCS06030000Z0EA
U33, U37: SKYA21003; SKYA21003_12QFN; Manufacturer Part Number SKYA21003
U34: B39202B9477P810; Manufacturer Part Number B39202B9477P810
U35, U44, U86, U126: SKY13416-485LF; 14QFN_SKY13416-485LF; Manufacturer Part Number SKY13416-485LF
U36, U99: SKY13414-485LF; 14QFN_SKY13414-485LF; Manufacturer Part Number SKY13414-485LF
U39: QPQ1297; Manufacturer Part Number QPQ1297TR7
U40: TQM963014; Manufacturer Part Number TQM963014
U41: QPQ1282; Manufacturer Part Number QPQ1282TR7
U42: TQQ6107; Manufacturer Part Number TQQ6107
U43: 885026; Manufacturer Part Number 885026
U76, U118, U119: 74LV164D,118; Manufacturer Part Number 74LV164D,118
U127, U129: SN74LV1T04; Manufacturer Part Number SN74LV1T04DCKRG4
U128: SKY13370-374LF; SKY13370-374LF_6QFN; Manufacturer Part Number SKY13370-374LF
U131: F6QA1G842M2AN-J; Manufacturer Part Number F6QA1G842M2AN-J
U132: B39212B9451P810; Manufacturer Part Number B39212B9451P810
U136: F6QA2G655M2QH-J; Manufacturer Part Number F6QA2G655M2QH-J
U160: MADL-011021-14150T; Manufacturer Part Number MADL-011021-14150T
U161: PAT1220-C-3DB-T5; Manufacturer Part Number PAT1220-C-3DB-T5
