myriadrf/LimeRFE/hardware/1v0/KiCAD/FAN.sch

## KiCad design hardware/1v0/KiCAD/FAN.sch (2020-02-29)

Schematic: FAN.sch

Parts:
C203: 1uF_0603_TMK107BJ105KA-T; SMD0603; Manufacturer Part Number TMK107BJ105KA-T
C214, C225: 1nF_0603_06035C102KAT2A; SMD0603; Manufacturer Part Number 06035C102KAT2A
P1: FAN_CONN_3; Manufacturer Part Number 53398-0371 (0533980371)
R1: 330R_0603_CRGCQ0603J330R; SMD0603; Manufacturer Part Number CRGCQ0603J330R
R216: NF_SMD_0402; SMD0402; Manufacturer Part Number _
R235: 0R_0402_Yageo; SMD0402; Manufacturer Part Number RC0402JR-070RL
U110: TPS22810DBVR; SOT23_TPS22810DBVR; Manufacturer Part Number TPS22810DBVR

Notes on the sheet:
FAN POWER
