myriadrf/LimeRFE/hardware/1v0/KiCAD/GPIO_Subsystem.sch

## KiCad design hardware/1v0/KiCAD/GPIO_Subsystem.sch (2020-02-29)

Schematic: GPIO_Subsystem.sch

Parts:
C32: 100uF_25V_EEE-1EA101UP; EEE-HC1E101P; Manufacturer Part Number EEE-1EA101UP
C33, C34, C36, C38, C40, C42, C44, C46, C49, C50: 1uF_0603_TMK107BJ105KA-T; SMD0603; Manufacturer Part Number TMK107BJ105KA-T
C35, C37, C39, C41, C43, C45, C47, C48, C51: C1206C104K5RAC7800; SMD1206; Manufacturer Part Number C1206C104K5RAC7800
D10, D11, D13, D14: LED0603_GREEN; LED_0603; Manufacturer Part Number SML-D12M1WT86
D12: GSOT03-E3-08; Manufacturer Part Number GSOT03-E3-08
J12: M50-3600542; PIN_HEADER_2X5; Manufacturer Part Number M50-3600542
J13: TSM-104-04-T-DV; Manufacturer Part Number TSM-104-04-T-DV
J14: TSM-102-04-T-SV; Manufacturer Part Number 200-TSM10204TSV
J15: Screw_Terminal_1x02; CONN_1757242; Manufacturer Part Number 1757242
J16: Screw_Terminal_1x08; CONN_1757307; Manufacturer Part Number 1757307
J22: TSM-103-04-L-SV; Manufacturer Part Number TSM-103-04-L-SV
J38: Jumper_SNM-100-BK-T; SNM-100-BK-T; Manufacturer Part Number SNM-100-BK-T
Q3, Q4, Q5, Q6: BC847; BC817_SOT-23; Manufacturer Part Number BC847C,215
R42, R43, R44, R45: NF_SMD_0402; SMD0402; Manufacturer Part Number _
R46, R47, R50, R51: 47K_0603; SMD0603; Manufacturer Part Number RT0603FRD0747KL
R48, R49, R52, R53: 220R_0603; SMD0603; Manufacturer Part Number RT0603DRD07220RL
R54, R55, R56, R57: 0R_0603_RCS06030000Z0EA; SMD0603; Manufacturer Part Number RCS06030000Z0EA
R58, R59, R60, R61: 10K_0603; SMD0603; Manufacturer Part Number RT0603FRD0710KL
SW2: ADE04S04; Manufacturer Part Number ADE04S04
U23, U24, U25, U26: 74LVC1T45; Manufacturer Part Number SN74LVC1T45DCKRG4
U27, U28: ULN2003D1013TR; Manufacturer Part Number ULN2003D1013TR

Notes on the sheet:
5v5 input max
Jumper connected VDDA=VDD_CON DONOT Connect when VDDA <> VDD_CON (For use in relay only mode)
TVS to clamp in case of VDDA = VDD_CON from the lime SDR board
