myriadrf/LimeRFE/hardware/1v0/KiCAD/HF_BANK.sch

## KiCad design hardware/1v0/KiCAD/HF_BANK.sch (2020-02-29)

Schematic: HF_BANK.sch

Parts:
U121: EE2-5NU-L; Manufacturer Part Number EE2-5NU-L
U138: DRDC3105F-7; DRDC3105F-7_SOT23; Manufacturer Part Number DRDC3105F-7

Notes on the sheet:
CHECK CTRL
