myriadrf/LimeRFE/hardware/1v0/KiCAD/LNA_H.sch

## KiCad design hardware/1v0/KiCAD/LNA_H.sch (2020-02-29)

Schematic: LNA_H.sch

Parts:
C158, C160, C161: 100nF_0402_GRM155R71C104KA88J; SMD0402; Manufacturer Part Number GRM155R71C104KA88J
C159: 1000pF_0402_GRM1555C1H102GA01D; SMD0402; Manufacturer Part Number GRM1555C1H102GA01D
C162: 30pF_0402_GJM1555C1H300FB01D; SMD0402; Manufacturer Part Number GJM1555C1H300FB01D
FB9: FB_600R_0805_MPZ2012S601AT000; SMD0805; Manufacturer Part Number MPZ2012S601AT000
L42: 56nH_0402_LQG15HS56NJ02D; SMD0402; Manufacturer Part Number LQG15HS56NJ02D
L43: 270nH_0402_LQG15HSR27J02D; SMD0402; Manufacturer Part Number LQG15HSR27J02D
R141, R144, R145, R146: NF_SMD_0603; SMD0603; Manufacturer Part Number _
R142, R147: 0R_0603_RCS06030000Z0EA; SMD0603; Manufacturer Part Number RCS06030000Z0EA
R143: 1k_0402; SMD0603; Manufacturer Part Number RC0402FR-7W1KL
U73: NCP331SNT1G; TSOP-6; Manufacturer Part Number NCP331SNT1G
U74: ADL5611ARKZ-R7; SOT89_ADL5611ARKZ-R7; Manufacturer Part Number ADL5611ARKZ-R7
