myriadrf/LimeRFE/hardware/1v0/KiCAD/LNA_L.sch

## KiCad design hardware/1v0/KiCAD/LNA_L.sch (2020-02-29)

Schematic: LNA_L.sch

Parts:
C121, C123, C125: 100nF_0402_GRM155R71C104KA88J; SMD0402; Manufacturer Part Number GRM155R71C104KA88J
C122, C124, C126: 1uF_0402_GCM155C71A105KE38D; SMD0402; Manufacturer Part Number GCM155C71A105KE38D
FB8: FB_600R_0805_MPZ2012S601AT000; SMD0805; Manufacturer Part Number MPZ2012S601AT000
L6, L7: 10u_0805; SMD0805; Manufacturer Part Number MLZ2012M100WT000
R119, R121, R125: 0R_0603_RCS06030000Z0EA; SMD0603; Manufacturer Part Number RCS06030000Z0EA
R120, R122, R123: NF_SMD_0603; SMD0603; Manufacturer Part Number _
R124: 10K_0402_Yageo; SMD0402; Manufacturer Part Number RC0402JR-7D10KL
U65: NCP331SNT1G; TSOP-6; Manufacturer Part Number NCP331SNT1G
U66: GALI-74+; SOT89; Manufacturer Part Number GALI-74+
