myriadrf/LimeRFE/hardware/1v0/KiCAD/LPF30.sch

## KiCad design hardware/1v0/KiCAD/LPF30.sch (2020-02-29)

Schematic: LPF30.sch

Parts:
C465: 68pF_0402_GCM1555C1H680JA16J; SMD0402; Manufacturer Part Number GCM1555C1H680JA16J
C466: 15pF_0402_GJM1555C1H150JB01D; SMD0402; Manufacturer Part Number GJM1555C1H150JB01D
C467, C469: 120pF_0603_GRM1885C2A121JA01D; SMD0603; Manufacturer Part Number GRM1885C2A121JA01D
C468: 20pF_0402_GJM1555C1H200GB01D; SMD0402; Manufacturer Part Number GJM1555C1H200GB01D
C470: 4.3pF_0402_GCM1555C1H4R3CA16D; SMD0402; Manufacturer Part Number GCM1555C1H4R3CA16D
C471: 82pF_0603_GCM1555C1H820JA16D; SMD0603; Manufacturer Part Number GCM1555C1H820JA16D
L104: 220nH_0805_0805HP-221XGRB; SMD0805; Manufacturer Part Number 0805HP-221XGRB
L105: 180nH_0805_0805HP-181XGRB; SMD0805; Manufacturer Part Number 0805HP-181XGRB
L106: 56nH_0805_0805HP-56NXGRB; SMD0805; Manufacturer Part Number 0805HP-56NXGRB
L107: 150nH_0805_0805HP-151XGRB; SMD0805; Manufacturer Part Number 0805HP-151XGRB
L108: 82nH_0805_0805HP-82NXJRB; SMD0805; Manufacturer Part Number 0805HP-82NXJRB
R131, R132: 0R_0805; SMD0805; Manufacturer Part Number RCS08050000Z0EA
R374, R375: 0RNF_0805_Yageo; SMD0805; Manufacturer Part Number RC0805JR-070RL
