myriadrf/LimeRFE/hardware/1v0/KiCAD/LPF70.sch

## KiCad design hardware/1v0/KiCAD/LPF70.sch (2020-02-29)

Schematic: LPF70.sch

Parts:
C410, C413: 27pF_0402_GCM1555C1H270FA16D; SMD0402; Manufacturer Part Number GCM1555C1H270FA16D
C411: 22pF_0402_CC0402JRNPO9BN220; SMD0402; Manufacturer Part Number CC0402JRNPO9BN220
C412: 56pF_0402_GCM1555C1H560JA16D; SMD0402; Manufacturer Part Number GCM1555C1H560JA16D
C414: 68pF_0402_GCM1555C1H680FA16J; SMD0402; Manufacturer Part Number GCM1555C1H680FA16J
C415: 8.1pF_0402_GJM1555C1H8R1BB01D; SMD0402; Manufacturer Part Number GJM1555C1H8R1BB01D
C416: 47pF_0402_GCQ1555C1H470JB01D; SMD0402; Manufacturer Part Number GCQ1555C1H470JB01D
L89, L90: 72nH_0603_0603HP-72NXGLU; SMD0603; Manufacturer Part Number 0603HP-72NXGLU
L91: 100nH_0603_0603HP-R10XJLU; SMD0603; Manufacturer Part Number 0603HP-R10XJLU
R275, R276: 0R_0402_RC0402JR-070RL; SMD0402; Manufacturer Part Number RC0402JR-070RL
