myriadrf/LimeRFE/hardware/1v0/KiCAD/LPF220.sch

## KiCad design hardware/1v0/KiCAD/LPF220.sch (2020-02-29)

Schematic: LPF220.sch

Parts:
C403: 9.2pF_0402_GJM1555C1H9R2BB01D; SMD0402; Manufacturer Part Number GJM1555C1H9R2BB01D
C404: 5.7pF_0402_GRM1555C1H5R7BA01D; SMD0402; Manufacturer Part Number GRM1555C1H5R7BA01D
C405: 12pF_0402_GCQ1555C1H120FB01D; SMD0402; Manufacturer Part Number GCQ1555C1H120FB01D
C406: 7.8pF_0402_GRM0225C1E7R8DA03L; SMD0402; Manufacturer Part Number GRM0225C1E7R8DA03L
C407: 15pF_0402_GCQ1555C1H150FB01D; SMD0402; Manufacturer Part Number GCQ1555C1H150FB01D
C408: 1pF_0402_GCQ1555C1H1R0BB01D; SMD0402; Manufacturer Part Number 81-GCQ1555C1H1R0BB1D
C409: 9.6pF_0402_GCQ1555C1H9R6BB01D; SMD0402; Manufacturer Part Number GCQ1555C1H9R6BB01D
L31: 27nH_0603_0603HP-27NXJLW; SMD0603; Manufacturer Part Number 0603HP-27NXJLW
L87: 24nH_0603_0603HP-24NXGLU; SMD0603; Manufacturer Part Number 0603HP-24NXGLU
L88: 39nH_0603_0603HP-39NXGLU; SMD0603; Manufacturer Part Number 0603HP-39NXGLU
R273, R274: 0R_0402_RC0402JR-070RL; SMD0402; Manufacturer Part Number RC0402JR-070RL
