myriadrf/LimeRFE/hardware/1v0/KiCAD/LPF225.sch

## KiCad design hardware/1v0/KiCAD/LPF225.sch (2020-02-29)

Schematic: LPF225.sch

Parts:
C164: 7pF_0402_GJM1555C1H7R0WB01D; SMD0402; Manufacturer Part Number GJM1555C1H7R0WB01D
C165, C168: 12pF_0402_GCQ1555C1H120GB01D; SMD0402; Manufacturer Part Number GCQ1555C1H120GB01D
C166: 20pF_0402_GJM1555C1H200FB01D; SMD0402; Manufacturer Part Number GJM1555C1H200FB01D
C167: 3.6pF_0402_GJM1555C1H3R6WB01D; SMD0402; Manufacturer Part Number GJM1555C1H3R6WB01D
L44: 27nH_0805; SMD0805; Manufacturer Part Number 0805HQ-27NXGLB
L45: 22nH_0805; SMD0805; Manufacturer Part Number 0805HT-22NTJLB
L46: 18nH_0805; SMD0805; Manufacturer Part Number 0805HT-18NTJLB
R155, R156: 0R_0603; SMD0603; Manufacturer Part Number RCS06030000Z0EA
