myriadrf/LimeRFE/hardware/1v0/KiCAD/LPF435.sch

## KiCad design hardware/1v0/KiCAD/LPF435.sch (2020-02-29)

Schematic: LPF435.sch

Parts:
C169: 3pF_0402_GJM1555C1H3R0BB01D; SMD0402; Manufacturer Part Number GJM1555C1H3R0BB01D
C170, C173: 4.7pF_0402_GJM1555C1H4R7CB01D; SMD0402; Manufacturer Part Number GJM1555C1H4R7CB01D
C171: 8pF_0402_GCM1555C1H8R0BA16D; SMD0402; Manufacturer Part Number GCM1555C1H8R0BA16D
C172: 1.5pF_0402_GJM1555C1H1R5CB01D; SMD0402; Manufacturer Part Number GJM1555C1H1R5CB01D
L47: 10nH_0805_0805HT-10NTJLC; SMD0805; Manufacturer Part Number 0805HT-10NTJLC
L48: 15nH_0805_0805HT-15NTJLB; SMD0805; Manufacturer Part Number 0805HT-15NTJLB
R157, R158: 0R_0603_RCS06030000Z0EA; SMD0603; Manufacturer Part Number RCS06030000Z0EA
