myriadrf/LimeRFE/hardware/1v0/KiCAD/LPF920.sch

## KiCad design hardware/1v0/KiCAD/LPF920.sch (2020-02-29)

Schematic: LPF920.sch

Parts:
R262, R272: 0R_0402_RC0402JR-070RL; SMD0402; Manufacturer Part Number RC0402JR-070RL
U146: 0915LP15B026E; Manufacturer Part Number 0915LP15B026E
