myriadrf/LimeRFE/hardware/1v0/KiCAD/LPF1280.sch

## KiCad design hardware/1v0/KiCAD/LPF1280.sch (2020-02-29)

Schematic: LPF1280.sch

Parts:
R245, R246: 0R_0603_RCS06030000Z0EA; SMD0603; Manufacturer Part Number RCS06030000Z0EA
U84: LFCN-1450+; Manufacturer Part Number LFCN-1450+
