myriadrf/LimeRFE/hardware/1v0/KiCAD/LPF2400.sch

## KiCad design hardware/1v0/KiCAD/LPF2400.sch (2020-02-29)

Schematic: LPF2400.sch

Parts:
R151, R152: 0R_0603_RCS06030000Z0EA; SMD0603; Manufacturer Part Number RCS06030000Z0EA
U95: 2450LP14B100T; Manufacturer Part Number 2450LP14B100T
