myriadrf/LimeRFE/hardware/1v0/KiCAD/LPF3500.sch

## KiCad design hardware/1v0/KiCAD/LPF3500.sch (2020-02-29)

Schematic: LPF3500.sch

Parts:
R153, R154: 0R_0603_RCS06030000Z0EA; SMD0603; Manufacturer Part Number RCS06030000Z0EA
U96: DEA163800LT-5017C1; Manufacturer Part Number DEA163800LT-5017C1
