myriadrf/LimeRFE/hardware/1v0/KiCAD/Lime_RFE.sch

## KiCad design hardware/1v0/KiCAD/Lime_RFE.sch (2020-02-29)

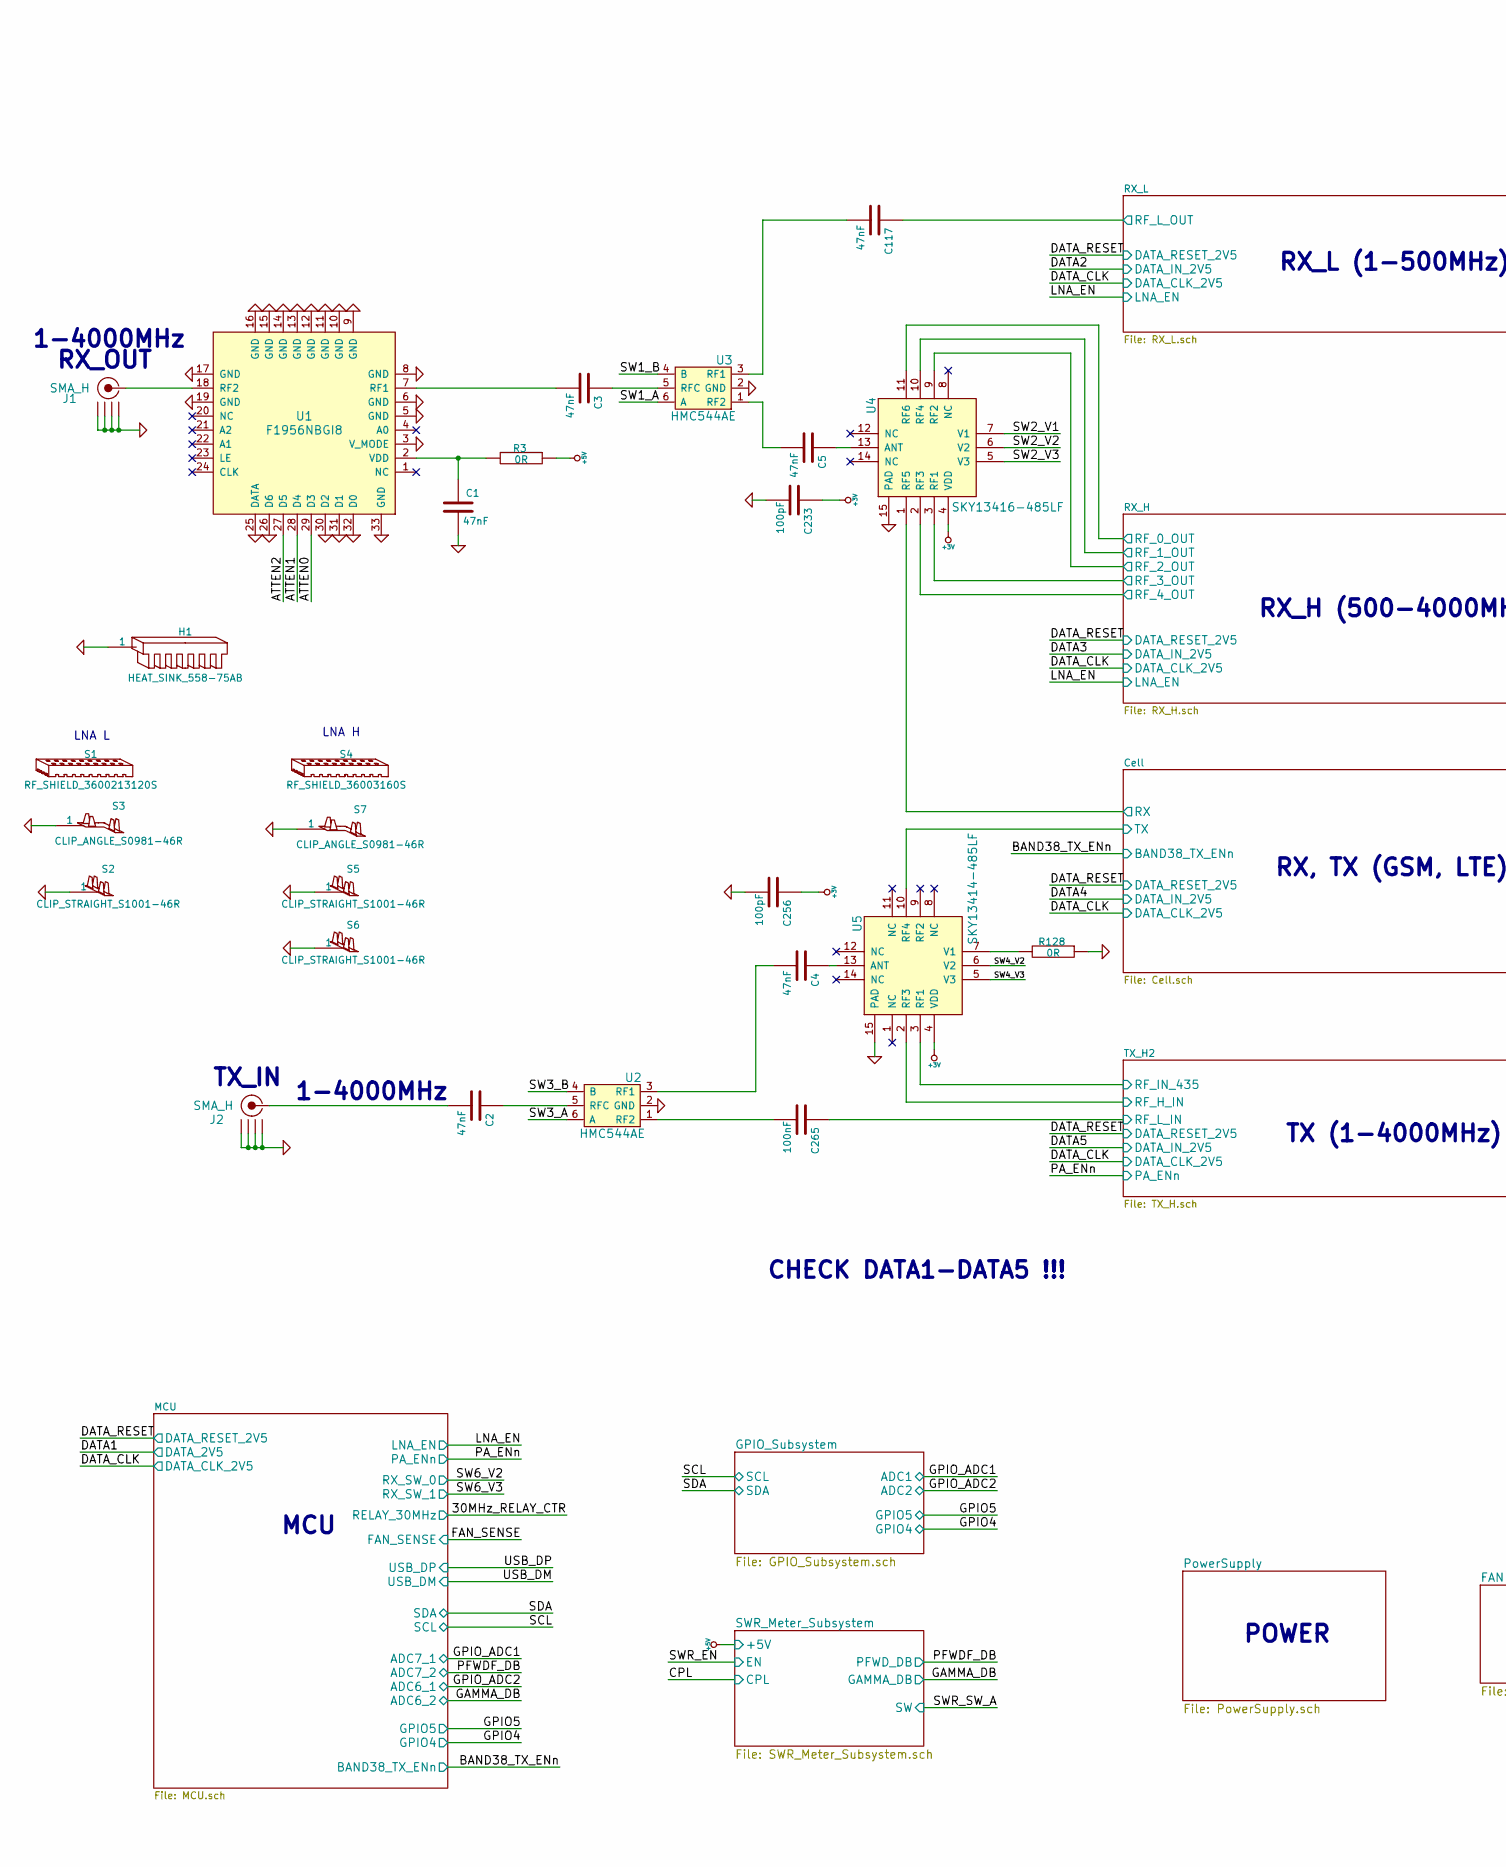
[picture p439: schematic Lime_RFE.sch, part in row 1, column 1]

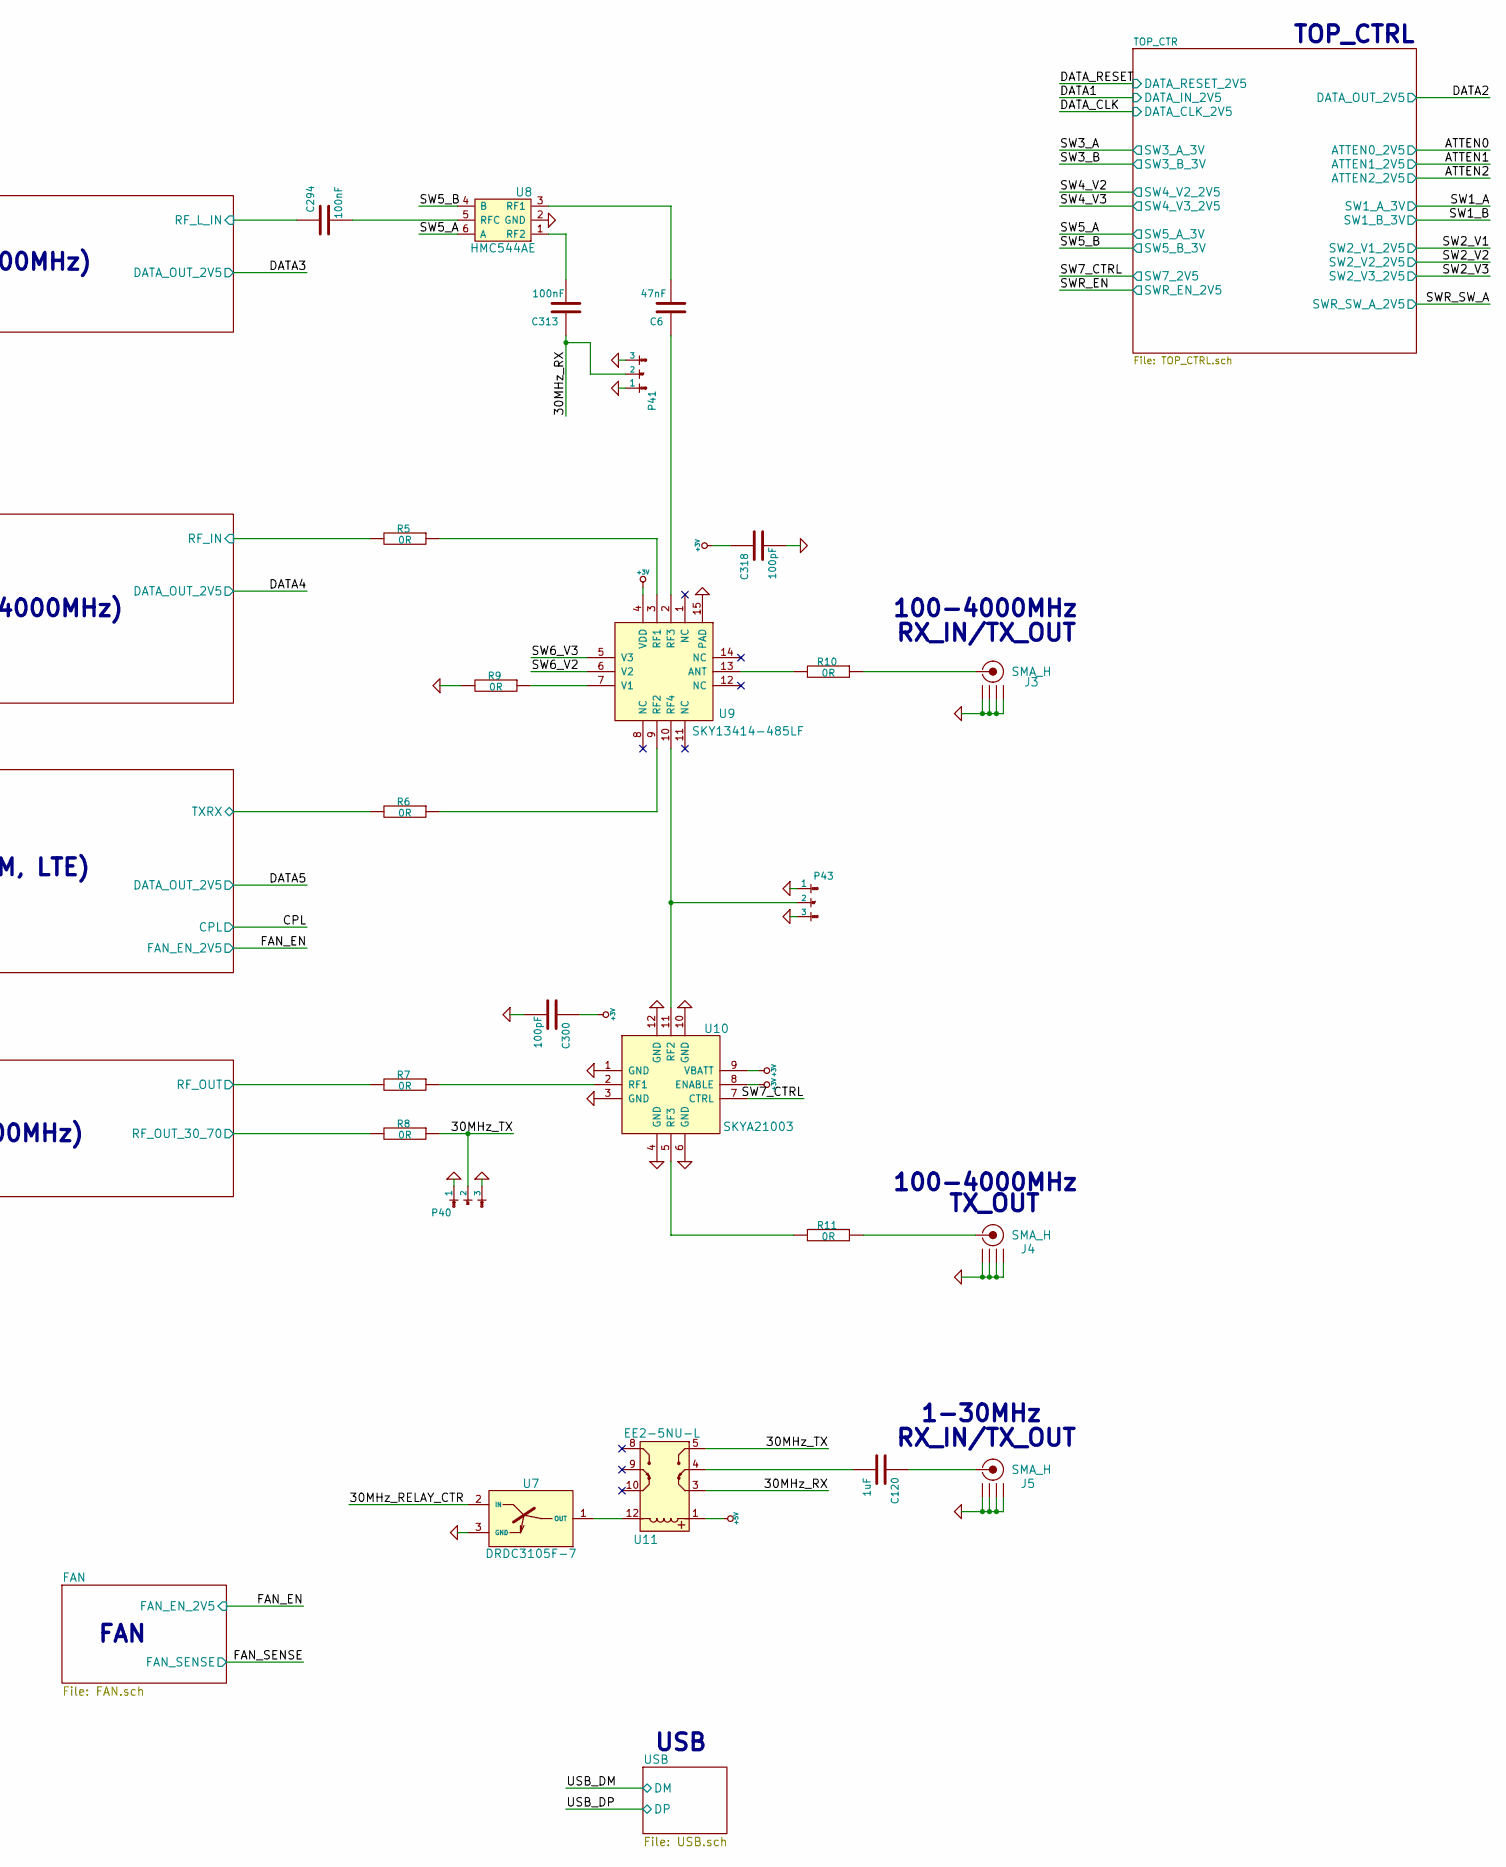
[picture p440: schematic Lime_RFE.sch, part in row 1, column 2]

Parts:
C1, C2, C3, C4, C5, C6, C117: 47nF_0402_GCM155R71H473KE02D; SMD0402; Manufacturer Part Number GCM155R71H473KE02D
C120: 1uF_0603_Yageo; SMD0603; Manufacturer Part Number CC0603KRX7R9BB105
C233, C256, C300, C318: 100pF_0402_GCM1555C1H101JA16D; SMD0402; Manufacturer Part Number GCM1555C1H101JA16D
C265, C294, C313: 100nF_0603_C0603C104M5RACTU; SMD0603; Manufacturer Part Number C0603C104M5RACTU
H1: HEAT_SINK_558-75AB; Manufacturer Part Number 558-75AB
J1, J2, J3, J4, J5: SMA_H_v3; SMA_v2; Manufacturer Part Number CON-SMA-EDGE-S
P40, P41, P43: probe_v1
R3: 0R_0402_RCS04020000Z0ED; SMD0402; Manufacturer Part Number RCS04020000Z0ED
R5, R6, R7, R8, R9, R10, R11, R128: 0R_0603_RCS06030000Z0EA; SMD0603; Manufacturer Part Number RCS06030000Z0EA
S1: RF_SHIELD_3600213120S; Manufacturer Part Number 3600213120S
S2, S5, S6: CLIP_STRAIGHT_S1001-46R; Manufacturer Part Number S1001-46R
S3, S7: CLIP_ANGLE_S0981-46R; Manufacturer Part Number S0981-46R
S4: RF_SHIELD_36003160S; Manufacturer Part Number 36003160S
U1: F1956NBGI8; Manufacturer Part Number F1956NBGI8
U2, U3, U8: HMC544AE; Manufacturer Part Number HMC544AE
U4: SKY13416-485LF; 14QFN_SKY13416-485LF; Manufacturer Part Number SKY13416-485LF
U5, U9: SKY13414-485LF; 14QFN_SKY13414-485LF; Manufacturer Part Number SKY13414-485LF
U7: DRDC3105F-7; DRDC3105F-7_SOT23; Manufacturer Part Number DRDC3105F-7
U10: SKYA21003; SKYA21003_12QFN; Manufacturer Part Number SKYA21003
U11: EE2-5NU-L; Manufacturer Part Number EE2-5NU-L

Connections:
30MHz_RELAY_CTR: U7.2 (IN)
30MHz_RX: C313.1, P41.2, U11.3
30MHz_TX: P40.2, R8.1, U11.5
+3V: C233.1, C256.1, C300.1, C318.1, U4.4 (VDD), U5.4 (VDD), U9.4 (VDD), U10.8 (ENABLE), U10.9 (VBATT)
+5V: R3.1, U11.1
ATTEN0: U1.29 (D3)
ATTEN1: U1.28 (D4)
ATTEN2: U1.27 (D5)
GND: C1.2, C233.2, C256.2, C300.2, C318.2, H1.1, J1.2 (GND1), J1.3 (GND2), J1.4 (GND3), J1.5 (GND4), J2.2 (GND1), J2.3 (GND2), J2.4 (GND3), J2.5 (GND4), J3.2 (GND1), J3.3 (GND2), J3.4 (GND3), J3.5 (GND4), J4.2 (GND1), J4.3 (GND2), J4.4 (GND3), J4.5 (GND4), J5.2 (GND1), J5.3 (GND2), J5.4 (GND3), J5.5 (GND4), P40.1, P40.3, P41.1, P41.3, P43.1, P43.3, R9.2, R128.1, S2.1, S3.1, S5.1, S6.1, S7.1, U1.3 (V_MODE), U1.5 (GND), U1.6 (GND), U1.8 (GND), U1.9 (GND), U1.10 (GND), U1.11 (GND), U1.12 (GND), U1.13 (GND), U1.14 (GND), U1.15 (GND), U1.16 (GND), U1.17 (GND), U1.19 (GND), U1.25 (DATA), U1.26 (D6), U1.30 (D2), U1.31 (D1), U1.32 (D0), U1.33 (GND), U2.2 (GND), U3.2 (GND), U4.15 (PAD), U5.15 (PAD), U7.3 (GND), U8.2 (GND), U9.15 (PAD), U10.1 (GND), U10.3 (GND), U10.4 (GND), U10.6 (GND), U10.10 (GND), U10.12 (GND)
unnamed: C1.1, R3.2, U1.2 (VDD)
unnamed: C2.1, U2.5 (RFC)
unnamed: C2.2, J2.1 (RF)
unnamed: C3.1, U3.5 (RFC)
unnamed: C3.2, U1.7 (RF1)
unnamed: C4.1, U5.13 (ANT)
unnamed: C4.2, U2.3 (RF1)
unnamed: C5.1, U4.13 (ANT)
unnamed: C5.2, U3.1 (RF2)
unnamed: C6.1, U9.2 (RF3)
unnamed: C6.2, U8.3 (RF1)
unnamed: C117.2, U3.3 (RF1)
unnamed: C120.1, J5.1 (RF)
unnamed: C120.2, U11.4
unnamed: C265.2, U2.1 (RF2)
unnamed: C294.2, U8.5 (RFC)
unnamed: C313.2, U8.1 (RF2)
unnamed: J1.1 (RF), U1.18 (RF2)
unnamed: J3.1 (RF), R10.1
unnamed: J4.1 (RF), R11.1
unnamed: P43.2, U9.10 (RF4), U10.11 (RF2)
unnamed: R5.1, U9.3 (RF1)
unnamed: R6.1, U9.9 (RF2)
unnamed: R7.1, U10.2 (RF1)
unnamed: R9.1, U9.7 (V1)
unnamed: R10.2, U9.13 (ANT)
unnamed: R11.2, U10.5 (RF3)
unnamed: R128.2, U5.7 (V1)
unnamed: U7.1 (OUT), U11.12
RF_0_OUT: U4.11 (RF6)
RF_1_OUT: U4.10 (RF4)
RF_2_OUT: U4.9 (RF2)
RF_3_OUT: U4.3 (RF1)
RF_4_OUT: U4.2 (RF3)
RF_H_IN: U5.2 (RF3)
RF_IN: R5.2
RF_IN_435: U5.3 (RF1)
RF_L_IN: C265.1, C294.1
RF_L_OUT: C117.1
RF_OUT: R7.2
RF_OUT_30_70: R8.2
RX: U4.1 (RF5)
SW1_A: U3.6 (A)
SW1_B: U3.4 (B)
SW2_V1: U4.7 (V1)
SW2_V2: U4.6 (V2)
SW2_V3: U4.5 (V3)
SW3_A: U2.6 (A)
SW3_B: U2.4 (B)
SW4_V2: U5.6 (V2)
SW4_V3: U5.5 (V3)
SW5_A: U8.6 (A)
SW5_B: U8.4 (B)
SW6_V2: U9.6 (V2)
SW6_V3: U9.5 (V3)
SW7_CTRL: U10.7 (CTRL)
TX: U5.10 (RF4)
TXRX: R6.2

Notes on the sheet:
MCU
RX_IN/TX_OUT
TX (1-4000MHz)
TX_OUT
TX_IN
RX_H (500-4000MHz)
RX_OUT
USB
POWER
100-4000MHz
1-30MHz
1-4000MHz
RX, TX (GSM, LTE)
RX_L (1-500MHz)
TOP_CTRL
FAN
CHECK DATA1-DATA5 !!!
LNA L
LNA H
