myriadrf/LimeRFE/hardware/1v0/KiCAD/MCU.sch

## KiCad design hardware/1v0/KiCAD/MCU.sch (2020-02-29)

Schematic: MCU.sch

Parts:
C7, C10, C11, C13: 1uF_0603_TMK107BJ105KA-T; SMD0603; Manufacturer Part Number TMK107BJ105KA-T
C8: 4.7uF_0402_GRM155R60J475ME87D; SMD0402; Manufacturer Part Number GRM155R60J475ME87D
C9, C12, C14, C189: 100nF_0402_GRM155R71C104KA88J; SMD0402; Manufacturer Part Number GRM155R71C104KA88J
D1: LED0603_RED; LED_0603; Manufacturer Part Number SML-D12U1WT86
D2: LED0603_GREEN; LED_0603; Manufacturer Part Number SML-D12M1WT86
FB2: 10uH_0603_TDK; SMD0603; Manufacturer Part Number MLZ1608E100MT
J6, J7: TSM-103-04-L-SV; Manufacturer Part Number TSM-103-04-L-SV
J8: TSM-103-04-F-DV; Manufacturer Part Number TSM-103-04-F-DV
J34, J35: Jumper_SNM-100-BK-T; SNM-100-BK-T; Manufacturer Part Number SNM-100-BK-T
Q1, Q2, Q7, Q8: BSN20; Manufacturer Part Number BSN20-7
R2, R19, R20, R21, R22, R186, R187, R188: 2k2_0402_ERJ-2RKF2201X; SMD0402; Manufacturer Part Number ERJ-2RKF2201X
R4, R24, R192: 0R_0402_RCS04020000Z0ED; SMD0402; Manufacturer Part Number RCS04020000Z0ED
R13, R14, R15, R16, R17: 1K_0402_CRGP0402F1K0; SMD0402; Manufacturer Part Number CRGP0402F1K0
R18: 10K_0402_Yageo; SMD0402; Manufacturer Part Number RC0402JR-7D10KL
R23, R191: NF_0R_0402_RCS04020000Z0ED; SMD0402; Manufacturer Part Number RCS04020000Z0ED
R100: 0RNF_0402_RC0402JR-070RL; SMD0402; Manufacturer Part Number RC0402JR-070RL
SW1: SW_PUSH; B3U-1000P; Manufacturer Part Number B3U-1000P
U12: ATMEGA328P-AU; Manufacturer Part Number ATMEGA328P-AUR
U13: FT232RL; Manufacturer Part Number FT232RL-REEL
U14: SN74LV1T04; Manufacturer Part Number SN74LV1T04DCKRG4
U15, U16, U104, U108: SN74LV1T34; Manufacturer Part Number Texas Instruments
X1: CSTNE16M0V530000R0; Manufacturer Part Number CSTNE16M0V530000R0

Notes on the sheet:
MCU
USB 2 SERIAL
RESET
ICSP
