myriadrf/LimeRFE/hardware/1v0/KiCAD/Notch.sch

## KiCad design hardware/1v0/KiCAD/Notch.sch (2020-02-29)

Schematic: Notch.sch

Parts:
C127, C133: 15pF_0402_GJM1555C1H150FB01D; SMD0402; Manufacturer Part Number GJM1555C1H150FB01D
C128, C132: 56pF_0402_GRM1555C1H560GA01D; SMD0402; Manufacturer Part Number GRM1555C1H560GA01D
C129, C131: 27pF_0402_04025U270GAT2A; SMD0402; Manufacturer Part Number 04025U270GAT2A
C130: 51pF_0402_GRM1555C1H510JA01D; SMD0402; Manufacturer Part Number GRM1555C1H510JA01D
C134: 2200pF_0603_GRM1885C1H222GA01D; SMD0603; Manufacturer Part Number GRM1885C1H222GA01D
C135: 4700pF_0603_GRM1887U1H472JA01D; SMD0603; Manufacturer Part Number GRM1887U1H472JA01D
C136, C138: 1000pF_0402_GRM1555C1H102GA01D; SMD0402; Manufacturer Part Number GRM1555C1H102GA01D
C137: 3300pF_0402_GRM155R71H332JA01D; SMD0402; Manufacturer Part Number GRM155R71H332JA01D
C139: 15000pF_0603_06035C153KAT2A; SMD0603; Manufacturer Part Number 06035C153KAT2A
C140: 1500pF_0603_GRM1885C1H152JA01D; SMD0603; Manufacturer Part Number GRM1885C1H152JA01D
L8, L15: 180nH_0805; SMD0805; Manufacturer Part Number 0805HP-181XGRB
L9, L16: 12nH_0805; SMD0805; Manufacturer Part Number 0805HP-12NXGRB
L10, L14: 47nH_0805; SMD0805; Manufacturer Part Number 0805HP-47NXGRB
L11, L13: 100nH_0805; SMD0805; Manufacturer Part Number 0805HP-101XGRB
L12: 56nH_0805; SMD0805; Manufacturer Part Number 0805HP-56NXGRB
L18, L21, L24: 1.8uH_1008; SMD1008_inductor; Manufacturer Part Number 1008LS-182XJLB
L19, L22: 2.2uH_1008; SMD1008_inductor; Manufacturer Part Number 1008LS-222XJLB
L25: 1.2uH_1008; SMD1008_inductor; Manufacturer Part Number 1008LS-122XJLB
R126, R127: 0R_0603_RCS06030000Z0EA; SMD0603; Manufacturer Part Number RCS06030000Z0EA
