myriadrf/LimeRFE/hardware/1v0/KiCAD/PA30.sch

## KiCad design hardware/1v0/KiCAD/PA30.sch (2020-02-29)

Schematic: PA30.sch

Parts:
C99, C311: 1nF_0603_06035C102KAT2A; SMD0603; Manufacturer Part Number 06035C102KAT2A
C208: 100uF_25V_Tantalum_AVX; TAJE107M025SNJV; Manufacturer Part Number TAJE107M025SNJV
C209, C341: 1uF_0805; SMD0805; Manufacturer Part Number VJ0805Y105KXXTW1BC
C210, C223, C241, C242, C301, C304, C308, C335: 100nF_0603_C0603C104M5RACTU; SMD0603; Manufacturer Part Number C0603C104M5RACTU
C219, C220: 91pF_0805; SMD0805; Manufacturer Part Number C0805C910K4HACTU
C243: 100nF_0805_08055C104KAT2A; SMD0805; Manufacturer Part Number 08055C104KAT2A
C317: 1uF_0603_TMK107BJ105KA-T; SMD0603; Manufacturer Part Number TMK107BJ105KA-T
D22: ZENER_Diode_5.09V_CDZFHT2RA5.1B; VMN2; Manufacturer Part Number CDZFHT2RA5.1B
D26, D27: Diode_BAS16HT1G; BAS16HT1G; Manufacturer Part Number BAS16HT1G
J19: TSM-103-04-L-SV; Manufacturer Part Number TSM-103-04-L-SV
J29, J31, J36: TSM-102-04-T-SV; Manufacturer Part Number 200-TSM10204TSV
J30, J32: PIN_HEADER_2X2_SSM-102-L-DV-K-TR; Manufacturer Part Number SSM-102-L-DV-K-TR
J42, J43, J44, J46: Jumper_SNM-100-BK-T; SNM-100-BK-T; Manufacturer Part Number SNM-100-BK-T
L114: 470nH_0805_0805LS-471XGLB; SMD0805; Manufacturer Part Number 0805LS-471XGLB
R107: 330R_0603_CRGCQ0603J330R; SMD0603; Manufacturer Part Number CRGCQ0603J330R
R207, R209: NF_150R_0805_ERJ-6ENF1500V; SMD0805; Manufacturer Part Number ERJ-6ENF1500V
R208: 0R_0805; SMD0805; Manufacturer Part Number RCS08050000Z0EA
R223, R229: 536R_0805_CRCW0805536RFKEA; SMD0805; Manufacturer Part Number CRCW0805536RFKEA
R267: 15K_0603; SMD0603; Manufacturer Part Number CRCW060315K0JNEAC
R268: 4.99K_0603; SMD0603; Manufacturer Part Number CRCW06034K99FKEAC
R343: 10K_TRIMMER_TC33X-2-103E; SMD_TC33X; Manufacturer Part Number TC33X-2-103E
R344, R348: 1K_0603_ESR03EZPJ102; SMD0603; Manufacturer Part Number ESR03EZPJ102
T1, T2: 744889020100; Manufacturer Part Number 744889020100
U6: RD16HHF1; Manufacturer Part Number RD16HHF1-501
U56: TPS22810DBVR; SOT23_TPS22810DBVR; Manufacturer Part Number TPS22810DBVR
