myriadrf/LimeRFE/hardware/1v0/KiCAD/PA145.sch

## KiCad design hardware/1v0/KiCAD/PA145.sch (2020-02-29)

Schematic: PA145.sch

Parts:
C93, C187: 1nF_0603_06035C102KAT2A; SMD0603; Manufacturer Part Number 06035C102KAT2A
C175: 82pF_0603_GRM1885C1H820JA01D; SMD0603; Manufacturer Part Number GRM1885C1H820JA01D
C176: 15pF_0603_C0603C150J5GACTU; SMD0603; Manufacturer Part Number C0603C150J5GACTU
C177, C180, C184: 100nF_0603_C0603C104M5RACTU; SMD0603; Manufacturer Part Number C0603C104M5RACTU
C178: 10pF_0603_GRM1885C1H100JA01J; SMD0603; Manufacturer Part Number GRM1885C1H100JA01J
C179: 27pF_0603_C0603C270J5GAC; SMD0603; Manufacturer Part Number C0603C270J5GAC
C181, C185: 100pF_0603_GRM1885C2A101JA01D; SMD0603; Manufacturer Part Number GRM1885C2A101JA01D
C182, C186: 470nF_0805; SMD0805; Manufacturer Part Number UMK212B7474KG-T
C183: 47pF_0603_GRM1885C2A470JA01J; SMD0603; Manufacturer Part Number GRM1885C2A470JA01J
C188, C191: 68pF_0603_GRM1885C1H680JA01D; SMD0603; Manufacturer Part Number GRM1885C1H680JA01D
C190: 39pF_0603_GRM1885C1H390JA01D; SMD0603; Manufacturer Part Number GRM1885C1H390JA01D
C192: 1500pF_0603_GRM1885C1H152JA01D; SMD0603; Manufacturer Part Number GRM1885C1H152JA01D
C193: 1uF_0603_TMK107BJ105KA-T; SMD0603; Manufacturer Part Number TMK107BJ105KA-T
D15: ZENER_Diode_5.09V_CDZFHT2RA5.1B; VMN2; Manufacturer Part Number CDZFHT2RA5.1B
D19, D23: Diode_BAS16HT1G; BAS16HT1G; Manufacturer Part Number BAS16HT1G
J24: TSM-102-04-T-SV; Manufacturer Part Number 200-TSM10204TSV
J39: Jumper_SNM-100-BK-T; SNM-100-BK-T; Manufacturer Part Number SNM-100-BK-T
L49: 68nH_0805_LQW2BAS68NG00L; SMD0805; Manufacturer Part Number LQW2BAS68NG00L
L50: 27nH_0603_LQG18HN27NJ00D; SMD0603; Manufacturer Part Number LQG18HN27NJ00D
L51: 78nH_0805_0805LS-78NXJLB; SMD0805; Manufacturer Part Number 0805LS-78NXJLB
L52: 12nH_1008_1008HQ-12NXJLB; SMD1008; Manufacturer Part Number 1008HQ-12NXJLB
L53: 1.15nH_0604_0604HQ-1N1XJLB; SMD0604; Manufacturer Part Number 0604HQ-1N1XJLB
L54: 68nH_0603_0603CS-68NXGLU; SMD0603; Manufacturer Part Number 0603CS-68NXGLU
R102: 330R_0603_CRGCQ0603J330R; SMD0603; Manufacturer Part Number CRGCQ0603J330R
R161: 10K_TRIMMER_TC33X-2-103E; SMD_TC33X; Manufacturer Part Number TC33X-2-103E
R162: 1K_0603_ESR03EZPJ102; SMD0603; Manufacturer Part Number ESR03EZPJ102
R163, R167: NF_SMD_0603; SMD0603; Manufacturer Part Number _
R165: 50R_0805_RCS080551R0FKEA; SMD0805; Manufacturer Part Number RCS080551R0FKEA
R166: 200R_0603; SMD0603; Manufacturer Part Number CRCW0603200RFKEAC
R263: 7.5K_0603; SMD0603; Manufacturer Part Number CRCW06037K50FKEB
R264: 20K_0603_RC0603FR-0720KL; SMD0603; Manufacturer Part Number RC0603FR-0720KL
U50: TPS22810DBVR; SOT23_TPS22810DBVR; Manufacturer Part Number TPS22810DBVR
U97: AFT09MS007NT1; SMD_AFT09MS007NT1; Manufacturer Part Number AFT09MS007NT1
