myriadrf/LimeRFE/hardware/1v0/KiCAD/PA435.sch

## KiCad design hardware/1v0/KiCAD/PA435.sch (2020-02-29)

Schematic: PA435.sch

Parts:
C98, C224: 1nF_0603_06035C102KAT2A; SMD0603; Manufacturer Part Number 06035C102KAT2A
C206, C207, C239, C240: 15pF_0603_KEMET; SMD0603; Manufacturer Part Number C0603C150J5GACTU
C216, C217, C221: 100nF_0603_C0603C104M5RACTU; SMD0603; Manufacturer Part Number C0603C104M5RACTU
C218, C222: 100pF_0603_GRM1885C2A101JA01D; SMD0603; Manufacturer Part Number GRM1885C2A101JA01D
C226: 1uF_0603_TMK107BJ105KA-T; SMD0603; Manufacturer Part Number TMK107BJ105KA-T
C234: 100pF_0603_Murata2; SMD0603; Manufacturer Part Number GRM1885C1H101JA01J
C235, C237: 470nF_0805; SMD0805; Manufacturer Part Number UMK212B7474KG-T
C236: 47pF_0603_KEMET; SMD0603; Manufacturer Part Number C0603C470J5GACTU
C238: 27pF_0603_C0603C270J5GAC; SMD0603; Manufacturer Part Number C0603C270J5GAC
D18: ZENER_Diode_5.09V_CDZFHT2RA5.1B; VMN2; Manufacturer Part Number CDZFHT2RA5.1B
D24, D25: Diode_BAS16HT1G; BAS16HT1G; Manufacturer Part Number BAS16HT1G
J26: TSM-102-04-T-SV; Manufacturer Part Number 200-TSM10204TSV
J41: Jumper_SNM-100-BK-T; SNM-100-BK-T; Manufacturer Part Number SNM-100-BK-T
L59: 27nH_0603_LQG18HN27NJ00D; SMD0603; Manufacturer Part Number LQG18HN27NJ00D
L60: 4.5nH_0604_0604HQ-4N5XJLB; SMD0604; Manufacturer Part Number 0604HQ-4N5XJLB
L62: 5.6nH_0805_0805HQ-5N6XJLC; SMD0805; Manufacturer Part Number 0805HQ-5N6XJLC
L63: 3.9nH_0805_0805HT-3N9TJLB; SMD0805; Manufacturer Part Number 0805HT-3N9TJLB
R106: 330R_0603_CRGCQ0603J330R; SMD0603; Manufacturer Part Number CRGCQ0603J330R
R221: 0R_0805_RC0805FR-130RL; SMD0805; Manufacturer Part Number RC0805FR-130RL
R226: 10K_TRIMMER_TC33X-2-103E; SMD_TC33X; Manufacturer Part Number TC33X-2-103E
R227: 1K_0603_ESR03EZPJ102; SMD0603; Manufacturer Part Number ESR03EZPJ102
R230, R234: NF_SMD_0603; SMD0603; Manufacturer Part Number _
R232: 50R_0805_RCS080551R0FKEA; SMD0805; Manufacturer Part Number RCS080551R0FKEA
R233: 200R_0603; SMD0603; Manufacturer Part Number CRCW0603200RFKEAC
R265: 7.5K_0603; SMD0603; Manufacturer Part Number CRCW06037K50FKEB
R266: 20K_0603_RC0603FR-0720KL; SMD0603; Manufacturer Part Number RC0603FR-0720KL
U55: TPS22810DBVR; SOT23_TPS22810DBVR; Manufacturer Part Number TPS22810DBVR
U103: AFT09MS007NT1; SMD_AFT09MS007NT1; Manufacturer Part Number AFT09MS007NT1
