myriadrf/LimeRFE/hardware/1v0/KiCAD/PA1000.sch

## KiCad design hardware/1v0/KiCAD/PA1000.sch (2020-02-29)

Schematic: PA1000.sch

Parts:
C97, C213: 1nF_0603_06035C102KAT2A; SMD0603; Manufacturer Part Number 06035C102KAT2A
C174, C205: 100pF_0603_GRM1885C1H101JA01J; SMD0603; Manufacturer Part Number GRM1885C1H101JA01J
C211: 100pF_0603_GRM1885C2A101JA01D; SMD0603; Manufacturer Part Number GRM1885C2A101JA01D
C212: 27pF_0603_C0603C270J5GAC; SMD0603; Manufacturer Part Number C0603C270J5GAC
C215: 1uF_0603_TMK107BJ105KA-T; SMD0603; Manufacturer Part Number TMK107BJ105KA-T
L57: 33uH_1210_CBC3225T330KR; SMD1210; Manufacturer Part Number CBC3225T330KR
L58: 78nH_0805_0805LS-78NXJLB; SMD0805; Manufacturer Part Number 0805LS-78NXJLB
R105: 330R_0603_CRGCQ0603J330R; SMD0603; Manufacturer Part Number CRGCQ0603J330R
R206: 5K1_0402; SMD0402; Manufacturer Part Number RC0402FR-075K1L
R214: 10K_0402_Yageo; SMD0402; Manufacturer Part Number RC0402JR-7D10KL
R215: 100R_0402_ESR01MZPF1000; SMD0402; Manufacturer Part Number ESR01MZPF1000
U54: TPS22810DBVR; SOT23_TPS22810DBVR; Manufacturer Part Number TPS22810DBVR
U101: RD01MUS2B; Manufacturer Part Number RD01MUS2B
