myriadrf/LimeRFE/hardware/1v0/KiCAD/PA1280.sch

## KiCad design hardware/1v0/KiCAD/PA1280.sch (2020-02-29)

Schematic: PA1280.sch

Parts:
C96, C202: 1nF_0603_06035C102KAT2A; SMD0603; Manufacturer Part Number 06035C102KAT2A
C194, C195, C199: 100nF_0603_C0603C104M5RACTU; SMD0603; Manufacturer Part Number C0603C104M5RACTU
C196, C200: 100pF_0603_GRM1885C2A101JA01D; SMD0603; Manufacturer Part Number GRM1885C2A101JA01D
C197, C201: 27pF_0603_C0603C270J5GAC; SMD0603; Manufacturer Part Number C0603C270J5GAC
C204: 1uF_0603_TMK107BJ105KA-T; SMD0603; Manufacturer Part Number TMK107BJ105KA-T
C349: 2.7pF_0603_KEMET; SMD0603; Manufacturer Part Number CBR06C279B5GAC
C350, C352: 3.9pF_0603_KEMET; SMD0603; Manufacturer Part Number CBR06C399B5GAC
C351: 120pF_0603_KEMET; SMD0603; Manufacturer Part Number C0603C121J5GACTU
C353: 22pF_0603; SMD0402; Manufacturer Part Number GCM1555C1H220GA16D
C354: 1.5pF_0603_KEMET; SMD0603; Manufacturer Part Number CBR06C159B5GAC
C355: 330pF_0603_GCM1885C2A331FA16D; SMD0603; Manufacturer Part Number GCM1885C2A331FA16D
C356: 5.6pF_0603_CBR06C569D5GAC; SMD0603; Manufacturer Part Number CBR06C569D5GAC
C357: 1pF_0603_Kemet; SMD0603; Manufacturer Part Number CBR06C109B5GAC
C379, C380: 47nF_0603_Kemet; SMD0603; Manufacturer Part Number C0603C473J3RACTU
D16: ZENER_Diode_5.09V_CDZFHT2RA5.1B; VMN2; Manufacturer Part Number CDZFHT2RA5.1B
D34, D35: Diode_BAS16HT1G; BAS16HT1G; Manufacturer Part Number BAS16HT1G
J20: TSM-102-04-T-SV; Manufacturer Part Number 200-TSM10204TSV
J40: Jumper_SNM-100-BK-T; SNM-100-BK-T; Manufacturer Part Number SNM-100-BK-T
L56: 12nH_0805_LQW2BAN12NG00L; SMD0805; Manufacturer Part Number LQW2BAN12NG00L
L79: 3.9nH_0603_LQW; SMD0603; Manufacturer Part Number LQW18AN3N9C0ZD
L80: 2.2nH_0603_LQW_NF; SMD0603; Manufacturer Part Number LQW18AN2N2D10D
L81: 12nH_0603_Murata_LQW; SMD0603; Manufacturer Part Number LQW18AN12NG10D
L82: 10nH_0603_0603HP-10NXGLW; SMD0603; Manufacturer Part Number 0603HP-10NXGLW
R101, R177, R183: 1K_0603_ESR03EZPJ102; SMD0603; Manufacturer Part Number ESR03EZPJ102
R104: 330R_0603_CRGCQ0603J330R; SMD0603; Manufacturer Part Number CRGCQ0603J330R
R176: 10K_TRIMMER_TC33X-2-103E; SMD_TC33X; Manufacturer Part Number TC33X-2-103E
R179: 20K_0603_RC0603FR-0720KL; SMD0603; Manufacturer Part Number RC0603FR-0720KL
R181: NF_SMD_0603; SMD0603; Manufacturer Part Number _
R257: 30R_0603; SMD0603; Manufacturer Part Number RCA060330R0JNEC
U53: TPS22810DBVR; SOT23_TPS22810DBVR; Manufacturer Part Number TPS22810DBVR
U124: RD01MUS2B; Manufacturer Part Number RD01MUS2B
