myriadrf/LimeRFE/hardware/1v0/KiCAD/PA2400.sch

## KiCad design hardware/1v0/KiCAD/PA2400.sch (2020-02-29)

Schematic: PA2400.sch

Parts:
C289, C329: 10uF_1206_Taiyo; SMD1206; Manufacturer Part Number TMK316BJ106KL-T
C327, C328, C336, C340: 0.1uF_0402_Murata; SMD0402; Manufacturer Part Number GRM155R71C104JA88J
C330, C339: 10uF_1206_Tantalum_Kemet; SMD1206_TANTAL; Manufacturer Part Number T491A106K016AT
C331, C338: 0.1uF_0603_Murata; SMD0603; Manufacturer Part Number GCM188R91E104JA37D
C332, C337: 1nF_0603_Murata_GCJ; SMD0603; Manufacturer Part Number GCJ188R71H102KA01D
C333: 0.01uF_0603_Murata; SMD0603; Manufacturer Part Number GRM155R71H103KA88D
C334: 100pF_0603_Murata_GCM; SMD0603; Manufacturer Part Number GCM1885C2A101FA16D
C490, C491: 100pF_0402_GCM1555C1H101JA16D; SMD0402; Manufacturer Part Number GCM1555C1H101JA16D
FB10, FB11: FB_600R_0805_MPZ2012S601AT000; SMD0805; Manufacturer Part Number MPZ2012S601AT000
R222: 0R_0402_Yageo; SMD0402; Manufacturer Part Number RC0402JR-070RL
U106: NCP702_2V8; NCP702_TSOP5; Manufacturer Part Number NCP702SN28T1G
U113: QPA9426; Manufacturer Part Number QPA9426
U120: NCP331SNT1G; TSOP-6; Manufacturer Part Number NCP331SNT1G
U162: MADL-011021-14150T; Manufacturer Part Number MADL-011021-14150T
U163: PAT1220-C-3DB-T5; Manufacturer Part Number PAT1220-C-3DB-T5

Notes on the sheet:
LDO +2.8V
PA2400
