myriadrf/LimeRFE/hardware/1v0/KiCAD/PA3500.sch

## KiCad design hardware/1v0/KiCAD/PA3500.sch (2020-02-29)

Schematic: PA3500.sch

Parts:
C94, C297: 1nF_0603_06035C102KAT2A; SMD0603; Manufacturer Part Number 06035C102KAT2A
C107: 100nF_0402_GRM155R71C104KA88J; SMD0402; Manufacturer Part Number GRM155R71C104KA88J
C231, C292, C296: 18pF_0603_GRM1885C1H180JA01J; SMD0603; Manufacturer Part Number GRM1885C1H180JA01J
C290: 400f_0402_GJM1555C1HR40WB01D; SMD0402; Manufacturer Part Number GJM1555C1HR40WB01D
C291: 100pF_0603_GRM1885C2A101JA01D; SMD0603; Manufacturer Part Number GRM1885C2A101JA01D
C293: 700f_0402_GRM1555C2AR70BA01D; SMD0402; Manufacturer Part Number GRM1555C2AR70BA01D
C319: 1uF_0603_TMK107BJ105KA-T; SMD0603; Manufacturer Part Number TMK107BJ105KA-T
L68: 25nH_0402_LQW15AN25NJ80D; SMD0603; Manufacturer Part Number LQW15AN25NJ80D
L72: 5.1nH_0402_LQW15AN25NJ80D; SMD0402; Manufacturer Part Number LQW15AN5N1D1ZD
L78: 3nH_0402_LQW15AN3N0B80D; SMD0402; Manufacturer Part Number LQW15AN3N0B80D
R103: 330R_0603_CRGCQ0603J330R; SMD0603; Manufacturer Part Number CRGCQ0603J330R
U51: TPS22810DBVR; SOT23_TPS22810DBVR; Manufacturer Part Number TPS22810DBVR
U82: MAAM-009560-TR3000; SOT89_MAAM-009560; Manufacturer Part Number MAAM-009560-TR3000
