myriadrf/LimeRFE/hardware/1v0/KiCAD/PA4000.sch

## KiCad design hardware/1v0/KiCAD/PA4000.sch (2020-02-29)

Schematic: PA4000.sch

Parts:
C342, C343, C345: 100nF_0402_GRM155R71C104KA88J; SMD0402; Manufacturer Part Number GRM155R71C104KA88J
C344, C347, C348: 15pF_0402_Murata; SMD0402; Manufacturer Part Number GCM1555C1H150JA16J
C346: 100pF_0402_Murata; SMD0402; Manufacturer Part Number GCM1555C1H101JA16D
FB12: FB_600R_0805_MPZ2012S601AT000; SMD0805; Manufacturer Part Number MPZ2012S601AT000
L55: 25nH_0402_LQW15AN25NJ80D; SMD0603; Manufacturer Part Number LQW15AN25NJ80D
R248, R249, R254, R256: NF_SMD_0402; SMD0402; Manufacturer Part Number _
R255, R332: 0R_0402_Yageo; SMD0402; Manufacturer Part Number RC0402JR-070RL
U122: NCP331SNT1G; TSOP-6; Manufacturer Part Number NCP331SNT1G
U123: MAAM-009286; SOT89_MAAM-009286; Manufacturer Part Number MAAM-009286-TR3000
