myriadrf/LimeRFE/hardware/1v0/KiCAD/PA_1_2_3.sch

## KiCad design hardware/1v0/KiCAD/PA_1_2_3.sch (2020-02-29)

Schematic: PA_1_2_3.sch

Parts:
C85, C92: 10uF_1206_Tantalum_Kemet; SMD1206_TANTAL; Manufacturer Part Number T491A106K016AT
C86, C91: 0.1uF_0603_Murata; SMD0603; Manufacturer Part Number GCM188R91E104JA37D
C87, C90: 1nF_0603_Murata_GCJ; SMD0603; Manufacturer Part Number GCJ188R71H102KA01D
C88: 0.01uF_0603_Murata; SMD0402; Manufacturer Part Number GRM155R71H103KA88D
C89: 100pF_0603_Murata_GCM; SMD0603; Manufacturer Part Number GCM1885C2A101FA16D
C278, C281: 10uF_0805_25V_Taiyo; SMD0805; Manufacturer Part Number TMK212BBJ106KG-T
C279, C280, C283, C284: 0.1uF_0402_Murata; SMD0402; Manufacturer Part Number GRM155R71C104JA88J
FB6, FB7: FB_600R_0805_MPZ2012S601AT000; SMD0805; Manufacturer Part Number MPZ2012S601AT000
J28: UMC_SMD; Manufacturer Part Number 0734120110
R93: 0RNF_0402_Yageo; SMD0402; Manufacturer Part Number RC0402JR-070RL
R96, R97: 0R_0402_Yageo; SMD0402; Manufacturer Part Number RC0402JR-070RL
R99: 50R_0402_Yageo; SMD0402; Manufacturer Part Number RC0402FR-0749R9L
U48: QPA9419; Manufacturer Part Number QPA9419
U49: HHM22139A2; Manufacturer Part Number HHM22139A2
U87: NCP702_2V8; NCP702_TSOP5; Manufacturer Part Number NCP702SN28T1G
U88: NCP331SNT1G; TSOP-6; Manufacturer Part Number NCP331SNT1G

Notes on the sheet:
LDO +2.8V
