myriadrf/LimeRFE/hardware/1v0/KiCAD/PA_7_38.sch

## KiCad design hardware/1v0/KiCAD/PA_7_38.sch (2020-02-29)

Schematic: PA_7_38.sch

Parts:
C77, C84: 10uF_1206_Tantalum_Kemet; SMD1206_TANTAL; Manufacturer Part Number T491A106K016AT
C78, C83: 0.1uF_0603_Murata; SMD0603; Manufacturer Part Number GCM188R91E104JA37D
C79, C82: 1nF_0603_Murata_GCJ; SMD0603; Manufacturer Part Number GCJ188R71H102KA01D
C80: 0.01uF_0603_Murata; SMD0402; Manufacturer Part Number GRM155R71H103KA88D
C81: 100pF_0603_Murata_GCM; SMD0603; Manufacturer Part Number GCM1885C2A101FA16D
C95, C198: 10uF_0805_25V_Taiyo; SMD0805; Manufacturer Part Number TMK212BBJ106KG-T
C100, C103, C275, C276: 0.1uF_0402_Murata; SMD0402; Manufacturer Part Number GRM155R71C104JA88J
FB4, FB5: FB_600R_0805_MPZ2012S601AT000; SMD0805; Manufacturer Part Number MPZ2012S601AT000
J21: UMC_SMD; Manufacturer Part Number 0734120110
R90: 0RNF_0402_Yageo; SMD0402; Manufacturer Part Number RC0402JR-070RL
R91, R92: 0R_0402_Yageo; SMD0402; Manufacturer Part Number RC0402JR-070RL
R94: 50R_0402_Yageo; SMD0402; Manufacturer Part Number RC0402FR-0749R9L
R173: 10K_0402_Yageo; SMD0402; Manufacturer Part Number RC0402JR-7D10KL
R189: 33.2R_0402_RC0402FR-0733R2L; SMD0402; Manufacturer Part Number RC0402FR-0733R2L
U46: QPA9426; Manufacturer Part Number QPA9426
U47: HHM22137A2; Manufacturer Part Number HHM22137A2
U52: NCP702_2V8; NCP702_TSOP5; Manufacturer Part Number NCP702SN28T1G
U85: NCP331SNT1G; TSOP-6; Manufacturer Part Number NCP331SNT1G
U130: FSA5157P6X; Manufacturer Part Number FSA5157P6X
U133: SN74LV1T34; Manufacturer Part Number Texas Instruments

Notes on the sheet:
LDO +2.8V
