myriadrf/LimeRFE/hardware/1v0/KiCAD/PA_220.sch

## KiCad design hardware/1v0/KiCAD/PA_220.sch (2020-02-29)

Schematic: PA_220.sch

Parts:
C381: 120pF_0603_KEMET; SMD0603_gap05; Manufacturer Part Number C0603C121J5GACTU
C382: 18pF_0603_Kemet; SMD0603_gap05; Manufacturer Part Number C0603C180J5GACTU
C383, C386, C454: 100nF_0603_C0603C104M5RACTU; SMD0603; Manufacturer Part Number C0603C104M5RACTU
C384: 15pF_0603_Kemet; SMD0603_gap05; Manufacturer Part Number C0603C150J5GACAUTO
C385: 8.2pF_0603_Kemet; SMD0603_gap05; Manufacturer Part Number CBR06C829D5GAC
C450, C455, C464: 1uF_0603_TMK107BJ105KA-T; SMD0603; Manufacturer Part Number TMK107BJ105KA-T
C451, C456: 1500pF_0603_GRM1885C1H152JA01D; SMD0603; Manufacturer Part Number GRM1885C1H152JA01D
C452, C457: 100pF_0603_Kemet; SMD0603_gap05; Manufacturer Part Number C0603C101J1GACTU
C453, C459, C462, C463: 47pF_0603_Kemet; SMD0603_gap05; Manufacturer Part Number C0603C470J4GACTU
C458, C461: 1nF_0603_06035C102KAT2A; SMD0603; Manufacturer Part Number 06035C102KAT2A
C460: 1pF_0603_Kemet; SMD0603_gap05; Manufacturer Part Number CBR06C109B5GAC
D37: ZENER_Diode_5.09V_CDZFHT2RA5.1B; VMN2; Manufacturer Part Number CDZFHT2RA5.1B
D38, D39: Diode_BAS16HT1G; BAS16HT1G; Manufacturer Part Number BAS16HT1G
J25: TSM-102-04-T-SV; Manufacturer Part Number 200-TSM10204TSV
J47: Jumper_SNM-100-BK-T; SNM-100-BK-T; Manufacturer Part Number SNM-100-BK-T
L98: 24nH_0603_Murata_LQW18; SMD0603_gap05; Manufacturer Part Number LQW18AN24NG80D
L99: 27nH_0603_LQG18HN27NJ00D; SMD0603; Manufacturer Part Number LQG18HN27NJ00D
L100: 10nH_0805_Murata; SMD0805; Manufacturer Part Number LQW2BAS10NG00L
L101: 11nH_0603_Coilcraft_0603HP; SMD0603_gap05; Manufacturer Part Number 0603HP-11NXGLU
L102: 30nH_0603_Coilcraft_0603HP; SMD0603_gap05; Manufacturer Part Number 0603HP-30NXGLW
L103: 75nH_0603_Coilcraft_0603HP; SMD0603_gap05; Manufacturer Part Number 0603HP-75NXGLW
R193: 7.5K_0603; SMD0603; Manufacturer Part Number CRCW06037K50FKEB
R217, R250: 0R_0603_RCS06030000Z0EA; SMD0603; Manufacturer Part Number RCS06030000Z0EA
R218: 10K_TRIMMER_TC33X-2-103E; SMD_TC33X; Manufacturer Part Number TC33X-2-103E
R236: 1K_0603_ESR03EZPJ102; SMD0603; Manufacturer Part Number ESR03EZPJ102
R237: 20K_0603_RC0603FR-0720KL; SMD0603; Manufacturer Part Number RC0603FR-0720KL
R366: NF_SMD_0603; SMD0603; Manufacturer Part Number _
R367: 50R_0805_RCS080551R0FKEA; SMD0805; Manufacturer Part Number RCS080551R0FKEA
R368: 200R_0603; SMD0603; Manufacturer Part Number CRCW0603200RFKEAC
R369: 330R_0603_CRGCQ0603J330R; SMD0603; Manufacturer Part Number CRGCQ0603J330R
U144: AFT09MS007NT1; SMD_AFT09MS007NT1; Manufacturer Part Number AFT09MS007NT1
U158: TPS22810DBVR; SOT23_TPS22810DBVR; Manufacturer Part Number TPS22810DBVR
