myriadrf/LimeRFE/hardware/1v0/KiCAD/PA_920.sch

## KiCad design hardware/1v0/KiCAD/PA_920.sch (2020-02-29)

Schematic: PA_920.sch

Parts:
C387: 4pF_0603_Kemet; SMD0603_gap05; Manufacturer Part Number CBR06C409B5GAC
C388, C402, C477: 100nF_0603_C0603C104M5RACTU; SMD0603; Manufacturer Part Number C0603C104M5RACTU
C389: 3.1pF_0603_Kemet_CBR; SMD0603_gap05; Manufacturer Part Number CBR06C319B5GAC
C400, C485: 5pF_0603_Kemet; SMD0603_gap05; Manufacturer Part Number CBR06C509B5GAC
C401: 8.2pF_0603_Kemet; SMD0603_gap05; Manufacturer Part Number CBR06C829D5GAC
C472, C478: 10uF_0603_Murata_GRM; SMD0603_gap05; Manufacturer Part Number GRM188R61E106KA73D
C473, C479: 47nF_0603_Kemet; SMD0603_gap05; Manufacturer Part Number C0603C473J3RACTU
C474, C480: 100pF_0603_Kemet; SMD0603_gap05; Manufacturer Part Number C0603C101J1GACTU
C475, C481, C487: 27pF_0603_Kemet; SMD0603_gap05; Manufacturer Part Number C0603C270J8GACTU
C476, C484: 22pF_0603_Kemet; SMD0603_gap05; Manufacturer Part Number C0603C220J1GACTU
C482, C486: 1nF_0603_06035C102KAT2A; SMD0603; Manufacturer Part Number 06035C102KAT2A
C483: 8pF_0603_Kemet; SMD0603_gap05; Manufacturer Part Number CBR06C809B5GAC
C488: 1uF_0603_TMK107BJ105KA-T; SMD0603; Manufacturer Part Number TMK107BJ105KA-T
D40: ZENER_Diode_5.09V_CDZFHT2RA5.1B; VMN2; Manufacturer Part Number CDZFHT2RA5.1B
D41, D42: Diode_BAS16HT1G; BAS16HT1G; Manufacturer Part Number BAS16HT1G
J27: TSM-102-04-T-SV; Manufacturer Part Number 200-TSM10204TSV
J48: Jumper_SNM-100-BK-T; SNM-100-BK-T; Manufacturer Part Number SNM-100-BK-T
L17: 6.8nH_0603_Murata_LQW; SMD0603_gap05; Manufacturer Part Number LQW18AN6N8C80D
L109: 2.2nH_0603_Murata_LQW; SMD0603_gap05; Manufacturer Part Number LQW18AN2N2D10D
L110: 12nH_0603_Murata_LQW; SMD0603_gap05; Manufacturer Part Number LQW18AN12NG10D
L111: 12nH_0805_Murata_LQW; SMD0603_gap05; Manufacturer Part Number LQW2BAN12NJ00L
L112: 360nH_0603_Coilcraft_0603HP_NF; SMD0603_gap05; Manufacturer Part Number 0603HP-R36XGLU
L113: 3.6nH_0603_Coilcraft_0603HP; SMD0603_gap05; Manufacturer Part Number 0603HP-3N6XGLU
R252, R258: 1K_0603_ESR03EZPJ102; SMD0603; Manufacturer Part Number ESR03EZPJ102
R253: 10K_TRIMMER_TC33X-2-103E; SMD_TC33X; Manufacturer Part Number TC33X-2-103E
R259: 24K_0603_CRCW060324K0FKEA; SMD0603; Manufacturer Part Number CRCW060324K0FKEA
R260: 30R_0603; SMD0603_gap05; Manufacturer Part Number RCA060330R0JNEC
R261: 200R_0603; SMD0603; Manufacturer Part Number CRCW0603200RFKEAC
R372: 330R_0603_CRGCQ0603J330R; SMD0603; Manufacturer Part Number CRGCQ0603J330R
U145: RFM04U6P; RFM04U6P_SOT89; Manufacturer Part Number RFM04U6P(TE12L,F)
U159: TPS22810DBVR; SOT23_TPS22810DBVR; Manufacturer Part Number TPS22810DBVR
