myriadrf/LimeRFE/hardware/1v0/KiCAD/PA_CTRL.sch

## KiCad design hardware/1v0/KiCAD/PA_CTRL.sch (2020-02-29)

Schematic: PA_CTRL.sch

Parts:
C93, C94, C101, C102, C104, C105, C110, C111: 10uF_1206_Taiyo; SMD1206; Manufacturer Part Number TMK316BJ106KL-T
C96, C97, C98, C99, C106, C107, C108, C109: 0.1uF_0402_Murata; SMD0402; Manufacturer Part Number GRM155R71C104JA88J
R101, R102, R110, R112: 10K_0402_Yageo; SMD0402; Manufacturer Part Number RC0402JR-7D10KL
R103, R104, R113, R114, R115, R116, R117, R118: 0R_0805_Yageo; SMD0805; Manufacturer Part Number RC0805JR-070RL
R105, R106, R107, R108: 0RNF_0805_Yageo; SMD0805; Manufacturer Part Number RC0805JR-070RL
R109, R111: 80k_0402_Yageo; SMD0402; Manufacturer Part Number RC0402FR-0780K6L
U50, U51: NCP702_2V8; NCP702_TSOP5; Manufacturer Part Number NCP702SN28T1G
U53, U54: NCP331SNT1G; TSOP-6; Manufacturer Part Number NCP331SNT1G
U55, U56: LD39200; Manufacturer Part Number LD39200PUR

Notes on the sheet:
LDO +2.8V
SWITCH (OPTIONAL)
LDO +4.5V
