myriadrf/LimeRFE/hardware/1v0/KiCAD/PDRIV30.sch

## KiCad design hardware/1v0/KiCAD/PDRIV30.sch (2020-02-29)

Schematic: PDRIV30.sch

Parts:
C102, C312: 1nF_0603_06035C102KAT2A; SMD0603; Manufacturer Part Number 06035C102KAT2A
C244, C298: 1uF_0805; SMD0805; Manufacturer Part Number VJ0805Y105KXXTW1BC
C272, C299, C302, C303, C305, C309, C397: 100nF_0603_C0603C104M5RACTU; SMD0603; Manufacturer Part Number C0603C104M5RACTU
C306: 1500pF_0603_GRM1885C1H152JA01D; SMD0603; Manufacturer Part Number GRM1885C1H152JA01D
C307: 10uF_1206_Taiyo; SMD1206; Manufacturer Part Number TMK316BJ106KL-T
C315: 1uF_0603_TMK107BJ105KA-T; SMD0603; Manufacturer Part Number TMK107BJ105KA-T
D28: ZENER_Diode_5.09V_CDZFHT2RA5.1B; VMN2; Manufacturer Part Number CDZFHT2RA5.1B
D29, D30: Diode_BAS16HT1G; BAS16HT1G; Manufacturer Part Number BAS16HT1G
FB16: 100uF_Ferrite_1812FS-104JLC; SMD_1812FS-104JLC; Manufacturer Part Number 1812FS-104JLC
L70: 18uF_1008_1008LS-183XJLB; SMD1008; Manufacturer Part Number 1008LS-183XJLB
R95: 10K_0402_Yageo; SMD0402; Manufacturer Part Number RC0402JR-7D10KL
R98: 30K_0402_Yageo; SMD0402; Manufacturer Part Number RC0402FR-0730KL
R108: 330R_0603_CRGCQ0603J330R; SMD0603; Manufacturer Part Number CRGCQ0603J330R
R112: 3.3K_0402_CRCW01003K30FREL; SMD0402; Manufacturer Part Number CRCW01003K30FREL
R210: 3R_0603_ESR03EZPJ3R0; SMD0603; Manufacturer Part Number ESR03EZPJ3R0
R238, R240: 150R_0603_Panasonic_250mW; SMD0603; Manufacturer Part Number ERJ-PA3J151V
R239: 36.5R_0603_Yageo; SMD0603; Manufacturer Part Number RC0603FR-0736R5L
R243: 680R_0805_ROHMSemiconductor_400mW; SMD0805; Manufacturer Part Number ESR10EZPJ681
R251: 330R_0603_ROHMSemiconductor_250mW; SMD0603; Manufacturer Part Number ESR03EZPJ331
R269: 1K_0603_ESR03EZPJ102; SMD0603; Manufacturer Part Number ESR03EZPJ102
U83: TPS22810DBVR; SOT23_TPS22810DBVR; Manufacturer Part Number TPS22810DBVR
U107: RD01MUS2B; Manufacturer Part Number RD01MUS2B
