myriadrf/LimeRFE/hardware/1v0/KiCAD/PDRIV220.sch

## KiCad design hardware/1v0/KiCAD/PDRIV220.sch (2020-02-29)

Schematic: PDRIV220.sch

Parts:
C417, C418, C421: 100nF_0603_C0603C104M5RACTU; SMD0603; Manufacturer Part Number C0603C104M5RACTU
C419, C423: 100pF_0603_GRM1885C2A101JA01D; SMD0603; Manufacturer Part Number GRM1885C2A101JA01D
C420, C424: 27pF_0603_C0603C270J5GAC; SMD0603; Manufacturer Part Number C0603C270J5GAC
C422: 47pF_0603_GRM1885C2A470JA01J; SMD0603; Manufacturer Part Number GRM1885C2A470JA01J
C425, C426: 1nF_0603_06035C102KAT2A; SMD0603; Manufacturer Part Number 06035C102KAT2A
C427: 1uF_0603_TMK107BJ105KA-T; SMD0603; Manufacturer Part Number TMK107BJ105KA-T
C493: 150pF_0805; SMD0805; Manufacturer Part Number 80-C0805C151J5RACTU
D43: ZENER_Diode_5.09V_CDZFHT2RA5.1B; VMN2; Manufacturer Part Number CDZFHT2RA5.1B
D44, D45: Diode_BAS16HT1G; BAS16HT1G; Manufacturer Part Number BAS16HT1G
L92: 27nH_0603_LQG18HN27NJ00D; SMD0603; Manufacturer Part Number LQG18HN27NJ00D
L93: 78nH_0805_0805LS-78NXJLB; SMD0805; Manufacturer Part Number 0805LS-78NXJLB
R180, R298, R307, R321: 0R_0603_RCS06030000Z0EA; SMD0603; Manufacturer Part Number RCS06030000Z0EA
R282: 10K_0402_Yageo; SMD0402; Manufacturer Part Number RC0402JR-7D10KL
R291: 30K_0402_Yageo; SMD0402; Manufacturer Part Number RC0402FR-0730KL
R296: 100R_0402_ESR01MZPF1000; SMD0402; Manufacturer Part Number ESR01MZPF1000
R297, R299, R306, R313: NF_SMD_0603; SMD0603; Manufacturer Part Number _
R301: 50R_0805_RCS080551R0FKEA; SMD0805; Manufacturer Part Number RCS080551R0FKEA
R302, R316: 330R_0603_CRGCQ0603J330R; SMD0603; Manufacturer Part Number CRGCQ0603J330R
U152: RD01MUS2B; Manufacturer Part Number RD01MUS2B
U153: TPS22810DBVR; SOT23_TPS22810DBVR; Manufacturer Part Number TPS22810DBVR
