myriadrf/LimeRFE/hardware/1v0/KiCAD/PDRIV1000.sch

## KiCad design hardware/1v0/KiCAD/PDRIV1000.sch (2020-02-29)

Schematic: PDRIV1000.sch

Parts:
C101, C228: 1nF_0603_06035C102KAT2A; SMD0603; Manufacturer Part Number 06035C102KAT2A
C227, C229, C230: 100pF_0603_GRM1885C1H101JA01J; SMD0603; Manufacturer Part Number GRM1885C1H101JA01J
C232: 100nF_0402_GRM155R71C104KA88J; SMD0402; Manufacturer Part Number GRM155R71C104KA88J
C267: 1uF_0603_TMK107BJ105KA-T; SMD0603; Manufacturer Part Number TMK107BJ105KA-T
L61: 500nH_0402_LQW15CAR50K00D; SMD0603; Manufacturer Part Number LQW15CAR50K00D
R213: 330R_0603_CRGCQ0603J330R; SMD0603; Manufacturer Part Number CRGCQ0603J330R
U79: QPA6489A; SOT89_QPA6489A; Manufacturer Part Number QPA6489ATR13
U80: TPS22810DBVR; SOT23_TPS22810DBVR; Manufacturer Part Number TPS22810DBVR

Notes on the sheet:
PREDRIVER_1-1000MHz
