myriadrf/LimeRFE/hardware/1v0/KiCAD/PDRIV1280.sch

## KiCad design hardware/1v0/KiCAD/PDRIV1280.sch (2020-02-29)

Schematic: PDRIV1280.sch

Parts:
C439, C440, C443: 100nF_0603_C0603C104M5RACTU; SMD0603; Manufacturer Part Number C0603C104M5RACTU
C441, C445: 100pF_0603_GRM1885C2A101JA01D; SMD0603; Manufacturer Part Number GRM1885C2A101JA01D
C442, C446: 27pF_0603_C0603C270J5GAC; SMD0603; Manufacturer Part Number C0603C270J5GAC
C444: 47pF_0603_GRM1885C2A470JA01J; SMD0603; Manufacturer Part Number GRM1885C2A470JA01J
C447, C448: 1nF_0603_06035C102KAT2A; SMD0603; Manufacturer Part Number 06035C102KAT2A
C449: 1uF_0603_TMK107BJ105KA-T; SMD0603; Manufacturer Part Number TMK107BJ105KA-T
C495: 150pF_0805; SMD0805; Manufacturer Part Number 80-C0805C151J5RACTU
D49: ZENER_Diode_5.09V_CDZFHT2RA5.1B; VMN2; Manufacturer Part Number CDZFHT2RA5.1B
D50, D51: Diode_BAS16HT1G; BAS16HT1G; Manufacturer Part Number BAS16HT1G
L96: 27nH_0603_LQG18HN27NJ00D; SMD0603; Manufacturer Part Number LQG18HN27NJ00D
L97: 78nH_0805_0805LS-78NXJLB; SMD0805; Manufacturer Part Number 0805LS-78NXJLB
R349: 10K_0402_Yageo; SMD0402; Manufacturer Part Number RC0402JR-7D10KL
R350, R354, R360, R363: 0R_0603_RCS06030000Z0EA; SMD0603; Manufacturer Part Number RCS06030000Z0EA
R351: 30K_0402_Yageo; SMD0402; Manufacturer Part Number RC0402FR-0730KL
R352: 100R_0402_ESR01MZPF1000; SMD0402; Manufacturer Part Number ESR01MZPF1000
R353, R355, R359, R361: NF_SMD_0603; SMD0603; Manufacturer Part Number _
R357: 50R_0805_RCS080551R0FKEA; SMD0805; Manufacturer Part Number RCS080551R0FKEA
R358: 1K_0603_ESR03EZPJ102; SMD0603; Manufacturer Part Number ESR03EZPJ102
R362: 330R_0603_CRGCQ0603J330R; SMD0603; Manufacturer Part Number CRGCQ0603J330R
U156: RD01MUS2B; Manufacturer Part Number RD01MUS2B
U157: TPS22810DBVR; SOT23_TPS22810DBVR; Manufacturer Part Number TPS22810DBVR
