myriadrf/LimeRFE/hardware/1v0/KiCAD/PREDRIVER.sch

## KiCad design hardware/1v0/KiCAD/PREDRIVER.sch (2020-02-29)

Schematic: PREDRIVER.sch

Parts:
C9, C11: 100nF_0402; SMD0402; Manufacturer Part Number CC0402ZRY5V7BB104
C10, C14: 1000pF_0402; SMD0603; Manufacturer Part Number GCM155R71H102KA37D
C12: 0.1uF_0402; SMD0402; Manufacturer Part Number GRM155R71C104KA88J
C13: 30pF_0402; SMD0402; Manufacturer Part Number GJM1555C1H300FB01D
FB1: FB_600R_2A_0805; SMD0805; Manufacturer Part Number MPZ2012S601AT000
L1: 56N_0402; SMD0603; Manufacturer Part Number LQG15HS56NJ02D
L2: 270N_0402; SMD0603; Manufacturer Part Number LQG15HSR27J02D
R10, R12, R17: 0R_0603; SMD0603; Manufacturer Part Number RCS06030000Z0EA
R11, R14, R15, R16: SMD_0603_NF; SMD0603_gap05; Manufacturer Part Number _
R13: 1k_0402; SMD0603; Manufacturer Part Number RC0402FR-7W1KL
U7: NCP331SNT1G; Manufacturer Part Number NCP331SNT1G
U8: PHA-1H+; SOT89; Manufacturer Part Number PHA-1H+
