myriadrf/LimeRFE/hardware/1v0/KiCAD/PREDRIVER_H.sch

## KiCad design hardware/1v0/KiCAD/PREDRIVER_H.sch (2020-02-29)

Schematic: PREDRIVER_H.sch

Parts:
C106: 1nF_0603_06035C102KAT2A; SMD0603; Manufacturer Part Number 06035C102KAT2A
C268, C269, C310: 56pF_0402_GCM1555C1H560JA16D; SMD0402; Manufacturer Part Number GCM1555C1H560JA16D
C270: 22pF_0402_CC0402JRNPO9BN220; SMD0402; Manufacturer Part Number CC0402JRNPO9BN220
C271: 500f_0402_GRM1555C2AR50BA01D; SMD0402; Manufacturer Part Number GRM1555C2AR50BA01D
C273: 1uF_0603_TMK107BJ105KA-T; SMD0603; Manufacturer Part Number TMK107BJ105KA-T
C316: 100nF_0402_GRM155R71C104KA88J; SMD0402; Manufacturer Part Number GRM155R71C104KA88J
L69: 780pH_0402_0402PA-0N8XJLW; SMD0402; Manufacturer Part Number 0402PA-0N8XJLW
L71: 18nH_0603_LQW18AN18NG00D; SMD0603; Manufacturer Part Number LQW18AN18NG00D
R111: 330R_0603_CRGCQ0603J330R; SMD0603; Manufacturer Part Number CRGCQ0603J330R
U81: QPA6489A; SOT89_QPA6489A; Manufacturer Part Number QPA6489ATR13
U102: TPS22810DBVR; SOT23_TPS22810DBVR; Manufacturer Part Number TPS22810DBVR

Notes on the sheet:
PREDRIVER_H
