myriadrf/LimeRFE/hardware/1v0/KiCAD/PRIV435.sch

## KiCad design hardware/1v0/KiCAD/PRIV435.sch (2020-02-29)

Schematic: PRIV435.sch

Parts:
C104, C253: 1nF_0603_06035C102KAT2A; SMD0603; Manufacturer Part Number 06035C102KAT2A
C108, C246, C250: 100nF_0603_C0603C104M5RACTU; SMD0603; Manufacturer Part Number C0603C104M5RACTU
C247, C251: 100pF_0603_GRM1885C2A101JA01D; SMD0603; Manufacturer Part Number GRM1885C2A101JA01D
C248, C252: 27pF_0603_C0603C270J5GAC; SMD0603; Manufacturer Part Number C0603C270J5GAC
C249: 47pF_0603_GRM1885C2A470JA01J; SMD0603; Manufacturer Part Number GRM1885C2A470JA01J
C255: 1uF_0603_TMK107BJ105KA-T; SMD0603; Manufacturer Part Number TMK107BJ105KA-T
C496: 47pF_0805_KEMET; SMD0805; Manufacturer Part Number C0805C470J5GACTU
D17, D31: Diode_BAS16HT1G; BAS16HT1G; Manufacturer Part Number BAS16HT1G
D20: ZENER_Diode_5.09V_CDZFHT2RA5.1B; VMN2; Manufacturer Part Number CDZFHT2RA5.1B
L64: 27nH_0603_LQG18HN27NJ00D; SMD0603; Manufacturer Part Number LQG18HN27NJ00D
L65: 78nH_0805_0805LS-78NXJLB; SMD0805; Manufacturer Part Number 0805LS-78NXJLB
R109, R270: 330R_0603_CRGCQ0603J330R; SMD0603; Manufacturer Part Number CRGCQ0603J330R
R113: 10K_0402_Yageo; SMD0402; Manufacturer Part Number RC0402JR-7D10KL
R114: 30K_0402_Yageo; SMD0402; Manufacturer Part Number RC0402FR-0730KL
R115: 100R_0402_ESR01MZPF1000; SMD0402; Manufacturer Part Number ESR01MZPF1000
R285, R289: NF_SMD_0603; SMD0603; Manufacturer Part Number _
R287: 50R_0805_RCS080551R0FKEA; SMD0805; Manufacturer Part Number RCS080551R0FKEA
U98: TPS22810DBVR; SOT23_TPS22810DBVR; Manufacturer Part Number TPS22810DBVR
U109: RD01MUS2B; Manufacturer Part Number RD01MUS2B
