myriadrf/LimeRFE/hardware/1v0/KiCAD/PowerSupply.sch

## KiCad design hardware/1v0/KiCAD/PowerSupply.sch (2020-02-29)

Schematic: PowerSupply.sch

Parts:
C15, C18: 1uF_0402_CC0402ZRY5V5BB105; SMD0402; Manufacturer Part Number CC0402ZRY5V5BB105
C16, C20, C21, C23, C25, C26, C110, C507, C508: 10uF_0603_GRM188R61E106KA73J; SMD0603; Manufacturer Part Number GRM188R61E106KA73J
C17, C24, C393: 2.2nF_0402_GRM155R71E222KA01D; SMD0402; Manufacturer Part Number GRM155R71E222KA01D
C19, C22: 0.1uF_0402_Murata; SMD0402; Manufacturer Part Number GRM155R71C104JA88J
D3, D7, D8, D9, D36: LED0603_GREEN; LED_0603; Manufacturer Part Number SML-D12M1WT86
D4, D5, D6: NSR20F30NXT5G; Manufacturer Part Number NSR20F30NXT5G
D52, D54: Schottky_Diode_PMEG045V100EPDZ; PMEG045V100EPDZ; Manufacturer Part Number PMEG045V100EPDZ
D53: ZENER_Diode_5.3V_P6SMB18CA; P6SMB18CA; Manufacturer Part Number P6SMB18CA
F1: Fuse_3405.0174.11; 3405.0174.11; Manufacturer Part Number 3405.0174.11
FB1: FB_60R_0805_MMZ2012Y600BT000; SMD0805; Manufacturer Part Number MMZ2012Y600BT000
J9, J10, J33: M20-8770342; Manufacturer Part Number M20-8770342
J11: TSM-103-04-F-DV; Manufacturer Part Number TSM-103-04-F-DV
J23: RAPC712X; Manufacturer Part Number RAPC712X
J37: Jumper_SNM-100-BK-T; SNM-100-BK-T; Manufacturer Part Number SNM-100-BK-T
L1, L2, L119: SPM6530T-2R2M; Manufacturer Part Number SPM6530T-2R2M
R12, R25: 619K_0805_ERJ-6ENF6193V; SMD0805; Manufacturer Part Number ERJ-6ENF6193V
R26, R29, R33, R36, R133, R134: 100k_0805; SMD0805; Manufacturer Part Number ERJ-6ENF1003V
R27: 0R_0402_RCS04020000Z0ED; SMD0402; Manufacturer Part Number RCS04020000Z0ED
R28: 39K_0402_Yageo; SMD0402; Manufacturer Part Number CRCW020139K0JNED
R30: 330R_0402_RC0402JR-07330RL; SMD0402; Manufacturer Part Number RC0402JR-07330RL
R31, R37, R171: 0R_0603_RCS06030000Z0EA; SMD0603; Manufacturer Part Number RCS06030000Z0EA
R32: 976K_0805_ERJ-6ENF9763V; SMD0805; Manufacturer Part Number ERJ-6ENF9763V
R34, R35: 680R_0402_RC0402FR-07680RL; SMD0402; Manufacturer Part Number RC0402FR-07680RL
R38: 1K_0402_CRGP0402F1K0; SMD0402; Manufacturer Part Number CRGP0402F1K0
R135: NF_0R_0402_RCS04020000Z0ED; SMD0402; Manufacturer Part Number RCS04020000Z0ED
R170: 10K_0402_Yageo; SMD0402; Manufacturer Part Number RC0402JR-7D10KL
R172: 150R_0402; SMD0402; Manufacturer Part Number RC0402FR-7D150RL
U17: NCP702_3V0; NCP702_TSOP5; Manufacturer Part Number NCP702SN30T1G
U18: LD39200; Manufacturer Part Number LD39200PUR
U19, U21, U90: TPS62136RGXT; Manufacturer Part Number TPS62136RGXR
U20: NCP349; 6-DFN; Manufacturer Part Number NCP349MNAETBG
U112: NCP163ASN250T1G_NF; SOT23_NCP163ASN250T1G; Manufacturer Part Number NCP163ASN250T1G

Notes on the sheet:
+5V EXTERNAL POWER
+5V POWER SOURCE SELECTION
+3V POWER LED
+5V MCU POWER LED
+5V POWER LED
+7.5V POWER LED
+2.5V POWER LED
+5V OUTPUT
