myriadrf/LimeRFE/hardware/1v0/KiCAD/RX.sch

## KiCad design hardware/1v0/KiCAD/RX.sch (2020-02-29)

Schematic: RX.sch

Parts:
C15, C16, C19, C20: 1u_0402; SMD0402; Manufacturer Part Number GCM155C71A105KE38D
C17, C18, C21: 1000pF_0402; SMD0402; Manufacturer Part Number GRM1555C1H102FA01D
U10, U11, U12, U13, U34, U35, U36, U37, U46, U47, U48, U49: SN74LV1T04; Manufacturer Part Number SN74LV1T04DCKR
U14, U15: PE4245; Manufacturer Part Number 4245-52
U16, U19: MASW-008566-TR3000; Manufacturer Part Number MASW-008566-TR3000
U17, U20: SKY13575-639LF; Manufacturer Part Number SKY13575-639LF
U18: SN74LVC1G139; SN74LVC1G139DCTR; Manufacturer Part Number SN74LVC1G139DCTR

Notes on the sheet:
LNA H
SP4T
LNA L
SPDT
