myriadrf/LimeRFE/hardware/1v0/KiCAD/RX_H.sch

## KiCad design hardware/1v0/KiCAD/RX_H.sch (2020-02-29)

Schematic: RX_H.sch

Parts:
C156, C157: 1000pF_0402_GRM1555C1H102GA01D; SMD0402; Manufacturer Part Number GRM1555C1H102GA01D
C392: 100nF_0402_GRM155R71C104KA88J; SMD0402; Manufacturer Part Number GRM155R71C104KA88J
P99, P100, P104, P105, P106, P108: probe_v1
R182, R185: 10K_0402_Yageo; SMD0402; Manufacturer Part Number RC0402JR-7D10KL
U67: SKY13415-485LF; 14QFN_SKY13415-485LF; Manufacturer Part Number SKY13415-485LF
U68: 74LV164D,118; Manufacturer Part Number 74LV164D,118
U69: 74LVC1G08GW; 74LVC1G08GW_TSSOP-5; Manufacturer Part Number 74LVC1G08GW,125

Notes on the sheet:
LNA H
SP4T
