myriadrf/LimeRFE/hardware/1v0/KiCAD/RX_L.sch

## KiCad design hardware/1v0/KiCAD/RX_L.sch (2020-02-29)

Schematic: RX_L.sch

Parts:
C118, C119, C141, C142, C143, C144: 1uF_0402_GCM155C71A105KE38D; SMD0402; Manufacturer Part Number GCM155C71A105KE38D
C390, C391: 100nF_0402_GRM155R71C104KA88J; SMD0402; Manufacturer Part Number GRM155R71C104KA88J
P79, P88, P90, P94, P95, P96: probe_v1
R130: 0R_0402_Yageo; SMD0402; Manufacturer Part Number RC0402JR-070RL
R175, R178: 10K_0402_Yageo; SMD0402; Manufacturer Part Number RC0402JR-7D10KL
U38, U93, U134, U135: HMC544AE; Manufacturer Part Number HMC544AE
U58, U59: MASW-008566-TR3000; Manufacturer Part Number MASW-008566-TR3000
U60, U62: 74LV164D,118; Manufacturer Part Number 74LV164D,118
U61, U63: PE4245; Manufacturer Part Number 4245-52
U64: 74LVC1G08GW; 74LVC1G08GW_TSSOP-5; Manufacturer Part Number 74LVC1G08GW,125
U137: TC74HC04AF; Manufacturer Part Number TC74HC04AF

Notes on the sheet:
LNA L
SP4T
SPDT
CTRL?
