myriadrf/LimeRFE/hardware/1v0/KiCAD/SWR_Meter_Subsystem.sch

## KiCad design hardware/1v0/KiCAD/SWR_Meter_Subsystem.sch (2020-02-29)

Schematic: SWR_Meter_Subsystem.sch

Parts:
C52, C53, C54, C55, C56, C57, C71, C72: NF_0603; SMD0603
C58, C60, C358: 1uF_0402_GCM155C71A105KE38D; SMD0402; Manufacturer Part Number GCM155C71A105KE38D
C59, C61, C62, C63, C64, C65, C66: 47nF_0402_GCM155R71H473KE02D; SMD0402; Manufacturer Part Number GCM155R71H473KE02D
C67, C68: 1nF_0603_Murata; SMD0603; Manufacturer Part Number GRM1885C1H102JA01J
C69: 10uF_0603_GRM188R61E106KA73J; SMD0603; Manufacturer Part Number GRM188R61E106KA73J
C70: 0.1uF_0402_Murata; SMD0402; Manufacturer Part Number GCM155R71C104KA55D
IC1, IC2: ADL5513; Manufacturer Part Number ADL5513ACPZ-R7
J17, J18: SMA_H_v3; SMA_v2; Manufacturer Part Number CON-SMA-EDGE-S
R62, R63, R64, R66: 120R_0805_Panasonic; SMD0805; Manufacturer Part Number ERJ-P06J121V
R65, R71: 294R_0603_Yageo; SMD0603; Manufacturer Part Number AC0603FR-07294RL
R67, R69: 249R_0603_CRCW0603249RFKEAHP; SMD0603; Manufacturer Part Number CRCW0603249RFKEAHP
R68: 17R8_0603_Vishay; SMD0603; Manufacturer Part Number RC0603FR-0717R8L
R70, R72: 60R4_0603_Yageo; SMD0603; Manufacturer Part Number RC0603FR-0760R4L
R73, R74, R75, R86, R87: 0R_0603_RCS06030000Z0EA; SMD0603; Manufacturer Part Number RCS06030000Z0EA
R76, R77: 52R3_0603_Yageo; SMD0603; Manufacturer Part Number RC0603FR-0752R3L
R78: 11k5_0603_Yageo; SMD0603; Manufacturer Part Number RT0603DRE0711K5L
R79: 2k32_0603_Yageo; SMD0603; Manufacturer Part Number RT0603DRD072K32L
R80, R83, R84, R85: 20K_0603_ESR03EZPJ203; SMD0603; Manufacturer Part Number ESR03EZPJ203
R81, R82: 10K_0603_ESR03EZPJ103; SMD0603; Manufacturer Part Number ESR03EZPJ103
U29, U30: HMC544AE; Manufacturer Part Number HMC544A
U31: NCP331SNT1G; TSOP-6; Manufacturer Part Number NCP331SNT1G
U32: LMC660CMX/NOPB; M14A; Manufacturer Part Number LMC660CMX/NOPB
U114, U125: SN74LV1T04; Manufacturer Part Number SN74LV1T04DCKRG4

Notes on the sheet:
Pin max = 1W
20 dB Attenuator
FWD
REF
3 dB Attenuator
CPL
