myriadrf/LimeRFE/hardware/1v0/KiCAD/TOP_CTRL.sch

## KiCad design hardware/1v0/KiCAD/TOP_CTRL.sch (2020-02-29)

Schematic: TOP_CTRL.sch

Parts:
C398, C399: 100nF_0402_GRM155R71C104KA88J; SMD0402; Manufacturer Part Number GRM155R71C104KA88J
U115: TC74HC04AF; Manufacturer Part Number TC74HC04AF
U116, U117: 74LV164D,118; Manufacturer Part Number 74LV164D,118
