myriadrf/LimeRFE/hardware/1v0/KiCAD/TX_H.sch

## KiCad design hardware/1v0/KiCAD/TX_H.sch (2020-02-29)

Schematic: TX_H.sch

Parts:
C111, C163, C394, C395, C396: 100nF_0402_GRM155R71C104KA88J; SMD0402; Manufacturer Part Number GRM155R71C104KA88J
C113, C245: 100pF_0402_GCM1555C1H101JA16D; SMD0402; Manufacturer Part Number GCM1555C1H101JA16D
C376, C377, C378: 1500pF_0603_GRM1885C1H152JA01D; SMD0603; Manufacturer Part Number GRM1885C1H152JA01D
P2, P5, P6, P7, P8, P9, P14, P15, P17, P18, P24, P27, P28, P30, P31, P32, P33, P34, P35, P45, P109, P110, P112: probe_v1
R129, R159, R160, R164, R169, R174, R195, R196, R197, R198, R199: 5K1_0402; SMD0402; Manufacturer Part Number RC0402FR-075K1L
R140, R168: 10K_0402_Yageo; SMD0402; Manufacturer Part Number RC0402JR-7D10KL
R148, R149: NF_0R_0402_RCS04020000Z0ED; SMD0402; Manufacturer Part Number RCS04020000Z0ED
R204, R205: 32.4R_0805_Vishay; SMD0805; Manufacturer Part Number CRCW080532R4FKEAHP
U75, U89, U92: 74LV164D,118; Manufacturer Part Number 74LV164D,118
U77, U78: SN74LVCH8T245PWR; Manufacturer Part Number SN74LVCH8T245PWR
U91: MASW-008566-TR3000; Manufacturer Part Number MASW-008566-TR3000
U94: SKY13418-485LF; 14QFN_SKY13418-485LF; Manufacturer Part Number SKY13418-485LF
U140: SKY13415-485LF; 14QFN_SKY13415-485LF; Manufacturer Part Number SKY13415-485LF
U141, U142: SN74LV1T04; Manufacturer Part Number SN74LV1T04DCKRG4
U143: HMC544AE; Manufacturer Part Number HMC544AE

Notes on the sheet:
1000-4000MHz
PA_145MHz
PA_2.4GHz
PA_4.0GHz
PA_3.5GHz
PA_1.28GHz
PA_1.0GHz
PA_435MHz
145MHz
2400MHz
1-4GHz
3500MHz
1-1000MHz
1280MHz
435MHz
PDRIV_1000MHz
PREDRIVER_H
PDRIV_435MHz
PDRIV_145MHz
SP4T
PA_30,70MHz
PDRIV_30, 70MHz
30,70MHz
PA_220MHz
PA_920MHz
PDRIV_1.28GHz
PDRIV_920MHz
PDRIV_220MHz
220MHz
BRANKO, PROVERI DA LI SVAKI SIGNAL IMA KONTROLU IZ SHIFTERA
