myriadrf/LimeRFE/hardware/1v0/KiCAD/USB.sch

## KiCad design hardware/1v0/KiCAD/USB.sch (2020-02-29)

Schematic: USB.sch

Parts:
C27, C28: 100nF_0402_GRM155R71C104KA88J; SMD0402; Manufacturer Part Number GRM155R71C104KA88J
C29: 10uF_0603_GRM188R61E106KA73J; SMD0603; Manufacturer Part Number GRM188R61E106KA73J
C30: 1uF_0402_CC0402ZRY5V5BB105; SMD0402; Manufacturer Part Number CC0402ZRY5V5BB105
C31: 3.9nF_0402_04025C392JAT2A; SMD0402; Manufacturer Part Number 04025C392JAT2A
CON1: 47346-0001; USB-MINI-B; Manufacturer Part Number 47346-0001
FB3: FB_600R_0805_MPZ2012S601AT000; SMD0805; Manufacturer Part Number MPZ2012S601AT000
R39, R40: 22R_0402_RC0402JR-0722RL; SMD0402; Manufacturer Part Number RC0402JR-0722RL
R41: 1M_0402_RC0402FR-071ML; SMD0402; Manufacturer Part Number RC0402FR-071ML
U22: NUP2202W1T2G; SC-88-6_NUP2202W1T2G; Manufacturer Part Number NUP2202W1T2G
