myriadrf/LimeRFE/hardware/1v31/KiCAD/LIMITER_CELL.sch

## KiCad design hardware/1v31/KiCAD/LIMITER_CELL.sch (2021-06-08)

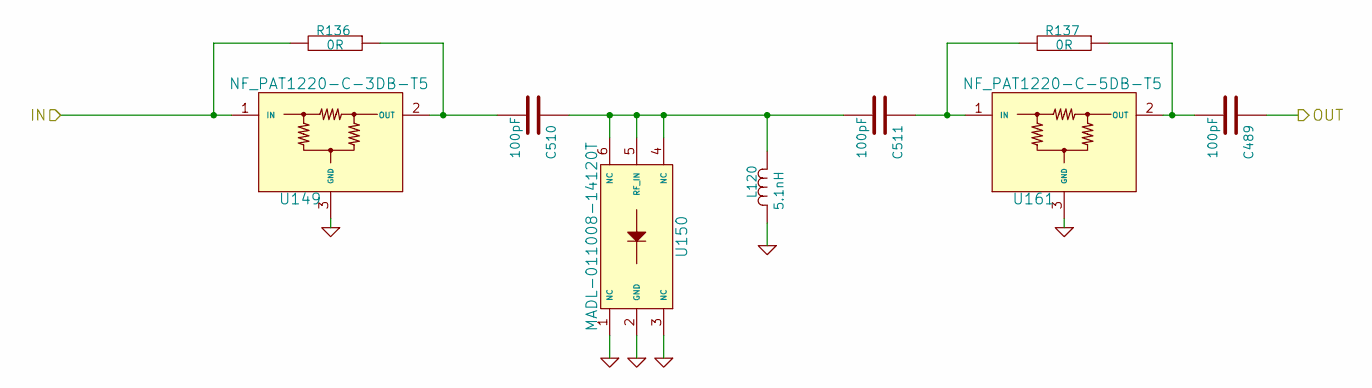
[picture p441: schematic LIMITER_CELL.sch]

Parts:
C489, C510, C511: 100pF_0402_GCM1555C1H101JA16D; SMD0402; Manufacturer Part Number GCM1555C1H101JA16D
L120: 5.1nH_0402_LQW15AN25NJ80D; SMD0603; Manufacturer Part Number LQW15AN5N1D1ZD
R136, R137: 0R_0402_RCS04020000Z0ED; SMD0402; Manufacturer Part Number RCS04020000Z0ED
U149: NF_PAT1220-C-3DB-T5; PAT1220-C-3DB-T5; Manufacturer Part Number PAT1220-C-3DB-T5
U150: MADL-011008-14120T; Manufacturer Part Number MADL-011008-14120T
U161: NF_PAT1220-C-5DB-T5; PAT1220-C-5DB-T5; Manufacturer Part Number PAT1220-C-5DB-T5

Connections:
GND: L120.2, U149.3 (GND), U150.1 (NC), U150.2 (GND), U150.3 (NC), U161.3 (GND)
IN: R136.2, U149.1 (IN)
unnamed: C489.2, R137.1, U161.2 (OUT)
unnamed: C510.1, C511.2, L120.1, U150.4 (NC), U150.5 (RF_IN), U150.6 (NC)
unnamed: C510.2, R136.1, U149.2 (OUT)
unnamed: C511.1, R137.2, U161.1 (IN)
OUT: C489.1
