myriadrf/LimeRFE/firmware/HW_1v31/LimeRFE_nano/mcu.cpp

#include "Arduino.h"
#include <Wire.h>
#include "consts.h"
#include "mcu.h"

void setupMCU(unsigned char value, unsigned char * currentState){
  
  if(bitRead(value, 0) == 1){
    enablePAs();
  } else {
    disablePAs();
  }
  
  if(bitRead(value, 1) == 1){
    enableLNAs();
  } else {
    disableLNAs();
  }

  setRXTX(value);
  
  setRelay(value);

  setBand38(value);

  memcpy(currentState + CHAIN_SIZE, &value, sizeof(value));
  
}

void enableLNAs(){
  digitalWrite(LNA_EN_PIN, HIGH); // LNAs enable
}

void disableLNAs(){
  digitalWrite(LNA_EN_PIN, LOW); // LNAs disable
}

void enablePAs(){
  digitalWrite(PA_ENn_PIN, LOW); // PAs enable (Active Low)
}

void disablePAs(){
  digitalWrite(PA_ENn_PIN, HIGH); // PAs disable (Active Low)
}

void band38TX(){
  digitalWrite(BAND38_TX_ENn_PIN, LOW);
}

void band38RX(){
  digitalWrite(BAND38_TX_ENn_PIN, HIGH);
}

void setRelay(unsigned char value){
  digitalWrite(RELAY_PIN, bitRead(value, MCU_BYTE_RELAY_BIT));
}

void setRXTX(unsigned char value){
  digitalWrite(RX_SW_PIN0, bitRead(value, MCU_BYTE_TXRX0_BIT));
  digitalWrite(RX_SW_PIN1, bitRead(value, MCU_BYTE_TXRX1_BIT));
}

void setBand38(unsigned char value){
  if (bitRead(value, MCU_BYTE_BAND38_BIT) == 0){
    band38RX();
  } else {
    band38TX();
  }
}

// Read Atmega328P internal temperature sensor //
long read_temp()
{
  // Read temperature sensor against 1.1V reference
  ADMUX = _BV(REFS1) | _BV(REFS0) | _BV(MUX3);
  // Start AD conversion
  ADCSRA |= _BV(ADEN) | _BV(ADSC);
  // Detect end-of-conversion
  while (bit_is_set(ADCSRA,ADSC));
  // return raw data
  return ADCL | (ADCH << 8);
}

// Convert raw temperature data to °C
double conv_temp(long raw_temp)
{
  // f(x) = (raw - offset) / coeff
  return((raw_temp - 324.31) / 1.22);
}

// Read GPIO 1 or 0 //
char getGPIO10( char pin) {
  if (pin == 0){
    if (digitalRead(GPIO0_PIN) == HIGH){
      return(0x01);
    } else {
      return(0x00);
    }
  } else if (pin == 1){
    if (digitalRead(GPIO1_PIN) == HIGH){
      return(0x01);
    } else {
      return(0x00);
    }
  } else {
    return(0xff);
  }
}

// Set GPIO 1 or 0 //
void setGPIO10( char pin, char value) {
  if (pin == 0){
    if (value == 0){
      digitalWrite(GPIO0_PIN, LOW);
    } else {
      digitalWrite(GPIO0_PIN, HIGH);
    }
  } else if (pin == 1){
    if (value == 0){
      digitalWrite(GPIO1_PIN, LOW);
    } else {
      digitalWrite(GPIO1_PIN, HIGH);
    }
  }
}

// Set GPIO 1 or 0 direction (1 - in, 0 - out)//
void configGPIO10( char pin, char dir) {
  if (pin == 0){
    if (dir == 0){
      pinMode(GPIO0_PIN, OUTPUT);
    } else {
      pinMode(GPIO0_PIN, INPUT);
    }
  } else if (pin == 1){
    if (dir == 0){
      pinMode(GPIO1_PIN, OUTPUT);
    } else {
      pinMode(GPIO1_PIN, INPUT);
    }
  }
}
