myriadrf/LimeRFE/firmware/HW_1v0/LimeRFE_nano/consts.h

#define CHAIN_SIZE              11  // chain bytes
#define STATE_SIZE              12  // board state bytes (chain bytes + MCU STATE byte)
#define BUFFER_SIZE             16  // communication buffer size 16 bytes
#define BUFFER_SIZE_MODE        2   // communication buffer size 2 bytes for CMD_MODE
#define CONN_DEFAULT            0
#define CONN_TXRX               1
#define CONN_TX                 2
#define CONN_30                 3
