myriadrf/LimeRFE/firmware/HW_1v0/LimeRFE_nano/errorCode.h

#define COMPLETED                         0
#define ERROR_TX_CONN                     1
#define ERROR_RX_CONN                     2
#define ERROR_RXTX_SAME_CONN              3
#define ERROR_CELL_WRONG_MODE             4
#define ERROR_CELL_TX_NOT_EQUAL_RX        5
#define ERROR_WRONG_CHANNEL_CODE          6
